DigicoolThings/MECB/MECB_WDC_W65C02S_PLCC_CPU/CreatiVision/CreatiVision_MECB_ROM_Expansion.pdf

## CreatiVision re-Creation - 16 Cartridge Selection

### for MECB ROM Expansion (ROM0 + ROM1)

v1.0 by DigicoolThings

Switch Settings: 1=On, 0=Off (Positions 1234 = A19, A18, A17, A16)

ROM | Program | Switch Setting 1234 | Switch Setting Rotary
ROM0 | Air/Sea Battle | 1111 | 0
| Astro Pinball | 1110 | 1
| Auto Chase | 1101 | 2
| BASIC 1983 | 1100 | 3
| Chopper Rescue | 1011 | 4
| Crazy Chicky | 1010 | 5
| Deep Sea Adventure | 1001 | 6
| Locomotive | 1000 | 7
ROM1 | Mouse Puzzle | 0111 | 8
| Planet Defender | 0110 | 9
| Police Jump | 0101 | A
| Soccer | 0100 | B
| Sonic Invader | 0011 | C
| Stone Age | 0010 | D
| Tank Attack | 0001 | E
| Tennis Wimbledon | 0000 | F
