DigicoolThings/MECB/MECB_6802_CPU/MECB_6802_CPU_PCB_3D.png

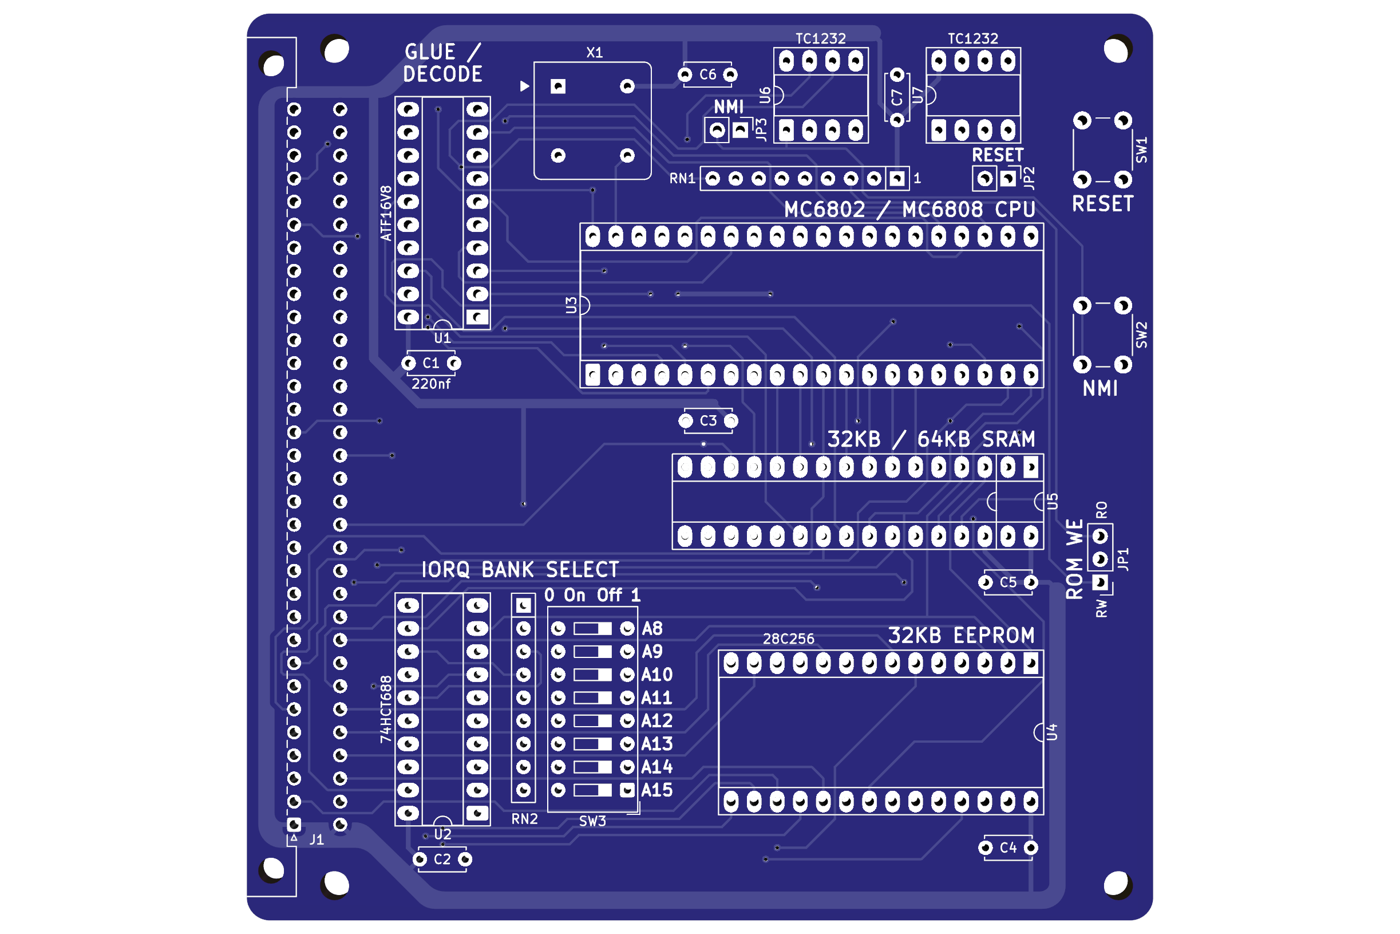
MECB_6802_CPU/MECB_6802_CPU_PCB_3D.png
