DigicoolThings/MECB/MECB_6809_CPU/MECB_6809_CPU_IORQ_48K_v2.5.jpg

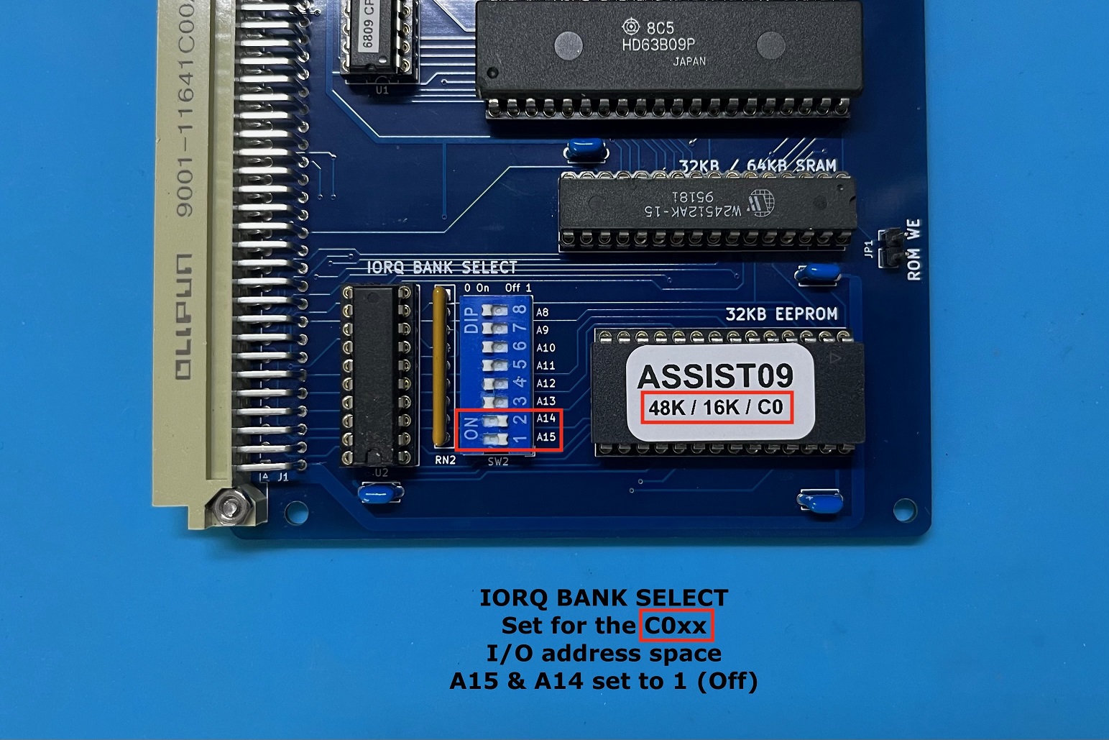
MECB_6809_CPU/MECB_6809_CPU_IORQ_48K_v2.5.jpg
