DigicoolThings/MECB/MECB_68008_CPU/MECB_68008_CPU_PCB_3D.png

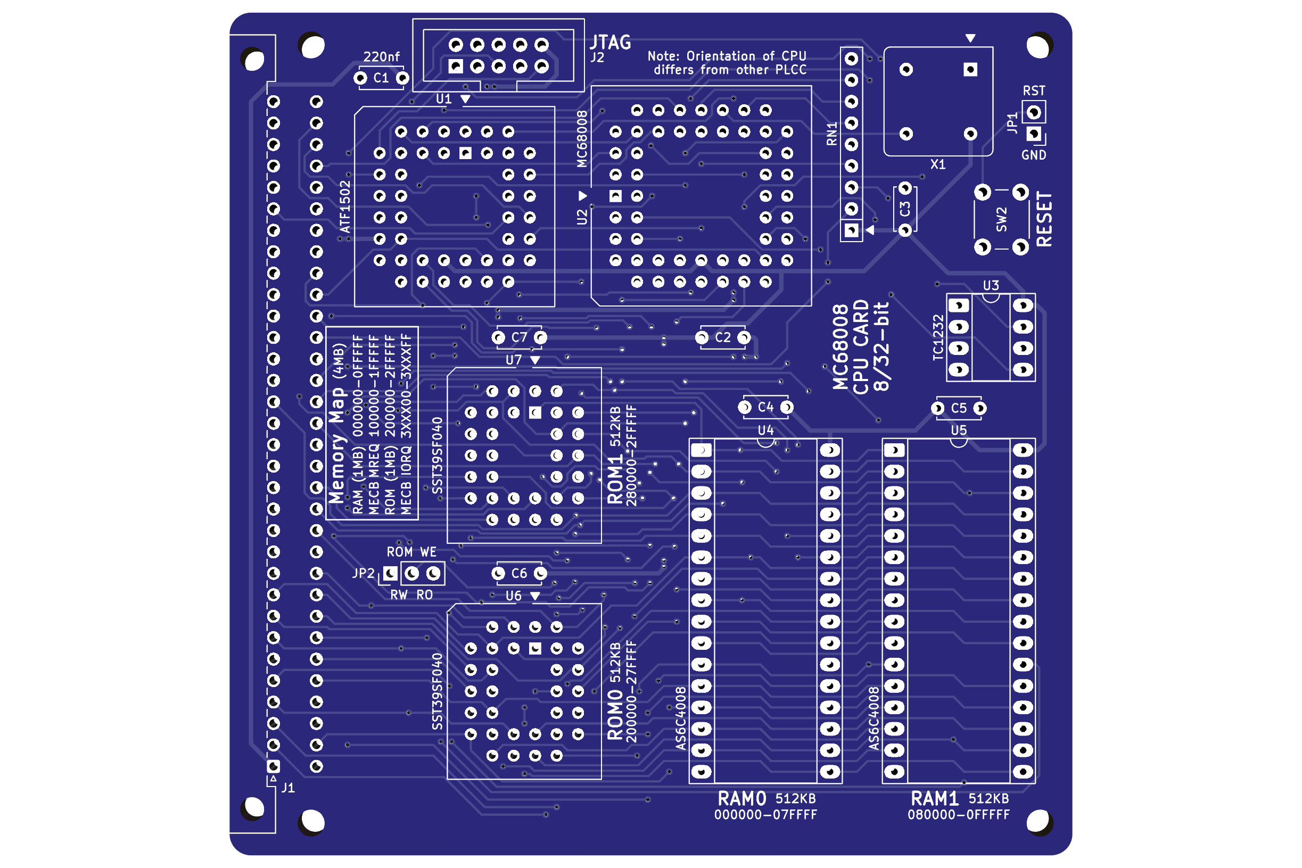
MECB_68008_CPU/MECB_68008_CPU_PCB_3D.png
