DigicoolThings/MECB/MECB_BackPlane_Extension/MECB_Backplane_Extension_PCB.png

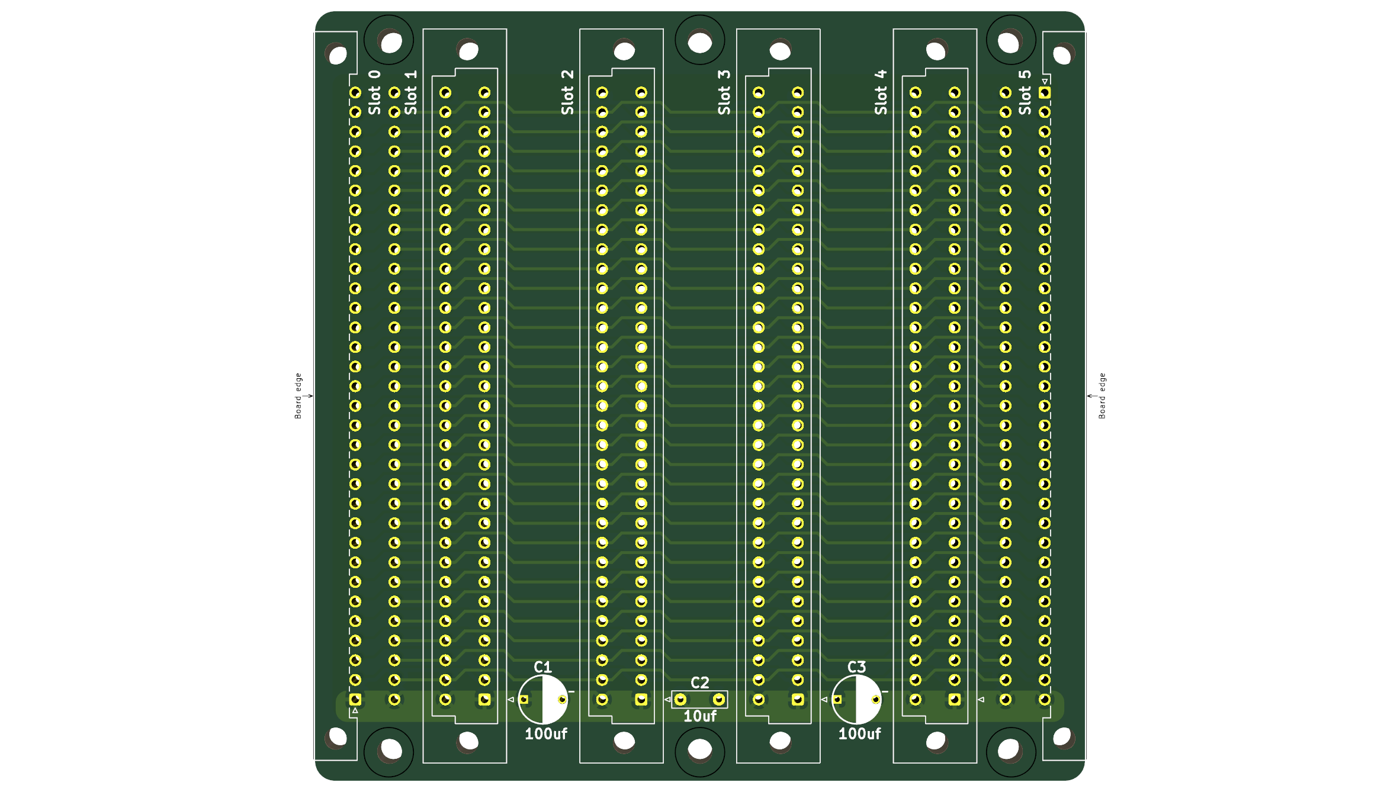
MECB_BackPlane_Extension/MECB_Backplane_Extension_PCB.png
