DigicoolThings/MECB/MECB_Grid/MECB_Grid_PCB_3D.png

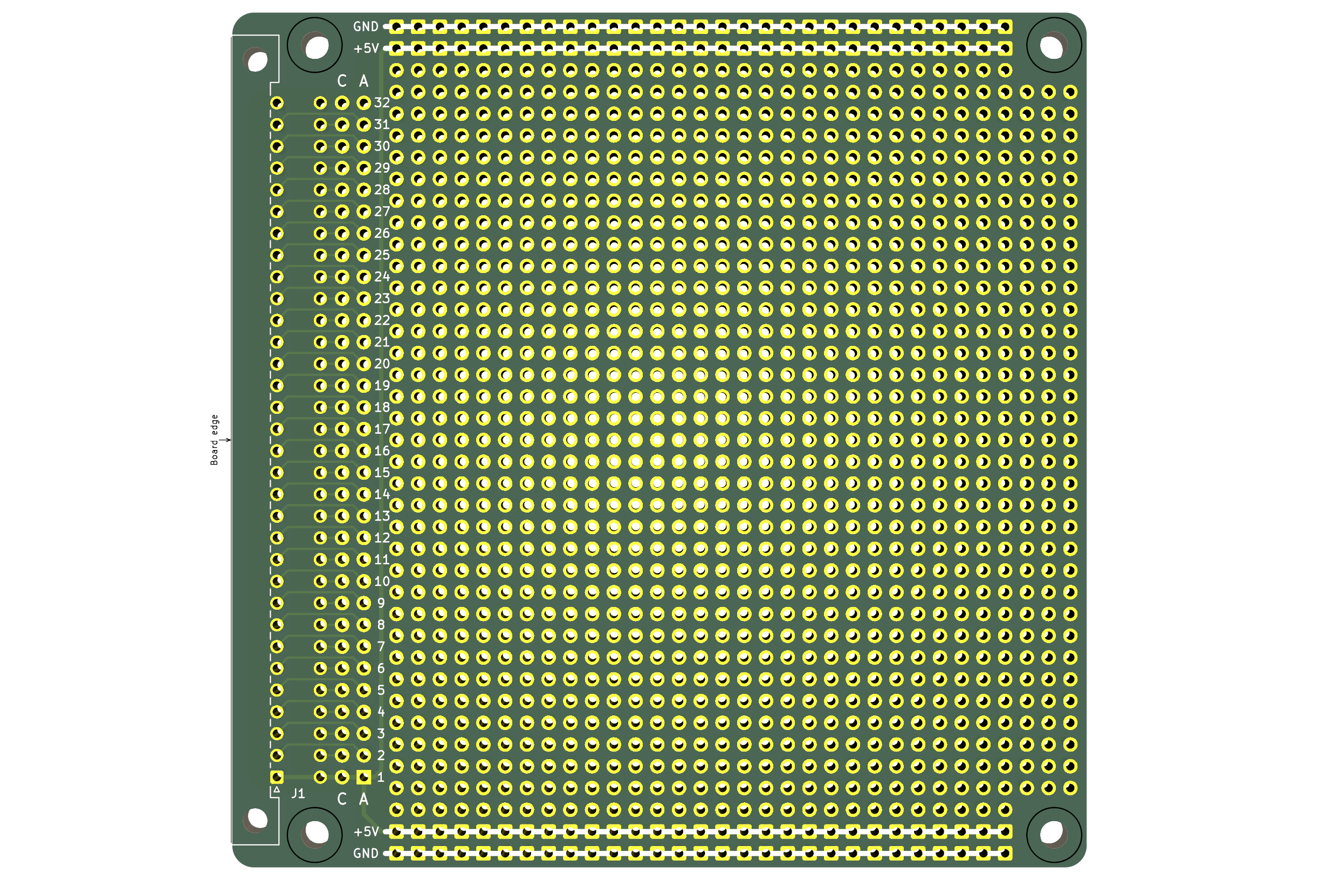
MECB_Grid/MECB_Grid_PCB_3D.png
