DigicoolThings/MECB/MECB_Grid/MECB_Pinout_Handout.png

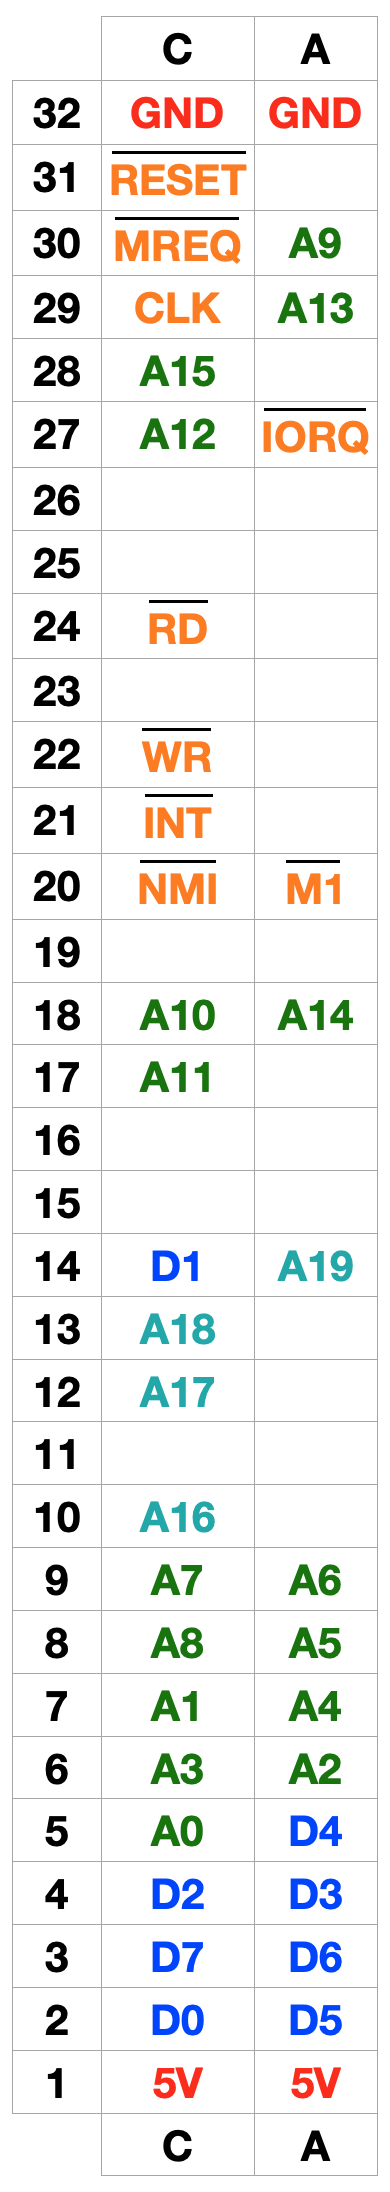
MECB_Grid/MECB_Pinout_Handout.png
