DigicoolThings/MECB/MECB_Motorola_IO/MECB_Motorola_IO_PCB_3D.png

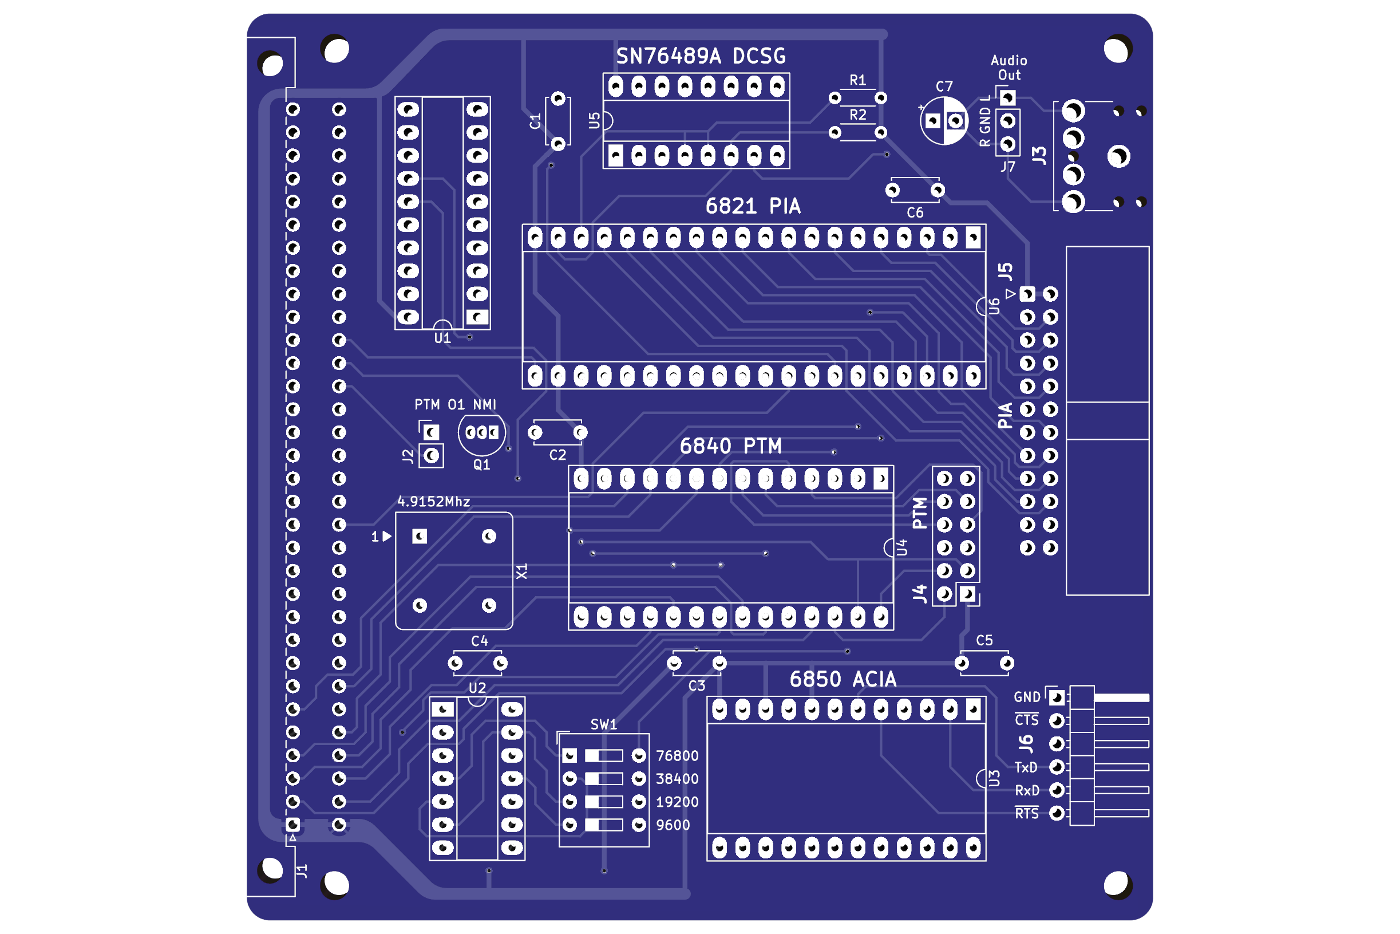
MECB_Motorola_IO/MECB_Motorola_IO_PCB_3D.png
