DigicoolThings/MECB/MECB_OLED_Display_128x64/MECB_OLED_Display_128x64_PCB_3D.png

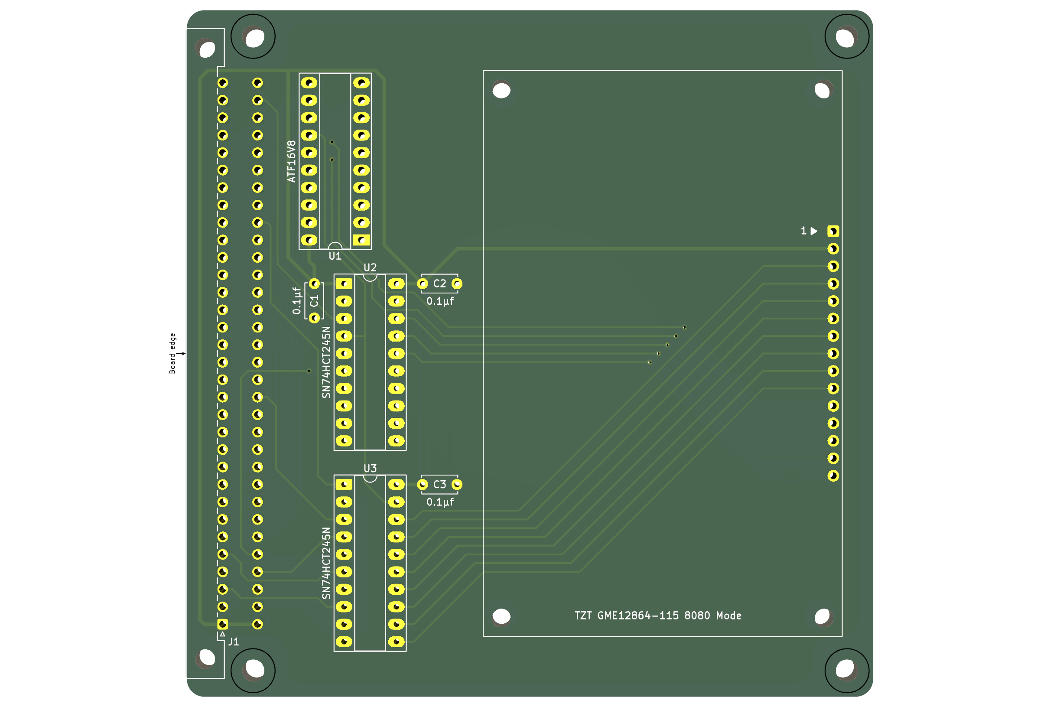
MECB_OLED_Display_128x64/MECB_OLED_Display_128x64_PCB_3D.png
