DigicoolThings/MECB/MECB_PICO9918_VDP/MECB_PICO9918_VDP_PCB_3D.png

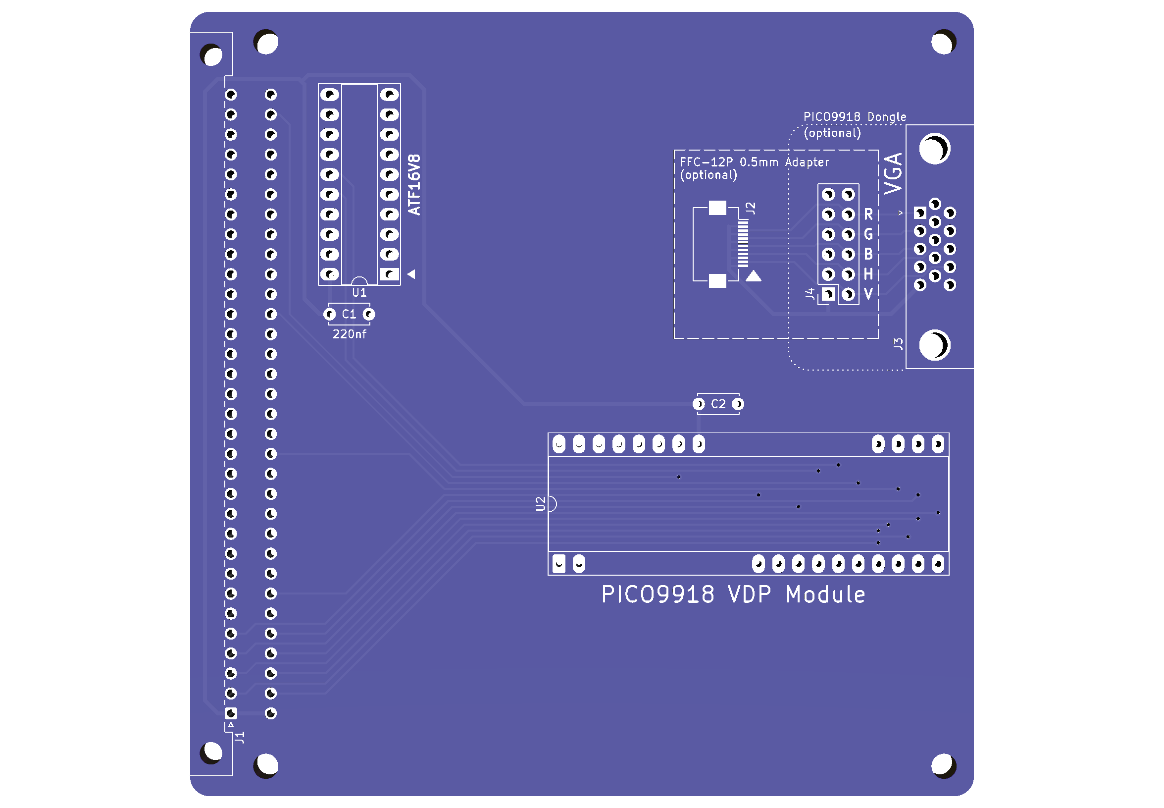
MECB_PICO9918_VDP/MECB_PICO9918_VDP_PCB_3D.png
