DigicoolThings/MECB/MECB_Template_16V8/meta/brd.png

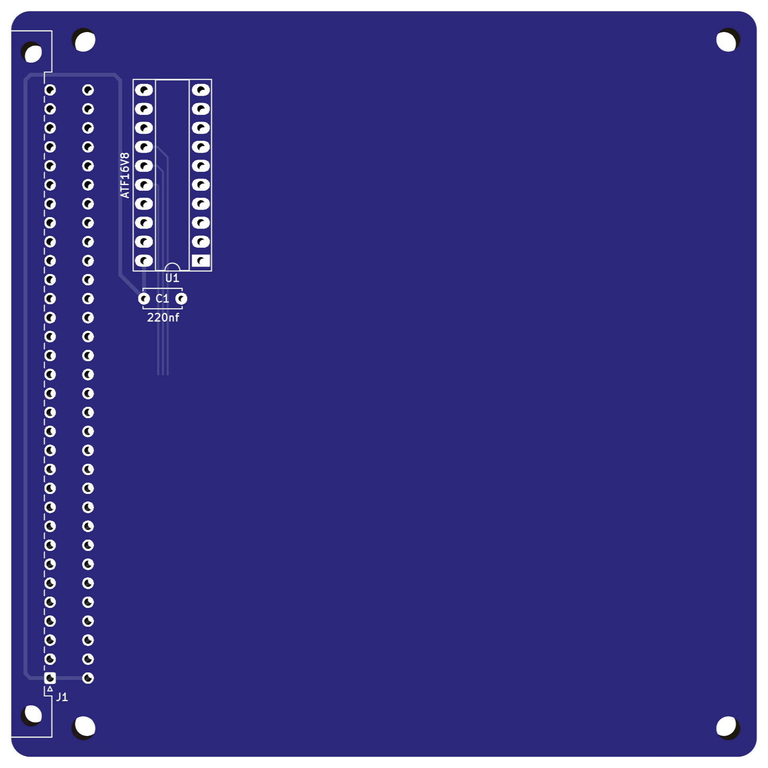
MECB_Template_16V8/meta/brd.png
