DigicoolThings/MECB/MECB_V9938_or_V9958_VDP/MECB_V9938_or_V9958_VDP_PCB_v1.2.png

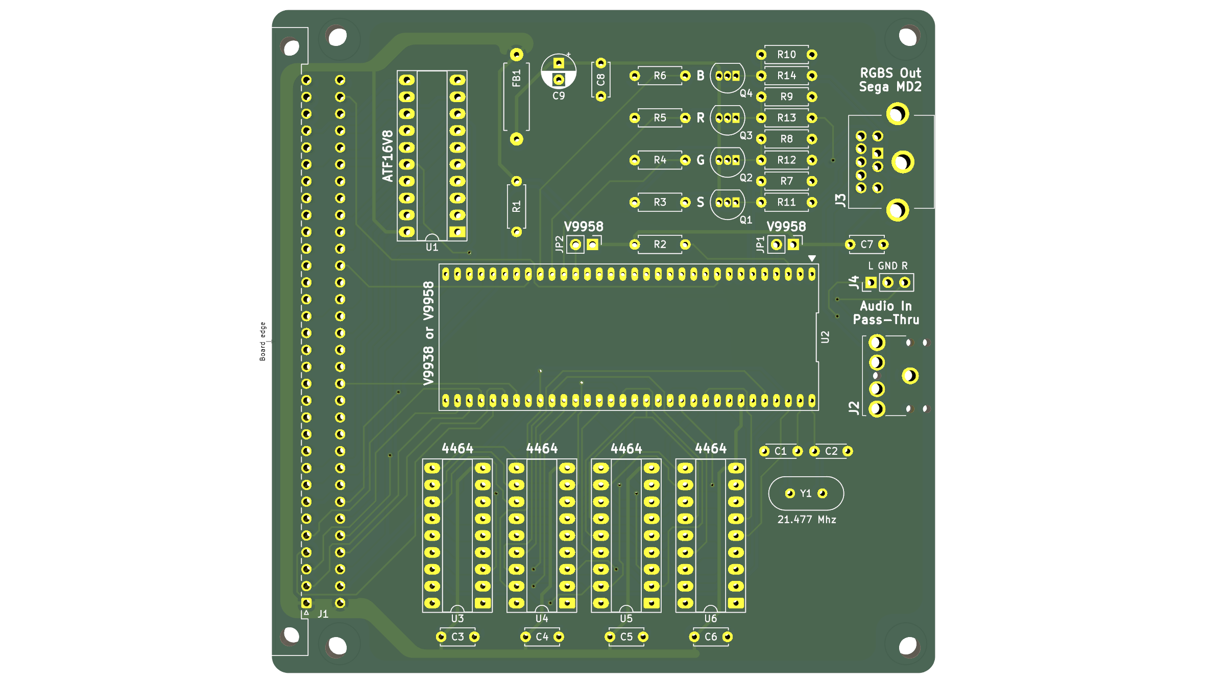
MECB_V9938_or_V9958_VDP/MECB_V9938_or_V9958_VDP_PCB_v1.2.png
