DigicoolThings/MECB/MECB_BackPlane_Extension/MECB_Backplane_Extension_BOM.pdf

Item | Qty | Source | Part Number
MECB Backplane Extension PCB | 1 | JLCPCB
DIN41612 Female 364 Connector | 4 | AliExpress | 364-STR-F
DIN41612 Female R/A 364 Connector | 1 | AliExpress | 364-RA-F
DIN41612 Male R/A 364 Connector | 1 | AliExpress | 364-RA-M
M2.5 Bolt 8mm | 8 | AliExpress
M2.5 Bolt 10mm | 4 | AliExpress
M2.5 Nut | 12 | AliExpress
12mm Nylon PCB Spacer | 6 | AliExpress
6mm Nylon Bolt | 12 | AliExpress
100uf Electrolytic | 2 | Mouser | 667-ECE-A1CKA101B
10uf Capacitor | 1 | Mouser | 810-FG24X7R1A106KRT6

MECB Backplane Extension - BOM

1
