DigicoolThings/MECB/MECB_6502_CPU/MECB_6502_CPU_BOM.pdf

Item | Qty | Source | Part Number
MECB 6502 CPU Card PCB | 1 | JLCPCB
DIN41612 Male R/A 364 Connector | 1 | AliExpress | 364-RA-M
M2.5 Bolt 10mm Thread Length | 2 | AliExpress
M2.5 Nut | 2 | AliExpress
12mm Nylon PCB Spacer | 4 | AliExpress
6mm Nylon Bolt | 8 | AliExpress
ATF16V8 PLD DIP20 (U1) | 1 | Mouser | ATF16V8B
28C256 32KB EEPROM DIP28 (U4) | 1 | Mouser | AT28C256
MOS 6502 or WDC W65C02S CPU DIP40 (U3) | 1 | AliExpress / Mouser
ECS-2100 Crystal Oscillator (e.g. 1 - 8Mhz) DIP8 (X1) | 1 | Mouser | ECS-2100AX-1.0MHZ
Resistor Network 4K7 SIP9 (RN1, RN2) | 2 | Mouser | 4609X-101-472LF
0.1µf Capacitor 5mm (C1,C2,C3,C4,C5,C6) | 6 | AliExpress
2 pin PCB Header | 4 | AliExpress
3 pin PCB Header | 1 | AliExpress
2 pin Jumper Cap | 2 | AliExpress
Tactile Switch 6mm | 2 | AliExpress
8-way DIP Switch DIP16 | 1 | AliExpress
74HCT688 DIP20 (U2) | 1 | Mouser | CD74HCT688E
W24512K 64KB SRAM SDIP32 (U5) | 1 | AliExpress
TC1232CPA DIP8 (U6,U7) | 2 | AliExpress | TC1232CPA
SDIP32 IC Socket (or 2x DIP16) (for U5) | 1 | AliExpress
DIP40 IC Socket (for U3) | 1 | AliExpress
DIP28 IC Socket (for U4) | 1 | AliExpress
DIP20 IC Socket (for U1,U2) | 2 | AliExpress
DIP8 IC Socket (for U6,U7,X1) | 3 | AliExpress

### MECB 6502 CPU - BOM

1
