DigicoolThings/MECB/MECB_Prototype/MECB_Prototype_BOM.pdf

Item | Qty | Source | Part Number
MECB Prototype Card PCB | 1 | JLCPCB
DIN41612 Male R/A 364 Connector | 1 | AliExpress | 364-RA-M
M2.5 Bolt 10mm Thread Length | 2 | AliExpress
M2.5 Nut | 2 | AliExpress
40 pin PCB Header | 2 | AliExpress
12mm Nylon PCB Spacer | 4 | AliExpress
6mm Nylon Bolt | 8 | AliExpress

MECB Prototype - BOM

1
