DigicoolThings/MECB/MECB_6802_CPU/MECB_6802_CPU_BOM.png

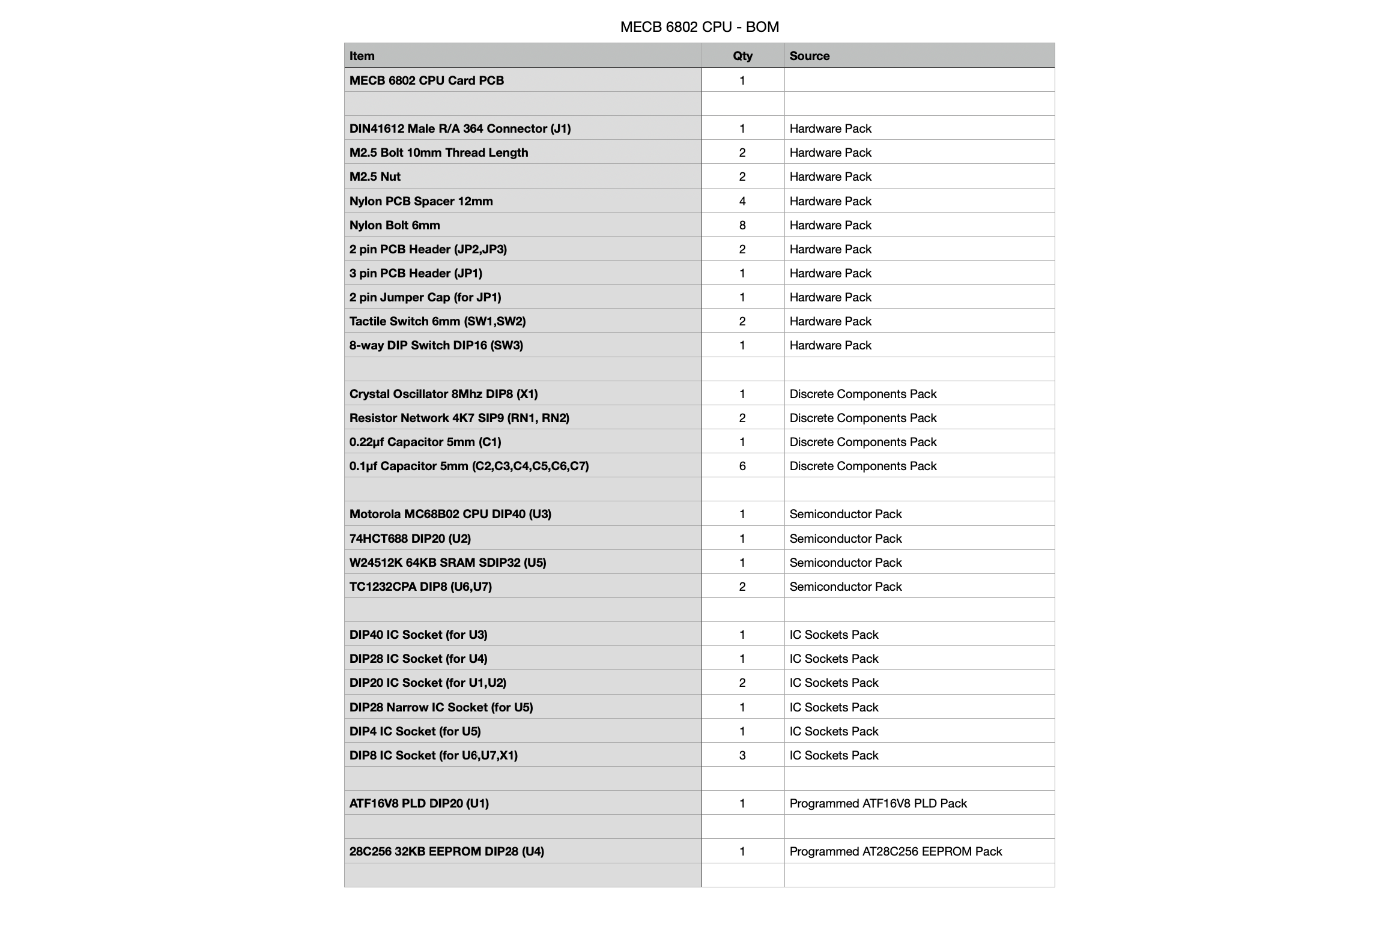
MECB_6802_CPU/MECB_6802_CPU_BOM.png
