DigicoolThings/MECB/MECB_68008_CPU/MECB_68008_CPU_BOM.png

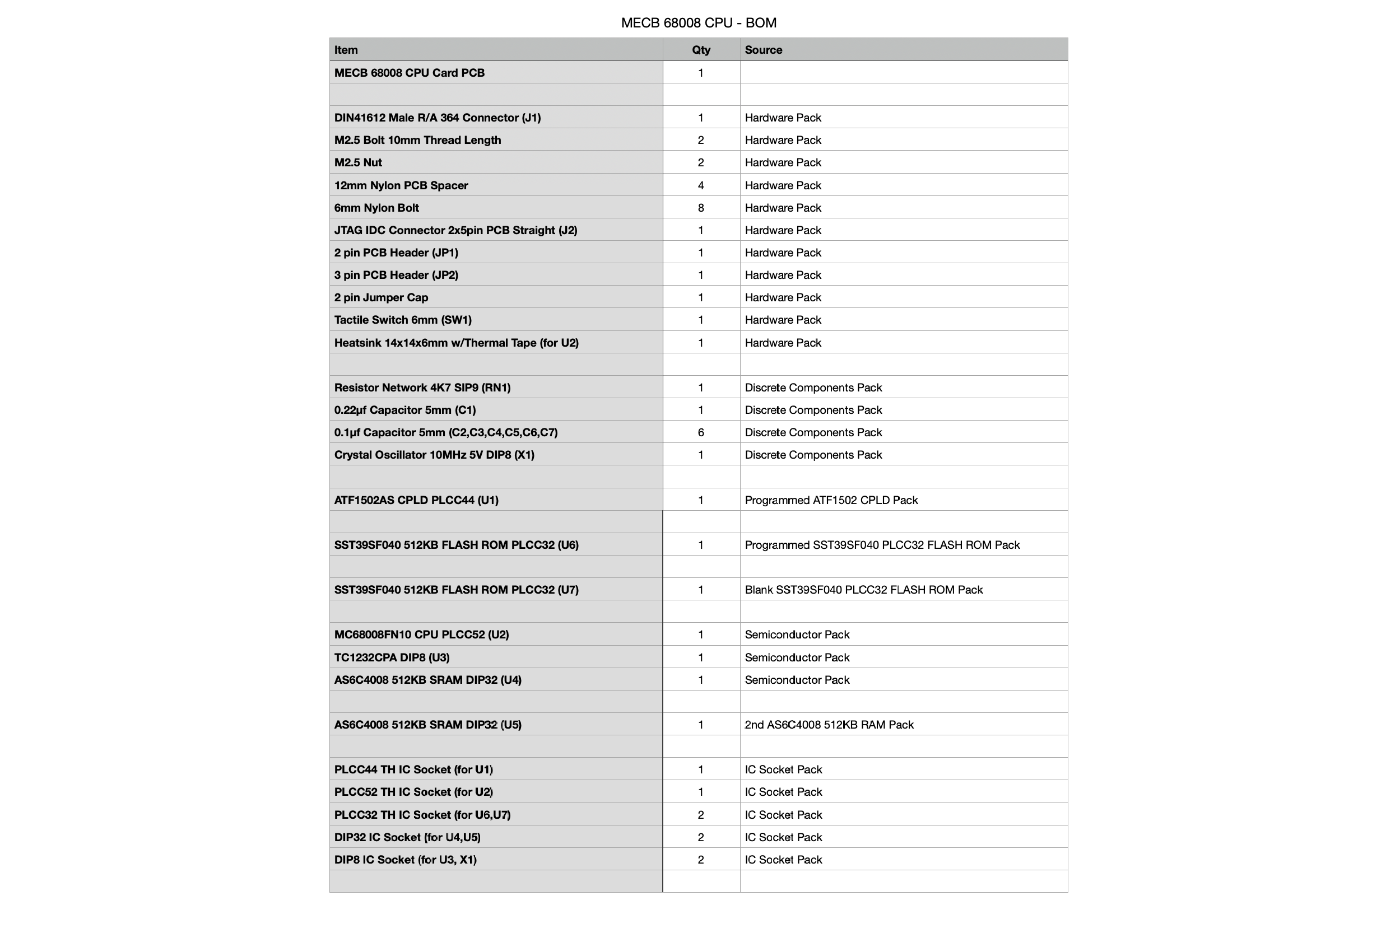
MECB_68008_CPU/MECB_68008_CPU_BOM.png
