DigicoolThings/MECB/MECB_Grid/MECB_Grid_BOM.png

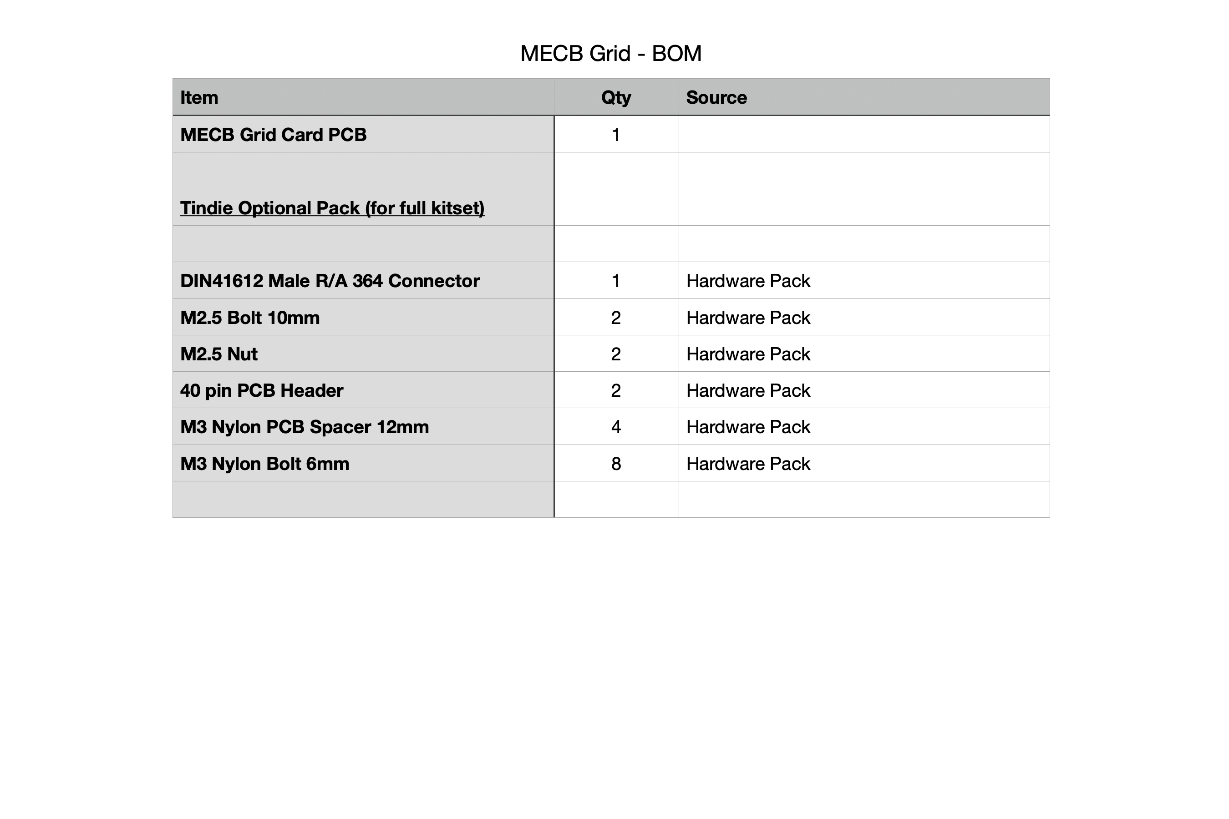
MECB_Grid/MECB_Grid_BOM.png
