DigicoolThings/MECB/MECB_Grid_16V8/MECB_Grid_16V8_BOM.png

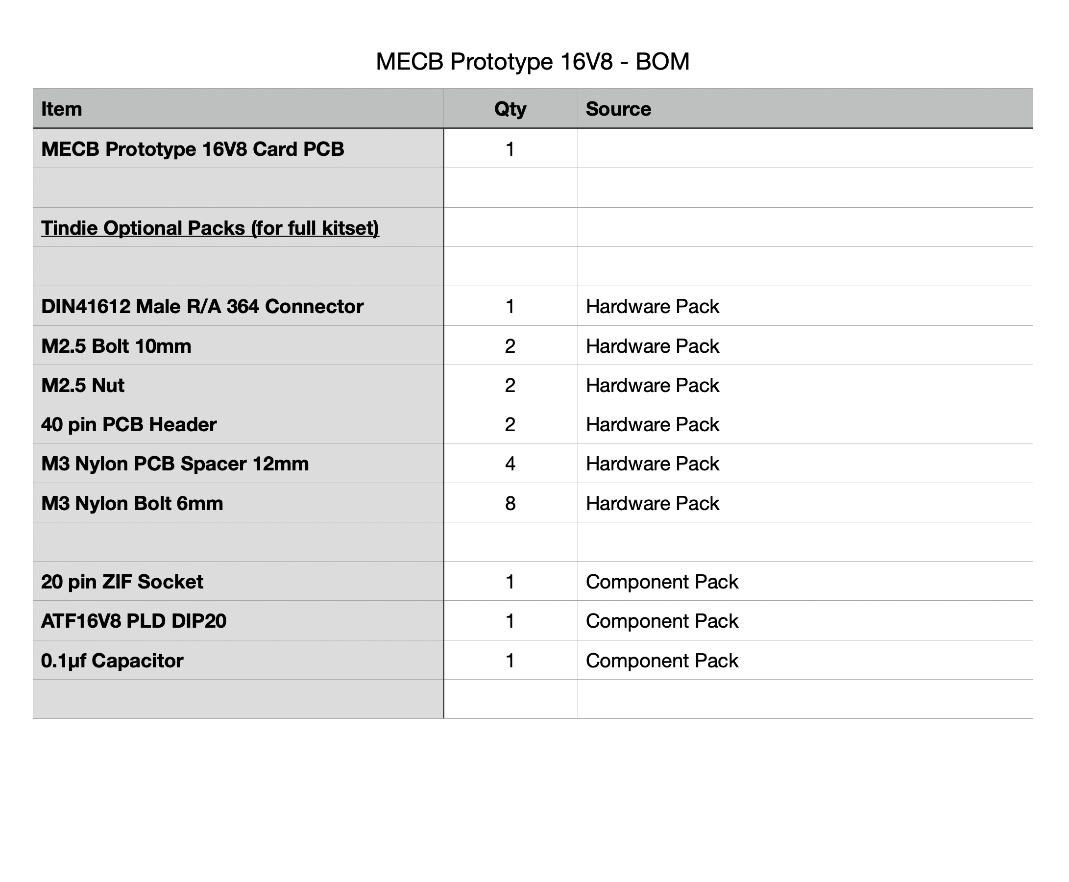
MECB_Grid_16V8/MECB_Grid_16V8_BOM.png
