DigicoolThings/MECB/MECB_Motorola_IO/MECB_Motorola_IO_BOM.png

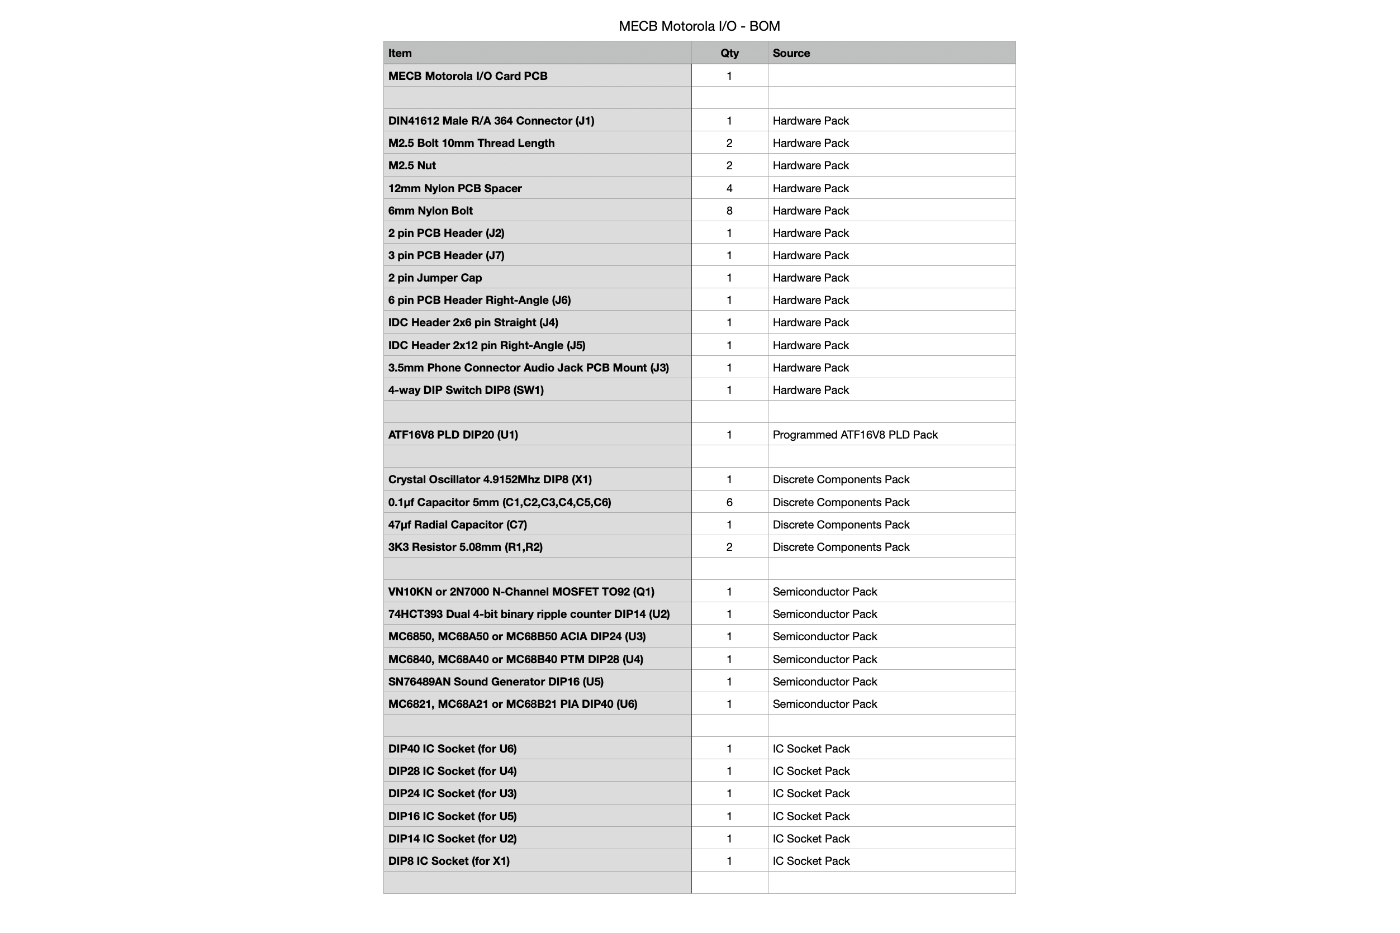
MECB_Motorola_IO/MECB_Motorola_IO_BOM.png
