DigicoolThings/MECB/MECB_OLED_Display_128x64/MECB_OLED_Display_128x64_BOM.png

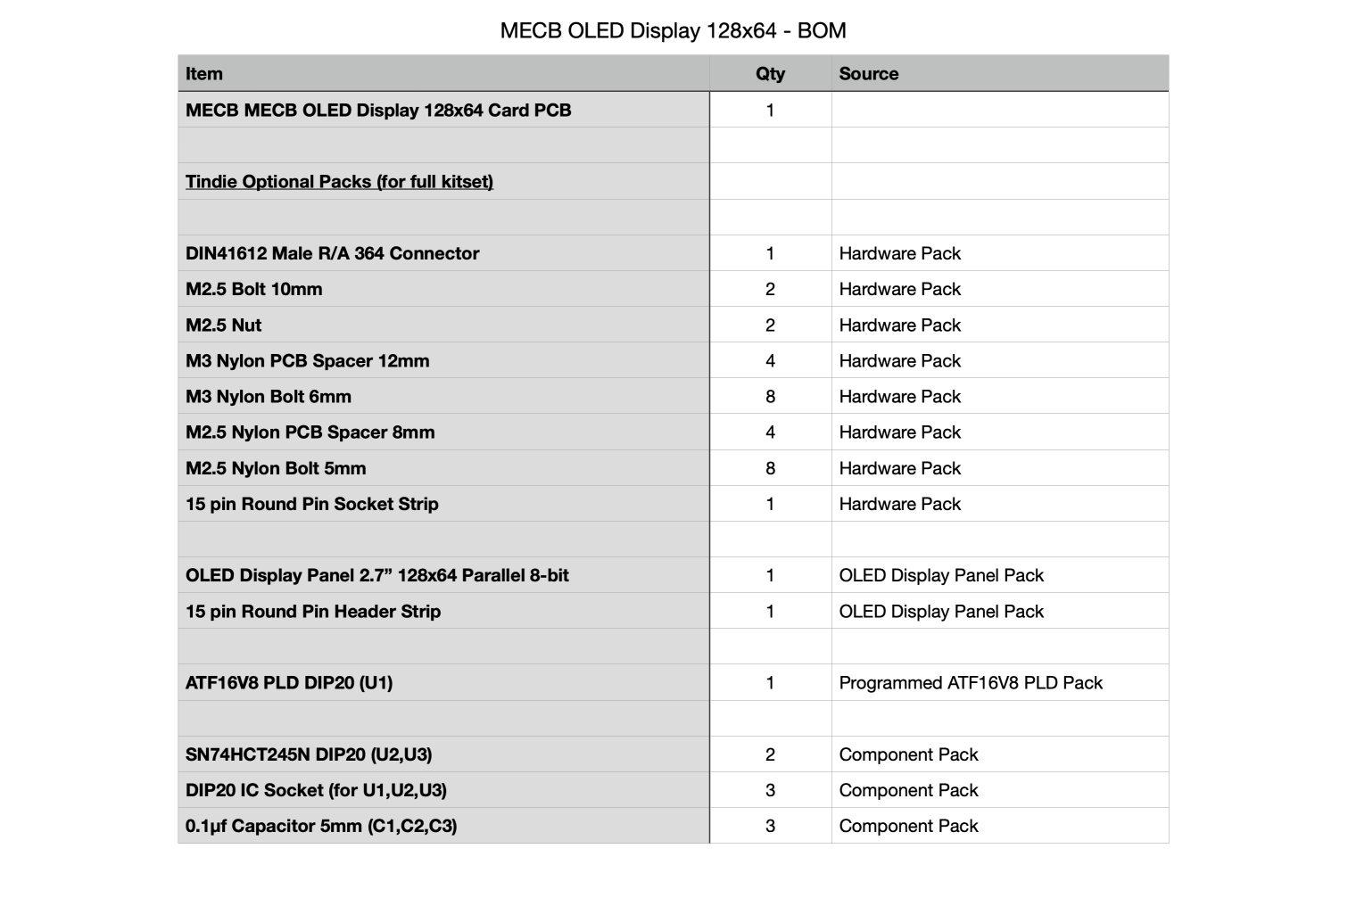
MECB_OLED_Display_128x64/MECB_OLED_Display_128x64_BOM.png
