DigicoolThings/MECB/MECB_Prototype_160mm/MECB_ProtoType_160mm_BOM.png

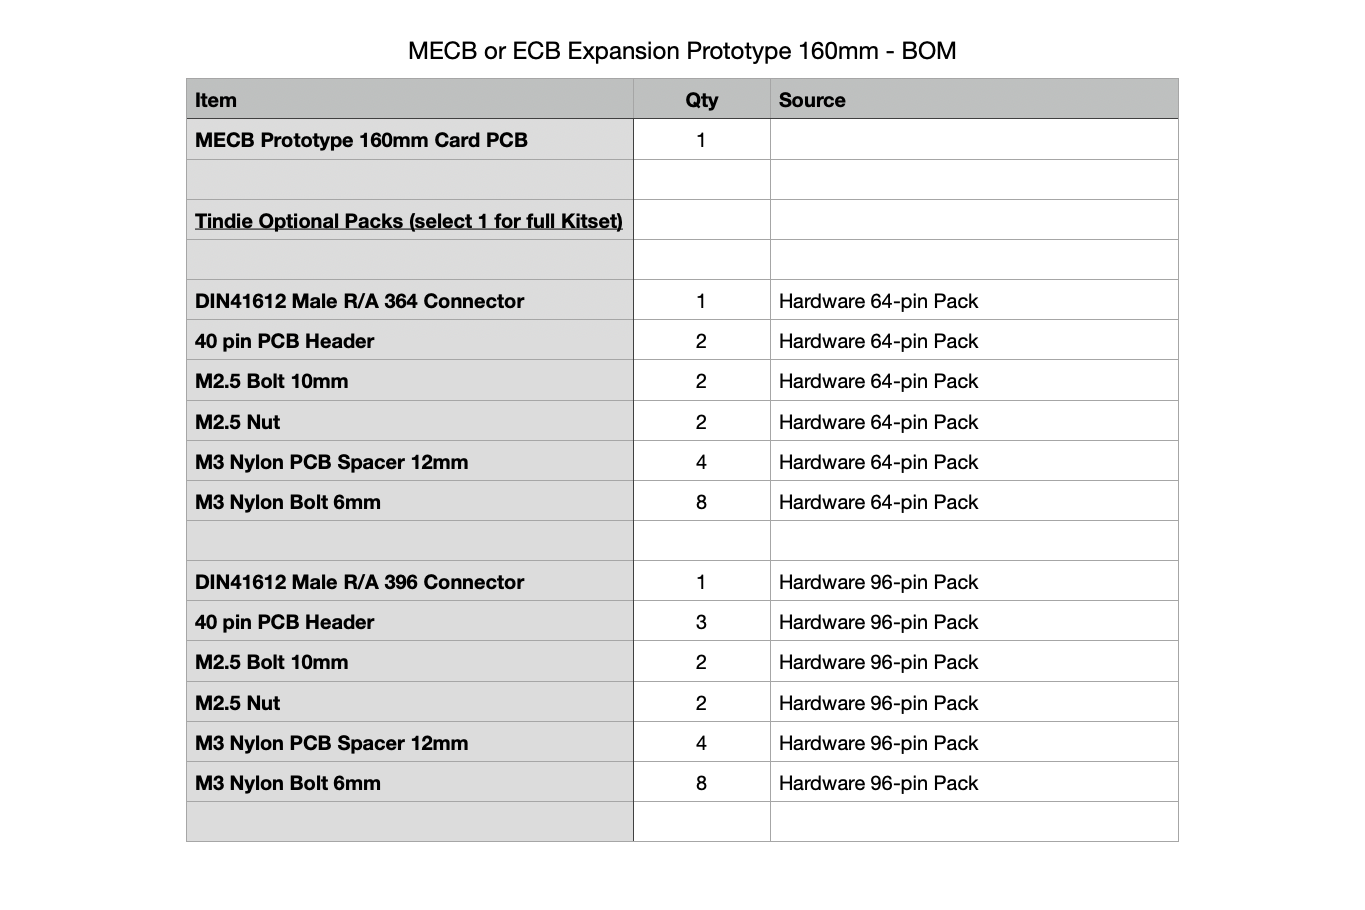
MECB_Prototype_160mm/MECB_ProtoType_160mm_BOM.png
