DigicoolThings/MECB/MECB_V9938_or_V9958_VDP/MECB_V9938_or_V9958_VDP_BOM_v1.x.png

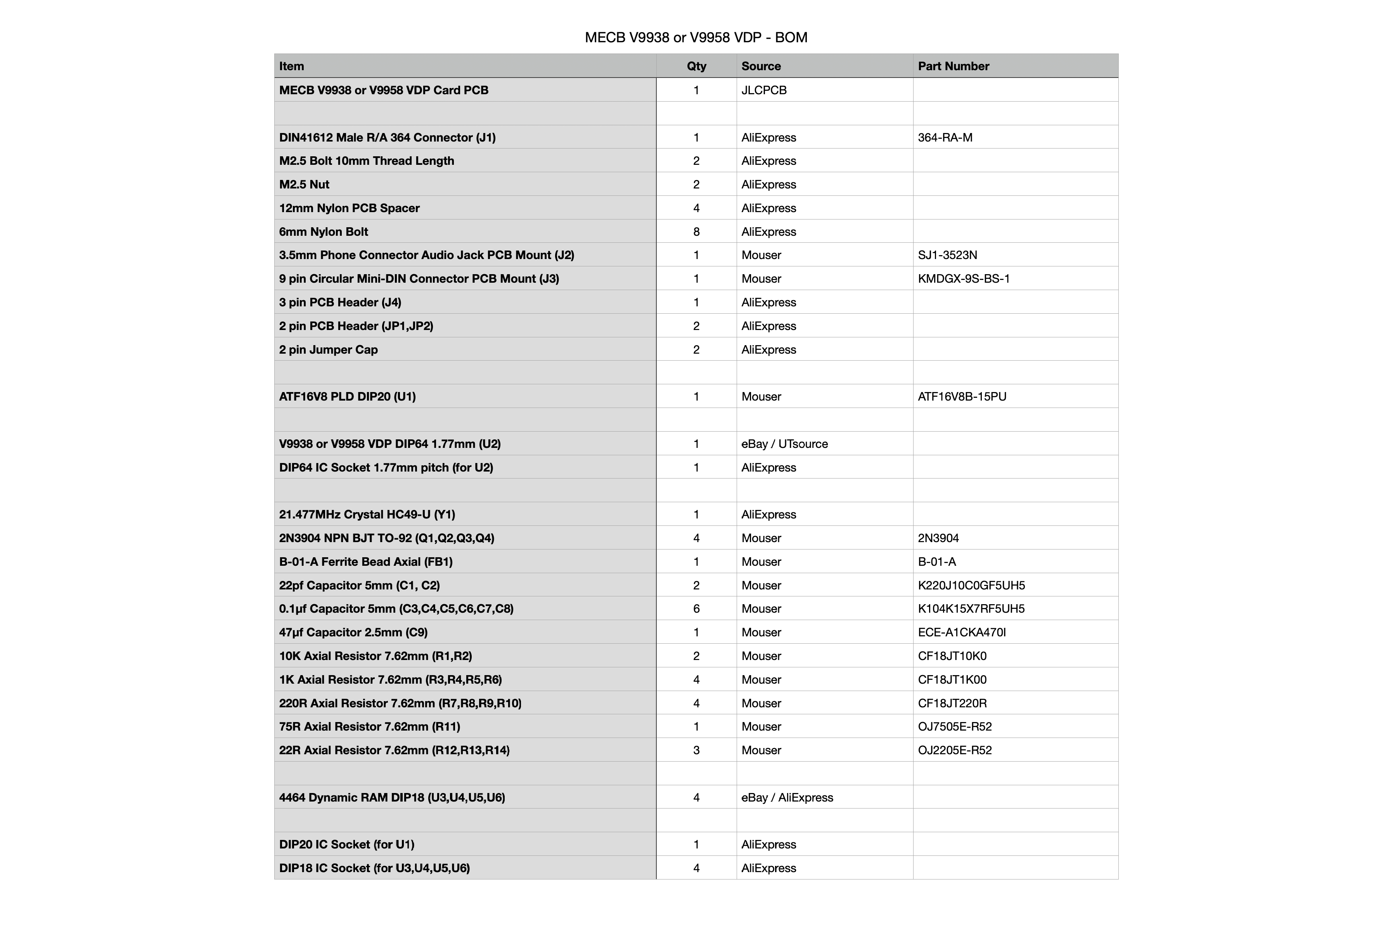
MECB_V9938_or_V9958_VDP/MECB_V9938_or_V9958_VDP_BOM_v1.x.png
