DigicoolThings/MECB/MECB_6309_CPU_PLCC/MECB_6309_CPU_PLCC_Assembled.jpeg

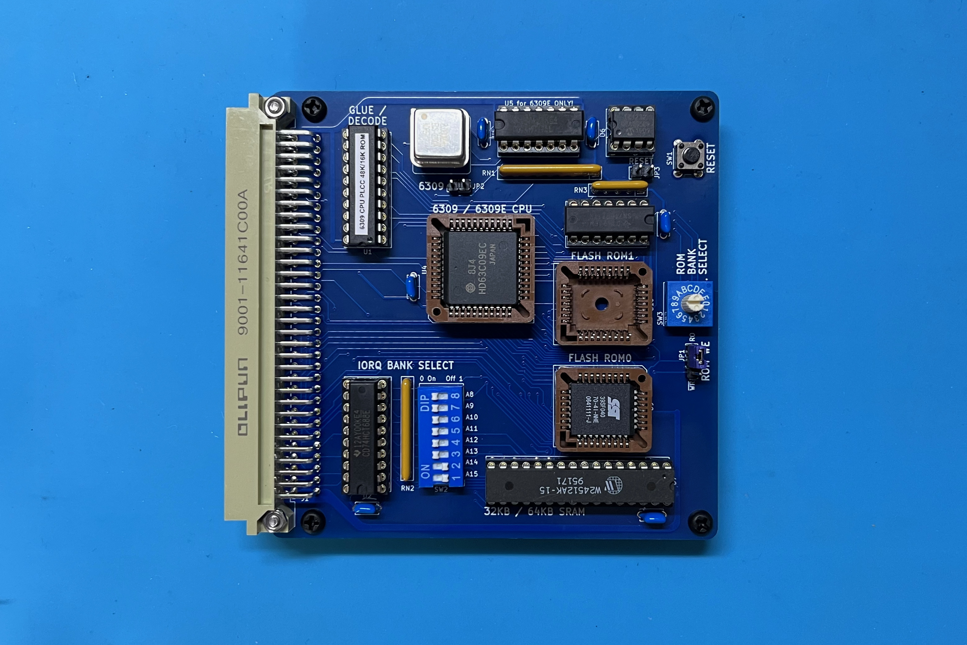
MECB_6309_CPU_PLCC/MECB_6309_CPU_PLCC_Assembled.jpeg
