DigicoolThings/MECB/MECB_6502_CPU/MECB_6502_CPU_Assembled_v1.3.jpeg

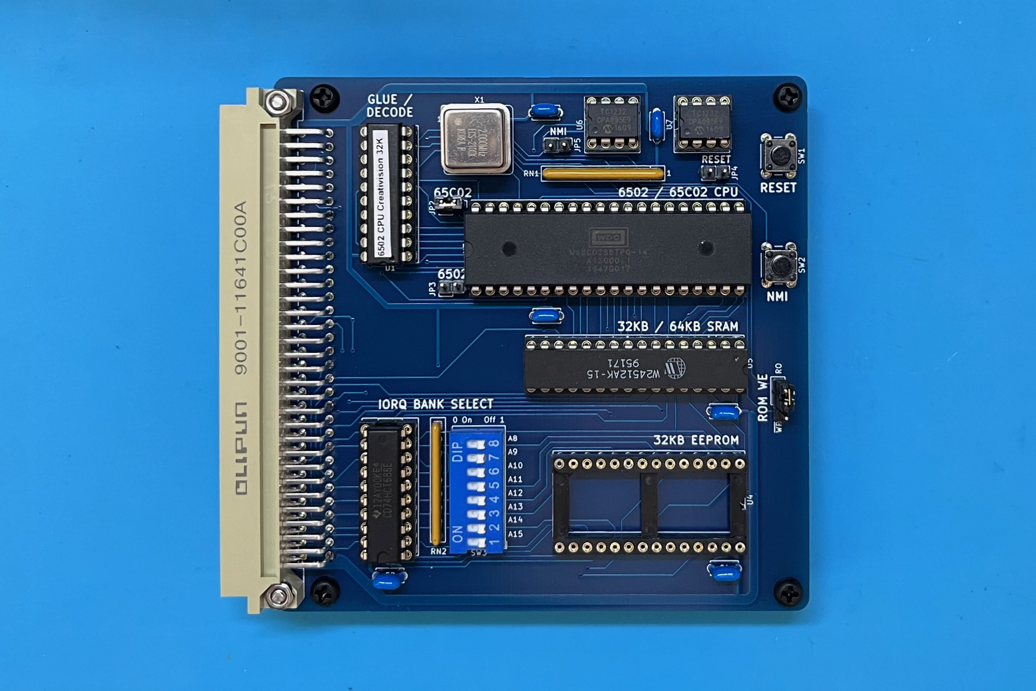
MECB_6502_CPU/MECB_6502_CPU_Assembled_v1.3.jpeg
