DigicoolThings/MECB/MECB_BackPlane/MECB_BackPlane_Assembled_v1.1.jpg

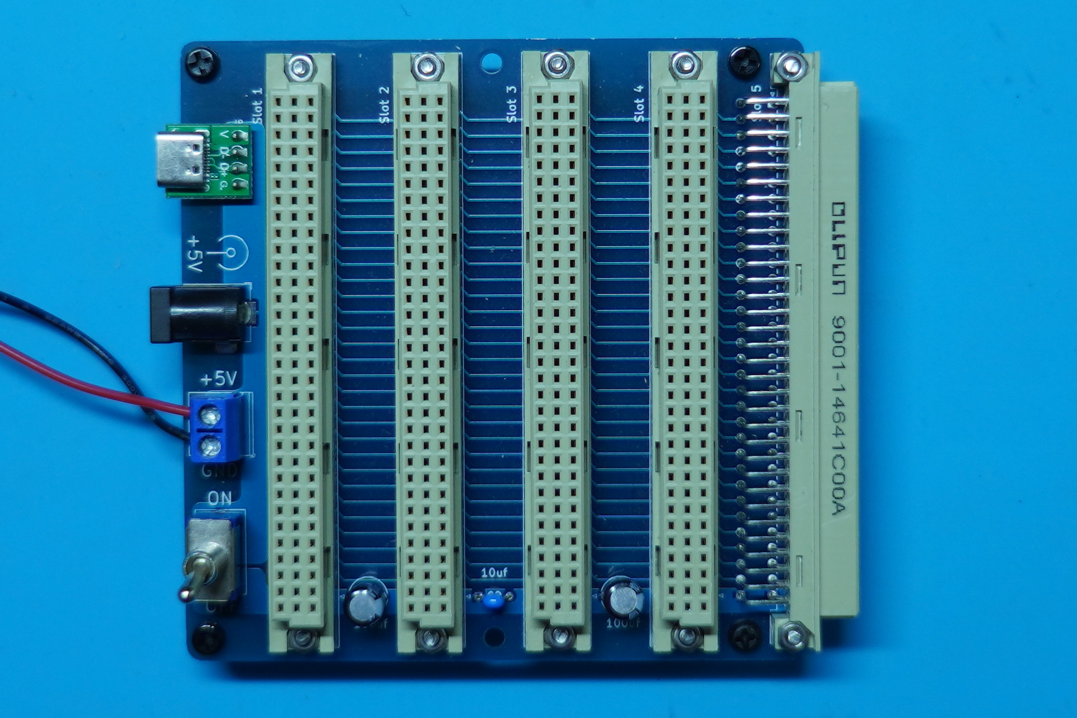
MECB_BackPlane/MECB_BackPlane_Assembled_v1.1.jpg
