DigicoolThings/MECB/MECB_BackPlane/MECB_Backplane_Assembled_v1.2.jpg

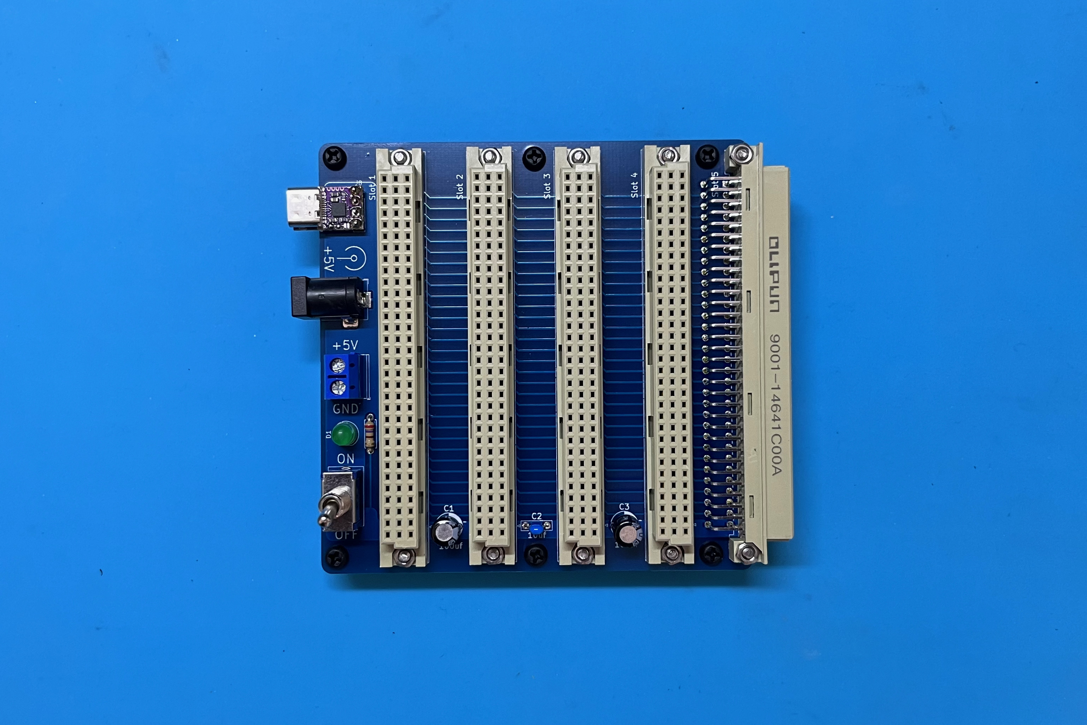
MECB_BackPlane/MECB_Backplane_Assembled_v1.2.jpg
