DigicoolThings/MECB/MECB_Motorola_IO/MECB_Motorola_IO_Assembled.jpeg

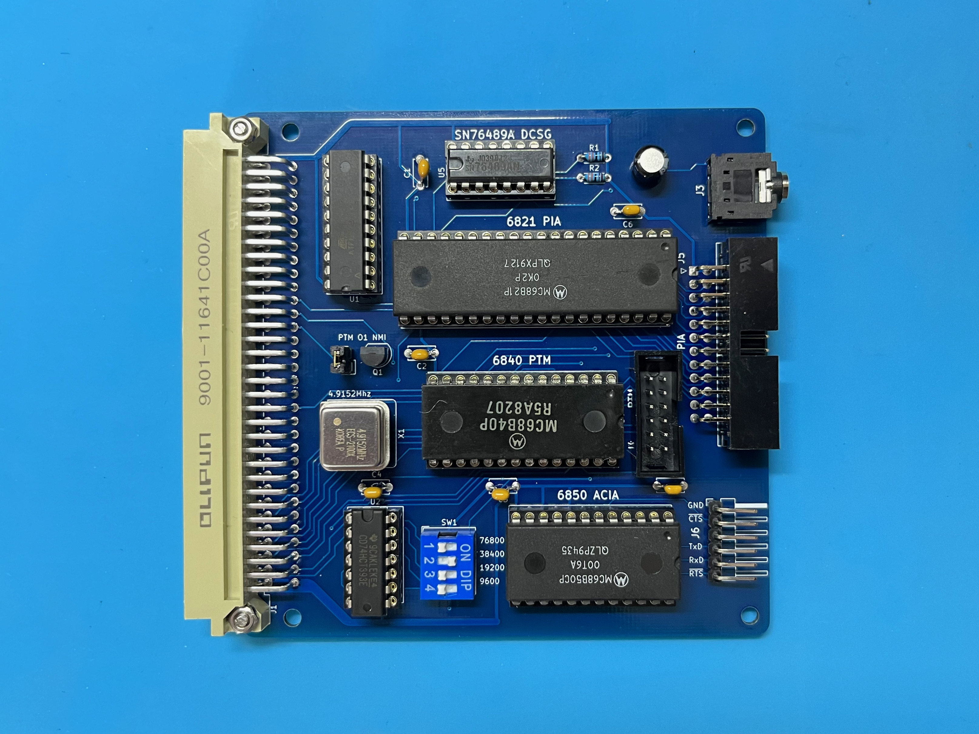
MECB_Motorola_IO/MECB_Motorola_IO_Assembled.jpeg
