DigicoolThings/MECB/MECB_PICO9918_VDP/MECB_PICO9918_VDP_Assembled.jpeg

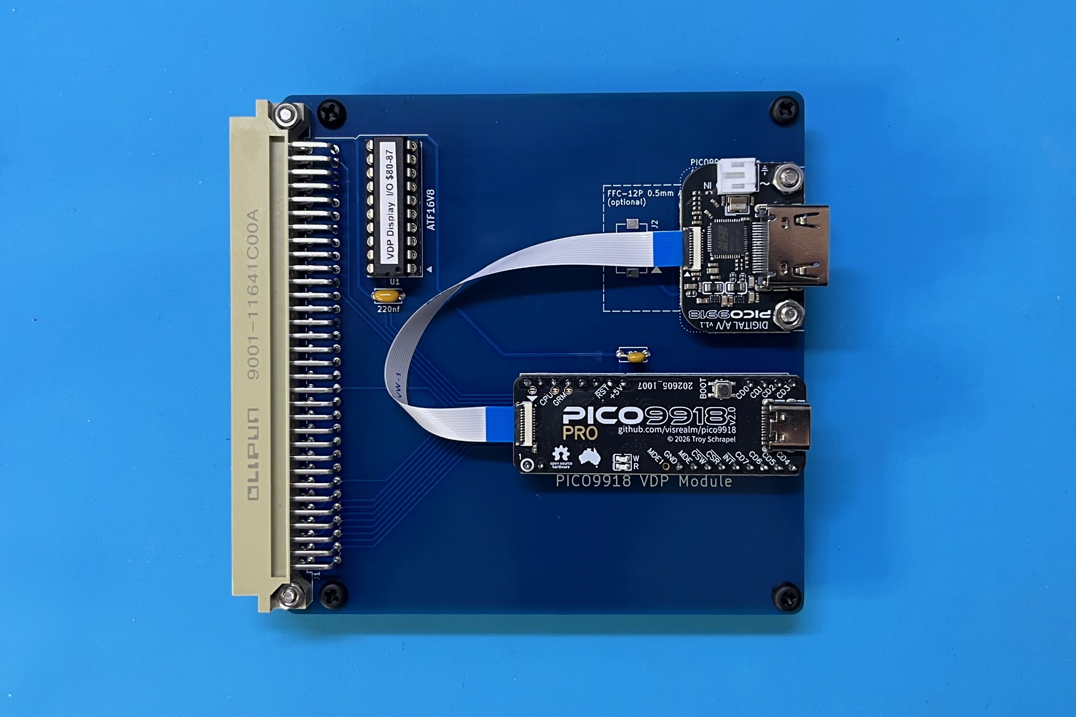
MECB_PICO9918_VDP/MECB_PICO9918_VDP_Assembled.jpeg
