DigicoolThings/MECB/MECB_Prototype/MECB_Prototype_Assembled.jpg

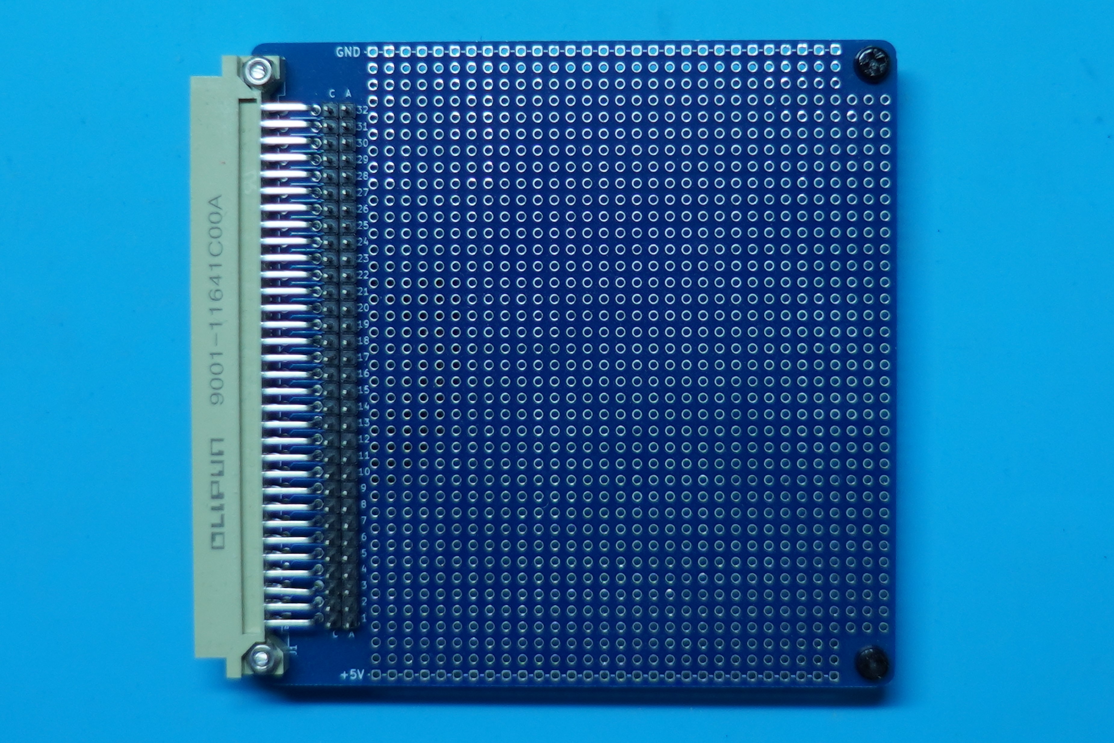
MECB_Prototype/MECB_Prototype_Assembled.jpg
