DigicoolThings/MECB/MECB_Prototype_16V8/MECB_Prototype_16V8_Assembled.jpeg

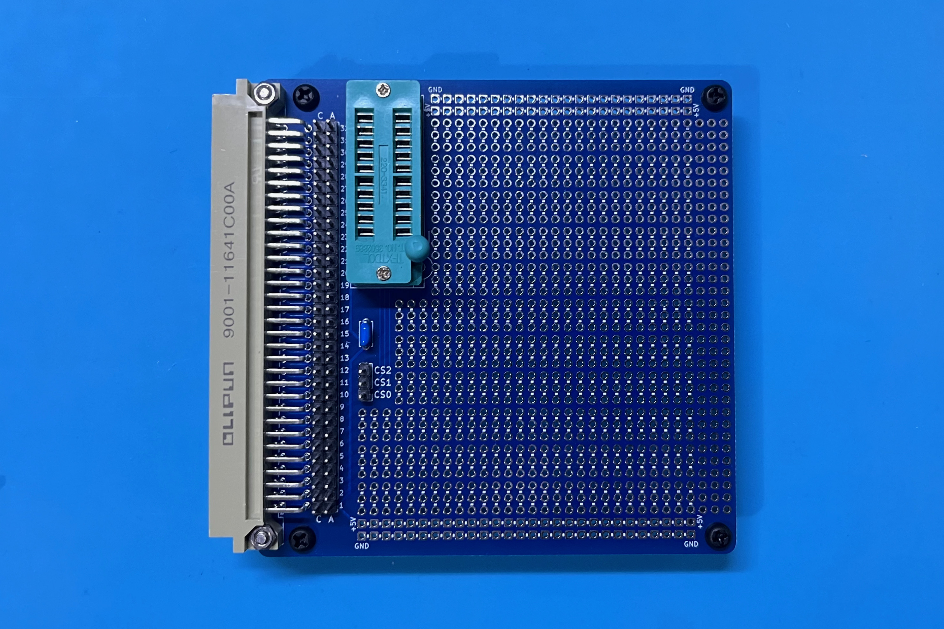
MECB_Prototype_16V8/MECB_Prototype_16V8_Assembled.jpeg
