DigicoolThings/MECB/MECB_Prototype_22V10/MECB_Prototype_22V10_Assembled.jpeg

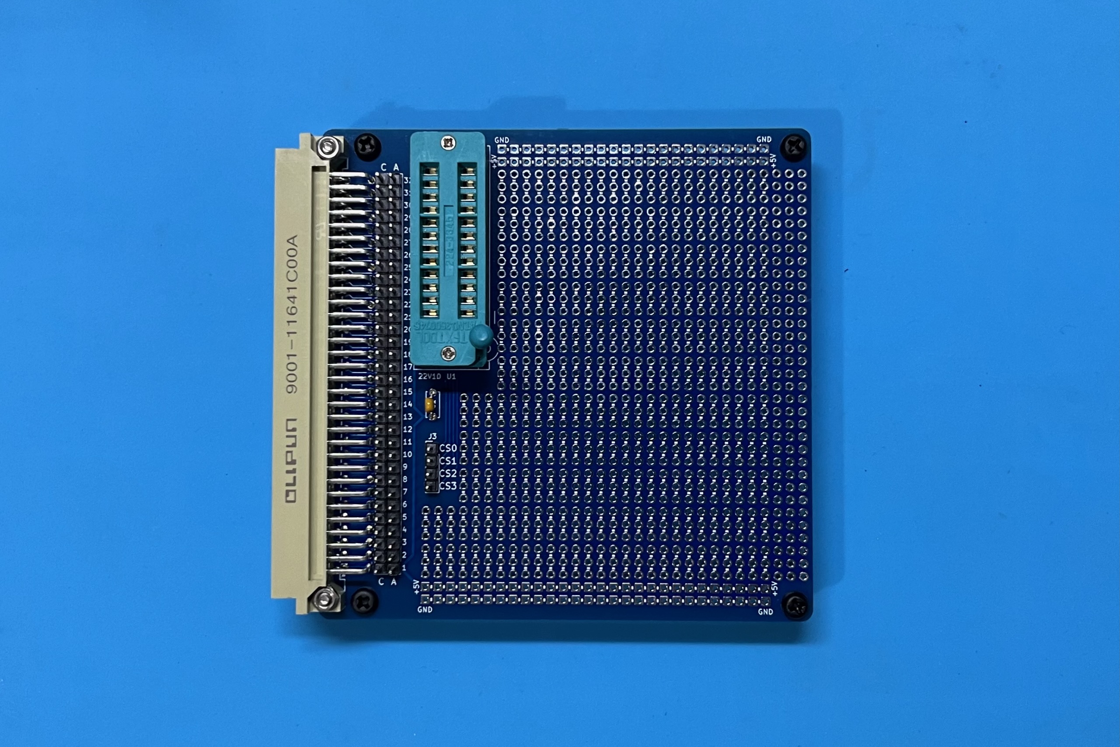
MECB_Prototype_22V10/MECB_Prototype_22V10_Assembled.jpeg
