DigicoolThings/MECB/MECB_TMS9918_or_TMS992x_VDP/MECB_TMS992xA_VDP_Assembled.jpg

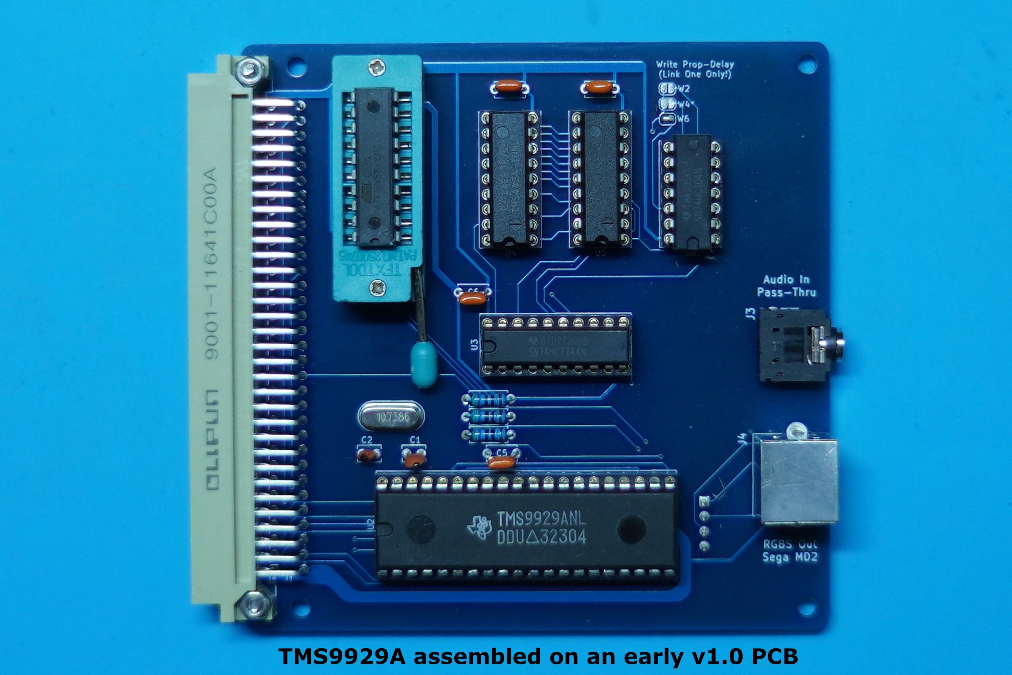
MECB_TMS9918_or_TMS992x_VDP/MECB_TMS992xA_VDP_Assembled.jpg
