DigicoolThings/MECB/MECB_WDC_W65C02S_PLCC_CPU/MECB_WDC_W65C02S_PLCC_CPU_Assembled.jpeg

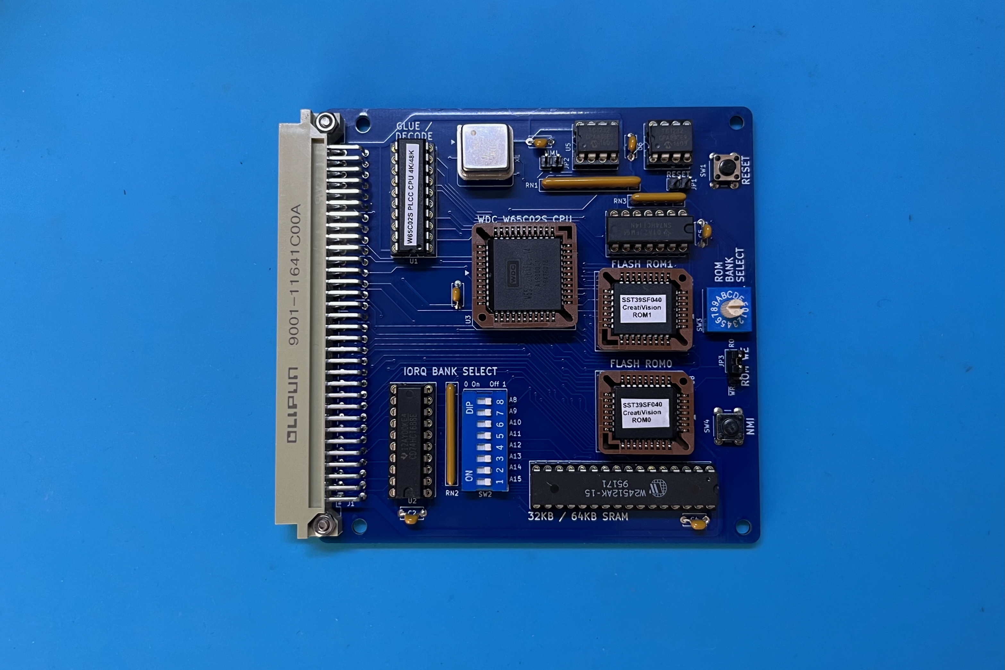
MECB_WDC_W65C02S_PLCC_CPU/MECB_WDC_W65C02S_PLCC_CPU_Assembled.jpeg
