DigicoolThings/MECB/MECB_Prototype_22V10/MECB_Prototype_22V10_Schematic.pdf

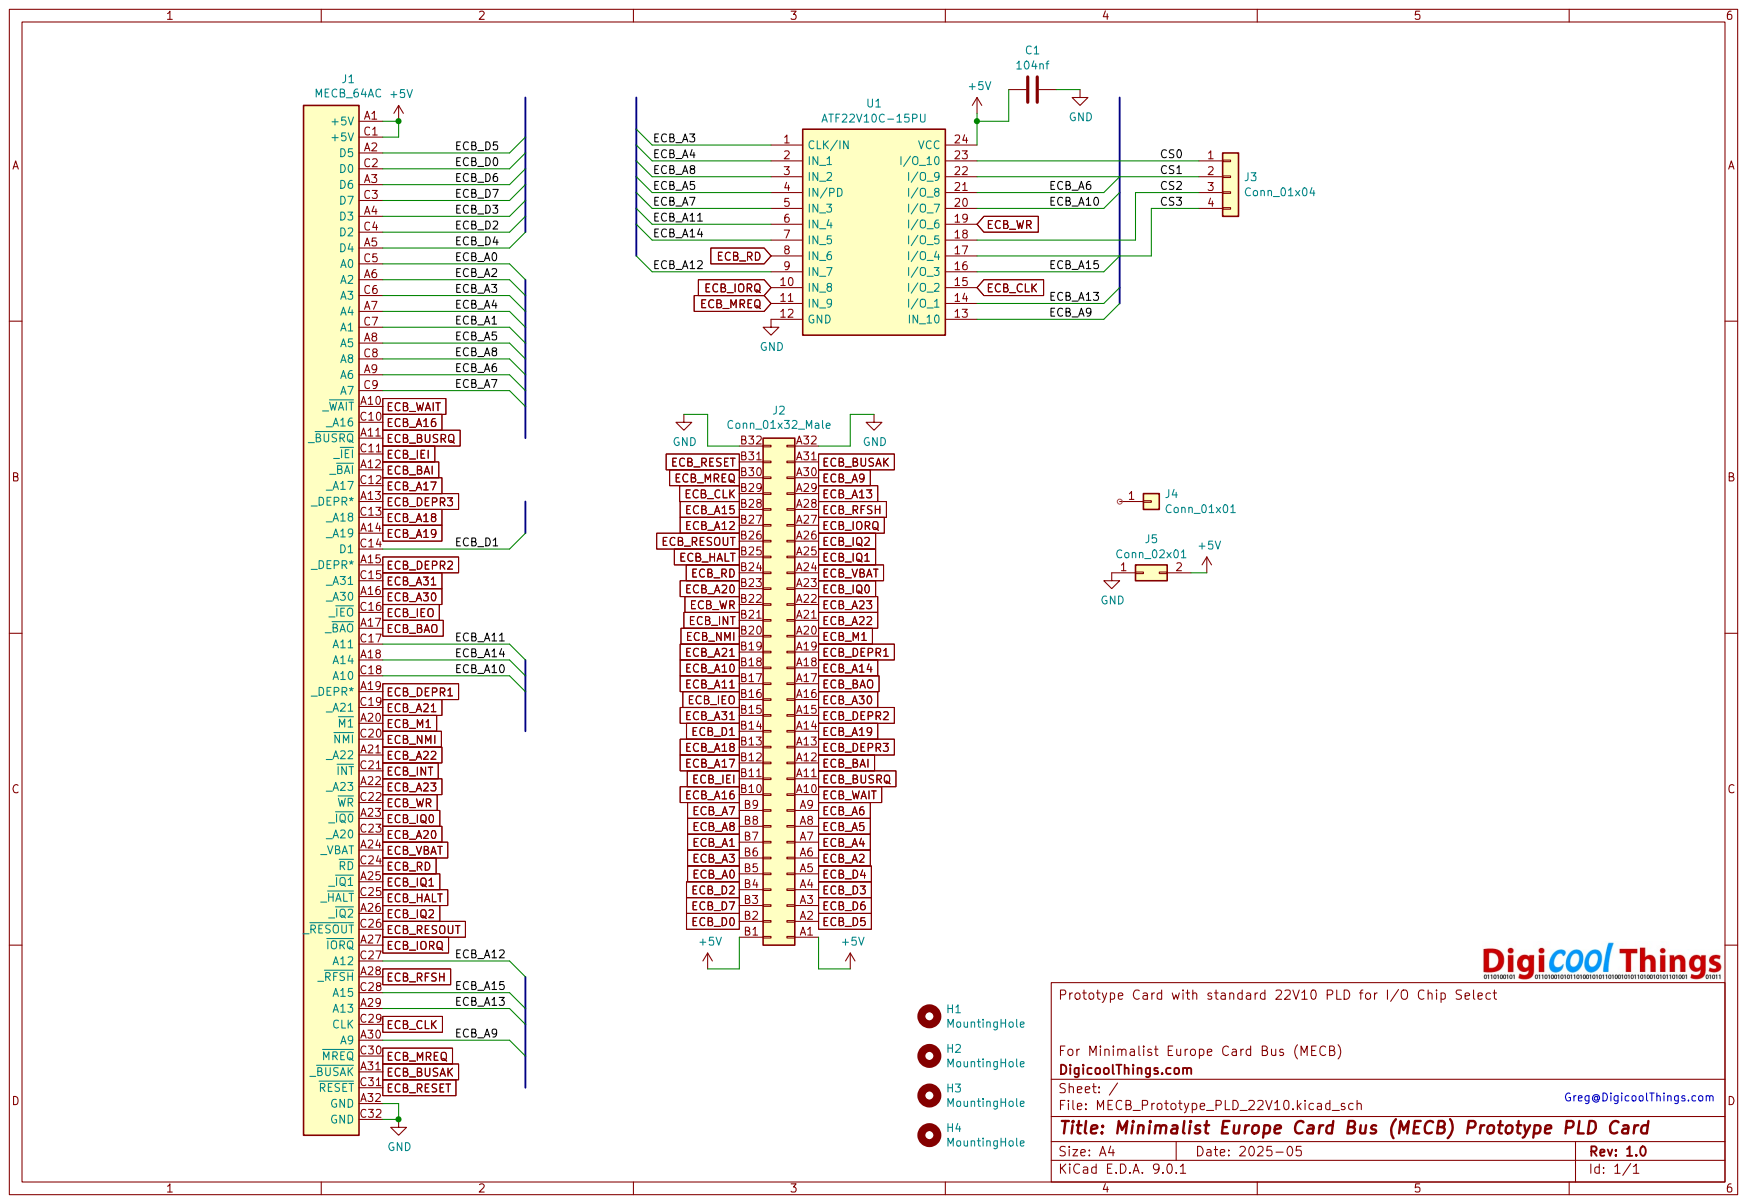
[picture p54: page 1]
