DigicoolThings/MECB/MECB_V9938_or_V9958_VDP/MECB_V9938_or_V9958_VDP_schematic_v1.2.pdf

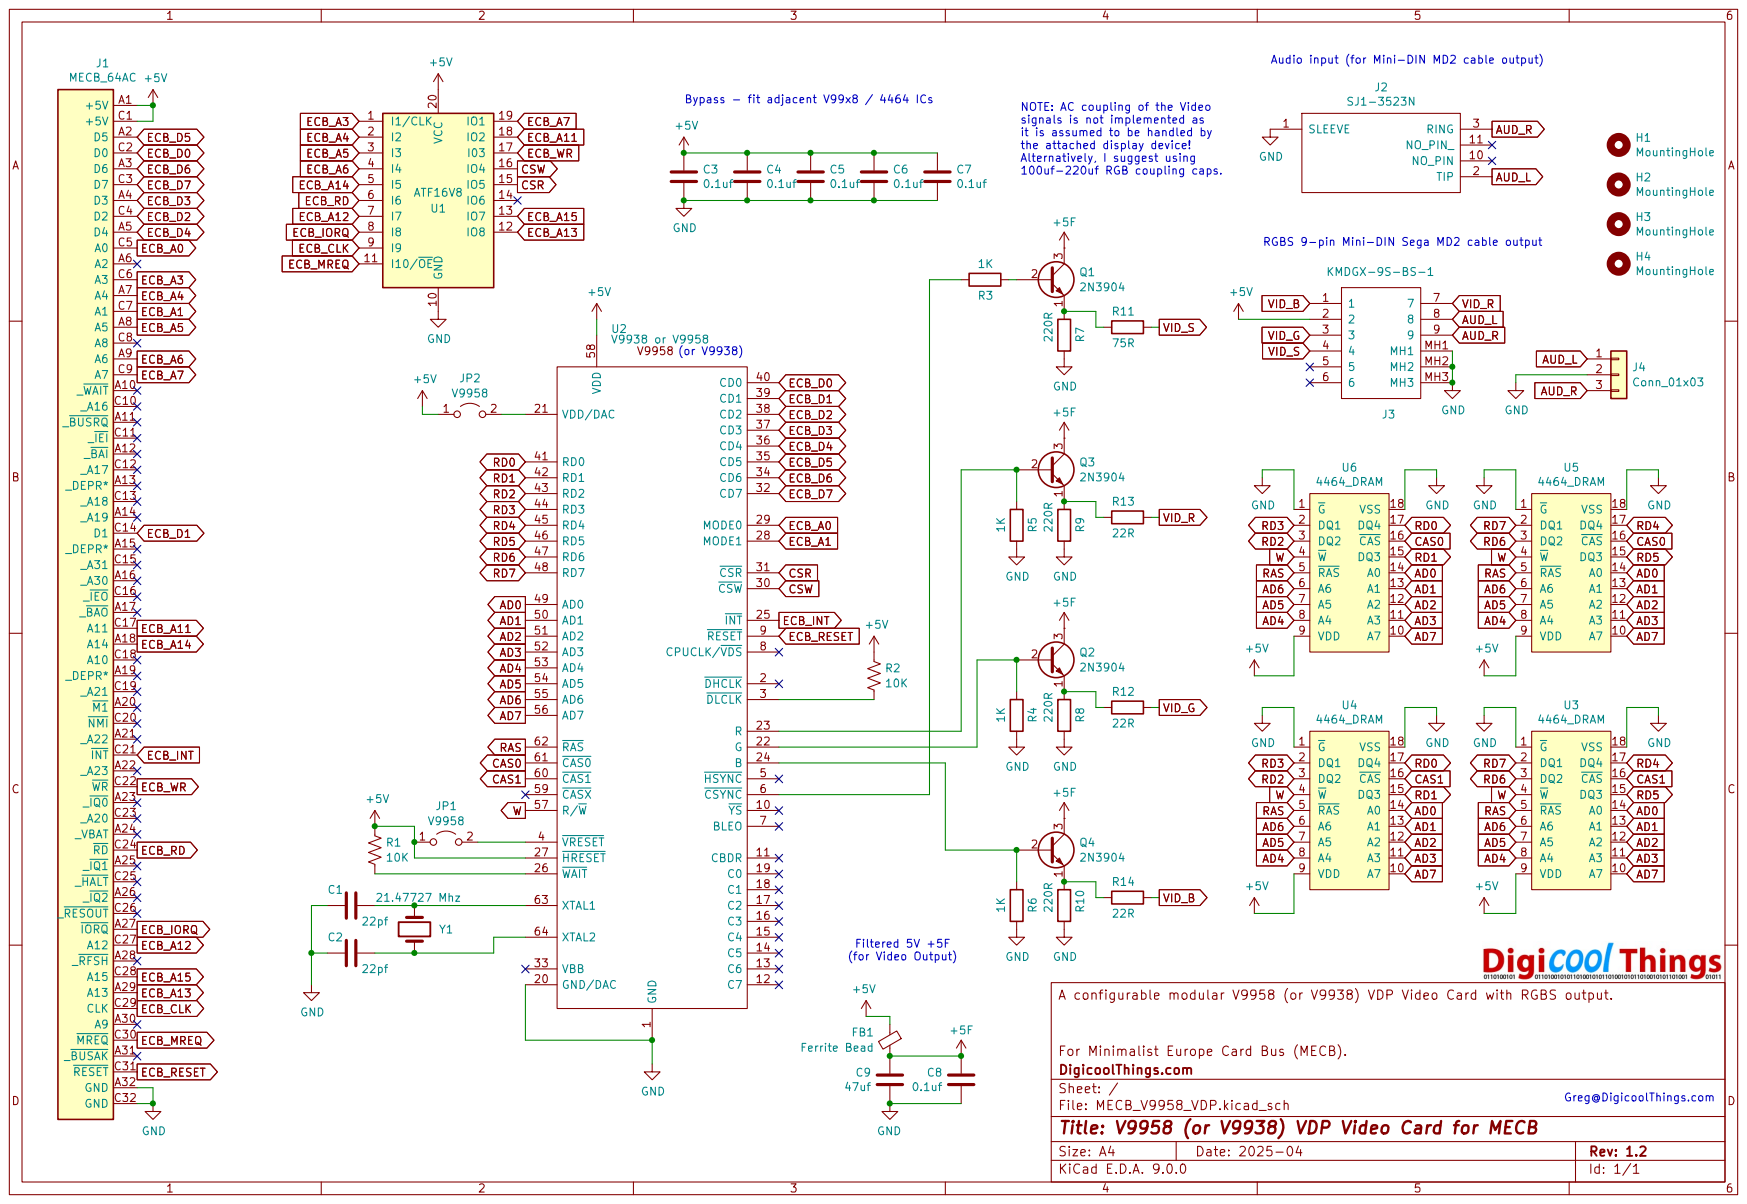
[picture p55: page 1]
