DigicoolThings/MECB/MECB_Motorola_IO/MECB_Motorola_IO_Schematic.pdf

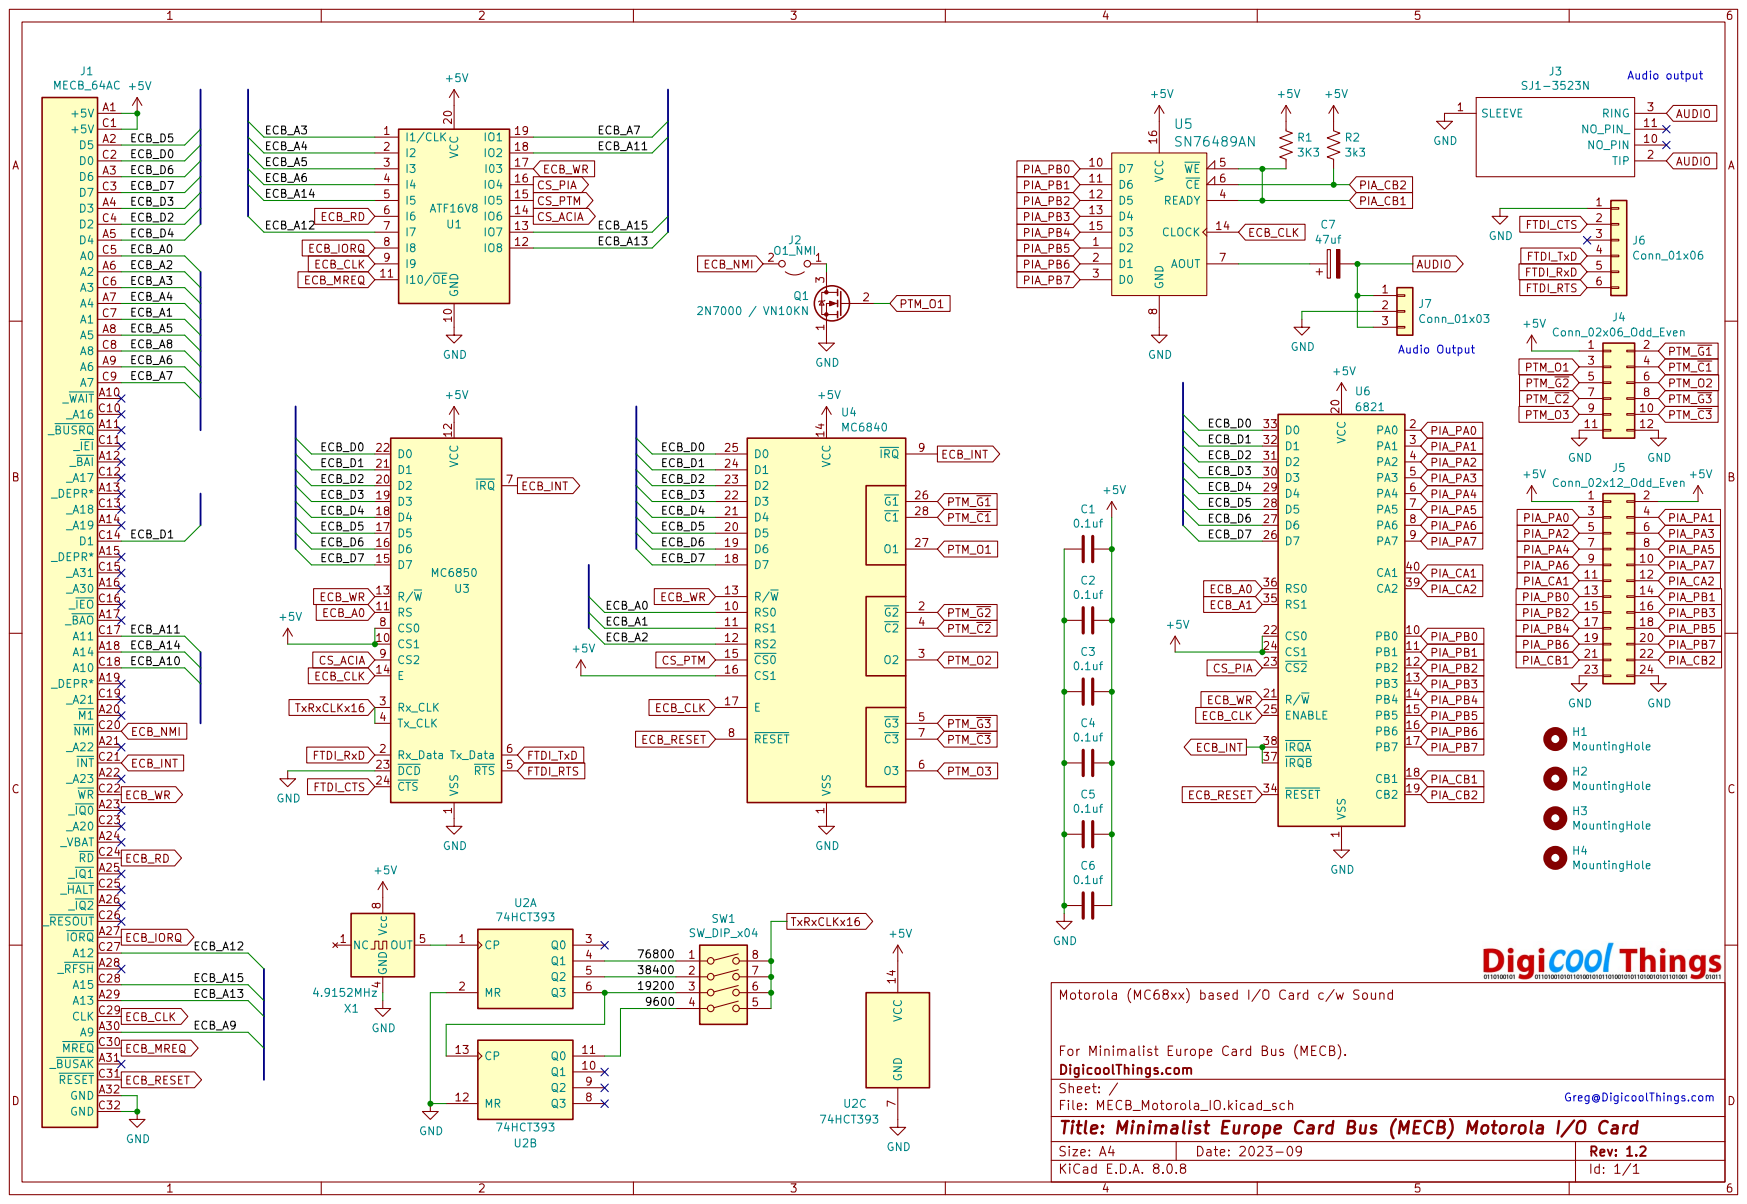
[picture p56: page 1]
