DigicoolThings/MECB/MECB_BackPlane_Extension/MECB_Backplane_Extension_Schematic.pdf

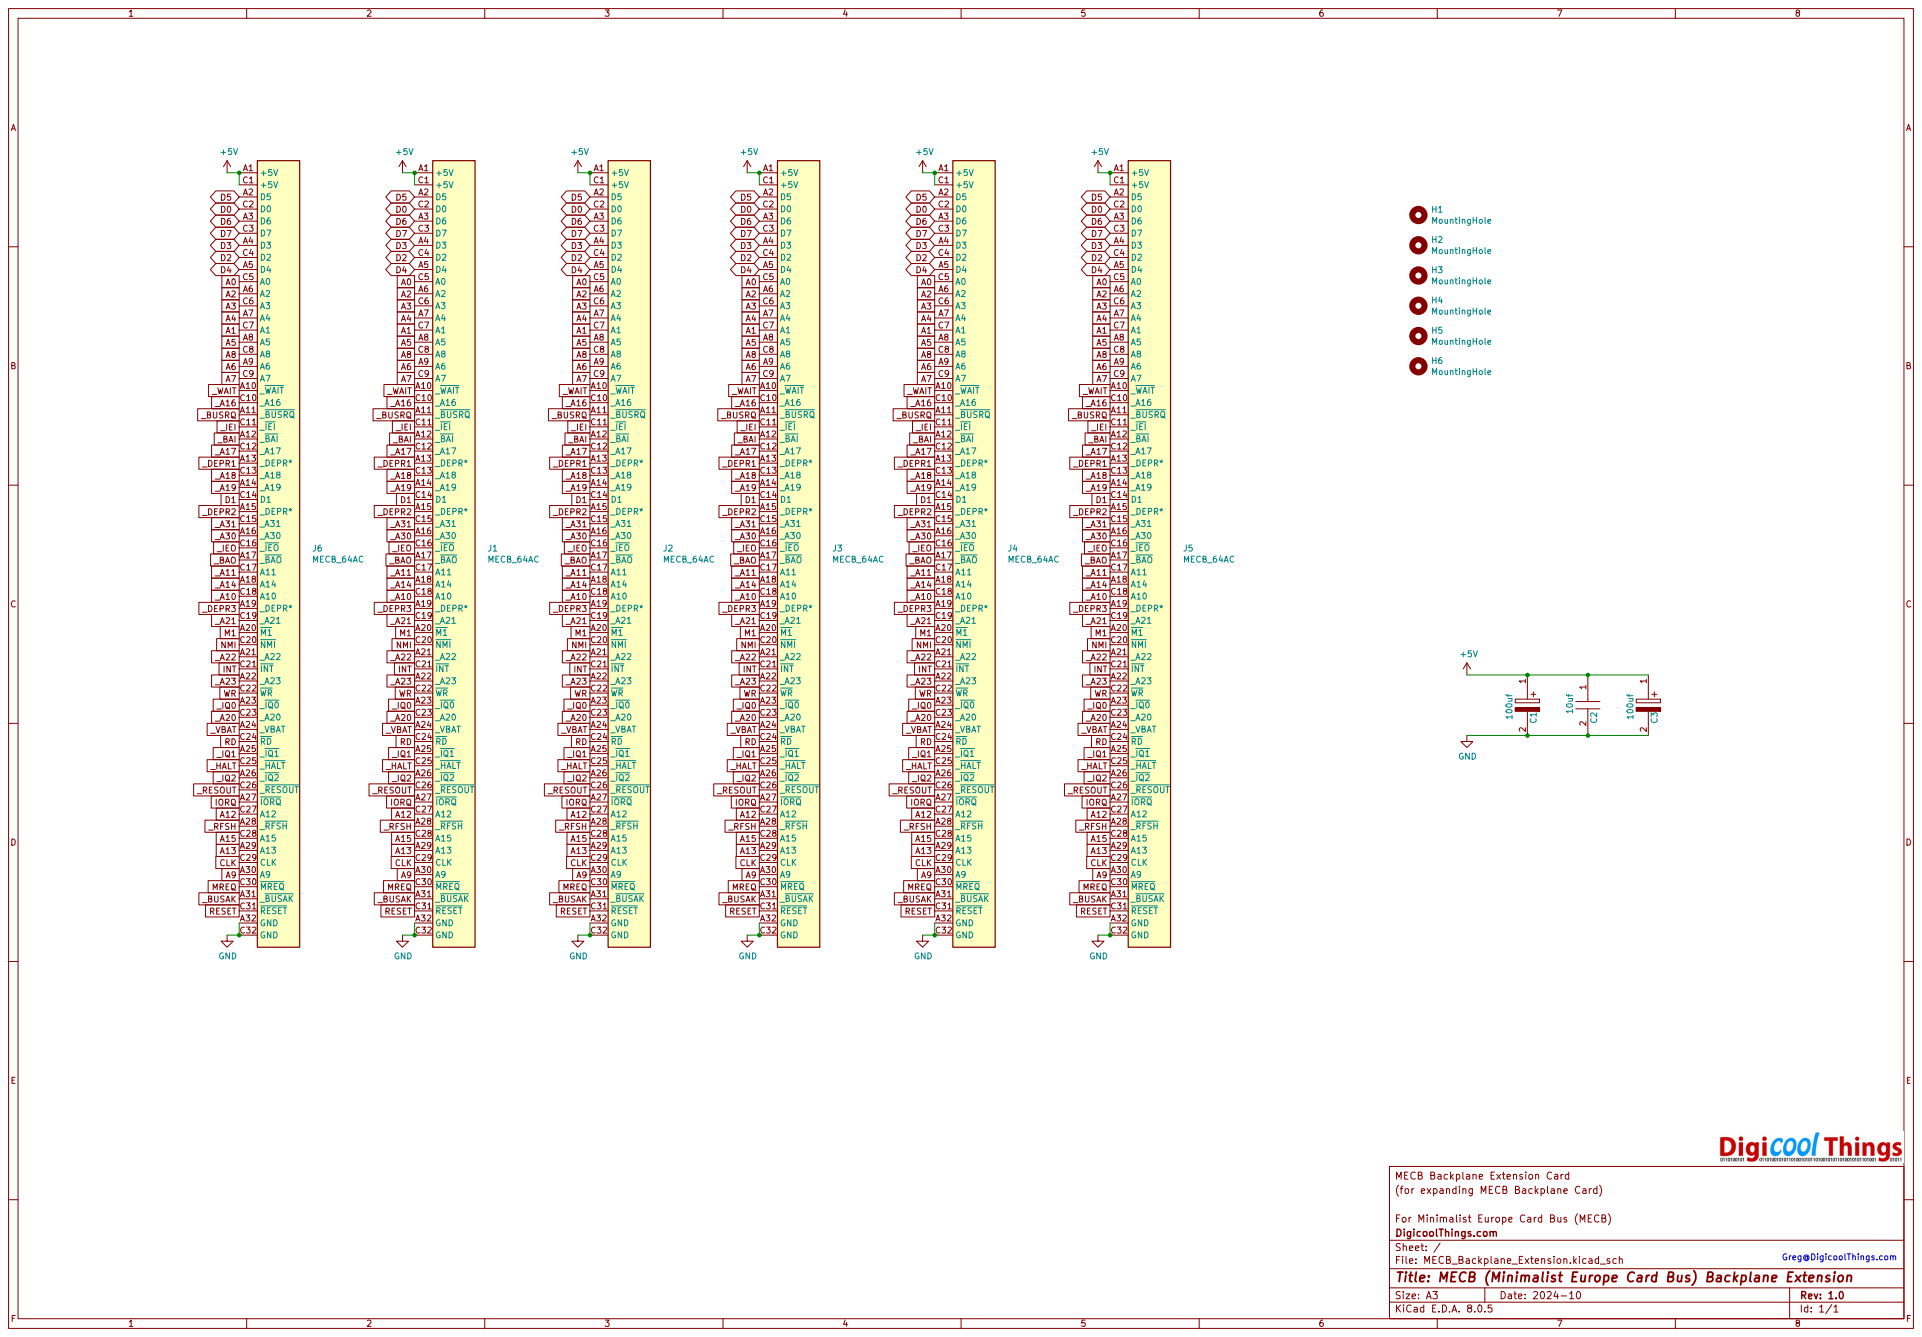
[picture p57: page 1]
