DigicoolThings/MECB/MECB_6502_CPU/MECB_6502_CPU_Schematic.pdf

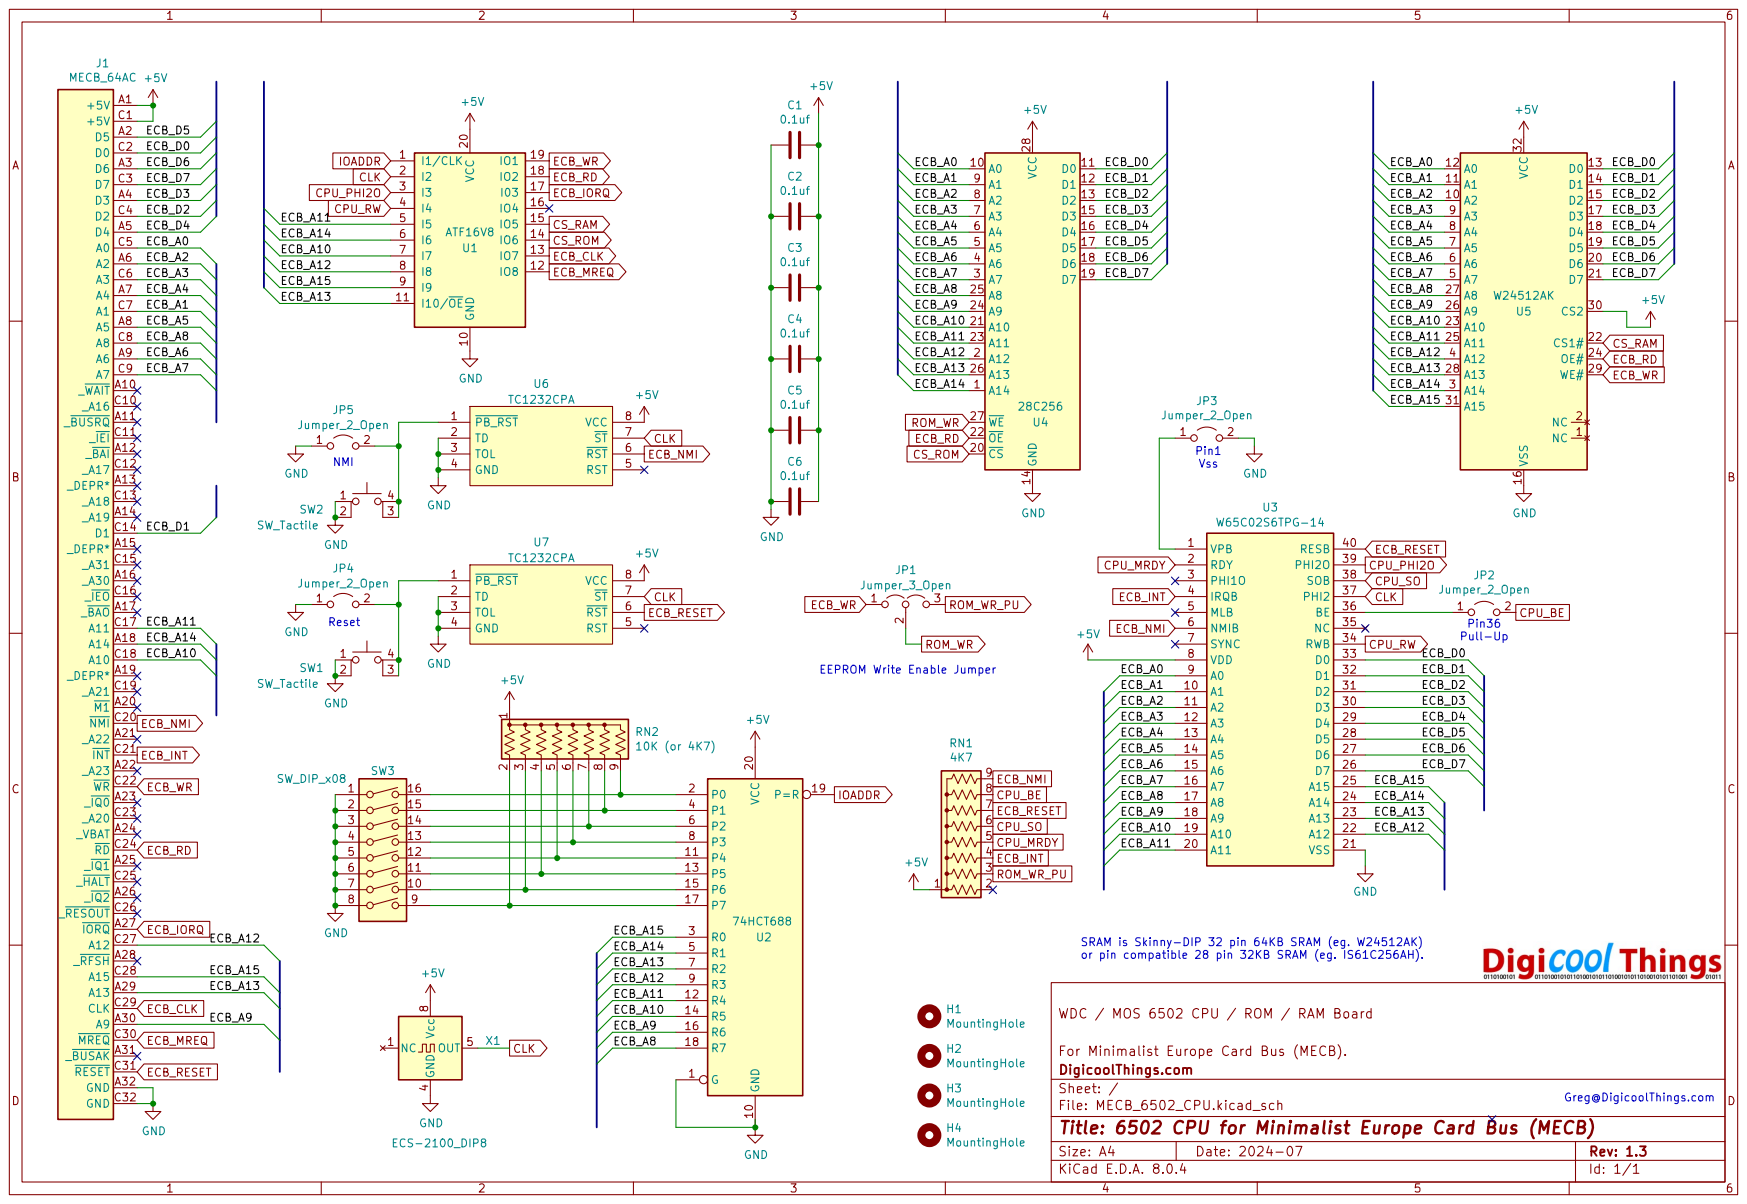
[picture p58: page 1]
