DigicoolThings/MECB/MECB_BackPlane/MECB_BackPlane_Schematic.pdf

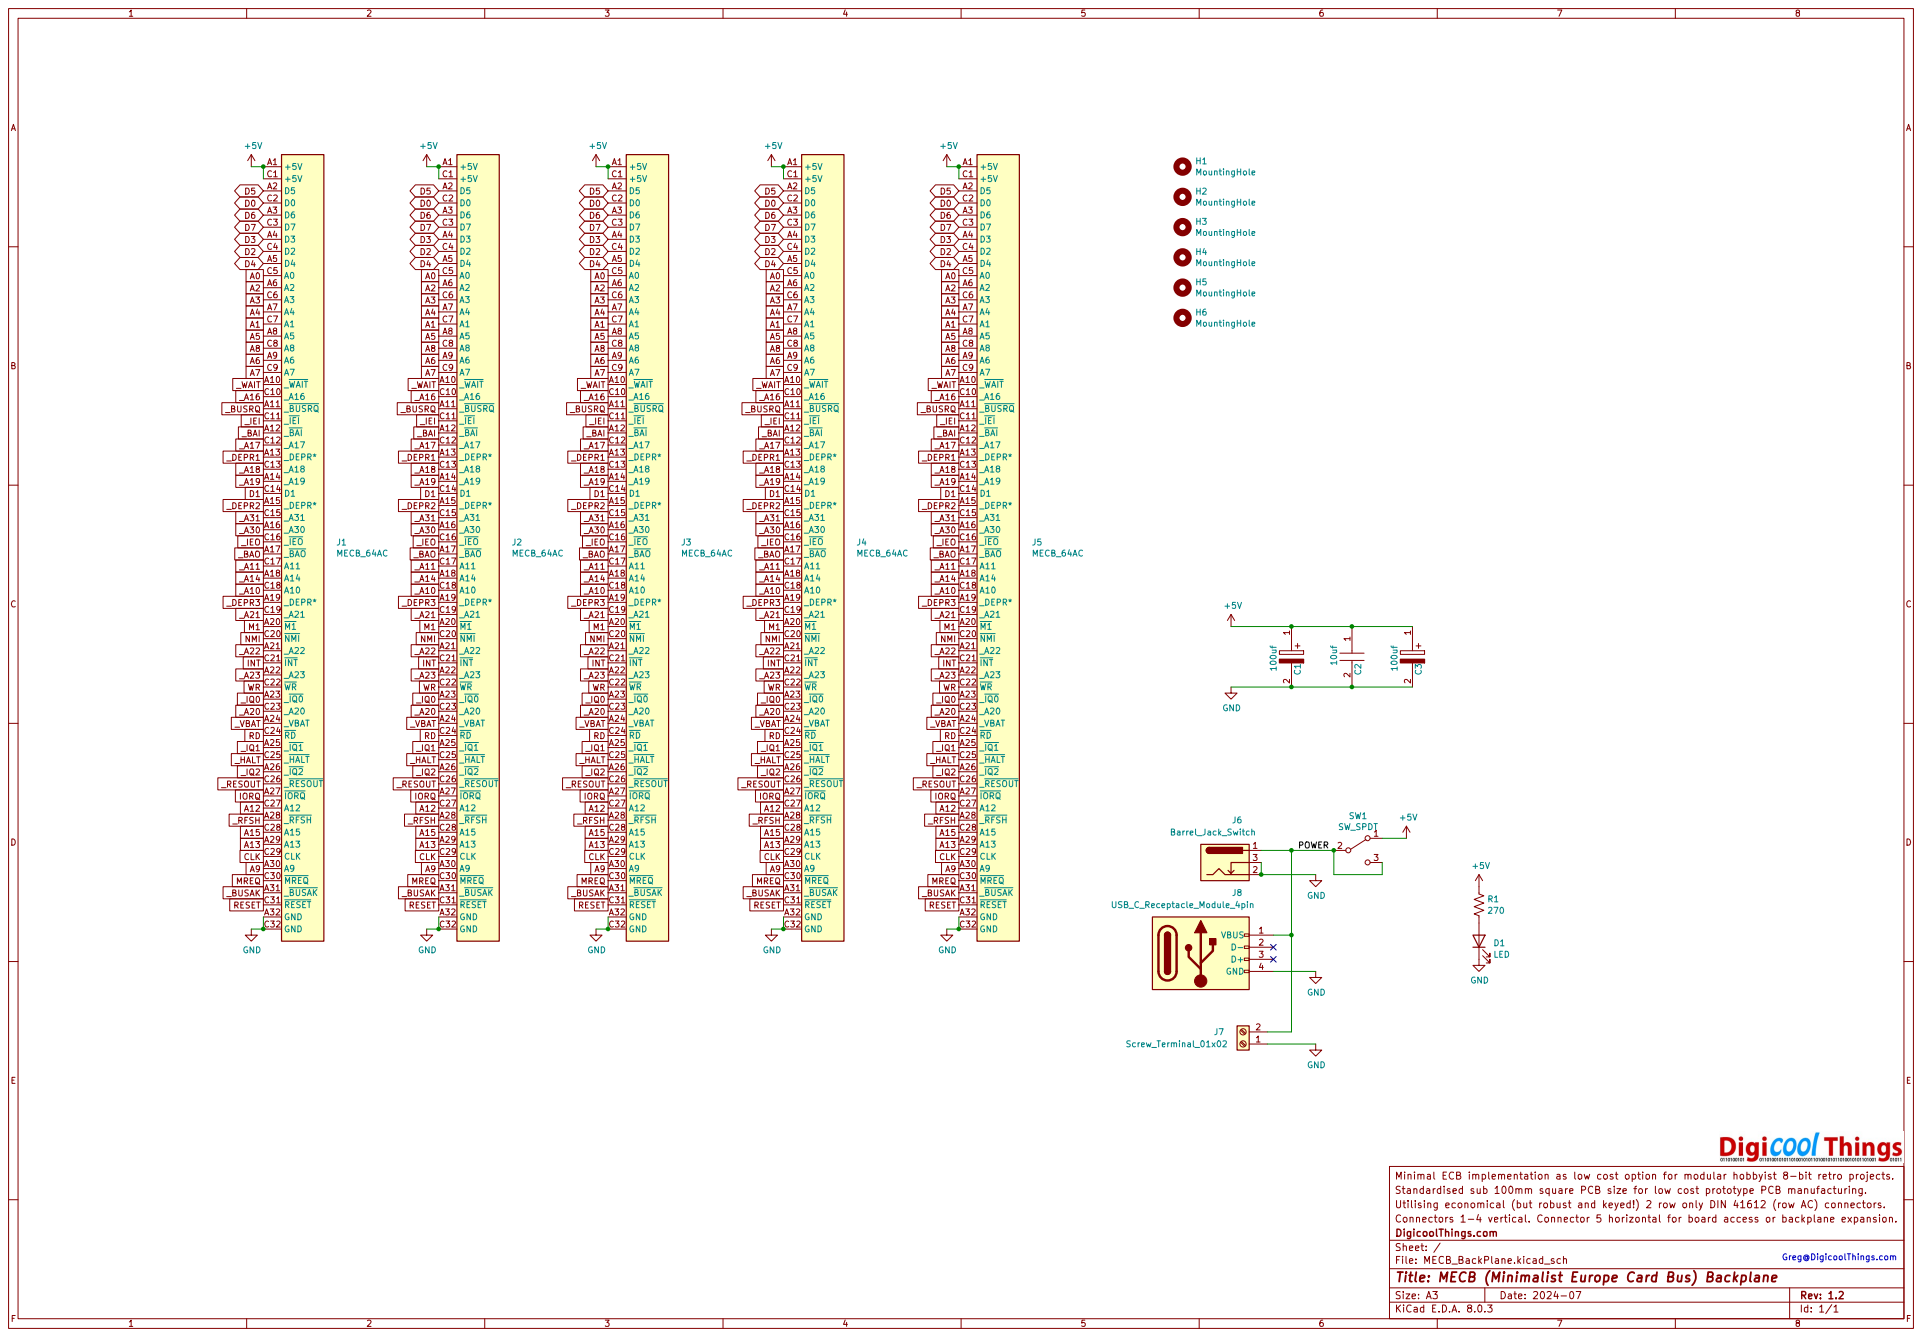
[picture p59: page 1]
