DigicoolThings/MECB/MECB_Prototype/MECB_Prototype_Schematic.pdf

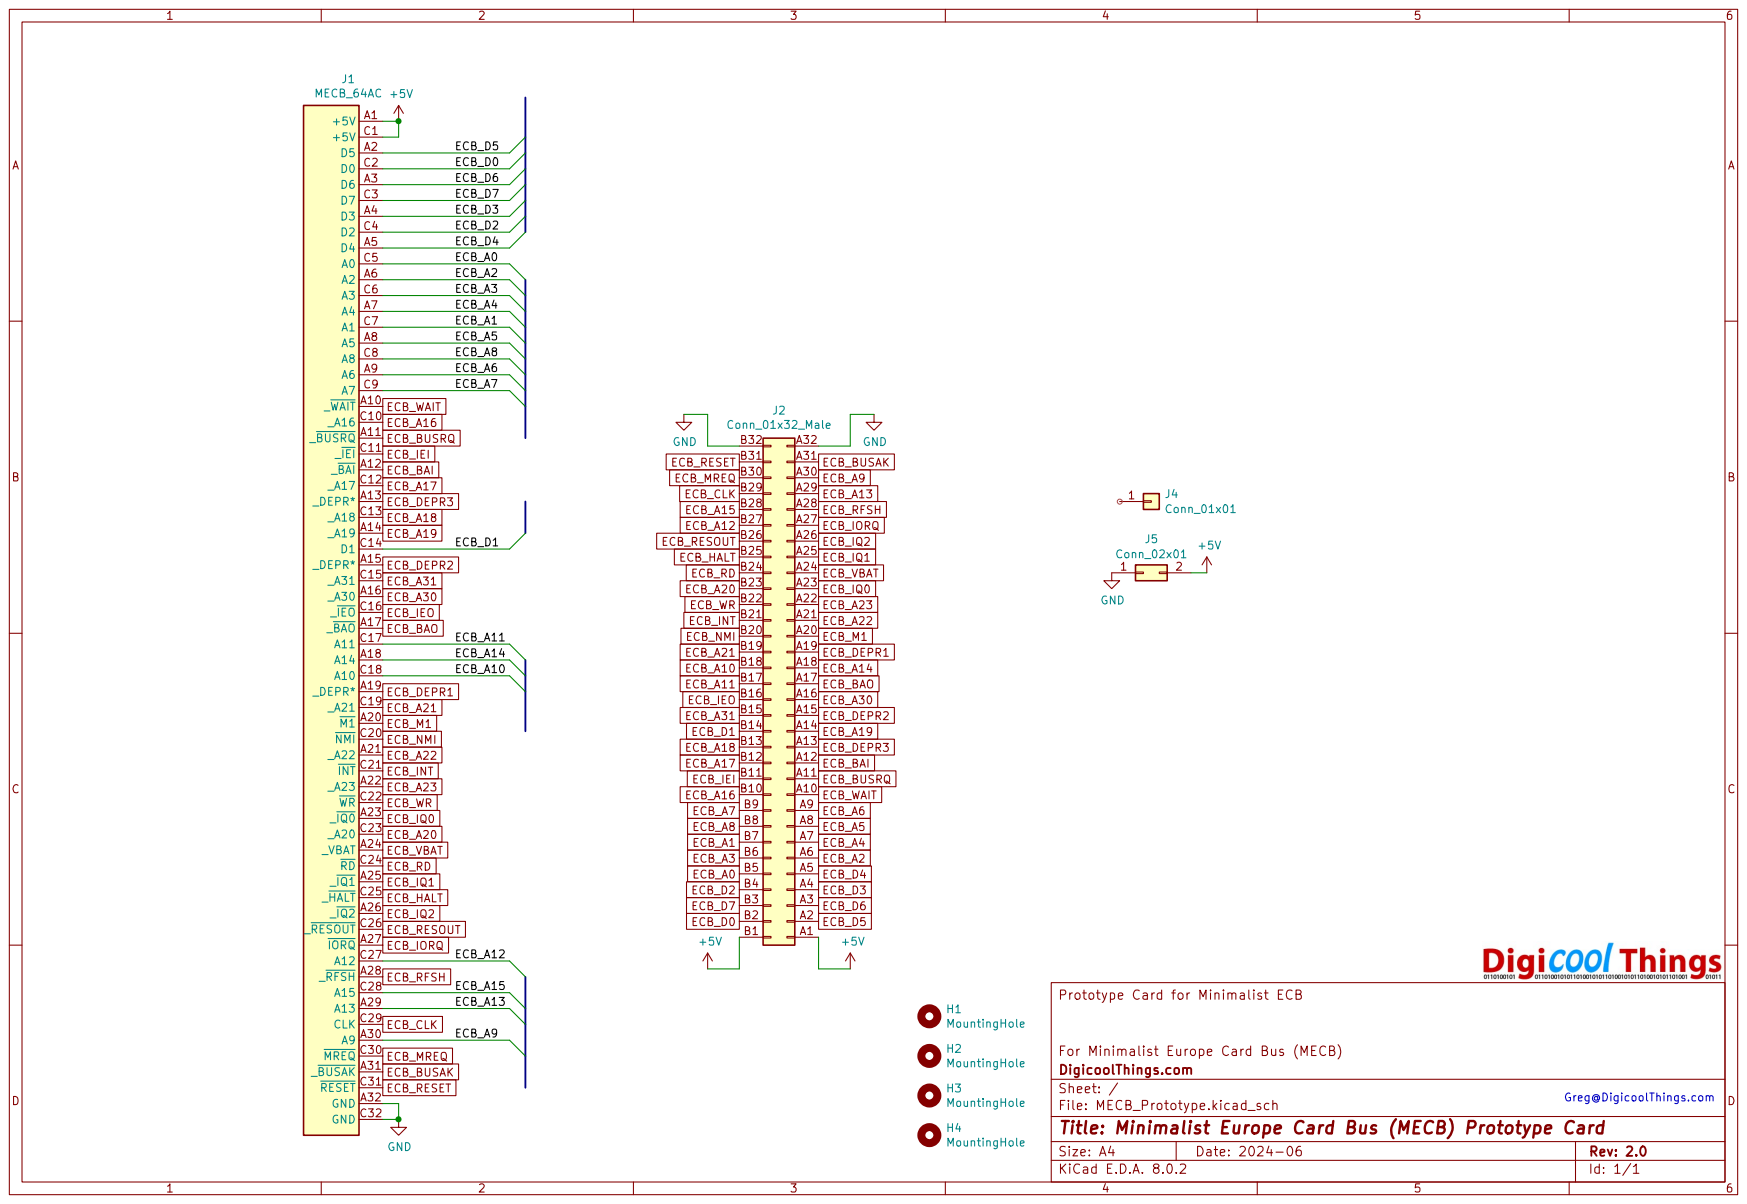
[picture p60: page 1]
