DigicoolThings/MECB/MECB_6309_CPU_PLCC/MECB_6309_CPU_PLCC_Schematic.pdf

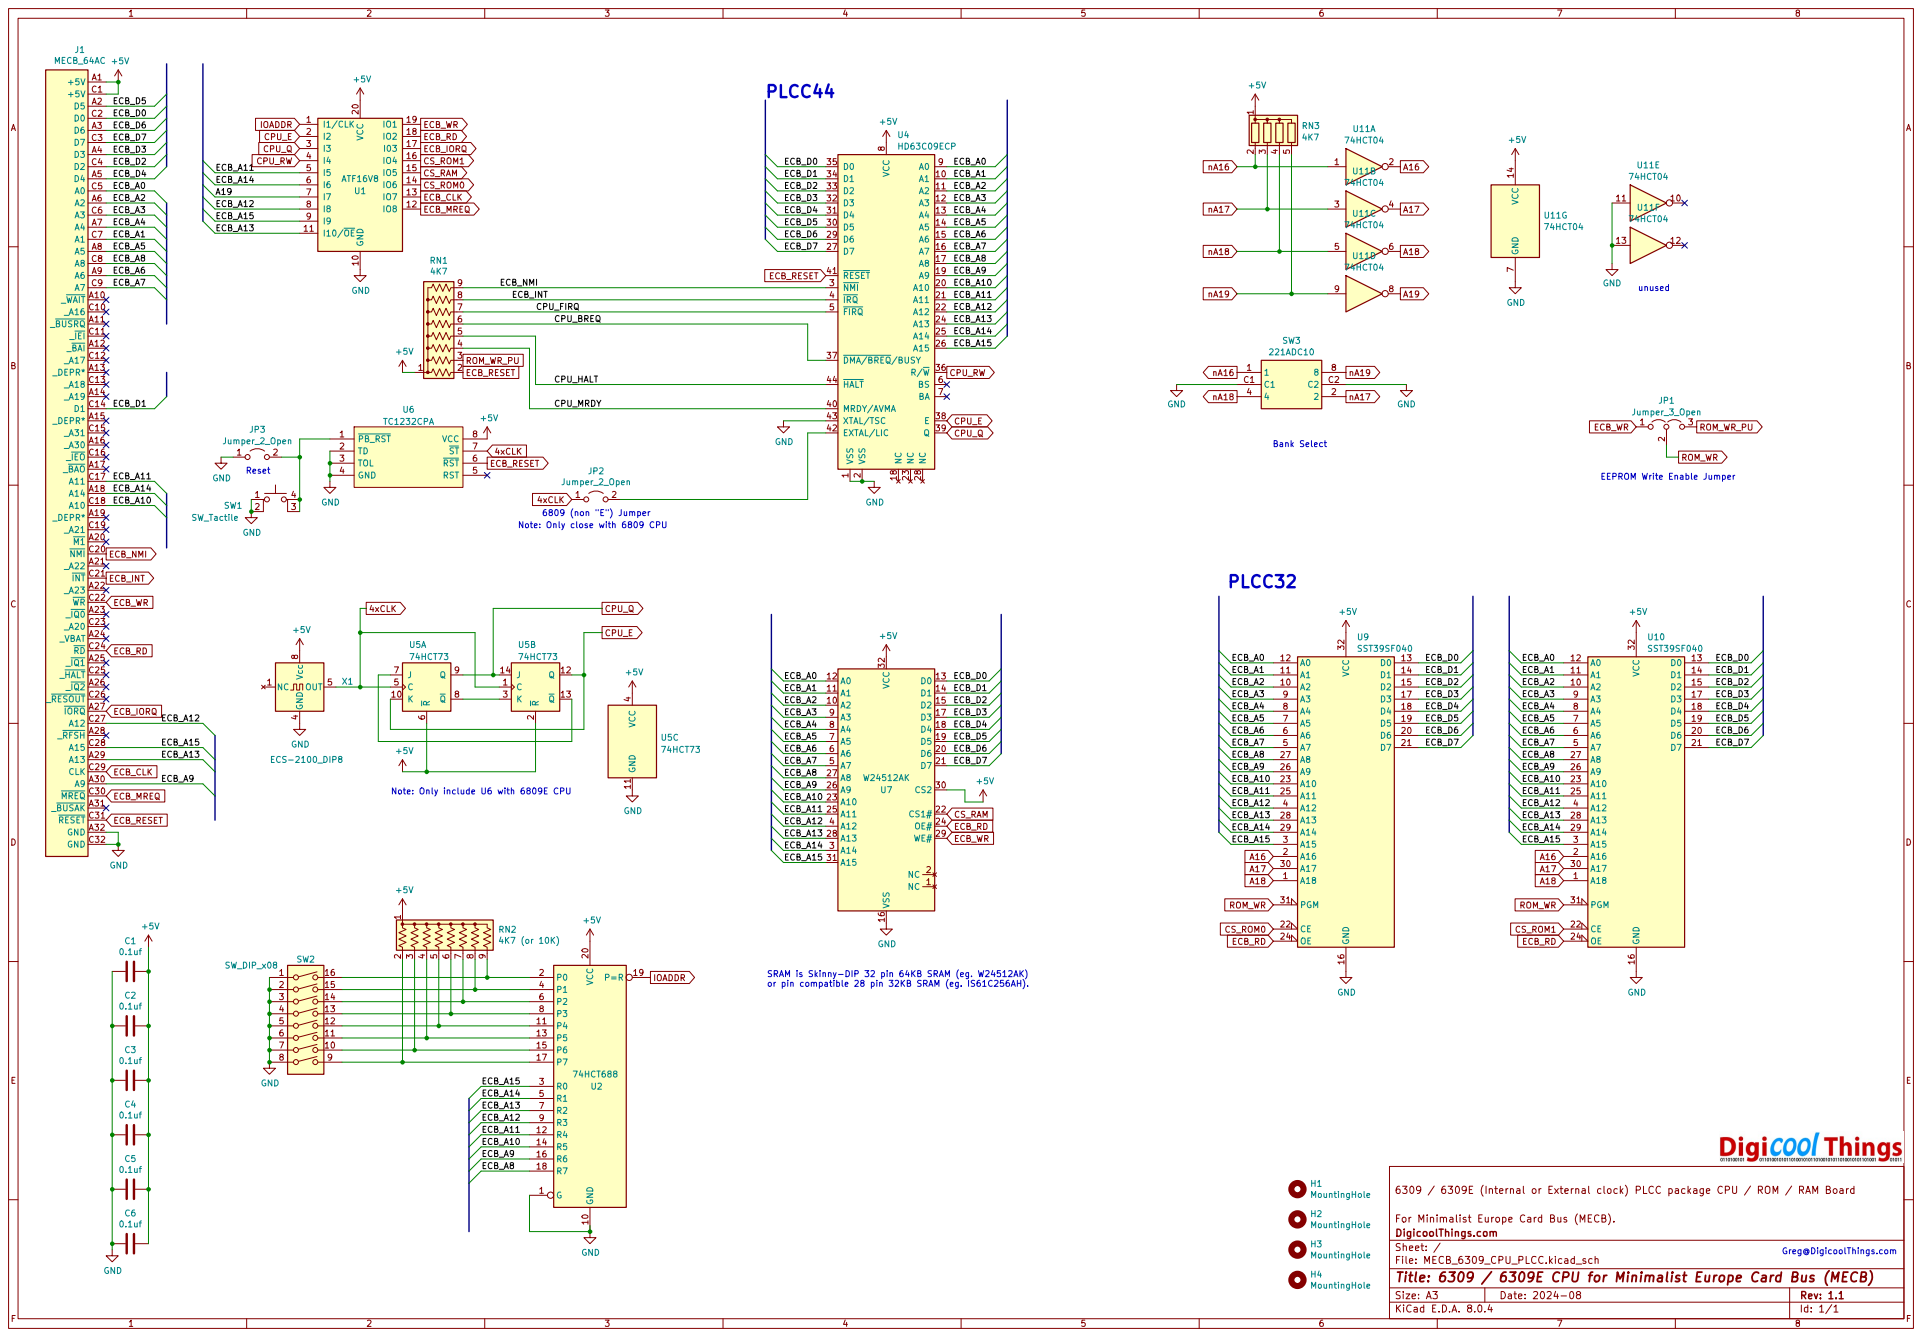
[picture p61: page 1]
