DigicoolThings/MECB/MECB_6809_CPU/MECB_6809_CPU_Schematic.pdf

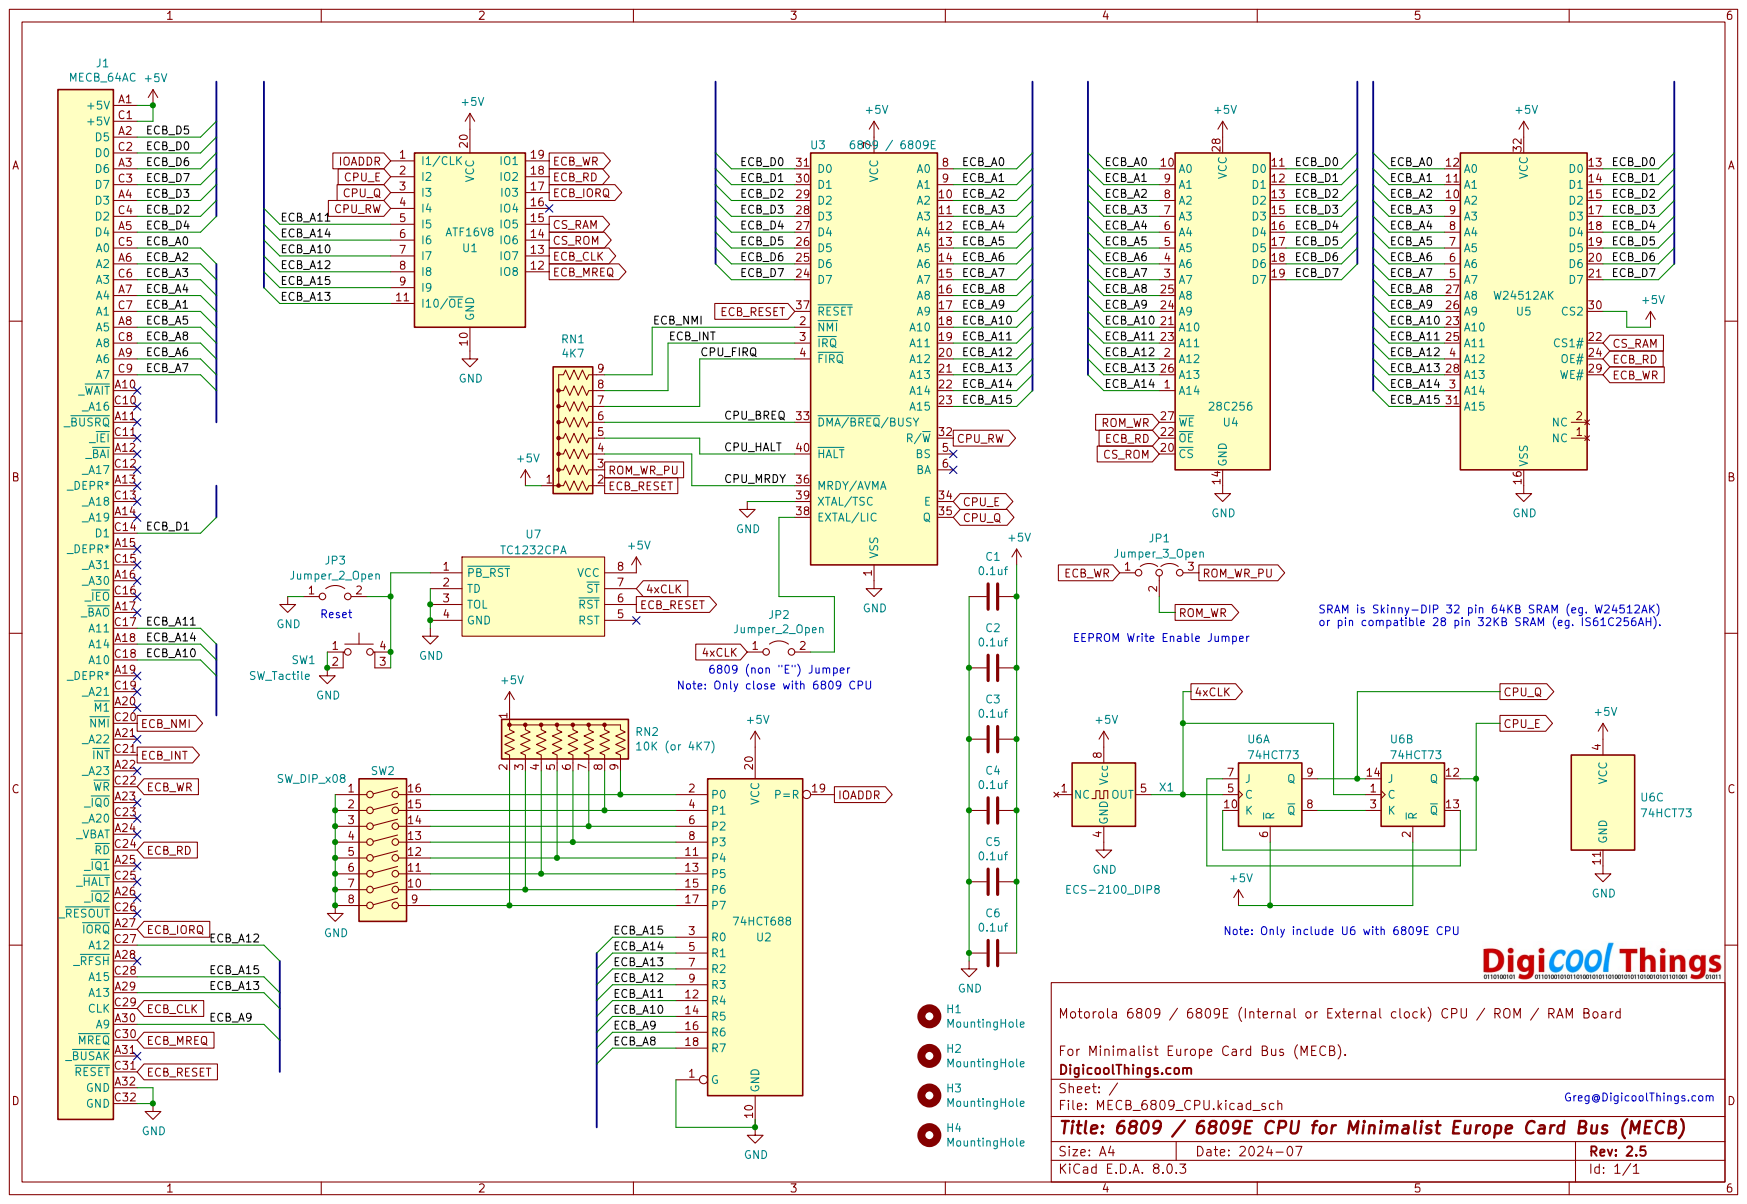
[picture p62: page 1]
