DigicoolThings/MECB/MECB_TMS9918_or_TMS992x_VDP/MECB_TMS9918_or_TMS992x_VDP_Schematic.pdf

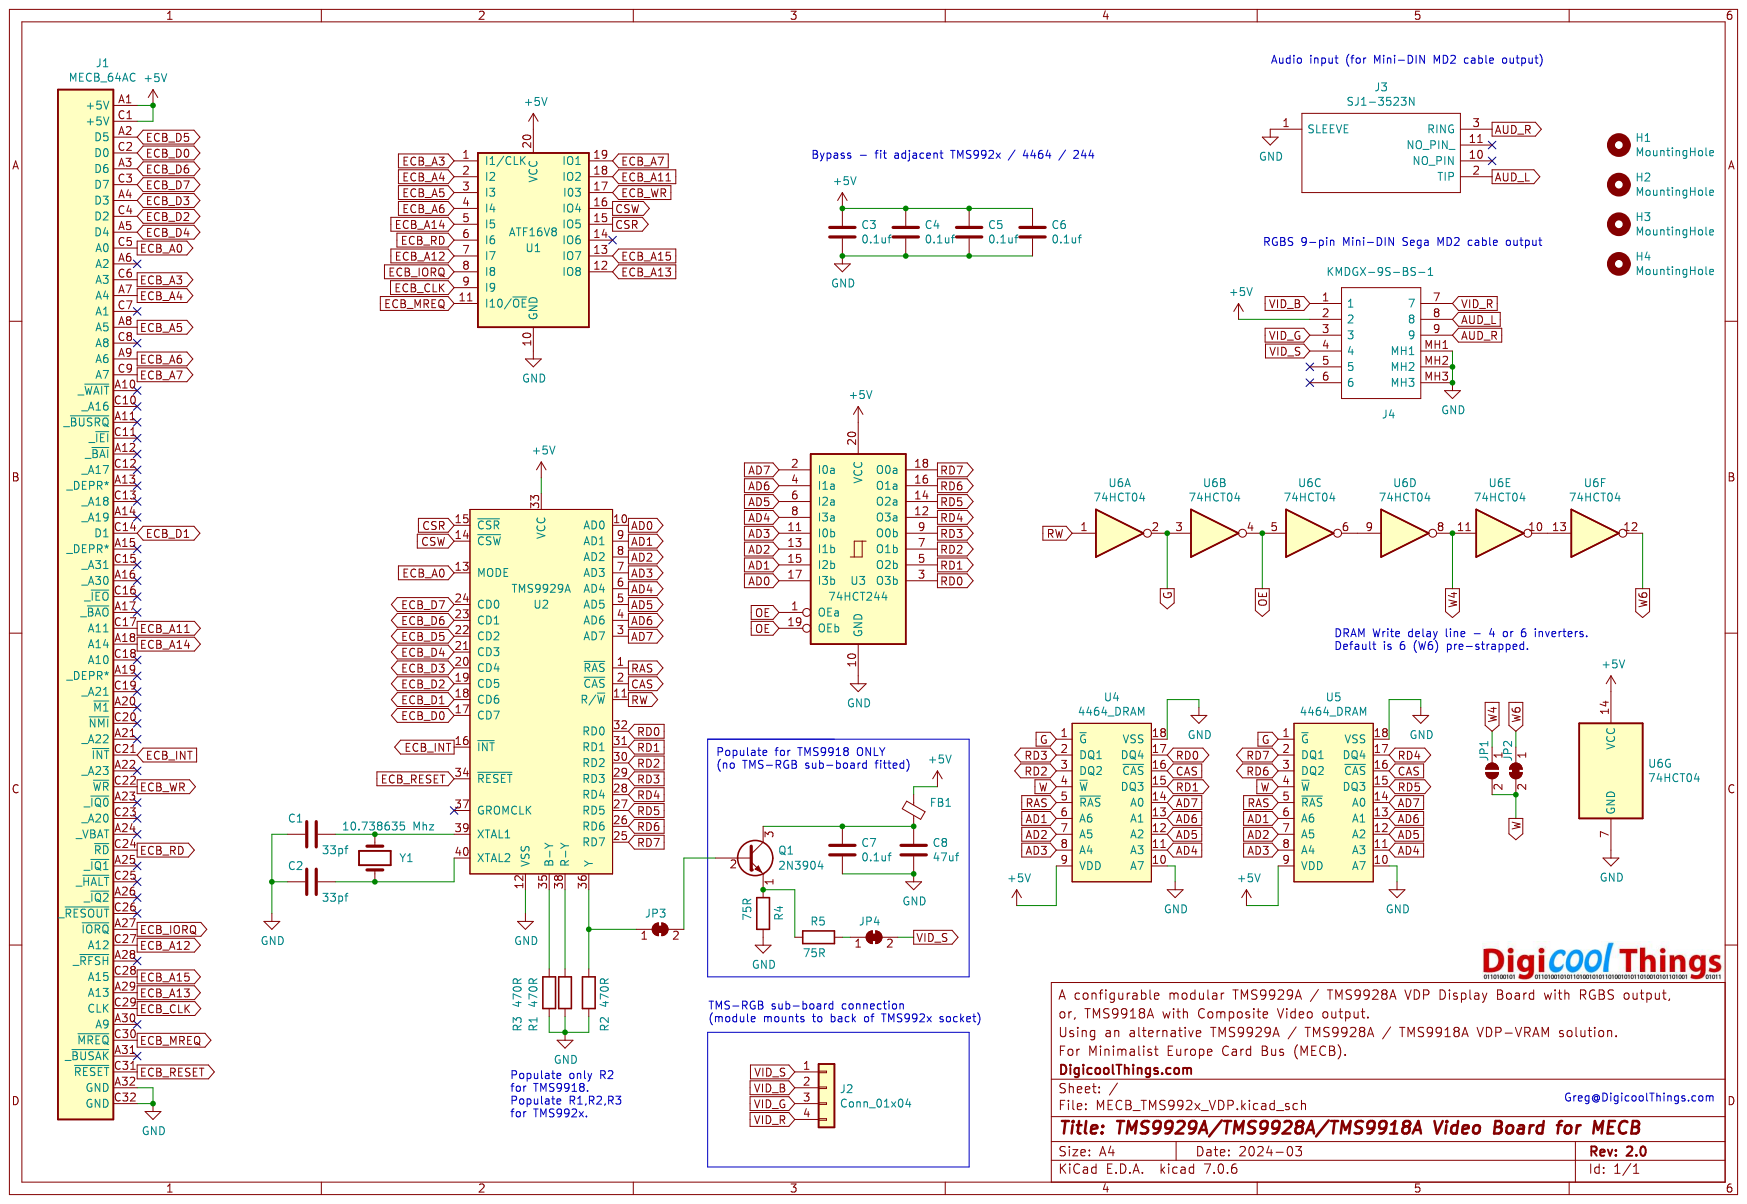
[picture p63: page 1]
