DigicoolThings/MECB/MECB_1MB_ROM_Expansion/MECB_1MB_ROM_Expansion_Schematic.pdf

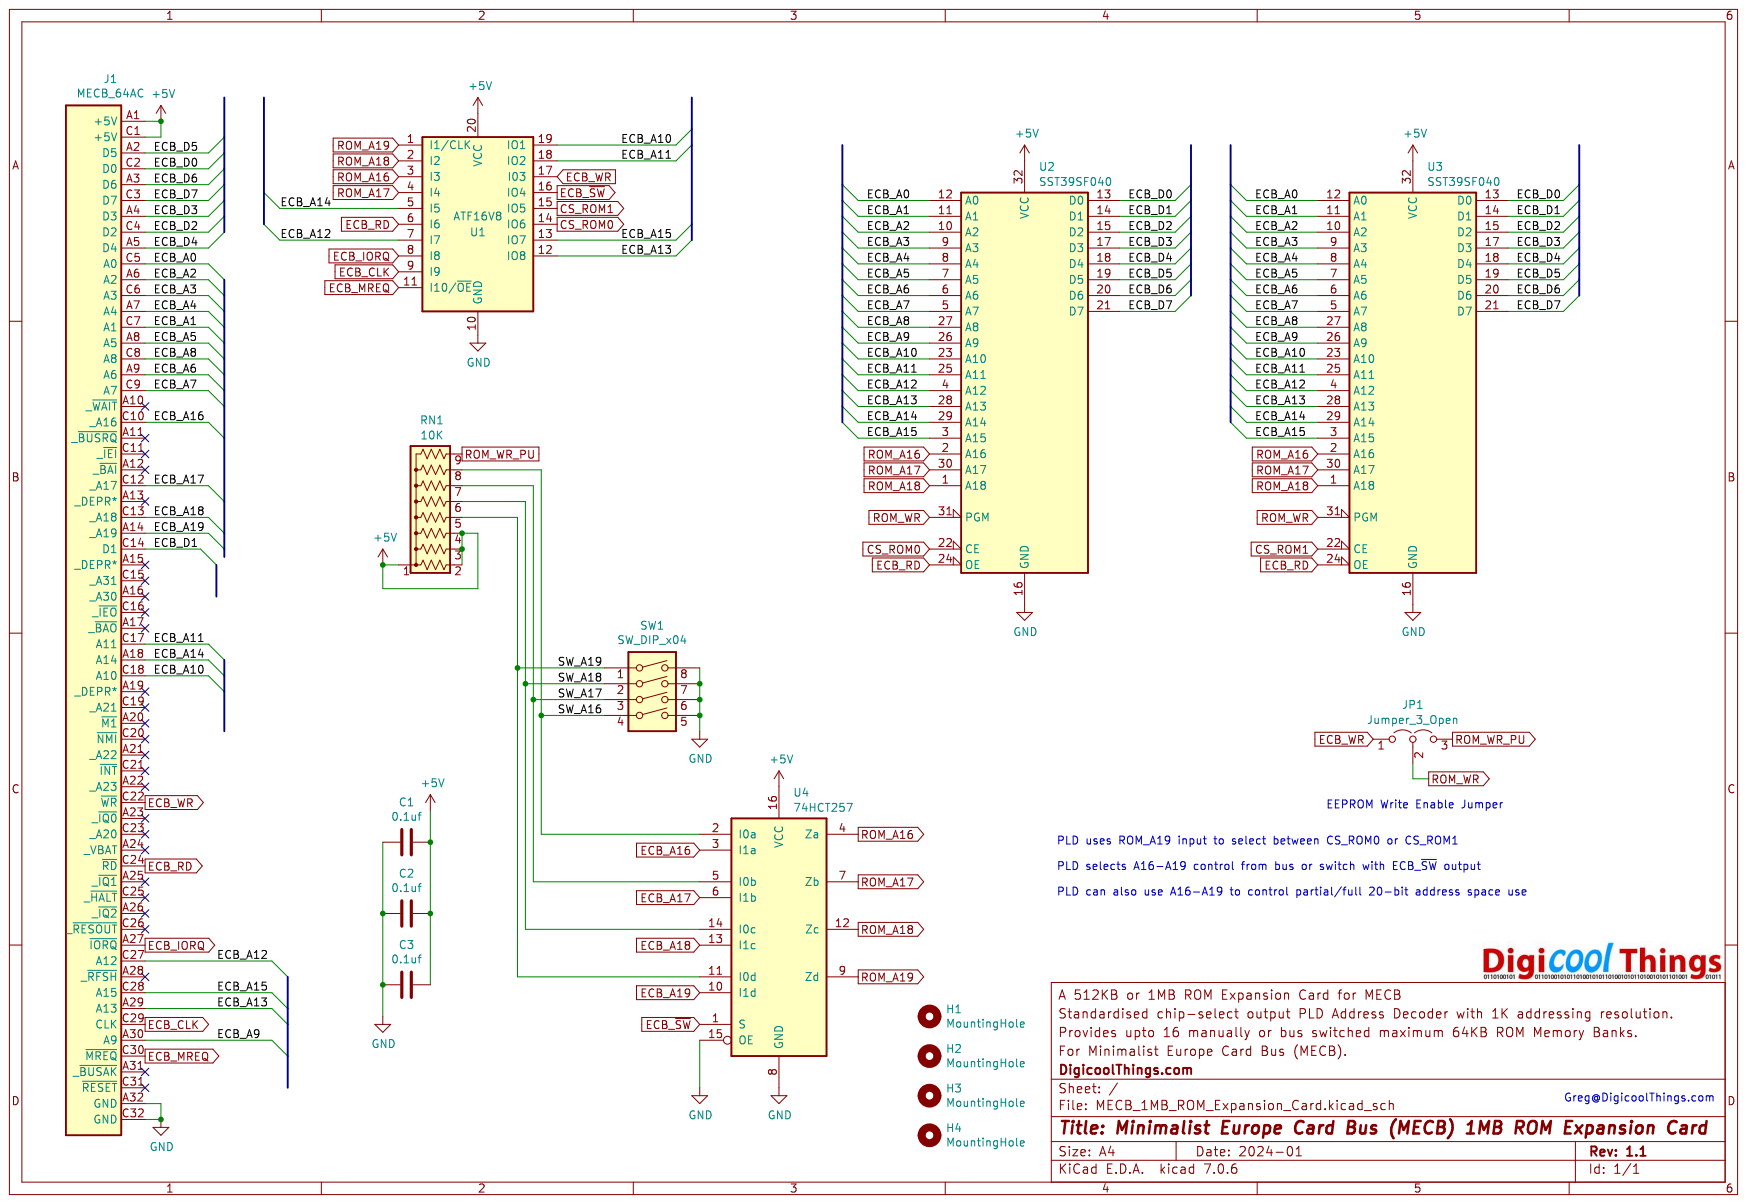
[picture p64: page 1]
