DigicoolThings/MECB/MECB_6809_CPU/HD63C09_PLCC-DIP40_Adapter/HD63C09_PLCC-DIP40_Adapter_Schematic_v1.0.pdf

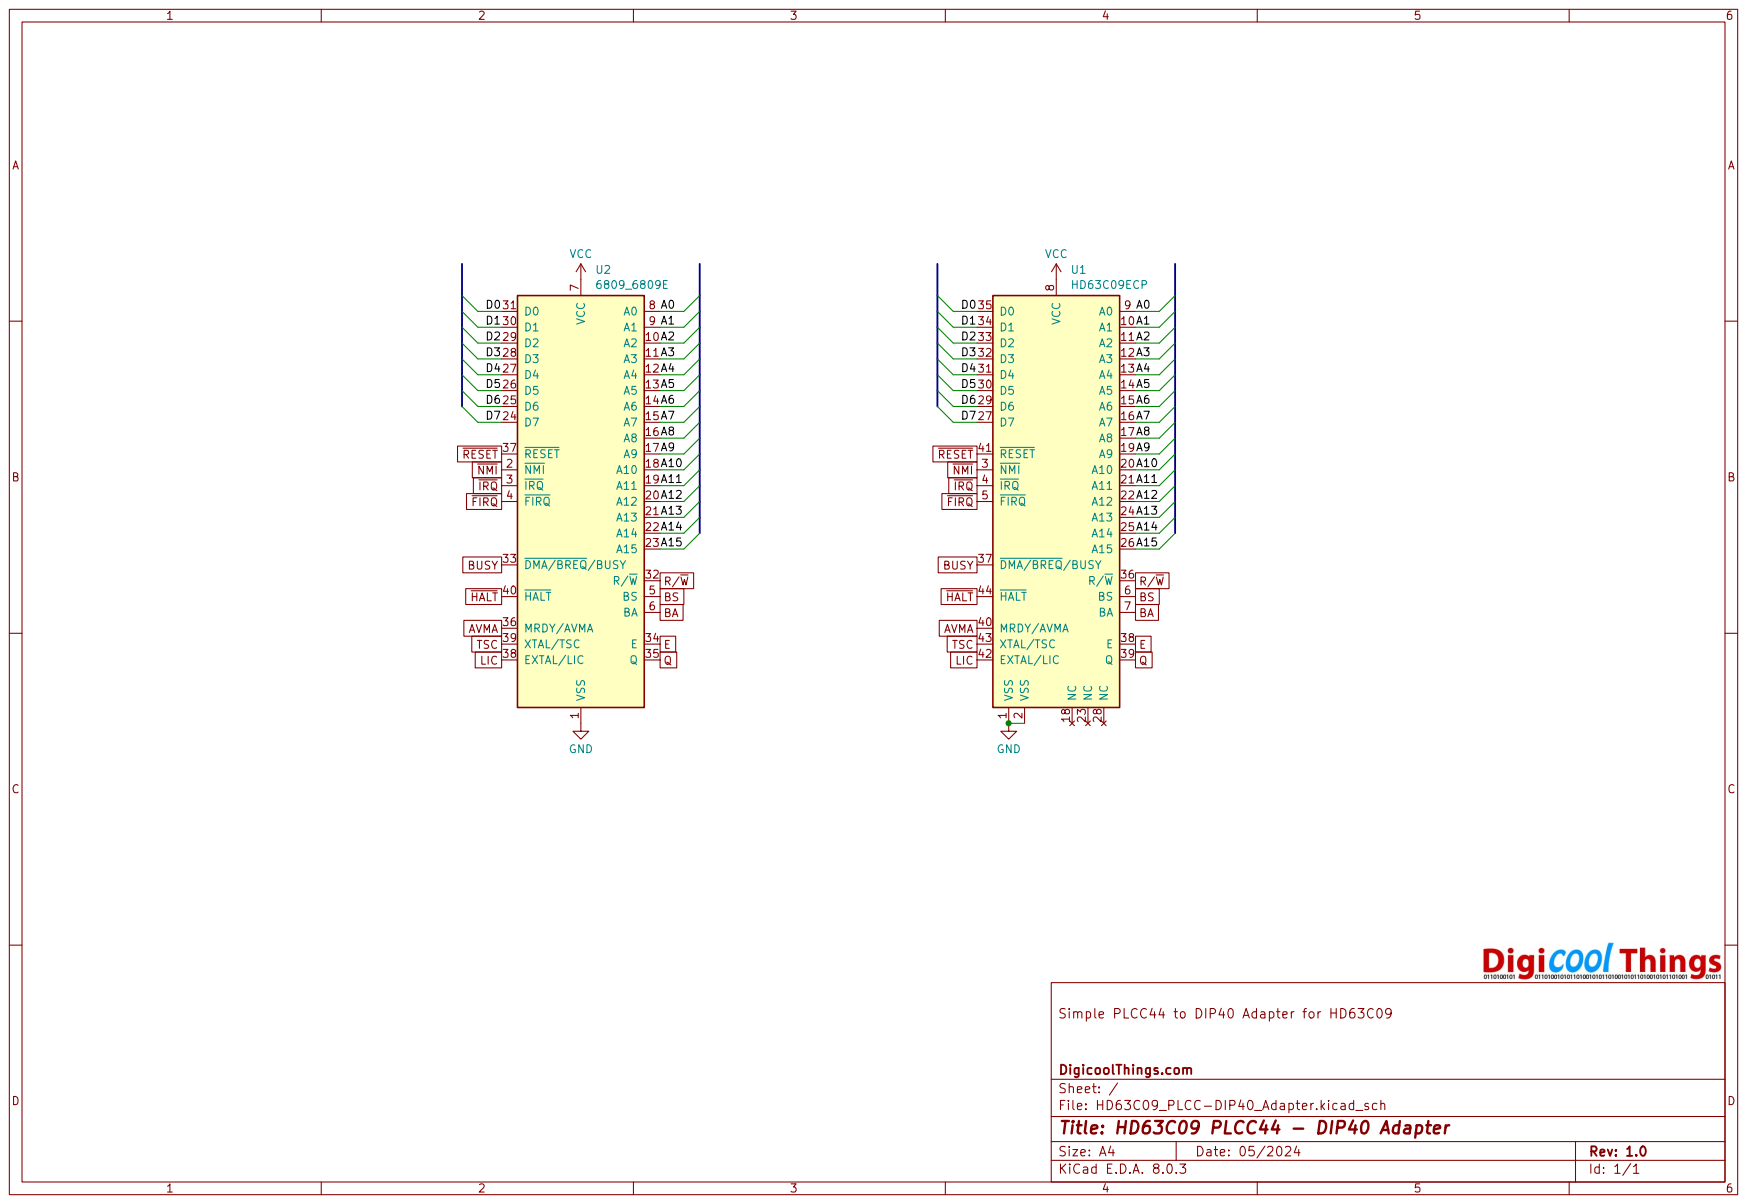
[picture p65: page 1]
