DigicoolThings/MECB/MECB_68008_CPU/Tutor/basic68k.asm

*************************************************************************************
*										    *
*	Enhanced BASIC for the Motorola MC680xx					    *
*										    *
*	This version is for the TS2 single board computer.		            *
*	Jeff Tranter (tranter@pobox.com)					    *
*										    *
*************************************************************************************
*										    *
*	Copyright(C) 2002-12 by Lee Davison. This program may be freely distributed *
*	for personal use only. All commercial rights are reserved.		    *
*										    *
*	More 68000 and other projects can be found on my website at ..		    *
*										    *
*	 http://mycorner.no-ip.org/index.html					    *
*										    *
*	mail : leeedavison@googlemail.com					    *
*										    *
*************************************************************************************

* Ver 3.54

* Ver 3.54 adds experimental support for LOAD/SAVE using Hobbytronics
* USB Flash Drive Host Board
* Ver 3.53 fixes math error that affected exponentiation ("^") and
*  EXP() function. Thanks to joelang for fix.
* Ver 3.52 stops USING$() from reading beyond the end of the format string
* Ver 3.51 fixes the UCASE$() and LCASE$() functions for null strings
* Ver 3.50 unary minus in concatenate generates a type mismatch error
* Ver 3.49 doesn't tokenise 'DEF' or 'DEC' within a hex value
* Ver 3.48 allows scientific notation underflow in the USING$() function
* Ver 3.47 traps the use of array elements as the FOR loop variable
* Ver 3.46 updates function and function variable handling

*************************************************************************************
*
* Ver 3.45 makes the handling of non existant variables consistent and gives the
* option of not returning an error for a non existant variable. If this is the
* behaviour you want just change novar to some non zero value

novar		EQU	0				* non existant variables cause errors

* Set the symbol FLASH_SUPPORT to 1 if you want to enable experimental
* support for LOAD/SAVE using a Hobbytronics USB Flash Drive Host
* Board.

FLASH_SUPPORT   EQU     0

*************************************************************************************

* Ver 3.44 adds overflow indication to the USING$() function
* Ver 3.43 removes an undocumented feature of concatenating null strings
* Ver 3.42 reimplements backspace so that characters are overwritten with [SPACE]
* Ver 3.41 removes undocumented features of the USING$() function
* Ver 3.40 adds the USING$() function
* Ver 3.33 adds the file requester to LOAD and SAVE
* Ver 3.32 adds the optional ELSE clause to IF .. THEN

*************************************************************************************
*
* Version 3.25 adds the option to change the behaviour of INPUT so that a null
* response does not cause a program break. If this is the behaviour you want just
* change nobrk to some non zero value.

nobrk		EQU	0				* null response to INPUT causes a break


*************************************************************************************
*
* Version 3.xx replaces the fixed RAM addressing from previous versions with a RAM
* pointer in a3. this means that this could now be run as a task on a multitasking
* system where memory resources may change.


*************************************************************************************

* This lot is in RAM

ram_strt    = $0000
ram_base    = $0400
LAB_WARM    = $0400
Wrmjpv      = $0402
Usrjmp      = $0406
Usrjpv      = $0408
V_INPT      = $040C
V_INPTv     = $040E
V_OUTP      = $0412
V_OUTPv     = $0414
V_LOAD      = $0418
V_LOADv     = $041A
V_SAVE      = $041E
V_SAVEv     = $0420
V_CTLC      = $0424
V_CTLCv     = $0426
Itemp       = $042A
Smeml       = $042E
Sfncl       = $0432
Svarl       = $0436
Sstrl       = $043A
Sarryl      = $043E
Earryl      = $0442
Sstorl      = $0446
Ememl       = $044A
Sutill      = $044E
Clinel      = $0452
Blinel      = $0456
Cpntrl      = $045A
Dlinel      = $045E
Dptrl       = $0462
Rdptrl      = $0466
Varname     = $046A
Cvaral      = $046E
Lvarpl      = $0472
des_sk_e    = $0476
des_sk      = $048E
Ibuffs      = $0490
Ibuffe      = $0590
FAC1_m      = $0590
FAC1_e      = $0594
FAC1_s      = $0595
FAC2_m      = $0598
FAC2_e      = $059C
FAC2_s      = $059D
FAC_sc      = $059E
flag        = $059F
PRNlword    = $05A0
ut1_pl      = $05A4
Asptl       = $05A8
Astrtl      = $05AC
numexp      = $05AC
expcnt      = $05AD
expneg      = $05AF
func_l      = $05B0
Defdim      = $05B4
cosout      = $05B4
Dtypef      = $05B5
Binss       = $05B6
Decss       = $05C6
Usdss       = $05CC
Hexss       = $05CE
BHsend      = $05D6
prstk       = $05D8
tpower      = $05D9
Asrch       = $05DA
Dimcnt      = $05DB
Breakf      = $05DC
Oquote      = $05DD
Gclctd      = $05DE
Sufnxf      = $05DF
Imode       = $05E0
Cflag       = $05E1
TabSiz      = $05E2
comp_f      = $05E3
Nullct      = $05E4
TPos        = $05E5
TWidth      = $05E6
Iclim       = $05E7
ccflag      = $05E8
ccbyte      = $05E9
ccnull      = $05EA
load_first  = $05EB
load_filename  = $05EC
prg_strt    = $05EC

* Use these two lines when running from ROM
ram_addr	EQU	$08800		* RAM start address just above where Tutor usage ends
* ram_size	EQU	$17800		* RAM size
ram_size	EQU	$3FFFF		* RAM size  (256KB RAM)

* Use these two lines when running from RAM
*ram_addr	EQU	$04000		* RAM start address
*ram_size	EQU	$04000		* RAM size
							* RAM offset definitions

ACIA_1   =      SER1        * Console ACIA base address
ACIA_2   =      SER2        * Auxiliary ACIA base address

*************************************************************************************
*
* the following code is simulator specific, change to suit your system

* Output character to the console from register d0.b

VEC_OUT
        MOVEM.L  A0/D1,-(A7)    * Save working registers
        LEA.L    ACIA_1,A0      * A0 points to console ACIA
TXNOTREADY
        MOVE.B   (A0),D1        * Read ACIA status
        BTST     #1,D1          * Test TDRE bit
        BEQ.S    TXNOTREADY     * Until ACIA Tx ready
        MOVE.B   D0,1(A0)       * Write character to send
        MOVEM.L  (A7)+,A0/D1    * Restore working registers
        RTS

* Output character to the second (aux) serial port from register d0.b

 ifne   FLASH_SUPPORT

VEC_OUT2
        MOVEM.L  A0/D1,-(A7)    * Save working registers
        LEA.L    ACIA_2,A0      * A0 points to console ACIA
TXNOTREADY1
        MOVE.B   (A0),D1        * Read ACIA status
        BTST     #1,D1          * Test TDRE bit
        BEQ.s    TXNOTREADY1    * Until ACIA Tx ready
        MOVE.B   D0,1(A0)       * Write character to send
        MOVEM.L  (A7)+,A0/D1    * Restore working registers
        RTS

* Output null terminated string pointed to by A0 to first serial port.

PRINTSTRING1
        MOVEM.L  A0/D0,-(A7)    * Save working registers
LP1     CMP.B    #0,(A0)        * Is it null?
        BEQ      RET1           * If so, return
        MOVE.B   (A0)+,D0       * Get character and advance pointer
        JSR      VEC_OUT        * Output it
        BRA      LP1            * Continue for rest of string

RET1    MOVEM.L  (A7)+,A0/D0    * Restore working registers
        RTS                     * Return

* Output null terminated string pointed to by A0 to second serial port.

PRINTSTRING2
        MOVEM.L  A0/D0,-(A7)    * Save working registers
LP2     CMP.B    #0,(A0)        * Is it null?
        BEQ      RET2           * If so, return
        MOVE.B   (A0)+,D0       * Get character and advance pointer
        JSR      VEC_OUT2       * Output it
        BRA      LP2            * Continue for rest of string

RET2    MOVEM.L  (A7)+,A0/D0    * Restore working registers
        RTS                     * Return

 endc

*************************************************************************************
*
* input a character from the console into register d0
* else return Cb=0 if there's no character available

VEC_IN
        MOVEM.L  A0/D1,-(A7)    * Save working registers
        LEA.L    ACIA_1,A0      * A0 points to console ACIA
        MOVE.B   (A0),D1        * Read ACIA status
        BTST     #0,D1          * Test RDRF bit
        BEQ.S    RXNOTREADY     * Branch if ACIA Rx not ready
        MOVE.B   1(A0),D0       * Read character received
        MOVEM.L  (A7)+,A0/D1    * Restore working registers
        ORI.B    #1,CCR         * Set the carry, flag we got a byte
        RTS                     * Return
RXNOTREADY
        MOVEM.L  (A7)+,A0/D1    * Restore working registers
        ANDI.B   #$FE,CCR       * Clear the carry, flag character not available
        RTS

* Input routine used in LOAD mode to read file from USB flash storage.

 ifne   FLASH_SUPPORT

VEC_IN2
        MOVEM.L  A0/D1,-(A7)    * Save working registers
        LEA.L    VEC_OUT2,A0    * Redirect output to aux. port.
        MOVE.L   A0,V_OUTPv(a3)

* The first time, send READ <filename> 1 1
* Subsequent times, send READ <filename> n 1

        LEA      LAB_READN(pc),A0 * Send READ command string
        BSR      PRINTSTRING2   * Print null terminated string

        LEA      load_filename(A3),A0 * Send filename string
        BSR      PRINTSTRING2   * Print null terminated string

        MOVE.B   #' ',D0       * Send space
        JSR      VEC_OUT2

        CMP.B    #1,load_first(A3) * First time?
        BNE      NOTFIRST1
        MOVE.B   #'1',D0        * Send '1'
        CLR.B    load_first(A3) * Clear first flag
        BRA      SENDCMD1
NOTFIRST1
        MOVE.B   #'n',D0        * Send 'n'
SENDCMD1
        JSR      VEC_OUT2
        MOVE.B   #' ',D0        * Send space
        JSR      VEC_OUT2
        MOVE.B   #'1',D0        * Send '1'
        JSR      VEC_OUT2
        MOVE.B   #$0D,D0        * Send <Return>
        JSR      VEC_OUT2

        LEA.L    VEC_OUT,A0     * Redirect output back to console port.
        MOVE.L   A0,V_OUTPv(a3)

* Read one byte from USB host

        LEA.L    ACIA_2,A0      * A0 points to console ACIA
RXNOTREADY2
        MOVE.B   (A0),D1        * Read ACIA status
        BTST     #0,D1          * Test RDRF bit
        BEQ.S    RXNOTREADY2    * Branch if ACIA Rx not ready
        MOVE.B   1(A0),D0       * Read character received

* Check for end of file character ('~') and if found, redirect
* input back to console port.

        CMP.B    #'~',D0        * End of file marker?
        BNE      NOTEOF
        MOVE.B   #$0D,D0        * Convert '~' to a Return
        LEA.L    VEC_IN,A0      * Redirect input back to console port.
        MOVE.L   A0,V_INPTv(a3)
NOTEOF
        MOVEM.L  (A7)+,A0/D1    * Restore working registers
        ORI.b    #1,CCR         * Set the carry, flag we got a byte
        RTS                     * Return

 endc

*************************************************************************************
*
* LOAD routine for the TS2 computer (not implemented)

 ifeq   FLASH_SUPPORT

VEC_LD
       MOVEQ           #$2E,d7                         * error code $2E "Not implemented" error
       BRA             LAB_XERR                        * do error #d7, then warm start

 endc

* LOAD routine for the TS2 computer. Supports a Hobbytronics USB Flash
* Drive Host Board connected to the auxiliary serial port.

 ifne   FLASH_SUPPORT

VEC_LD  LEA             LAB_FILENAME(PC),A0             * Prompt for filename.
        BSR             PRINTSTRING1                    * Print null terminated string
        MOVE.L          A3,A2                           * Save pointer to RAM variables
GETFN1  JSR             VEC_IN                          * Get character
        BCC             GETFN1                          * Go back if carry clear, indicating no key pressed
        JSR             VEC_OUT                         * Echo the character
        CMP.B           #$0D,D0                         * Was it <Return>?
        BEQ             ENDLN1                          * If so, branch
        CMP.B           #$7F,D0                         * Was it <Delete>?
        BEQ             DELETE1                         * If so, handle delete
        CMP.B           #$08,D0                         * Was it <Backspace?
        BEQ             DELETE1                         * If so, handle as delete
        MOVE.B          D0,load_filename(A2)            * Save in buffer
        ADDQ.L          #1,A2                           * Advance string pointer
        BRA             GETFN1                          * Go back and get next character
DELETE1 SUBQ.L          #1,A2                           * Delete last character entered
        BRA             GETFN1                          * Go back and get next character

ENDLN1  MOVE.B          #0,load_filename(A2)            * Add terminating null to filename
        LEA.L           VEC_IN2,A0                      * Redirect input from aux. port.
        MOVE.L          A0,V_INPTv(a3)
        MOVE.B          #1,load_first(A3)               * Set load_first flag

* Input routine will detect end of file and redirect input back to
* console port.

        RTS

 endc

*************************************************************************************
*
* SAVE routine for the TS2 computer (not implemented)

 ifeq   FLASH_SUPPORT
VEC_SV
       MOVEQ           #$2E,d7                         * error code $2E "Not implemented" error
       BRA             LAB_XERR                        * do error #d7, then warm start
 endc

 ifne   FLASH_SUPPORT

* SAVE routine for the TS2 computer. Supports a Hobbytronics USB Flash
* Drive Host Board connected to the auxiliary serial port.

* TODO: Make configurable at build time

VEC_SV  LEA             LAB_FILENAME(PC),A0             * Prompt for filename.
        BSR             PRINTSTRING1                    * Print null terminated string
        MOVE.L          A3,A2                           * Save pointer to RAM variables
GETFN   JSR             VEC_IN                          * Get character
        BCC             GETFN                           * Go back if carry clear, indicating no key pressed
        JSR             VEC_OUT                         * Echo the character
        CMP.B           #$0D,D0                         * Was it <Return>?
        BEQ             ENDLN                           * If so, branch
        CMP.B           #$7F,D0                         * Was it <Delete>?
        BEQ             DELETE                          * If so, handle delete
        CMP.B           #$08,D0                         * Was it <Backspace?
        BEQ             DELETE                          * If so, handle as delete
        MOVE.B          D0,load_filename(A2)            * Save in buffer
        ADDQ.L          #1,A2                           * Advance string pointer
        BRA             GETFN                           * Go back and get next character
DELETE  SUBQ.L          #1,A2                           * Delete last character entered
        BRA             GETFN                           * Go back and get next character

ENDLN   MOVE.B          #0,load_filename(A2)            * Add terminating null to filename

        LEA.L           VEC_OUT2,A0                     * Redirect output to aux. port.
        MOVE.L          A0,V_OUTPv(a3)

        LEA             LAB_WRITE(pc),A0                * Send WRITE command string
        BSR             PRINTSTRING2                    * Print null terminated string

        LEA             load_filename(A3),A0            * Send filename string
        BSR             PRINTSTRING2                    * Print null terminated string

        MOVE.B          #$0D,D0                         * Send <Return>
        JSR             VEC_OUT2

        MOVE.l          #356000,d0                      * Delay approx. 1 second to allow USB to create file
DELAY   SUBQ.l          #1,d0
        BNE             DELAY

        MOVEQ           #0,d0                           * Tells LIST no arguments
        ANDI.b          #$FE,CCR                        * Clear carry
        BSR             LAB_LIST                        * Call LIST routine

        MOVEQ           #'~',d0                         * Send tilde symbol indicate end of file (used when loading)
        BSR             LAB_PRNA

        MOVEQ           #26,d0                          * Send Control-Z to indicate end of file save operation
        BSR             LAB_PRNA

        LEA.L           VEC_OUT,A0                      * Redirect output back to console port.
        MOVE.L          A0,V_OUTPv(a3)
        RTS                                             * Return

LAB_WRITE
        dc.b            '$WRITE ',$00

LAB_READN
        dc.b            '$READ ',$00

LAB_FILENAME
        dc.b            'Filename? ',$00

 endc
        even

*************************************************************************************

code_start
                                * Set up ACIA parameters
        LEA.L   ACIA_1,A0       * A0 points to console ACIA
        MOVE.B  #$15,(A0)       * Set up ACIA1 constants (no IRQ,
                                * RTS* low, 8 bit, no parity, 1 stop)
        LEA.L   ACIA_2,A0       * A0 points to aux. ACIA
        MOVE.B  #$15,(A0)       * Set up ACIA2 constants (no IRQ,
                                * RTS* low, 8 bit, no parity, 1 stop)

* to tell EhBASIC where and how much RAM it has pass the address in a0 and the size
* in d0. these values are at the end of the .inc file

	MOVEA.l	#ram_addr,a0		* tell BASIC where RAM starts
	MOVE.l	#ram_size,d0		* tell BASIC how big RAM is

* end of simulator specific code


****************************************************************************************
****************************************************************************************
****************************************************************************************
****************************************************************************************
*
* Register use :- (must improve this !!)
*
*	a6 -	temp Bpntr				* temporary BASIC execute pointer
*	a5 -	Bpntr					* BASIC execute (get byte) pointer
*	a4 -	des_sk				        * descriptor stack pointer
*	a3 -	ram_strt				* start of RAM. all RAM references are offsets
*							* from this value
*

*************************************************************************************
*
* BASIC cold start entry point. assume entry with RAM address in a0 and RAM length
* in d0

LAB_COLD
	CMP.l		#$4000,d0			* compare size with 16k
	BGE.s		LAB_sizok			* branch if >= 16k

	MOVEQ		#5,d0				* error 5 - not enough RAM
        move.b          #228,D7                         * Go to TUTOR function
        trap            #14                             * Call TRAP14 handler

LAB_sizok
	MOVEA.l	a0,a3				* copy RAM base to a3
	ADDA.l	d0,a0				* a0 is top of RAM
	MOVE.l	a0,Ememl(a3)		* set end of mem
	LEA		ram_base(a3),sp		* set stack to RAM start + 1k

	MOVE.w	#$4EF9,d0			* JMP opcode
	MOVEA.l	sp,a0				* point to start of vector table

	MOVE.w	d0,(a0)+			* LAB_WARM
	LEA		LAB_COLD(pc),a1		* initial warm start vector
	MOVE.l	a1,(a0)+			* set vector

	MOVE.w	d0,(a0)+			* Usrjmp
	LEA		LAB_FCER(pc),a1		* initial user function vector
							* "Function call" error
	MOVE.l	a1,(a0)+			* set vector

	MOVE.w	d0,(a0)+			* V_INPT JMP opcode
	LEA		VEC_IN(pc),a1		* get byte from input device vector
	MOVE.l	a1,(a0)+			* set vector

	MOVE.w	d0,(a0)+			* V_OUTP JMP opcode
	LEA		VEC_OUT(pc),a1		* send byte to output device vector
	MOVE.l	a1,(a0)+			* set vector

	MOVE.w	d0,(a0)+			* V_LOAD JMP opcode
	LEA		VEC_LD(pc),a1		* load BASIC program vector
	MOVE.l	a1,(a0)+			* set vector

	MOVE.w	d0,(a0)+			* V_SAVE JMP opcode
	LEA		VEC_SV(pc),a1		* save BASIC program vector
	MOVE.l	a1,(a0)+			* set vector

	MOVE.w	d0,(a0)+			* V_CTLC JMP opcode
	LEA		VEC_CC(pc),a1		* save CTRL-C check vector
	MOVE.l	a1,(a0)+			* set vector

* set-up start values

*##LAB_GMEM
	MOVEQ		#$00,d0			* clear d0
	MOVE.b	d0,Nullct(a3)		* default NULL count
	MOVE.b	d0,TPos(a3)			* clear terminal position
	MOVE.b	d0,ccflag(a3)		* allow CTRL-C check
	MOVE.w	d0,prg_strt-2(a3)		* clear start word
	MOVE.w	d0,BHsend(a3)		* clear value to string end word

	MOVE.b	#$50,TWidth(a3)		* default terminal width byte for simulator
	MOVE.b	#$0E,TabSiz(a3)		* save default tab size = 14

	MOVE.b	#$38,Iclim(a3)		* default limit for TAB = 14 for simulator

	LEA		des_sk(a3),a4		* set descriptor stack start

	LEA		prg_strt(a3),a0		* get start of mem
	MOVE.l	a0,Smeml(a3)		* save start of mem

	BSR		LAB_1463			* do "NEW" and "CLEAR"
	BSR		LAB_CRLF			* print CR/LF
	MOVE.l	Ememl(a3),d0		* get end of mem
	SUB.l		Smeml(a3),d0		* subtract start of mem

	BSR		LAB_295E			* print d0 as unsigned integer (bytes free)
	LEA		LAB_SMSG(pc),a0		* point to start message
	BSR		LAB_18C3			* print null terminated string from memory

	LEA		LAB_RSED(pc),a0		* get pointer to value
	BSR		LAB_UFAC			* unpack memory (a0) into FAC1

	LEA		LAB_1274(pc),a0		* get warm start vector
	MOVE.l	a0,Wrmjpv(a3)		* set warm start vector
	BSR		LAB_RND			* initialise
	JMP		LAB_WARM(a3)		* go do warm start


*************************************************************************************
*
* do format error

LAB_FOER
	MOVEQ		#$2C,d7			* error code $2C "Format" error
	BRA.s		LAB_XERR			* do error #d7, then warm start


*************************************************************************************
*
* do address error

LAB_ADER
	MOVEQ		#$2A,d7			* error code $2A "Address" error
	BRA.s		LAB_XERR			* do error #d7, then warm start


*************************************************************************************
*
* do wrong dimensions error

LAB_WDER
	MOVEQ		#$28,d7			* error code $28 "Wrong dimensions" error
	BRA.s		LAB_XERR			* do error #d7, then warm start


*************************************************************************************
*
* do undimensioned array error

LAB_UDER
	MOVEQ		#$26,d7			* error code $26 "undimensioned array" error
	BRA.s		LAB_XERR			* do error #d7, then warm start


*************************************************************************************
*
* do undefined variable error

LAB_UVER

* if you do want a non existant variable to return an error then leave the novar
* value at the top of this file set to zero

 ifeq	novar

	MOVEQ		#$24,d7			* error code $24 "undefined variable" error
	BRA.s		LAB_XERR			* do error #d7, then warm start

 endc

* if you want a non existant variable to return a null value then set the novar
* value at the top of this file to some non zero value

 ifne	novar

	ADD.l		d0,d0				* .......$ .......& ........ .......0
	SWAP		d0				* ........ .......0 .......$ .......&
	ROR.b		#1,d0				* ........ .......0 .......$ &.......
	LSR.w		#1,d0				* ........ .......0 0....... $&.....�.
	AND.b		#$C0,d0			* mask the type bits
	MOVE.b	d0,Dtypef(a3)		* save the data type

	MOVEQ		#0,d0				* clear d0 and set the zero flag
	MOVEA.l	d0,a0				* return a null address
	RTS

 endc


*************************************************************************************
*
* do loop without do error

LAB_LDER
	MOVEQ		#$22,d7			* error code $22 "LOOP without DO" error
	BRA.s		LAB_XERR			* do error #d7, then warm start


*************************************************************************************
*
* do undefined function error

LAB_UFER
	MOVEQ		#$20,d7			* error code $20 "Undefined function" error
	BRA.s		LAB_XERR			* do error #d7, then warm start


*************************************************************************************
*
* do can't continue error

LAB_CCER
	MOVEQ		#$1E,d7			* error code $1E "Can't continue" error
	BRA.s		LAB_XERR			* do error #d7, then warm start


*************************************************************************************
*
* do string too complex error

LAB_SCER
	MOVEQ		#$1C,d7			* error code $1C "String too complex" error
	BRA.s		LAB_XERR			* do error #d7, then warm start


*************************************************************************************
*
* do string too long error

LAB_SLER
	MOVEQ		#$1A,d7			* error code $1A "String too long" error
	BRA.s		LAB_XERR			* do error #d7, then warm start


*************************************************************************************
*
* do type missmatch error

LAB_TMER
	MOVEQ		#$18,d7			* error code $18 "Type mismatch" error
	BRA.s		LAB_XERR			* do error #d7, then warm start


*************************************************************************************
*
* do illegal direct error

LAB_IDER
	MOVEQ		#$16,d7			* error code $16 "Illegal direct" error
	BRA.s		LAB_XERR			* do error #d7, then warm start


*************************************************************************************
*
* do divide by zero error

LAB_DZER
	MOVEQ		#$14,d7			* error code $14 "Divide by zero" error
	BRA.s		LAB_XERR			* do error #d7, then warm start


*************************************************************************************
*
* do double dimension error

LAB_DDER
	MOVEQ		#$12,d7			* error code $12 "Double dimension" error
	BRA.s		LAB_XERR			* do error #d7, then warm start


*************************************************************************************
*
* do array bounds error

LAB_ABER
	MOVEQ		#$10,d7			* error code $10 "Array bounds" error
	BRA.s		LAB_XERR			* do error #d7, then warm start


*************************************************************************************
*
* do undefined satement error

LAB_USER
	MOVEQ		#$0E,d7			* error code $0E "Undefined statement" error
	BRA.s		LAB_XERR			* do error #d7, then warm start


*************************************************************************************
*
* do out of memory error

LAB_OMER
	MOVEQ		#$0C,d7			* error code $0C "Out of memory" error
	BRA.s		LAB_XERR			* do error #d7, then warm start


*************************************************************************************
*
* do overflow error

LAB_OFER
	MOVEQ		#$0A,d7			* error code $0A "Overflow" error
	BRA.s		LAB_XERR			* do error #d7, then warm start


*************************************************************************************
*
* do function call error

LAB_FCER
	MOVEQ		#$08,d7			* error code $08 "Function call" error
	BRA.s		LAB_XERR			* do error #d7, then warm start


*************************************************************************************
*
* do out of data error

LAB_ODER
	MOVEQ		#$06,d7			* error code $06 "Out of DATA" error
	BRA.s		LAB_XERR			* do error #d7, then warm start


*************************************************************************************
*
* do return without gosub error

LAB_RGER
	MOVEQ		#$04,d7			* error code $04 "RETURN without GOSUB" error
	BRA.s		LAB_XERR			* do error #d7, then warm start


*************************************************************************************
*
* do syntax error

LAB_SNER
	MOVEQ		#$02,d7			* error code $02 "Syntax" error
	BRA.s		LAB_XERR			* do error #d7, then warm start


*************************************************************************************
*
* do next without for error

LAB_NFER
	MOVEQ		#$00,d7			* error code $00 "NEXT without FOR" error


*************************************************************************************
*
* do error #d7, then warm start

LAB_XERR
	BSR		LAB_1491			* flush stack & clear continue flag
	BSR		LAB_CRLF			* print CR/LF
	LEA		LAB_BAER(pc),a1		* start of error message pointer table
	MOVE.w	(a1,d7.w),d7		* get error message offset
	LEA		(a1,d7.w),a0		* get error message address
	BSR		LAB_18C3			* print null terminated string from memory
	LEA		LAB_EMSG(pc),a0		* point to " Error" message
LAB_1269
	BSR		LAB_18C3			* print null terminated string from memory
	MOVE.l	Clinel(a3),d0		* get current line
	BMI.s		LAB_1274			* go do warm start if -ve # (was immediate mode)

							* else print line number
	BSR		LAB_2953			* print " in line [LINE #]"

* BASIC warm start entry point, wait for Basic command

LAB_1274
	LEA		LAB_RMSG(pc),a0		* point to "Ready" message
	BSR		LAB_18C3			* go do print string

* wait for Basic command - no "Ready"

LAB_127D
	MOVEQ		#-1,d1			* set to -1
	MOVE.l	d1,Clinel(a3)		* set current line #
	MOVE.b	d1,Breakf(a3)		* set break flag
	LEA		Ibuffs(a3),a5		* set basic execute pointer ready for new line
LAB_127E
	BSR		LAB_1357			* call for BASIC input
	BSR		LAB_GBYT			* scan memory
	BEQ.s		LAB_127E			* loop while null

* got to interpret input line now ....

	BCS.s		LAB_1295			* branch if numeric character, handle new
							* BASIC line

							* no line number so do immediate mode, a5
							* points to the buffer start
	BSR		LAB_13A6			* crunch keywords into Basic tokens
							* crunch from (a5), output to (a0)
							* returns ..
							* d2 is length, d1 trashed, d0 trashed,
							* a1 trashed
	BRA		LAB_15F6			* go scan & interpret code


*************************************************************************************
*
* handle a new BASIC line

LAB_1295
	BSR		LAB_GFPN			* get fixed-point number into temp integer & d1
	BSR		LAB_13A6			* crunch keywords into Basic tokens
							* crunch from (a5), output to (a0)
							* returns .. d2 is length,
							* d1 trashed, d0 trashed, a1 trashed
	MOVE.l	Itemp(a3),d1		* get required line #
	BSR		LAB_SSLN			* search BASIC for d1 line number
							* returns pointer in a0
	BCS.s		LAB_12E6			* branch if not found

							* aroooogah! line # already exists! delete it
	MOVEA.l	(a0),a1			* get start of block (next line pointer)
	MOVE.l	Sfncl(a3),d0		* get end of block (start of functions)
	SUB.l		a1,d0				* subtract start of block ( = bytes to move)
	LSR.l		#1,d0				* /2 (word move)
	SUBQ.l	#1,d0				* adjust for DBF loop
	SWAP		d0				* swap high word to low word
	MOVEA.l	a0,a2				* copy destination
LAB_12AE
	SWAP		d0				* swap high word to low word
LAB_12B0
	MOVE.w	(a1)+,(a2)+			* copy word
	DBF		d0,LAB_12B0			* decrement low count and loop until done

	SWAP		d0				* swap high word to low word
	DBF		d0,LAB_12AE			* decrement high count and loop until done

	MOVE.l	a2,Sfncl(a3)		* start of functions
	MOVE.l	a2,Svarl(a3)		* save start of variables
	MOVE.l	a2,Sstrl(a3)		* start of strings
	MOVE.l	a2,Sarryl(a3)		* save start of arrays
	MOVE.l	a2,Earryl(a3)		* save end of arrays

							* got new line in buffer and no existing same #
LAB_12E6
	MOVE.b	Ibuffs(a3),d0		* get byte from start of input buffer
	BEQ.s		LAB_1325			* if null line go do line chaining

							* got new line and it isn't empty line
	MOVEA.l	Sfncl(a3),a1		* get start of functions (end of block to move)
	LEA		8(a1,d2),a2			* copy it, add line length and add room for
							* pointer and line number

	MOVE.l	a2,Sfncl(a3)		* start of functions
	MOVE.l	a2,Svarl(a3)		* save start of variables
	MOVE.l	a2,Sstrl(a3)		* start of strings
	MOVE.l	a2,Sarryl(a3)		* save start of arrays
	MOVE.l	a2,Earryl(a3)		* save end of arrays
	MOVE.l	Ememl(a3),Sstorl(a3)	* copy end of mem to start of strings, clear
							* strings

	MOVE.l	a1,d1				* copy end of block to move
	SUB.l		a0,d1				* subtract start of block to move
	LSR.l		#1,d1				* /2 (word copy)
	SUBQ.l	#1,d1				* correct for loop end on -1
	SWAP		d1				* swap high word to low word
LAB_12FF
	SWAP		d1				* swap high word to low word
LAB_1301
	MOVE.w	-(a1),-(a2)			* decrement pointers and copy word
	DBF		d1,LAB_1301			* decrement & loop

	SWAP		d1				* swap high word to low word
	DBF		d1,LAB_12FF			* decrement high count and loop until done

* space is opened up, now copy the crunched line from the input buffer into the space

	LEA		Ibuffs(a3),a1		* source is input buffer
	MOVEA.l	a0,a2				* copy destination
	MOVEQ		#-1,d1			* set to allow re-chaining
	MOVE.l	d1,(a2)+			* set next line pointer (allow re-chaining)
	MOVE.l	Itemp(a3),(a2)+		* save line number
	LSR.w		#1,d2				* /2 (word copy)
	SUBQ.w	#1,d2				* correct for loop end on -1
LAB_1303
	MOVE.w	(a1)+,(a2)+			* copy word
	DBF		d2,LAB_1303			* decrement & loop

	BRA.s		LAB_1325			* go test for end of prog

* rebuild chaining of BASIC lines

LAB_132E
	ADDQ.w	#8,a0				* point to first code byte of line, there is
							* always 1 byte + [EOL] as null entries are
							* deleted
LAB_1330
	TST.b		(a0)+				* test byte	
	BNE.s		LAB_1330			* loop if not [EOL]

							* was [EOL] so get next line start
	MOVE.w	a0,d1				* past pad byte(s)
	ANDI.w	#1,d1				* mask odd bit
	ADD.w		d1,a0				* add back to ensure even
	MOVE.l	a0,(a1)			* save next line pointer to current line
LAB_1325
	MOVEA.l	a0,a1				* copy pointer for this line
	TST.l		(a0)				* test pointer to next line
	BNE.s		LAB_132E			* not end of program yet so we must
							* go and fix the pointers

	BSR		LAB_1477			* reset execution to start, clear variables
							* and flush stack
	BRA		LAB_127D			* now we just wait for Basic command, no "Ready"


*************************************************************************************
*
* receive a line from the keyboard
							* character $08 as delete key, BACKSPACE on
							* standard keyboard
LAB_134B
	BSR		LAB_PRNA			* go print the character
	MOVEQ		#' ',d0			* load [SPACE]
	BSR		LAB_PRNA			* go print
	MOVEQ		#$08,d0			* load [BACKSPACE]
	BSR		LAB_PRNA			* go print
	SUBQ.w	#$01,d1			* decrement the buffer index (delete)
	BRA.s		LAB_1359			* re-enter loop

* print "? " and get BASIC input
* return a0 pointing to the buffer start

LAB_INLN
	BSR		LAB_18E3			* print "?" character
	MOVEQ		#' ',d0			* load " "
	BSR		LAB_PRNA			* go print

* call for BASIC input (main entry point)
* return a0 pointing to the buffer start

LAB_1357
	MOVEQ		#$00,d1			* clear buffer index
	LEA		Ibuffs(a3),a0		* set buffer base pointer
LAB_1359
	JSR		V_INPT(a3)			* call scan input device
	BCC.s		LAB_1359			* loop if no byte

	BEQ.s		LAB_1359			* loop if null byte

	CMP.b		#$07,d0			* compare with [BELL]
	BEQ.s		LAB_1378			* branch if [BELL]

	CMP.b		#$0D,d0			* compare with [CR]
	BEQ		LAB_1866			* do CR/LF exit if [CR]

	TST.w		d1				* set flags on buffer index
	BNE.s		LAB_1374			* branch if not empty

* the next two lines ignore any non printing character and [SPACE] if the input buffer
* is empty

	CMP.b		#' ',d0			* compare with [SP]+1
	BLS.s		LAB_1359			* if < ignore character

*##	CMP.b		#' '+1,d0			* compare with [SP]+1
*##	BCS.s		LAB_1359			* if < ignore character

LAB_1374
	CMP.b		#$08,d0			* compare with [BACKSPACE]
	BEQ.s		LAB_134B			* go delete last character

LAB_1378
	CMP.w		#(Ibuffe-Ibuffs-1),d1	* compare character count with max-1
	BCC.s		LAB_138E			* skip store & do [BELL] if buffer full

	MOVE.b	d0,(a0,d1.w)		* else store in buffer
	ADDQ.w	#$01,d1			* increment index
LAB_137F
	BSR		LAB_PRNA			* go print the character
	BRA.s		LAB_1359			* always loop for next character

* announce buffer full

LAB_138E
	MOVEQ		#$07,d0			* [BELL] character into d0
	BRA.s		LAB_137F			* go print the [BELL] but ignore input character


*************************************************************************************
*
* copy a hex value without crunching

LAB_1392
	MOVE.b	d0,(a0,d2.w)		* save the byte to the output
	ADDQ.w	#1,d2				* increment the buffer save index

	ADDQ.w	#1,d1				* increment the buffer read index
	MOVE.b	(a5,d1.w),d0		* get a byte from the input buffer
	BEQ		LAB_13EC			* if [EOL] go save it without crunching

	CMP.b		#' ',d0			* compare the character with " "
	BEQ.s		LAB_1392			* if [SPACE] just go save it and get another

	CMP.b		#'0',d0			* compare the character with "0"
	BCS.s		LAB_13C6			* if < "0" quit the hex save loop

	CMP.b		#'9',d0			* compare with "9"
	BLS.s		LAB_1392			* if it is "0" to "9" save it and get another

	MOVEQ		#-33,d5			* mask xx0x xxxx, ASCII upper case
	AND.b		d0,d5				* mask the character

	CMP.b		#'A',d5			* compare with "A"
	BCS.s		LAB_13CC			* if < "A" quit the hex save loop

	CMP.b		#'F',d5			* compare with "F"
	BLS.s		LAB_1392			* if it is "A" to "F" save it and get another

	BRA.s		LAB_13CC			* else continue crunching

* crunch keywords into Basic tokens
* crunch from (a5), output to (a0)
* returns ..
* d4 trashed
* d3 trashed
* d2 is length
* d1 trashed
* d0 trashed
* a1 trashed

* this is the improved BASIC crunch routine and is 10 to 100 times faster than the
* old list search

LAB_13A6
	MOVEQ		#0,d1				* clear the read index
	MOVE.l	d1,d2				* clear the save index
	MOVE.b	d1,Oquote(a3)		* clear the open quote/DATA flag
LAB_13AC
	MOVEQ		#0,d0				* clear word
	MOVE.b	(a5,d1.w),d0		* get byte from input buffer
	BEQ.s		LAB_13EC			* if null save byte then continue crunching

	CMP.b		#'_',d0			* compare with "_"
	BCC.s		LAB_13EC			* if >= "_" save byte then continue crunching

	CMP.b		#'<',d0			* compare with "<"
	BCC.s		LAB_13CC			* if >= "<" go crunch

	CMP.b		#'0',d0			* compare with "0"
	BCC.s		LAB_13EC			* if >= "0" save byte then continue crunching

	MOVE.b	d0,Asrch(a3)		* save buffer byte as search character
	CMP.b		#$22,d0			* is it quote character?
	BEQ.s		LAB_1410			* branch if so (copy quoted string)

	CMP.b		#'$',d0			* is it the hex value character?
	BEQ.s		LAB_1392			* if so go copy a hex value

LAB_13C6
	CMP.b		#'*',d0			* compare with "*"
	BCS.s		LAB_13EC			* if <= "*" save byte then continue crunching

							* crunch rest
LAB_13CC
	BTST.b	#6,Oquote(a3)		* test open quote/DATA token flag
	BNE.s		LAB_13EC			* branch if b6 of Oquote set (was DATA)
							* go save byte then continue crunching

	SUB.b		#$2A,d0			* normalise byte
	ADD.w		d0,d0				* *2 makes word offset (high byte=$00)
	LEA		TAB_CHRT(pc),a1		* get keyword offset table address
	MOVE.w	(a1,d0.w),d0		* get offset into keyword table
	BMI.s		LAB_141F			* branch if no keywords for character

	LEA		TAB_STAR(pc),a1		* get keyword table address
	ADDA.w	d0,a1				* add keyword offset
	MOVEQ		#-1,d3			* clear index
	MOVE.w	d1,d4				* copy read index
LAB_13D6
	ADDQ.w	#1,d3				* increment table index
	MOVE.b	(a1,d3.w),d0		* get byte from table
LAB_13D8
	BMI.s		LAB_13EA			* branch if token, save token and continue
							* crunching

	ADDQ.w	#1,d4				* increment read index
	CMP.b		(a5,d4.w),d0		* compare byte from input buffer
	BEQ.s		LAB_13D6			* loop if character match

	BRA.s		LAB_1417			* branch if no match

LAB_13EA
	MOVE.w	d4,d1				* update read index
LAB_13EC
	MOVE.b	d0,(a0,d2.w)		* save byte to output
	ADDQ.w	#1,d2				* increment buffer save index
	ADDQ.w	#1,d1				* increment buffer read index
	TST.b		d0				* set flags
	BEQ.s		LAB_142A			* branch if was null [EOL]

							* d0 holds token or byte here
	SUB.b		#$3A,d0			* subtract ":"
	BEQ.s		LAB_13FF			* branch if it was ":" (is now $00)

							* d0 now holds token-$3A
	CMP.b		#(TK_DATA-$3A),d0		* compare with DATA token - $3A
	BNE.s		LAB_1401			* branch if not DATA

							* token was : or DATA
LAB_13FF
	MOVE.b	d0,Oquote(a3)		* save token-$3A ($00 for ":", TK_DATA-$3A for
							* DATA)
LAB_1401
	SUB.b		#(TK_REM-$3A),d0		* subtract REM token offset
	BNE		LAB_13AC			* If wasn't REM then go crunch rest of line

	MOVE.b	d0,Asrch(a3)		* else was REM so set search for [EOL]

							* loop for REM, "..." etc.
LAB_1408
	MOVE.b	(a5,d1.w),d0		* get byte from input buffer
	BEQ.s		LAB_13EC			* branch if null [EOL]

	CMP.b		Asrch(a3),d0		* compare with stored character
	BEQ.s		LAB_13EC			* branch if match (end quote, REM, :, or DATA)

							* entry for copy string in quotes, don't crunch
LAB_1410
	MOVE.b	d0,(a0,d2.w)		* save byte to output
	ADDQ.w	#1,d2				* increment buffer save index
	ADDQ.w	#1,d1				* increment buffer read index
	BRA.s		LAB_1408			* loop

* not found keyword this go so find the end of this word in the table

LAB_1417
	MOVE.w	d1,d4				* reset read pointer
LAB_141B
	ADDQ.w	#1,d3				* increment keyword table pointer, flag
							* unchanged
	MOVE.b	(a1,d3.w),d0		* get keyword table byte
	BPL.s		LAB_141B			* if not end of keyword go do next byte

	ADDQ.w	#1,d3				* increment keyword table pointer flag
							* unchanged
	MOVE.b	(a1,d3.w),d0		* get keyword table byte
	BNE.s		LAB_13D8			* go test next word if not zero byte (table end)

							* reached end of table with no match
LAB_141F
	MOVE.b	(a5,d1.w),d0		* restore byte from input buffer
	BRA.s		LAB_13EC			* go save byte in output and continue crunching

							* reached [EOL]
LAB_142A
	MOVEQ		#0,d0				* ensure longword clear
	BTST		d0,d2				* test odd bit (fastest)
	BEQ.s		LAB_142C			* branch if no bytes to fill

	MOVE.b	d0,(a0,d2.w)		* clear next byte
	ADDQ.w	#1,d2				* increment buffer save index
LAB_142C
	MOVE.l	d0,(a0,d2.w)		* clear next line pointer, EOT in immediate mode
	RTS


*************************************************************************************
*
* search Basic for d1 line number from start of mem

LAB_SSLN
	MOVEA.l	Smeml(a3),a0		* get start of program mem
	BRA.s		LAB_SCLN			* go search for required line from a0

LAB_145F
	MOVEA.l	d0,a0				* copy next line pointer

* search Basic for d1 line number from a0
* returns Cb=0 if found
* returns a0 pointer to found or next higher (not found) line

LAB_SCLN
	MOVE.l	(a0)+,d0			* get next line pointer and point to line #
	BEQ.s		LAB_145E			* is end marker so we're done, do 'no line' exit

	CMP.l		(a0),d1			* compare this line # with required line #
	BGT.s		LAB_145F			* loop if required # > this #

	SUBQ.w	#4,a0				* adjust pointer, flags not changed
	RTS

LAB_145E
	SUBQ.w	#4,a0				* adjust pointer, flags not changed
	SUBQ.l	#1,d0				* make end program found = -1, set carry
	RTS


*************************************************************************************
*
* perform NEW

LAB_NEW
	BNE.s		RTS_005			* exit if not end of statement (do syntax error)

LAB_1463
	MOVEA.l	Smeml(a3),a0		* point to start of program memory
	MOVEQ		#0,d0				* clear longword
	MOVE.l	d0,(a0)+			* clear first line, next line pointer
	MOVE.l	a0,Sfncl(a3)		* set start of functions

* reset execution to start, clear variables and flush stack

LAB_1477
	MOVEA.l	Smeml(a3),a5		* reset BASIC execute pointer
	SUBQ.w	#1,a5				* -1 (as end of previous line)

* "CLEAR" command gets here

LAB_147A
	MOVE.l	Ememl(a3),Sstorl(a3)	* save end of mem as bottom of string space
	MOVE.l	Sfncl(a3),d0		* get start of functions
	MOVE.l	d0,Svarl(a3)		* start of variables
	MOVE.l	d0,Sstrl(a3)		* start of strings
	MOVE.l	d0,Sarryl(a3)		* set start of arrays
	MOVE.l	d0,Earryl(a3)		* set end of arrays
LAB_1480
	MOVEQ		#0,d0				* set Zb
	MOVE.b	d0,ccnull(a3)		* clear get byte countdown
	BSR		LAB_RESTORE			* perform RESTORE command

* flush stack & clear continue flag

LAB_1491
	LEA		des_sk(a3),a4		* reset descriptor stack pointer

	MOVE.l	(sp)+,d0			* pull return address
	LEA		ram_base(a3),sp		* set stack to RAM start + 1k, flush stack
	MOVE.l	d0,-(sp)			* restore return address

	MOVEQ		#0,d0				* clear longword
	MOVE.l	d0,Cpntrl(a3)		* clear continue pointer
	MOVE.b	d0,Sufnxf(a3)		* clear subscript/FNX flag
RTS_005
	RTS


*************************************************************************************
*
* perform CLEAR

LAB_CLEAR
	BEQ.s		LAB_147A			* if no following byte go do "CLEAR"

	RTS						* was following byte (go do syntax error)


*************************************************************************************
*
* perform LIST [n][-m]

LAB_LIST
	BCS.s		LAB_14BD			* branch if next character numeric (LIST n...)

	MOVEQ		#-1,d1			* set end to $FFFFFFFF
	MOVE.l	d1,Itemp(a3)		* save to Itemp

	MOVEQ		#0,d1				* set start to $00000000
	TST.b		d0				* test next byte
	BEQ.s		LAB_14C0			* branch if next character [NULL] (LIST)

	CMP.b		#TK_MINUS,d0		* compare with token for -
	BNE.s		RTS_005			* exit if not - (LIST -m)

							* LIST [[n]-[m]] this sets the n, if present,
							* as the start and end
LAB_14BD
	BSR		LAB_GFPN			* get fixed-point number into temp integer & d1
LAB_14C0
	BSR		LAB_SSLN			* search BASIC for d1 line number
							* (pointer in a0)
	BSR		LAB_GBYT			* scan memory
	BEQ.s		LAB_14D4			* branch if no more characters

							* this bit checks the - is present
	CMP.b		#TK_MINUS,d0		* compare with token for -
	BNE.s		RTS_005			* return if not "-" (will be Syntax error)

	MOVEQ		#-1,d1			* set end to $FFFFFFFF
	MOVE.l	d1,Itemp(a3)		* save Itemp

							* LIST [n]-[m] the - was there so see if
							* there is an m to set as the end value
	BSR		LAB_IGBY			* increment & scan memory
	BEQ.s		LAB_14D4			* branch if was [NULL] (LIST n-)

	BSR		LAB_GFPN			* get fixed-point number into temp integer & d1
LAB_14D4
	MOVE.b	#$00,Oquote(a3)		* clear open quote flag
	BSR		LAB_CRLF			* print CR/LF
	MOVE.l	(a0)+,d0			* get next line pointer
	BEQ.s		RTS_005			* if null all done so exit

	MOVEA.l	d0,a1				* copy next line pointer
	BSR		LAB_1629			* do CRTL-C check vector

	MOVE.l	(a0)+,d0			* get this line #
	CMP.l		Itemp(a3),d0		* compare end line # with this line #
	BHI.s		RTS_005			* if this line greater all done so exit

LAB_14E2
	MOVEM.l	a0-a1,-(sp)			* save registers
	BSR		LAB_295E			* print d0 as unsigned integer
	MOVEM.l	(sp)+,a0-a1			* restore registers
	MOVEQ		#$20,d0			* space is the next character
LAB_150C
	BSR		LAB_PRNA			* go print the character
	CMP.b		#$22,d0			* was it " character
	BNE.s		LAB_1519			* branch if not

							* we're either entering or leaving quotes
	EOR.b		#$FF,Oquote(a3)		* toggle open quote flag
LAB_1519
	MOVE.b	(a0)+,d0			* get byte and increment pointer
	BNE.s		LAB_152E			* branch if not [EOL] (go print)

							* was [EOL]
	MOVEA.l	a1,a0				* copy next line pointer
	MOVE.l	a0,d0				* copy to set flags
	BNE.s		LAB_14D4			* go do next line if not [EOT]

	RTS

LAB_152E
	BPL.s		LAB_150C			* just go print it if not token byte

							* else it was a token byte so maybe uncrunch it
	TST.b		Oquote(a3)			* test the open quote flag
	BMI.s		LAB_150C			* just go print character if open quote set

							* else uncrunch BASIC token
	LEA		LAB_KEYT(pc),a2		* get keyword table address
	MOVEQ		#$7F,d1			* mask into d1
	AND.b		d0,d1				* copy and mask token
	LSL.w		#2,d1				* *4
	LEA		(a2,d1.w),a2		* get keyword entry address
	MOVE.b	(a2)+,d0			* get byte from keyword table
	BSR		LAB_PRNA			* go print the first character
	MOVEQ		#0,d1				* clear d1
	MOVE.b	(a2)+,d1			* get remaining length byte from keyword table
	BMI.s		LAB_1519			* if -ve done so go get next byte

	MOVE.w	(a2),d0			* get offset to rest
	LEA		TAB_STAR(pc),a2		* get keyword table address
	LEA		(a2,d0.w),a2		* get address of rest
LAB_1540
	MOVE.b	(a2)+,d0			* get byte from keyword table
	BSR		LAB_PRNA			* go print the character
	DBF		d1,LAB_1540			* decrement and loop if more to do

	BRA.s		LAB_1519			* go get next byte


*************************************************************************************
*
* perform FOR

LAB_FOR
	BSR		LAB_LET			* go do LET

	MOVE.l	Lvarpl(a3),d0		* get the loop variable pointer
	CMP.l		Sstrl(a3),d0		* compare it with the end of vars memory
	BGE		LAB_TMER			* if greater go do type mismatch error

* test for not less than the start of variables memory if needed
*
*	CMP.l		Svarl(a3),d0		* compare it with the start of variables memory
*	BLT		LAB_TMER			* if not variables memory do type mismatch error

*	MOVEQ		#28,d0			* we need 28 bytes !
*	BSR.s		LAB_1212			* check room on stack for d0 bytes

	BSR		LAB_SNBS			* scan for next BASIC statement ([:] or [EOL])
							* returns a0 as pointer to [:] or [EOL]
	MOVE.l	a0,(sp)			* push onto stack (and dump the return address)
	MOVE.l	Clinel(a3),-(sp)		* push current line onto stack

	MOVEQ		#TK_TO-$100,d0		* set "TO" token
	BSR		LAB_SCCA			* scan for CHR$(d0) else syntax error/warm start
	BSR		LAB_CTNM			* check if source is numeric, else type mismatch
	MOVE.b	Dtypef(a3),-(sp)		* push the FOR variable data type onto stack
	BSR		LAB_EVNM			* evaluate expression and check is numeric else
							* do type mismatch

	MOVE.l	FAC1_m(a3),-(sp)		* push TO value mantissa
	MOVE.w	FAC1_e(a3),-(sp)		* push TO value exponent and sign

	MOVE.l	#$80000000,FAC1_m(a3)	* set default STEP size mantissa
	MOVE.w	#$8100,FAC1_e(a3)		* set default STEP size exponent and sign

	BSR		LAB_GBYT			* scan memory
	CMP.b		#TK_STEP,d0			* compare with STEP token
	BNE.s		LAB_15B3			* jump if not "STEP"

							* was STEP token so ....
	BSR		LAB_IGBY			* increment & scan memory
	BSR		LAB_EVNM			* evaluate expression & check is numeric
							* else do type mismatch
LAB_15B3
	MOVE.l	FAC1_m(a3),-(sp)		* push STEP value mantissa
	MOVE.w	FAC1_e(a3),-(sp)		* push STEP value exponent and sign

	MOVE.l	Lvarpl(a3),-(sp)		* push variable pointer for FOR/NEXT
	MOVE.w	#TK_FOR,-(sp)		* push FOR token on stack

	BRA.s		LAB_15C2			* go do interpreter inner loop

LAB_15DC						* have reached [EOL]+1
	MOVE.w	a5,d0				* copy BASIC execute pointer
	AND.w		#1,d0				* and make line start address even
	ADD.w		d0,a5				* add to BASIC execute pointer
	MOVE.l	(a5)+,d0			* get next line pointer
	BEQ		LAB_1274			* if null go to immediate mode, no "BREAK"
							* message (was immediate or [EOT] marker)

	MOVE.l	(a5)+,Clinel(a3)		* save (new) current line #
LAB_15F6
	BSR		LAB_GBYT			* get BASIC byte
	BSR.s		LAB_15FF			* go interpret BASIC code from (a5)

* interpreter inner loop (re)entry point

LAB_15C2
	BSR.s		LAB_1629			* do CRTL-C check vector
	TST.b		Clinel(a3)			* test current line #, is -ve for immediate mode
	BMI.s		LAB_15D1			* branch if immediate mode

	MOVE.l	a5,Cpntrl(a3)		* save BASIC execute pointer as continue pointer
LAB_15D1
	MOVE.b	(a5)+,d0			* get this byte & increment pointer
	BEQ.s		LAB_15DC			* loop if [EOL]

	CMP.b		#$3A,d0			* compare with ":"
	BEQ.s		LAB_15F6			* loop if was statement separator

	BRA		LAB_SNER			* else syntax error, then warm start


*************************************************************************************
*
* interpret BASIC code from (a5)

LAB_15FF
	BEQ		RTS_006			* exit if zero [EOL]

LAB_1602
	EORI.b	#$80,d0			* normalise token
	BMI		LAB_LET			* if not token, go do implied LET

	CMP.b		#(TK_TAB-$80),d0		* compare normalised token with TAB
	BCC		LAB_SNER			* branch if d0>=TAB, syntax error/warm start
							* only tokens before TAB can start a statement

	EXT.w		d0				* byte to word (clear high byte)
	ADD.w		d0,d0				* *2
	LEA		LAB_CTBL(pc),a0		* get vector table base address
	MOVE.w	(a0,d0.w),d0		* get offset to vector
	PEA		(a0,d0.w)			* push vector
	BRA		LAB_IGBY			* get following byte & execute vector


*************************************************************************************
*
* CTRL-C check jump. this is called as a subroutine but exits back via a jump if a
* key press is detected.

LAB_1629
	JMP		V_CTLC(a3)			* ctrl c check vector

* if there was a key press it gets back here .....

LAB_1636
	CMP.b		#$03,d0			* compare with CTRL-C
	BEQ.s		LAB_163B			* STOP if was CTRL-C

LAB_1639
	RTS						*


*************************************************************************************
*
* perform END

LAB_END
	BNE.s		LAB_1639			* exit if something follows STOP
	MOVE.b	#0,Breakf(a3)		* clear break flag, indicate program end


*************************************************************************************
*
* perform STOP

LAB_STOP
	BNE.s		LAB_1639			* exit if something follows STOP

LAB_163B
	LEA		Ibuffe(a3),a1		* get buffer end
	CMPA.l	a1,a5				* compare execute address with buffer end
	BCS.s		LAB_164F			* branch if BASIC pointer is in buffer
							* can't continue in immediate mode

							* else...
	MOVE.l	a5,Cpntrl(a3)		* save BASIC execute pointer as continue pointer
LAB_1647
	MOVE.l	Clinel(a3),Blinel(a3)	* save break line
LAB_164F
	ADDQ.w	#4,sp				* dump return address, don't return to execute
							* loop
	MOVE.b	Breakf(a3),d0		* get break flag
	BEQ		LAB_1274			* go do warm start if was program end

	LEA		LAB_BMSG(pc),a0		* point to "Break"
	BRA		LAB_1269			* print "Break" and do warm start


*************************************************************************************
*
* perform RESTORE

LAB_RESTORE
	MOVEA.l	Smeml(a3),a0		* copy start of memory
	BEQ.s		LAB_1624			* branch if next character null (RESTORE)

	BSR		LAB_GFPN			* get fixed-point number into temp integer & d1
	CMP.l		Clinel(a3),d1		* compare current line # with required line #
	BLS.s		LAB_GSCH			* branch if >= (start search from beginning)

	MOVEA.l	a5,a0				* copy BASIC execute pointer
LAB_RESs
	TST.b		(a0)+				* test next byte & increment pointer
	BNE.s		LAB_RESs			* loop if not EOL

	MOVE.w	a0,d0				* copy pointer
	AND.w		#1,d0				* mask odd bit
	ADD.w		d0,a0				* add pointer
							* search for line in Itemp from (a0)
LAB_GSCH
	BSR		LAB_SCLN			* search for d1 line number from a0
							* returns Cb=0 if found
	BCS		LAB_USER			* go do "Undefined statement" error if not found

LAB_1624
	TST.b		-(a0)				* decrement pointer (faster)
	MOVE.l	a0,Dptrl(a3)		* save DATA pointer
RTS_006
	RTS


*************************************************************************************
*
* perform NULL

LAB_NULL
	BSR		LAB_GTBY			* get byte parameter, result in d0 and Itemp
	MOVE.b	d0,Nullct(a3)		* save new NULL count
	RTS


*************************************************************************************
*
* perform CONT

LAB_CONT
	BNE		LAB_SNER			* if following byte exit to do syntax error

	TST.b		Clinel(a3)			* test current line #, is -ve for immediate mode
	BPL		LAB_CCER			* if running go do can't continue error

	MOVE.l	Cpntrl(a3),d0		* get continue pointer
	BEQ		LAB_CCER			* go do can't continue error if we can't

							* we can continue so ...
	MOVEA.l	d0,a5				* save continue pointer as BASIC execute pointer
	MOVE.l	Blinel(a3),Clinel(a3)	* set break line as current line
	RTS


*************************************************************************************
*
* perform RUN

LAB_RUN
	BNE.s		LAB_RUNn			* if following byte do RUN n

	BSR		LAB_1477			* execution to start, clear vars & flush stack
	MOVE.l	a5,Cpntrl(a3)		* save as continue pointer
	BRA		LAB_15C2			* go do interpreter inner loop
							* (can't RTS, we flushed the stack!)

LAB_RUNn
	BSR		LAB_147A			* go do "CLEAR"
	BRA.s		LAB_16B0			* get n and do GOTO n


*************************************************************************************
*
* perform DO

LAB_DO
*	MOVE.l	#$05,d0			* need 5 bytes for DO
*	BSR.s		LAB_1212			* check room on stack for A bytes
	MOVE.l	a5,-(sp)			* push BASIC execute pointer on stack
	MOVE.l	Clinel(a3),-(sp)		* push current line on stack
	MOVE.w	#TK_DO,-(sp)		* push token for DO on stack
	PEA		LAB_15C2(pc)		* set return address
	BRA		LAB_GBYT			* scan memory & return to interpreter inner loop


*************************************************************************************
*
* perform GOSUB

LAB_GOSUB
*	MOVE.l	#10,d0			* need 10 bytes for GOSUB
*	BSR.s		LAB_1212			* check room on stack for d0 bytes
	MOVE.l	a5,-(sp)			* push BASIC execute pointer
	MOVE.l	Clinel(a3),-(sp)		* push current line
	MOVE.w	#TK_GOSUB,-(sp)		* push token for GOSUB
LAB_16B0
	BSR		LAB_GBYT			* scan memory
	PEA		LAB_15C2(pc)		* return to interpreter inner loop after GOTO n

* this PEA is needed because either we just cleared the stack and have nowhere to return
* to or, in the case of GOSUB, we have just dropped a load on the stack and the address
* we whould have returned to is buried. This burried return address will be unstacked by
* the corresponding RETURN command


*************************************************************************************
*
* perform GOTO

LAB_GOTO
	BSR		LAB_GFPN			* get fixed-point number into temp integer & d1
	MOVEA.l	Smeml(a3),a0		* get start of memory
	CMP.l		Clinel(a3),d1		* compare current line with wanted #
	BLS.s		LAB_16D0			* branch if current # => wanted #

	MOVEA.l	a5,a0				* copy BASIC execute pointer
LAB_GOTs
	TST.b		(a0)+				* test next byte & increment pointer
	BNE.s		LAB_GOTs			* loop if not EOL

	MOVE.w	a0,d0				* past pad byte(s)
	AND.w		#1,d0				* mask odd bit
	ADD.w		d0,a0				* add to pointer

LAB_16D0
	BSR		LAB_SCLN			* search for d1 line number from a0
							* returns Cb=0 if found
	BCS		LAB_USER			* if carry set go do "Undefined statement" error

	MOVEA.l	a0,a5				* copy to basic execute pointer
	SUBQ.w	#1,a5				* decrement pointer
	MOVE.l	a5,Cpntrl(a3)		* save as continue pointer
	RTS


*************************************************************************************
*
* perform LOOP

LAB_LOOP
	CMP.w		#TK_DO,4(sp)		* compare token on stack with DO token
	BNE		LAB_LDER			* branch if no matching DO

	MOVE.b	d0,d7				* copy following token (byte)
	BEQ.s		LoopAlways			* if no following token loop forever

	CMP.b		#':',d7			* compare with ":"
	BEQ.s		LoopAlways			* if no following token loop forever

	SUB.b		#TK_UNTIL,d7		* subtract token for UNTIL
	BEQ.s		DoRest			* branch if was UNTIL

	SUBQ.b	#1,d7				* decrement result
	BNE		LAB_SNER			* if not WHILE go do syntax error & warm start
							* only if the token was WHILE will this fail

	MOVEQ		#-1,d7			* set invert result longword
DoRest
	BSR		LAB_IGBY			* increment & scan memory
	BSR		LAB_EVEX			* evaluate expression
	TST.b		FAC1_e(a3)			* test FAC1 exponent
	BEQ.s		DoCmp				* if = 0 go do straight compare

	MOVE.b	#$FF,FAC1_e(a3)		* else set all bits
DoCmp
	EOR.b		d7,FAC1_e(a3)		* EOR with invert byte
	BNE.s		LoopDone			* if <> 0 clear stack & back to interpreter loop

							* loop condition wasn't met so do it again
LoopAlways
	MOVE.l	6(sp),Clinel(a3)		* copy DO current line
	MOVE.l	10(sp),a5			* save BASIC execute pointer

	LEA		LAB_15C2(pc),a0		* get return address
	MOVE.l	a0,(sp)			* dump the call to this routine and set the
							* return address
	BRA		LAB_GBYT			* scan memory and return to interpreter inner
							* loop

							* clear stack & back to interpreter loop
LoopDone
	LEA		14(sp),sp			* dump structure and call from stack
	BRA.s		LAB_DATA			* go perform DATA (find : or [EOL])


*************************************************************************************
*
* perform RETURN

LAB_RETURN
	BNE.s		RTS_007			* exit if following token to allow syntax error

	CMP.w		#TK_GOSUB,4(sp)		* compare token from stack with GOSUB
	BNE		LAB_RGER			* do RETURN without GOSUB error if no matching
							* GOSUB

	ADDQ.w	#6,sp				* dump calling address & token
	MOVE.l	(sp)+,Clinel(a3)		* pull current line
	MOVE.l	(sp)+,a5			* pull BASIC execute pointer
							* now do perform "DATA" statement as we could be
							* returning into the middle of an ON <var> GOSUB
							* n,m,p,q line (the return address used by the
							* DATA statement is the one pushed before the
							* GOSUB was executed!)


*************************************************************************************
*
* perform DATA

LAB_DATA
	BSR.s		LAB_SNBS			* scan for next BASIC statement ([:] or [EOL])
							* returns a0 as pointer to [:] or [EOL]
	MOVEA.l	a0,a5				* skip rest of statement
RTS_007
	RTS


*************************************************************************************
*
* scan for next BASIC statement ([:] or [EOL])
* returns a0 as pointer to [:] or [EOL]

LAB_SNBS
	MOVEA.l	a5,a0				* copy BASIC execute pointer
	MOVEQ		#$22,d1			* set string quote character
	MOVEQ		#$3A,d2			* set look for character = ":"
	BRA.s		LAB_172D			* go do search

LAB_172C
	CMP.b		d0,d2				* compare with ":"
	BEQ.s		RTS_007a			* exit if found

	CMP.b		d0,d1				* compare with '"'
	BEQ.s		LAB_1725			* if found go search for [EOL]

LAB_172D
	MOVE.b	(a0)+,d0			* get next byte
	BNE.s		LAB_172C			* loop if not null [EOL]

RTS_007a
	SUBQ.w	#1,a0				* correct pointer
	RTS

LAB_1723
	CMP.b		d0,d1				* compare with '"'
	BEQ.s		LAB_172D			* if found go search for ":" or [EOL]

LAB_1725
	MOVE.b	(a0)+,d0			* get next byte
	BNE.s		LAB_1723			* loop if not null [EOL]

	BRA.s		RTS_007a			* correct pointer & return


*************************************************************************************
*
* perform IF

LAB_IF
	BSR		LAB_EVEX			* evaluate expression
	BSR		LAB_GBYT			* scan memory
	CMP.b		#TK_THEN,d0			* compare with THEN token
	BEQ.s		LAB_174B			* if it was THEN then continue

							* wasn't IF .. THEN so must be IF .. GOTO
	CMP.b		#TK_GOTO,d0			* compare with GOTO token
	BNE		LAB_SNER			* if not GOTO token do syntax error/warm start

							* was GOTO so check for GOTO <n>
	MOVE.l	a5,a0				* save the execute pointer
	BSR		LAB_IGBY			* scan memory, test for a numeric character
	MOVE.l	a0,a5				* restore the execute pointer
	BCC		LAB_SNER			* if not numeric do syntax error/warm start

LAB_174B
	MOVE.b	FAC1_e(a3),d0		* get FAC1 exponent
	BEQ.s		LAB_174E			* if result was zero go look for an ELSE

	BSR		LAB_IGBY			* increment & scan memory
	BCS		LAB_GOTO			* if numeric do GOTO n
							* a GOTO <n> will never return to the IF
							* statement so there is no need to return
							* to this code

	CMP.b		#TK_RETURN,d0		* compare with RETURN token
	BEQ		LAB_1602			* if RETURN then interpret BASIC code from (a5)
							* and don't return here

	BSR		LAB_15FF			* else interpret BASIC code from (a5)

* the IF was executed and there may be a following ELSE so the code needs to return
* here to check and ignore the ELSE if present

	MOVE.b	(a5),d0			* get the next basic byte
	CMP.b		#TK_ELSE,d0			* compare it with the token for ELSE
	BEQ		LAB_DATA			* if ELSE ignore the following statement

* there was no ELSE so continue execution of IF <expr> THEN <stat> [: <stat>]. any
* following ELSE will, correctly, cause a syntax error

	RTS						* else return to interpreter inner loop

* perform ELSE after IF

LAB_174E
	MOVE.b	(a5)+,d0			* faster increment past THEN
	MOVEQ		#-87,d3			* set search for ELSE token
	MOVEQ		#-117,d4			* set search for IF token
	MOVEQ		#0,d5				* clear the nesting depth
LAB_1750
	MOVE.b	(a5)+,d0			* get next BASIC byte & increment ptr
	BEQ.s		LAB_1754			* if EOL correct the pointer and return

	CMP.b		d4,d0				* compare with "IF" token
	BNE.s		LAB_1752			* skip if not nested IF

	ADDQ.w	#1,d5				* else increment the nesting depth ..
	BRA.s		LAB_1750			* .. and continue looking

LAB_1752
	CMP.b		d3,d0				* compare with ELSE token
	BNE.s		LAB_1750			* if not ELSE continue looking

LAB_1756
	DBF		d5,LAB_1750			* loop if still nested

* found the matching ELSE, now do <{n|statement}>

	BSR		LAB_GBYT			* scan memory
	BCS		LAB_GOTO			* if numeric do GOTO n
							* code will return to the interpreter loop
							* at the tail end of the GOTO <n>

	BRA		LAB_15FF			* else interpret BASIC code from (a5)
							* code will return to the interpreter loop
							* at the tail end of the <statement>


*************************************************************************************
*
* perform REM, skip (rest of) line

LAB_REM
	TST.b		(a5)+				* test byte & increment pointer
	BNE.s		LAB_REM			* loop if not EOL

LAB_1754
	SUBQ.w	#1,a5				* correct the execute pointer
	RTS


*************************************************************************************
*
* perform ON

LAB_ON
	BSR		LAB_GTBY			* get byte parameter, result in d0 and Itemp
	MOVE.b	d0,d2				* copy byte
	BSR		LAB_GBYT			* restore BASIC byte
	MOVE.w	d0,-(sp)			* push GOTO/GOSUB token
	CMP.b		#TK_GOSUB,d0		* compare with GOSUB token
	BEQ.s		LAB_176C			* branch if GOSUB

	CMP.b		#TK_GOTO,d0			* compare with GOTO token
	BNE		LAB_SNER			* if not GOTO do syntax error, then warm start

* next character was GOTO or GOSUB

LAB_176C
	SUBQ.b	#1,d2				* decrement index (byte value)
	BNE.s		LAB_1773			* branch if not zero

	MOVE.w	(sp)+,d0			* pull GOTO/GOSUB token
	BRA		LAB_1602			* go execute it

LAB_1773
	BSR		LAB_IGBY			* increment & scan memory
	BSR.s		LAB_GFPN			* get fixed-point number into temp integer & d1
							* (skip this n)
	CMP.b		#$2C,d0			* compare next character with ","
	BEQ.s		LAB_176C			* loop if ","

	MOVE.w	(sp)+,d0			* pull GOTO/GOSUB token (run out of options)
	RTS						* and exit


*************************************************************************************
*
* get fixed-point number into temp integer & d1
* interpret number from (a5), leave (a5) pointing to byte after #

LAB_GFPN
	MOVEQ		#$00,d1			* clear integer register
	MOVE.l	d1,d0				* clear d0
	BSR		LAB_GBYT			* scan memory, Cb=1 if "0"-"9", & get byte
	BCC.s		LAB_1786			* return if carry clear, chr was not "0"-"9"

	MOVE.l	d2,-(sp)			* save d2
LAB_1785
	MOVE.l	d1,d2				* copy integer register
	ADD.l		d1,d1				* *2
	BCS		LAB_SNER			* if overflow do syntax error, then warm start

	ADD.l		d1,d1				* *4
	BCS		LAB_SNER			* if overflow do syntax error, then warm start

	ADD.l		d2,d1				* *1 + *4
	BCS		LAB_SNER			* if overflow do syntax error, then warm start

	ADD.l		d1,d1				* *10
	BCS		LAB_SNER			* if overflow do syntax error, then warm start

	SUB.b		#$30,d0			* subtract $30 from byte
	ADD.l		d0,d1				* add to integer register, the top 24 bits are
							* always clear
	BVS		LAB_SNER			* if overflow do syntax error, then warm start
							* this makes the maximum line number 2147483647
	BSR		LAB_IGBY			* increment & scan memory
	BCS.s		LAB_1785			* loop for next character if "0"-"9"

	MOVE.l	(sp)+,d2			* restore d2
LAB_1786
	MOVE.l	d1,Itemp(a3)		* save Itemp
	RTS


*************************************************************************************
*
* perform DEC

LAB_DEC
	MOVE.w	#$8180,-(sp)		* set -1 sign/exponent
	BRA.s		LAB_17B7			* go do DEC


*************************************************************************************
*
* perform INC

LAB_INC
	MOVE.w	#$8100,-(sp)		* set 1 sign/exponent
	BRA.s		LAB_17B7			* go do INC

							* was "," so another INCR variable to do
LAB_17B8
	BSR		LAB_IGBY			* increment and scan memory
LAB_17B7
	BSR		LAB_GVAR			* get variable address in a0

* if you want a non existant variable to return a null value then set the novar
* value at the top of this file to some non zero value

 ifne	novar

	BEQ.s		LAB_INCT			* if variable not found skip the inc/dec

 endc

	TST.b		Dtypef(a3)			* test data type, $80=string, $40=integer,
							* $00=float
	BMI		LAB_TMER			* if string do "Type mismatch" error/warm start

	BNE.s		LAB_INCI			* go do integer INC/DEC

	MOVE.l	a0,Lvarpl(a3)		* save var address
	BSR		LAB_UFAC			* unpack memory (a0) into FAC1
	MOVE.l	#$80000000,FAC2_m(a3)	* set FAC2 mantissa for 1
	MOVE.w	(sp),d0			* move exponent & sign to d0
	MOVE.w	d0,FAC2_e(a3)		* move exponent & sign to FAC2
	MOVE.b	FAC1_s(a3),FAC_sc(a3)	* make sign compare = FAC1 sign
	EOR.b		d0,FAC_sc(a3)		* make sign compare (FAC1_s EOR FAC2_s)
	BSR		LAB_ADD			* add FAC2 to FAC1
	BSR		LAB_PFAC			* pack FAC1 into variable (Lvarpl)
LAB_INCT
	BSR		LAB_GBYT			* scan memory
	CMPI.b	#$2C,d0			* compare with ","
	BEQ.s		LAB_17B8			* continue if "," (another variable to do)

	ADDQ.w	#2,sp				* else dump sign & exponent
	RTS

LAB_INCI
	TST.b		1(sp)				* test sign
	BNE.s		LAB_DECI			* branch if DEC

	ADDQ.l	#1,(a0)			* increment variable
	BRA.s		LAB_INCT			* go scan for more

LAB_DECI
	SUBQ.l	#1,(a0)			* decrement variable
	BRA.s		LAB_INCT			* go scan for more


*************************************************************************************
*
* perform LET

LAB_LET
	BSR		LAB_SVAR			* search for or create a variable
							* return the variable address in a0
	MOVE.l	a0,Lvarpl(a3)		* save variable address
	MOVE.b	Dtypef(a3),-(sp)		* push var data type, $80=string, $40=integer,
							* $00=float
	MOVEQ		#TK_EQUAL-$100,d0		* get = token
	BSR		LAB_SCCA			* scan for CHR$(d0), else do syntax error/warm
							* start
	BSR		LAB_EVEX			* evaluate expression
	MOVE.b	Dtypef(a3),d0		* copy expression data type
	MOVE.b	(sp)+,Dtypef(a3)		* pop variable data type
	ROL.b		#1,d0				* set carry if expression type = string
	BSR		LAB_CKTM			* type match check, set C for string
	BEQ		LAB_PFAC			* if number pack FAC1 into variable Lvarpl & RET

* string LET

LAB_17D5
	MOVEA.l	Lvarpl(a3),a2		* get pointer to variable
LAB_17D6
	MOVEA.l	FAC1_m(a3),a0		* get descriptor pointer
	MOVEA.l	(a0),a1			* get string pointer
	CMP.l		Sstorl(a3),a1		* compare string memory start with string
							* pointer
	BCS.s		LAB_1811			* if it was in program memory assign the value
							* and exit

	CMPA.l	Sfncl(a3),a0		* compare functions start with descriptor
							* pointer
	BCS.s		LAB_1811			* branch if >= (string is on stack)

							* string is variable$ make space and copy string
LAB_1810
	MOVEQ		#0,d1				* clear length
	MOVE.w	4(a0),d1			* get string length
	MOVEA.l	(a0),a0			* get string pointer
	BSR		LAB_20C9			* copy string
	MOVEA.l	FAC1_m(a3),a0		* get descriptor pointer back
							* clean stack & assign value to string variable
LAB_1811
	CMPA.l	a0,a4				* is string on the descriptor stack
	BNE.s		LAB_1813			* skip pop if not

	ADDQ.w	#$06,a4			* else update stack pointer
LAB_1813
	MOVE.l	(a0)+,(a2)+			* save pointer to variable
	MOVE.w	(a0),(a2)			* save length to variable
RTS_008
	RTS


*************************************************************************************
*
* perform GET

LAB_GET
	BSR		LAB_SVAR			* search for or create a variable
							* return the variable address in a0
	MOVE.l	a0,Lvarpl(a3)		* save variable address as GET variable
	TST.b		Dtypef(a3)			* test data type, $80=string, $40=integer,
							* $00=float
	BMI.s		LAB_GETS			* go get string character

							* was numeric get
	BSR		INGET				* get input byte
	BSR		LAB_1FD0			* convert d0 to unsigned byte in FAC1
	BRA		LAB_PFAC			* pack FAC1 into variable (Lvarpl) & return

LAB_GETS
	MOVEQ		#$00,d1			* assume no byte
	MOVE.l	d1,a0				* assume null string
	BSR		INGET				* get input byte
	BCC.s		LAB_NoSt			* branch if no byte received

	MOVEQ		#$01,d1			* string is single byte
	BSR		LAB_2115			* make string space d1 bytes long
							* return a0 = pointer, other registers unchanged

	MOVE.b	d0,(a0)			* save byte in string (byte IS string!)
LAB_NoSt
	BSR		LAB_RTST			* push string on descriptor stack
							* a0 = pointer, d1 = length

	BRA.s		LAB_17D5			* do string LET & return


*************************************************************************************
*
* PRINT

LAB_1829
	BSR		LAB_18C6			* print string from stack
LAB_182C
	BSR		LAB_GBYT			* scan memory

* perform PRINT

LAB_PRINT
	BEQ.s		LAB_CRLF			* if nothing following just print CR/LF

LAB_1831
	CMP.b		#TK_TAB,d0			* compare with TAB( token
	BEQ.s		LAB_18A2			* go do TAB/SPC

	CMP.b		#TK_SPC,d0			* compare with SPC( token
	BEQ.s		LAB_18A2			* go do TAB/SPC

	CMP.b		#',',d0			* compare with ","
	BEQ.s		LAB_188B			* go do move to next TAB mark

	CMP.b		#';',d0			* compare with ";"
	BEQ		LAB_18BD			* if ";" continue with PRINT processing

	BSR		LAB_EVEX			* evaluate expression
	TST.b		Dtypef(a3)			* test data type, $80=string, $40=integer,
							* $00=float
	BMI.s		LAB_1829			* branch if string

** replace the two lines above with this code

**	MOVE.b	Dtypef(a3),d0		* get data type flag, $80=string, $00=numeric
**	BMI.s		LAB_1829			* branch if string

	BSR		LAB_2970			* convert FAC1 to string
	BSR		LAB_20AE			* print " terminated string to FAC1 stack

* don't check fit if terminal width byte is zero

	MOVEQ		#0,d0				* clear d0
	MOVE.b	TWidth(a3),d0		* get terminal width byte
	BEQ.s		LAB_185E			* skip check if zero

	SUB.b		7(a4),d0			* subtract string length
	SUB.b		TPos(a3),d0			* subtract terminal position
	BCC.s		LAB_185E			* branch if less than terminal width

	BSR.s		LAB_CRLF			* else print CR/LF
LAB_185E
	BSR.s		LAB_18C6			* print string from stack
	BRA.s		LAB_182C			* always go continue processing line


*************************************************************************************
*
* CR/LF return to BASIC from BASIC input handler
* leaves a0 pointing to the buffer start

LAB_1866
	MOVE.b	#$00,(a0,d1.w)		* null terminate input

* print CR/LF

LAB_CRLF
	MOVEQ		#$0D,d0			* load [CR]
	BSR.s		LAB_PRNA			* go print the character
	MOVEQ		#$0A,d0			* load [LF]
	BRA.s		LAB_PRNA			* go print the character & return

LAB_188B
	MOVE.b	TPos(a3),d2			* get terminal position
	CMP.b		Iclim(a3),d2		* compare with input column limit
	BCS.s		LAB_1898			* branch if less than Iclim

	BSR.s		LAB_CRLF			* else print CR/LF (next line)
	BRA.s		LAB_18BD			* continue with PRINT processing

LAB_1898
	SUB.b		TabSiz(a3),d2		* subtract TAB size
	BCC.s		LAB_1898			* loop if result was >= 0

	NEG.b		d2				* twos complement it
	BRA.s		LAB_18B7			* print d2 spaces

							* do TAB/SPC
LAB_18A2
	MOVE.w	d0,-(sp)			* save token
	BSR		LAB_SGBY			* increment and get byte, result in d0 and Itemp
	MOVE.w	d0,d2				* copy byte
	BSR		LAB_GBYT			* get basic byte back
	CMP.b		#$29,d0			* is next character ")"
	BNE		LAB_SNER			* if not do syntax error, then warm start

	MOVE.w	(sp)+,d0			* get token back
	CMP.b		#TK_TAB,d0			* was it TAB ?
	BNE.s		LAB_18B7			* branch if not (was SPC)

							* calculate TAB offset
	SUB.b		TPos(a3),d2			* subtract terminal position
	BLS.s		LAB_18BD			* branch if result was <= 0
							* can't TAB backwards or already there

							* print d2.b spaces
LAB_18B7
	MOVEQ		#0,d0				* clear longword
	SUBQ.b	#1,d0				* make d0 = $FF
	AND.l		d0,d2				* mask for byte only
	BEQ.s		LAB_18BD			* branch if zero

	MOVEQ		#$20,d0			* load " "
	SUBQ.b	#1,d2				* adjust for DBF loop
LAB_18B8
	BSR.s		LAB_PRNA			* go print
	DBF		d2,LAB_18B8			* decrement count and loop if not all done

							* continue with PRINT processing
LAB_18BD
	BSR		LAB_IGBY			* increment & scan memory
	BNE		LAB_1831			* if byte continue executing PRINT

	RTS						* exit if nothing more to print


*************************************************************************************
*
* print null terminated string from a0

LAB_18C3
	BSR		LAB_20AE			* print terminated string to FAC1/stack

* print string from stack

LAB_18C6
	BSR		LAB_22B6			* pop string off descriptor stack or from memory
							* returns with d0 = length, a0 = pointer
	BEQ.s		RTS_009			* exit (RTS) if null string

	MOVE.w	d0,d1				* copy length & set Z flag
	SUBQ.w	#1,d1				* -1 for BF loop
LAB_18CD
	MOVE.b	(a0)+,d0			* get byte from string
	BSR.s		LAB_PRNA			* go print the character
	DBF		d1,LAB_18CD			* decrement count and loop if not done yet

RTS_009
	RTS


*************************************************************************************
*
* print "?" character

LAB_18E3
	MOVEQ		#$3F,d0			* load "?" character


*************************************************************************************
*
* print character in d0, includes the null handler and infinite line length code
* changes no registers

LAB_PRNA
	MOVE.l	d1,-(sp)			* save d1
	CMP.b		#$20,d0			* compare with " "
	BCS.s		LAB_18F9			* branch if less, non printing character

							* don't check fit if terminal width byte is zero
	MOVE.b	TWidth(a3),d1		* get terminal width
	BNE.s		LAB_18F0			* branch if not zero (not infinite length)

							* is "infinite line" so check TAB position
	MOVE.b	TPos(a3),d1			* get position
	SUB.b		TabSiz(a3),d1		* subtract TAB size
	BNE.s		LAB_18F7			* skip reset if different

	MOVE.b	d1,TPos(a3)			* else reset position
	BRA.s		LAB_18F7			* go print character

LAB_18F0
	CMP.b		TPos(a3),d1			* compare with terminal character position
	BNE.s		LAB_18F7			* branch if not at end of line

	MOVE.l	d0,-(sp)			* save d0
	BSR		LAB_CRLF			* else print CR/LF
	MOVE.l	(sp)+,d0			* restore d0
LAB_18F7
	ADDQ.b	#$01,TPos(a3)		* increment terminal position
LAB_18F9
	JSR		V_OUTP(a3)			* output byte via output vector
	CMP.b		#$0D,d0			* compare with [CR]
	BNE.s		LAB_188A			* branch if not [CR]

							* else print nullct nulls after the [CR]
	MOVEQ		#$00,d1			* clear d1
	MOVE.b	Nullct(a3),d1		* get null count
	BEQ.s		LAB_1886			* branch if no nulls

	MOVEQ		#$00,d0			* load [NULL]
LAB_1880
	JSR		V_OUTP(a3)			* go print the character
	DBF		d1,LAB_1880			* decrement count and loop if not all done

	MOVEQ		#$0D,d0			* restore the character
LAB_1886
	MOVE.b	d1,TPos(a3)			* clear terminal position
LAB_188A
	MOVE.l	(sp)+,d1			* restore d1
	RTS


*************************************************************************************
*
* handle bad input data

LAB_1904
	MOVEA.l	(sp)+,a5			* restore execute pointer
	TST.b		Imode(a3)			* test input mode flag, $00=INPUT, $98=READ
	BPL.s		LAB_1913			* branch if INPUT (go do redo)

	MOVE.l	Dlinel(a3),Clinel(a3)	* save DATA line as current line
	BRA		LAB_TMER			* do type mismatch error, then warm start

							* mode was INPUT
LAB_1913
	LEA		LAB_REDO(pc),a0		* point to redo message
	BSR		LAB_18C3			* print null terminated string from memory
	MOVEA.l	Cpntrl(a3),a5		* save continue pointer as BASIC execute pointer
	RTS


*************************************************************************************
*
* perform INPUT

LAB_INPUT
	BSR		LAB_CKRN			* check not direct (back here if ok)
	CMP.b		#'"',d0			* compare the next byte with open quote
	BNE.s		LAB_1934			* if no prompt string just go get the input

	BSR		LAB_1BC1			* print "..." string
	MOVEQ		#';',d0			* set the search character to ";"
	BSR		LAB_SCCA			* scan for CHR$(d0), else do syntax error/warm
							* start
	BSR		LAB_18C6			* print string from Sutill/Sutilh
							* finished the prompt, now read the data
LAB_1934
	BSR		LAB_INLN			* print "? " and get BASIC input
							* return a0 pointing to the buffer start
	MOVEQ		#0,d0				* flag INPUT

* if you don't want a null response to INPUT to break the program then set the nobrk
* value at the top of this file to some non zero value

 ifne	nobrk

	BRA.s		LAB_1953			* go handle the input

 endc

* if you do want a null response to INPUT to break the program then leave the nobrk
* value at the top of this file set to zero

 ifeq	nobrk

	TST.b		(a0)				* test first byte from buffer
	BNE.s		LAB_1953			* branch if not null input

	BRA		LAB_1647			* go do BREAK exit

 endc


*************************************************************************************
*
* perform READ

LAB_READ
	MOVEA.l	Dptrl(a3),a0		* get the DATA pointer
	MOVEQ		#$98-$100,d0		* flag READ
LAB_1953
	MOVE.b	d0,Imode(a3)		* set input mode flag, $00=INPUT, $98=READ
	MOVE.l	a0,Rdptrl(a3)		* save READ pointer

							* READ or INPUT the next variable from list
LAB_195B
	BSR		LAB_SVAR			* search for or create a variable
							* return the variable address in a0
	MOVE.l	a0,Lvarpl(a3)		* save variable address as LET variable
	MOVE.l	a5,-(sp)			* save BASIC execute pointer
LAB_1961
	MOVEA.l	Rdptrl(a3),a5		* set READ pointer as BASIC execute pointer
	BSR		LAB_GBYT			* scan memory
	BNE.s		LAB_1986			* if not null go get the value

							* the pointer was to a null entry
	TST.b		Imode(a3)			* test input mode flag, $00=INPUT, $98=READ
	BMI.s		LAB_19DD			* branch if READ (go find the next statement)

							* else the mode was INPUT so get more
	BSR		LAB_18E3			* print a "?" character
	BSR		LAB_INLN			* print "? " and get BASIC input
							* return a0 pointing to the buffer start

* if you don't want a null response to INPUT to break the program then set the nobrk
* value at the top of this file to some non zero value

 ifne	nobrk

	MOVE.l	a0,Rdptrl(a3)		* save the READ pointer
	BRA.s		LAB_1961			* go handle the input

 endc

* if you do want a null response to INPUT to break the program then leave the nobrk
* value at the top of this file set to zero

 ifeq	nobrk

	TST.b		(a0)				* test the first byte from the buffer
	BNE.s		LAB_1984			* if not null input go handle it

	BRA		LAB_1647			* else go do the BREAK exit

LAB_1984
	MOVEA.l	a0,a5				* set the execute pointer to the buffer
	SUBQ.w	#1,a5				* decrement the execute pointer

 endc

LAB_1985
	BSR		LAB_IGBY			* increment & scan memory
LAB_1986
	TST.b		Dtypef(a3)			* test data type, $80=string, $40=integer,
							* $00=float
	BPL.s		LAB_19B0			* branch if numeric

							* else get string
	MOVE.b	d0,d2				* save search character
	CMP.b		#$22,d0			* was it " ?
	BEQ.s		LAB_1999			* branch if so

	MOVEQ		#':',d2			* set new search character
	MOVEQ		#',',d0			* other search character is ","
	SUBQ.w	#1,a5				* decrement BASIC execute pointer
LAB_1999
	ADDQ.w	#1,a5				* increment BASIC execute pointer
	MOVE.b	d0,d3				* set second search character
	MOVEA.l	a5,a0				* BASIC execute pointer is source

	BSR		LAB_20B4			* print d2/d3 terminated string to FAC1 stack
							* d2 = Srchc, d3 = Asrch, a0 is source
	MOVEA.l	a2,a5				* copy end of string to BASIC execute pointer
	BSR		LAB_17D5			* go do string LET
	BRA.s		LAB_19B6			* go check string terminator

							* get numeric INPUT
LAB_19B0
	MOVE.b	Dtypef(a3),-(sp)		* save variable data type
	BSR		LAB_2887			* get FAC1 from string
	MOVE.b	(sp)+,Dtypef(a3)		* restore variable data type
	BSR		LAB_PFAC			* pack FAC1 into (Lvarpl)
LAB_19B6
	BSR		LAB_GBYT			* scan memory
	BEQ.s		LAB_19C2			* branch if null (last entry)

	CMP.b		#',',d0			* else compare with ","
	BNE		LAB_1904			* if not "," go handle bad input data

	ADDQ.w	#1,a5				* else was "," so point to next chr
							* got good input data
LAB_19C2
	MOVE.l	a5,Rdptrl(a3)		* save the read pointer for now
	MOVEA.l	(sp)+,a5			* restore the execute pointer
	BSR		LAB_GBYT			* scan the memory
	BEQ.s		LAB_1A03			* if null go do extra ignored message

	PEA		LAB_195B(pc)		* set return address
	BRA		LAB_1C01			* scan for "," else do syntax error/warm start
							* then go INPUT next variable from list

							* find next DATA statement or do "Out of Data"
							* error
LAB_19DD
	BSR		LAB_SNBS			* scan for next BASIC statement ([:] or [EOL])
							* returns a0 as pointer to [:] or [EOL]
	MOVEA.l	a0,a5				* add index, now = pointer to [EOL]/[EOS]
	ADDQ.w	#1,a5				* pointer to next character
	CMP.b		#':',d0			* was it statement end?
	BEQ.s		LAB_19F6			* branch if [:]

							* was [EOL] so find next line

	MOVE.w	a5,d1				* past pad byte(s)
	AND.w		#1,d1				* mask odd bit
	ADD.w		d1,a5				* add pointer
	MOVE.l	(a5)+,d2			* get next line pointer
	BEQ		LAB_ODER			* branch if end of program

	MOVE.l	(a5)+,Dlinel(a3)		* save current DATA line
LAB_19F6
	BSR		LAB_GBYT			* scan memory
	CMP.b		#TK_DATA,d0			* compare with "DATA" token
	BEQ		LAB_1985			* was "DATA" so go do next READ

	BRA.s		LAB_19DD			* go find next statement if not "DATA"

* end of INPUT/READ routine

LAB_1A03
	MOVEA.l	Rdptrl(a3),a0		* get temp READ pointer
	TST.b		Imode(a3)			* get input mode flag, $00=INPUT, $98=READ
	BPL.s		LAB_1A0E			* branch if INPUT

	MOVE.l	a0,Dptrl(a3)		* else save temp READ pointer as DATA pointer
	RTS

							* we were getting INPUT
LAB_1A0E
	TST.b		(a0)				* test next byte
	BNE.s		LAB_1A1B			* error if not end of INPUT

	RTS
							* user typed too much
LAB_1A1B
	LEA		LAB_IMSG(pc),a0		* point to extra ignored message
	BRA		LAB_18C3			* print null terminated string from memory & RTS


*************************************************************************************
*
* perform NEXT

LAB_NEXT
	BNE.s		LAB_1A46			* branch if NEXT var

	ADDQ.w	#4,sp				* back past return address
	CMP.w		#TK_FOR,(sp)		* is FOR token on stack?
	BNE		LAB_NFER			* if not do NEXT without FOR err/warm start

	MOVEA.l	2(sp),a0			* get stacked FOR variable pointer
	BRA.s		LAB_11BD			* branch always (no variable to search for)

* NEXT var

LAB_1A46
	BSR		LAB_GVAR			* get variable address in a0
	ADDQ.w	#4,sp				* back past return address
	MOVE.w	#TK_FOR,d0			* set for FOR token
	MOVEQ		#$1C,d1			* set for FOR use size
	BRA.s		LAB_11A6			* enter loop for next variable search

LAB_11A5
	ADDA.l	d1,sp				* add FOR stack use size
LAB_11A6
	CMP.w		(sp),d0			* is FOR token on stack?
	BNE		LAB_NFER			* if not found do NEXT without FOR error and
							* warm start

							* was FOR token
	CMPA.l	2(sp),a0			* compare var pointer with stacked var pointer
	BNE.s		LAB_11A5			* loop if no match found

LAB_11BD
	MOVE.w	6(sp),FAC2_e(a3)		* get STEP value exponent and sign
	MOVE.l	8(sp),FAC2_m(a3)		* get STEP value mantissa

	MOVE.b	18(sp),Dtypef(a3)		* restore FOR variable data type
	BSR		LAB_1C19			* check type and unpack (a0)

	MOVE.b	FAC2_s(a3),FAC_sc(a3)	* save FAC2 sign as sign compare
	MOVE.b	FAC1_s(a3),d0		* get FAC1 sign
	EOR.b		d0,FAC_sc(a3)		* EOR to create sign compare

	MOVE.l	a0,Lvarpl(a3)		* save variable pointer
	BSR		LAB_ADD			* add STEP value to FOR variable
	MOVE.b	18(sp),Dtypef(a3)		* restore FOR variable data type (again)
	BSR		LAB_PFAC			* pack FAC1 into FOR variable (Lvarpl)

	MOVE.w	12(sp),FAC2_e(a3)		* get TO value exponent and sign
	MOVE.l	14(sp),FAC2_m(a3)		* get TO value mantissa

	MOVE.b	FAC2_s(a3),FAC_sc(a3)	* save FAC2 sign as sign compare
	MOVE.b	FAC1_s(a3),d0		* get FAC1 sign
	EOR.b		d0,FAC_sc(a3)		* EOR to create sign compare

	BSR		LAB_27FA			* compare FAC1 with FAC2 (TO value)
							* returns d0=+1 if FAC1 > FAC2
							* returns d0= 0 if FAC1 = FAC2
							* returns d0=-1 if FAC1 < FAC2

	MOVE.w	6(sp),d1			* get STEP value exponent and sign
	EOR.w		d0,d1				* EOR compare result with STEP exponent and sign

	TST.b		d0				* test for =
	BEQ.s		LAB_1A90			* branch if = (loop INcomplete)

	TST.b		d1				* test result
	BPL.s		LAB_1A9B			* branch if > (loop complete)

							* loop back and do it all again
LAB_1A90
	MOVE.l	20(sp),Clinel(a3)		* reset current line
	MOVE.l	24(sp),a5			* reset BASIC execute pointer
	BRA		LAB_15C2			* go do interpreter inner loop

							* loop complete so carry on
LAB_1A9B
	ADDA.w	#28,sp			* add 28 to dump FOR structure
	BSR		LAB_GBYT			* scan memory
	CMP.b		#$2C,d0			* compare with ","
	BNE		LAB_15C2			* if not "," go do interpreter inner loop

							* was "," so another NEXT variable to do
	BSR		LAB_IGBY			* else increment & scan memory
	BSR		LAB_1A46			* do NEXT (var)


*************************************************************************************
*
* evaluate expression & check is numeric, else do type mismatch

LAB_EVNM
	BSR.s		LAB_EVEX			* evaluate expression


*************************************************************************************
*
* check if source is numeric, else do type mismatch

LAB_CTNM
	CMP.w		d0,d0				* required type is numeric so clear carry


*************************************************************************************
*
* type match check, set C for string, clear C for numeric

LAB_CKTM
	BTST.b	#7,Dtypef(a3)		* test data type flag, don't change carry
	BNE.s		LAB_1ABA			* branch if data type is string

							* else data type was numeric
	BCS		LAB_TMER			* if required type is string do type mismatch
							* error

	RTS
							* data type was string, now check required type
LAB_1ABA
	BCC		LAB_TMER			* if required type is numeric do type mismatch
							* error
	RTS


*************************************************************************************
*
* this routine evaluates any type of expression. first it pushes an end marker so
* it knows when the expression has been evaluated, this is a precedence value of zero.
* next the first value is evaluated, this can be an in line value, either numeric or
* string, a variable or array element of any type, a function or even an expression
* in parenthesis. this value is kept in FAC_1
* after the value is evaluated a test is made on the next BASIC program byte, if it
* is a comparrison operator i.e. "<", "=" or ">", then the corresponding bit is set
* in the comparison evaluation flag. this test loops until no more comparrison operators
* are found or more than one of any type is found. in the last case an error is generated

* evaluate expression

LAB_EVEX
	SUBQ.w	#1,a5				* decrement BASIC execute pointer
LAB_EVEZ
	MOVEQ		#0,d1				* clear precedence word
	MOVE.b	d1,Dtypef(a3)		* clear the data type, $80=string, $40=integer,
							* $00=float
	BRA.s		LAB_1ACD			* enter loop

* get vector, set up operator then continue evaluation

LAB_1B43						*
	LEA		LAB_OPPT(pc),a0		* point to operator vector table
	MOVE.w	2(a0,d1.w),d0		* get vector offset
	PEA		(a0,d0.w)			* push vector

	MOVE.l	FAC1_m(a3),-(sp)		* push FAC1 mantissa
	MOVE.w	FAC1_e(a3),-(sp)		* push sign and exponent
	MOVE.b	comp_f(a3),-(sp)		* push comparison evaluation flag

	MOVE.w	(a0,d1.w),d1		* get precedence value
LAB_1ACD
	MOVE.w	d1,-(sp)			* push precedence value
	BSR		LAB_GVAL			* get value from line
	MOVE.b	#$00,comp_f(a3)		* clear compare function flag
LAB_1ADB
	BSR		LAB_GBYT			* scan memory
LAB_1ADE
	SUB.b		#TK_GT,d0			* subtract token for > (lowest compare function)
	BCS.s		LAB_1AFA			* branch if < TK_GT

	CMP.b		#$03,d0			* compare with ">" to "<" tokens
	BCS.s		LAB_1AE0			* branch if <= TK_SGN (is compare function)

	TST.b		comp_f(a3)			* test compare function flag
	BNE.s		LAB_1B2A			* branch if compare function

	BRA		LAB_1B78			* go do functions

							* was token for > = or < (d0 = 0, 1 or 2)
LAB_1AE0
	MOVEQ		#1,d1				* set to 0000 0001
	ASL.b		d0,d1				* 1 if >, 2 if =, 4 if <
	MOVE.b	comp_f(a3),d0		* copy old compare function flag
	EOR.b		d1,comp_f(a3)		* EOR in this compare function bit
	CMP.b		comp_f(a3),d0		* compare old with new compare function flag
	BCC		LAB_SNER			* if new <= old comp_f do syntax error and warm
							* start, there was more than one <, = or >
	BSR		LAB_IGBY			* increment & scan memory
	BRA.s		LAB_1ADE			* go do next character

							* token is < ">" or > "<" tokens
LAB_1AFA
	TST.b		comp_f(a3)			* test compare function flag
	BNE.s		LAB_1B2A			* branch if compare function

							* was < TK_GT so is operator or lower
	ADD.b	#(TK_GT-TK_PLUS),d0		* add # of operators (+ - * / ^ AND OR EOR)
	BCC.s		LAB_1B78			* branch if < + operator

	BNE.s		LAB_1B0B			* branch if not + token

	TST.b		Dtypef(a3)			* test data type, $80=string, $40=integer,
							* $00=float
	BMI		LAB_224D			* type is string & token was +

LAB_1B0B
	MOVEQ		#0,d1				* clear longword
	ADD.b		d0,d0				* *2
	ADD.b		d0,d0				* *4
	MOVE.b	d0,d1				* copy to index
LAB_1B13
	MOVE.w	(sp)+,d0			* pull previous precedence
	LEA		LAB_OPPT(pc),a0		* set pointer to operator table
	CMP.w		(a0,d1.w),d0		* compare with this opperator precedence
	BCC.s		LAB_1B7D			* branch if previous precedence (d0) >=

	BSR		LAB_CTNM			* check if source is numeric, else type mismatch
LAB_1B1C
	MOVE.w	d0,-(sp)			* save precedence
LAB_1B1D
	BSR		LAB_1B43			* get vector, set-up operator and continue
							* evaluation
	MOVE.w	(sp)+,d0			* restore precedence
	MOVE.l	prstk(a3),d1		* get stacked function pointer
	BPL.s		LAB_1B3C			* branch if stacked values

	MOVE.w	d0,d0				* copy precedence (set flags)
	BEQ.s		LAB_1B7B			* exit if done

	BRA.s		LAB_1B86			* else pop FAC2 & return (do function)

							* was compare function (< = >)
LAB_1B2A
	MOVE.b	Dtypef(a3),d0		* get data type flag
	MOVE.b	comp_f(a3),d1		* get compare function flag
	ADD.b		d0,d0				* string bit flag into X bit
	ADDX.b	d1,d1				* shift compare function flag

	MOVE.b	#0,Dtypef(a3)		* clear data type flag, $00=float
	MOVE.b	d1,comp_f(a3)		* save new compare function flag
	SUBQ.w	#1,a5				* decrement BASIC execute pointer
	MOVEQ		#(TK_LT-TK_PLUS)*4,d1	* set offset to last operator entry
	BRA.s		LAB_1B13			* branch always

LAB_1B3C
	LEA		LAB_OPPT(pc),a0		* point to function vector table
	CMP.w		(a0,d1.w),d0		* compare with this opperator precedence
	BCC.s		LAB_1B86			* branch if d0 >=, pop FAC2 & return

	BRA.s		LAB_1B1C			* branch always

* do functions

LAB_1B78
	MOVEQ		#-1,d1			* flag all done
	MOVE.w	(sp)+,d0			* pull precedence word
LAB_1B7B
	BEQ.s		LAB_1B9D			* exit if done

LAB_1B7D
	CMP.w		#$64,d0			* compare previous precedence with $64
	BEQ.s		LAB_1B84			* branch if was $64 (< function can be string)

	BSR		LAB_CTNM			* check if source is numeric, else type mismatch
LAB_1B84
	MOVE.l	d1,prstk(a3)		* save current operator index

							* pop FAC2 & return
LAB_1B86
	MOVE.b	(sp)+,d0			* pop comparison evaluation flag
	MOVE.b	d0,d1				* copy comparison evaluation flag
	LSR.b		#1,d0				* shift out comparison evaluation lowest bit
	MOVE.b	d0,Cflag(a3)		* save comparison evaluation flag
	MOVE.w	(sp)+,FAC2_e(a3)		* pop exponent and sign
	MOVE.l	(sp)+,FAC2_m(a3)		* pop mantissa
	MOVE.b	FAC2_s(a3),FAC_sc(a3)	* copy FAC2 sign
	MOVE.b	FAC1_s(a3),d0		* get FAC1 sign
	EOR.b		d0,FAC_sc(a3)		* EOR FAC1 sign and set sign compare

	LSR.b		#1,d1				* type bit into X and C
	RTS

LAB_1B9D
	MOVE.b	FAC1_e(a3),d0		* get FAC1 exponent
	RTS


*************************************************************************************
*
* get a value from the BASIC line

LAB_GVAL
	BSR.s		LAB_IGBY			* increment & scan memory
	BCS		LAB_2887			* if numeric get FAC1 from string & return

	TST.b		d0				* test byte
	BMI		LAB_1BD0			* if -ve go test token values

							* else it is either a string, number, variable
							* or (<expr>)
	CMP.b		#'$',d0			* compare with "$"
	BEQ		LAB_2887			* if "$" get hex number from string & return

	CMP.b		#'%',d0			* else compare with "%"
	BEQ		LAB_2887			* if "%" get binary number from string & return

	CMP.b		#$2E,d0			* compare with "."
	BEQ		LAB_2887			* if so get FAC1 from string and return
							* (e.g. .123)

							* wasn't a number so ...
	CMP.b		#$22,d0			* compare with "
	BNE.s		LAB_1BF3			* if not open quote it must be a variable or
							* open bracket

							* was open quote so get the enclosed string

* print "..." string to string stack

LAB_1BC1
	MOVE.b	(a5)+,d0			* increment BASIC execute pointer (past ")
							* fastest/shortest method
	MOVEA.l	a5,a0				* copy basic execute pointer (string start)
	BSR		LAB_20AE			* print " terminated string to stack
	MOVEA.l	a2,a5				* restore BASIC execute pointer from temp
	RTS

* get value from line .. continued
							* wasn't any sort of number so ...
LAB_1BF3
	CMP.b		#'(',d0			* compare with "("
	BNE.s		LAB_1C18			* if not "(" get (var) and return value in FAC1
							* and $ flag


*************************************************************************************
*
* evaluate expression within parentheses

LAB_1BF7
	BSR		LAB_EVEZ			* evaluate expression (no decrement)


*************************************************************************************
*
* all the 'scan for' routines return the character after the sought character

* scan for ")", else do syntax error, then warm start

LAB_1BFB
	MOVEQ		#$29,d0			* load d0 with ")"
	BRA.s		LAB_SCCA


*************************************************************************************
*
* scan for "," and get byte, else do Syntax error then warm start

LAB_SCGB
	PEA		LAB_GTBY(pc)		* return address is to get byte parameter


*************************************************************************************
*
* scan for ",", else do syntax error, then warm start

LAB_1C01
	MOVEQ		#$2C,d0			* load d0 with ","


*************************************************************************************
*
* scan for CHR$(d0) , else do syntax error, then warm start

LAB_SCCA
	CMP.b		(a5)+,d0			* check next byte is = d0
	BEQ.s		LAB_GBYT			* if so go get next

	BRA		LAB_SNER			* else do syntax error/warm start


*************************************************************************************
*
* BASIC increment and scan memory routine

LAB_IGBY
	MOVE.b	(a5)+,d0			* get byte & increment pointer

* scan memory routine, exit with Cb = 1 if numeric character
* also skips any spaces encountered

LAB_GBYT
	MOVE.b	(a5),d0			* get byte

	CMP.b		#$20,d0			* compare with " "
	BEQ.s		LAB_IGBY			* if " " go do next

* test current BASIC byte, exit with Cb = 1 if numeric character

	CMP.b		#TK_ELSE,d0			* compare with the token for ELSE
	BCC.s		RTS_001			* exit if >= (not numeric, carry clear)

	CMP.b		#$3A,d0			* compare with ":"
	BCC.s		RTS_001			* exit if >= (not numeric, carry clear)

	MOVEQ		#-48,d6			* set -"0"
	ADD.b		d6,d0				* add -"0"
	SUB.b		d6,d0				* subtract -"0"
RTS_001						* carry set if byte = "0"-"9"
	RTS


*************************************************************************************
*
* set-up for - operator

LAB_1C11
	BSR		LAB_CTNM			* check if source is numeric, else type mismatch
	MOVEQ	#(TK_GT-TK_PLUS)*4,d1		* set offset from base to - operator
LAB_1C13
	LEA		4(sp),sp			* dump GVAL return address
	BRA		LAB_1B1D			* continue evaluating expression


*************************************************************************************
*
* variable name set-up
* get (var), return value in FAC_1 & data type flag

LAB_1C18
	BSR		LAB_GVAR			* get variable address in a0

* if you want a non existant variable to return a null value then set the novar
* value at the top of this file to some non zero value

 ifne	novar

	BNE.s		LAB_1C19			* if it exists return it

	LEA.l		LAB_1D96(pc),a0		* else return a null descriptor/pointer

 endc

* return existing variable value

LAB_1C19
	TST.b		Dtypef(a3)			* test data type, $80=string, $40=integer,
							* $00=float
	BEQ		LAB_UFAC			* if float unpack memory (a0) into FAC1 and
							* return

	BPL.s		LAB_1C1A			* if integer unpack memory (a0) into FAC1
							* and return

	MOVE.l	a0,FAC1_m(a3)		* else save descriptor pointer in FAC1
	RTS

LAB_1C1A
	MOVE.l	(a0),d0			* get integer value
	BRA		LAB_AYFC			* convert d0 to signed longword in FAC1 & return


*************************************************************************************
*
* get value from line .. continued
* do tokens

LAB_1BD0
	CMP.b		#TK_MINUS,d0		* compare with token for -
	BEQ.s		LAB_1C11			* branch if - token (do set-up for - operator)

							* wasn't -123 so ...
	CMP.b		#TK_PLUS,d0			* compare with token for +
	BEQ		LAB_GVAL			* branch if + token (+n = n so ignore leading +)

	CMP.b		#TK_NOT,d0			* compare with token for NOT
	BNE.s		LAB_1BE7			* branch if not token for NOT

							* was NOT token
	MOVE.w	#(TK_EQUAL-TK_PLUS)*4,d1	* offset to NOT function
	BRA.s		LAB_1C13			* do set-up for function then execute

							* wasn't +, - or NOT so ...
LAB_1BE7
	CMP.b		#TK_FN,d0			* compare with token for FN
	BEQ		LAB_201E			* if FN go evaluate FNx

							* wasn't +, -, NOT or FN so ...
	SUB.b		#TK_SGN,d0			* compare with token for SGN & normalise
	BCS		LAB_SNER			* if < SGN token then do syntax error

* get value from line .. continued
* only functions left so set up function references

* new for V2.0+ this replaces a lot of IF .. THEN .. ELSEIF .. THEN .. that was needed
* to process function calls. now the function vector is computed and pushed on the stack
* and the preprocess offset is read. if the preprocess offset is non zero then the vector
* is calculated and the routine called, if not this routine just does RTS. whichever
* happens the RTS at the end of this routine, or the preprocess routine calls, the
* function code

* this also removes some less than elegant code that was used to bypass type checking
* for functions that returned strings

	AND.w		#$7F,d0			* mask byte
	ADD.w		d0,d0				* *2 (2 bytes per function offset)

	LEA		LAB_FTBL(pc),a0		* pointer to functions vector table
	MOVE.w	(a0,d0.w),d1		* get function vector offset
	PEA		(a0,d1.w)			* push function vector

	LEA		LAB_FTPP(pc),a0		* pointer to functions preprocess vector table
	MOVE.w	(a0,d0.w),d0		* get function preprocess vector offset
	BEQ.s		LAB_1C2A			* no preprocess vector so go do function

	LEA		(a0,d0.w),a0		* get function preprocess vector
	JMP		(a0)				* go do preprocess routine then function


*************************************************************************************
*
* process string expression in parenthesis

LAB_PPFS
	BSR		LAB_1BF7			* process expression in parenthesis
	TST.b		Dtypef(a3)			* test data type
	BPL		LAB_TMER			* if numeric do Type missmatch Error/warm start

LAB_1C2A
	RTS						* else do function


*************************************************************************************
*
* process numeric expression in parenthesis

LAB_PPFN
	BSR		LAB_1BF7			* process expression in parenthesis
	TST.b		Dtypef(a3)			* test data type
	BMI		LAB_TMER			* if string do Type missmatch Error/warm start

	RTS						* else do function


*************************************************************************************
*
* set numeric data type and increment BASIC execute pointer

LAB_PPBI
	MOVE.b	#$00,Dtypef(a3)		* clear data type flag, $00=float
	MOVE.b	(a5)+,d0			* get next BASIC byte
	RTS						* do function


*************************************************************************************
*
* process string for LEFT$, RIGHT$ or MID$

LAB_LRMS
	BSR		LAB_EVEZ			* evaluate (should be string) expression
	TST.b		Dtypef(a3)			* test data type flag
	BPL		LAB_TMER			* if type is not string do type mismatch error

	MOVE.b	(a5)+,d2			* get BASIC byte
	CMP.b		#',',d2			* compare with comma
	BNE		LAB_SNER			* if not "," go do syntax error/warm start

	MOVE.l	FAC1_m(a3),-(sp)		* save descriptor pointer
	BSR		LAB_GTWO			* get word parameter, result in d0 and Itemp
	MOVEA.l	(sp)+,a0			* restore descriptor pointer
	RTS						* do function


*************************************************************************************
*
* process numeric expression(s) for BIN$ or HEX$

LAB_BHSS
	BSR		LAB_EVEZ			* evaluate expression (no decrement)
	TST.b		Dtypef(a3)			* test data type
	BMI		LAB_TMER			* if string do Type missmatch Error/warm start

	BSR		LAB_2831			* convert FAC1 floating to fixed
							* result in d0 and Itemp
	MOVEQ		#0,d1				* set default to no leading "0"s
	MOVE.b	(a5)+,d2			* get BASIC byte
	CMP.b		#',',d2			* compare with comma
	BNE.s		LAB_BHCB			* if not "," go check close bracket

	MOVE.l	d0,-(sp)			* copy number to stack
	BSR		LAB_GTBY			* get byte value
	MOVE.l	d0,d1				* copy leading 0s #
	MOVE.l	(sp)+,d0			* restore number from stack
	MOVE.b	(a5)+,d2			* get BASIC byte
LAB_BHCB
	CMP.b		#')',d2			* compare with close bracket
	BNE		LAB_SNER			* if not ")" do Syntax Error/warm start

	RTS						* go do function


*************************************************************************************
*
* perform EOR

LAB_EOR
	BSR.s		GetFirst			* get two values for OR, AND or EOR
							* first in d0, and Itemp, second in d2
	EOR.l		d2,d0				* EOR values
	BRA		LAB_AYFC			* convert d0 to signed longword in FAC1 & RET


*************************************************************************************
*
* perform OR

LAB_OR
	BSR.s		GetFirst			* get two values for OR, AND or EOR
							* first in d0, and Itemp, second in d2
	OR.l		d2,d0				* do OR
	BRA		LAB_AYFC			* convert d0 to signed longword in FAC1 & RET


*************************************************************************************
*
* perform AND

LAB_AND
	BSR.s		GetFirst			* get two values for OR, AND or EOR
							* first in d0, and Itemp, second in d2
	AND.l		d2,d0				* do AND
	BRA		LAB_AYFC			* convert d0 to signed longword in FAC1 & RET


*************************************************************************************
*
* get two values for OR, AND, EOR
* first in d0, second in d2

GetFirst
	BSR		LAB_EVIR			* evaluate integer expression (no sign check)
							* result in d0 and Itemp
	MOVE.l	d0,d2				* copy second value
	BSR		LAB_279B			* copy FAC2 to FAC1, get first value in
							* expression
	BRA		LAB_EVIR			* evaluate integer expression (no sign check)
							* result in d0 and Itemp & return


*************************************************************************************
*
* perform NOT

LAB_EQUAL
	BSR		LAB_EVIR			* evaluate integer expression (no sign check)
							* result in d0 and Itemp
	NOT.l		d0				* bitwise invert
	BRA		LAB_AYFC			* convert d0 to signed longword in FAC1 & RET


*************************************************************************************
*
* perform comparisons
* do < compare

LAB_LTHAN
	BSR		LAB_CKTM			* type match check, set C for string
	BCS.s		LAB_1CAE			* branch if string

							* do numeric < compare
	BSR		LAB_27FA			* compare FAC1 with FAC2
							* returns d0=+1 if FAC1 > FAC2
							* returns d0= 0 if FAC1 = FAC2
							* returns d0=-1 if FAC1 < FAC2
	BRA.s		LAB_1CF2			* process result

							* do string < compare
LAB_1CAE
	MOVE.b	#$00,Dtypef(a3)		* clear data type, $80=string, $40=integer,
							* $00=float
	BSR		LAB_22B6			* pop string off descriptor stack, or from top
							* of string space returns d0 = length,
							* a0 = pointer
	MOVEA.l	a0,a1				* copy string 2 pointer
	MOVE.l	d0,d1				* copy string 2 length
	MOVEA.l	FAC2_m(a3),a0		* get string 1 descriptor pointer
	BSR		LAB_22BA			* pop (a0) descriptor, returns with ..
							* d0 = length, a0 = pointer
	MOVE.l	d0,d2				* copy length
	BNE.s		LAB_1CB5			* branch if not null string

	TST.l		d1				* test if string 2 is null also
	BEQ.s		LAB_1CF2			* if so do string 1 = string 2

LAB_1CB5
	SUB.l		d1,d2				* subtract string 2 length
	BEQ.s		LAB_1CD5			* branch if strings = length

	BCS.s		LAB_1CD4			* branch if string 1 < string 2

	MOVEQ		#-1,d0			* set for string 1 > string 2
	BRA.s		LAB_1CD6			* go do character comapare

LAB_1CD4
	MOVE.l	d0,d1				* string 1 length is compare length
	MOVEQ		#1,d0				* and set for string 1 < string 2
	BRA.s		LAB_1CD6			* go do character comapare

LAB_1CD5
	MOVE.l	d2,d0				* set for string 1 = string 2
LAB_1CD6
	SUBQ.l	#1,d1				* adjust length for DBcc loop

							* d1 is length to compare, d0 is <=> for length
							* a0 is string 1 pointer, a1 is string 2 pointer
LAB_1CE6
	CMPM.b	(a0)+,(a1)+			* compare string bytes (1 with 2)
	DBNE		d1,LAB_1CE6			* loop if same and not end yet

	BEQ.s		LAB_1CF2			* if = to here, then go use length compare

	BCC.s		LAB_1CDB			* else branch if string 1 > string 2

	MOVEQ		#-1,d0			* else set for string 1 < string 2
	BRA.s		LAB_1CF2			* go set result

LAB_1CDB
	MOVEQ		#1,d0				* and set for string 1 > string 2

LAB_1CF2
	ADDQ.b	#1,d0				* make result 0, 1 or 2
	MOVE.b	d0,d1				* copy to d1
	MOVEQ		#1,d0				* set d0 longword
	ROL.b		d1,d0				* make 1, 2 or 4 (result = flag bit)
	AND.b		Cflag(a3),d0		* AND with comparison evaluation flag
	BEQ		LAB_27DB			* exit if not a wanted result (i.e. false)

	MOVEQ		#-1,d0			* else set -1 (true)
	BRA		LAB_27DB			* save d0 as integer & return


LAB_1CFE
	BSR		LAB_1C01			* scan for ",", else do syntax error/warm start


*************************************************************************************
*
* perform DIM

LAB_DIM
	MOVEQ		#-1,d1			* set "DIM" flag
	BSR.s		LAB_1D10			* search for or dimension a variable
	BSR		LAB_GBYT			* scan memory
	BNE.s		LAB_1CFE			* loop and scan for "," if not null

	RTS


*************************************************************************************
*
* perform << (left shift)

LAB_LSHIFT
	BSR.s		GetPair			* get an integer and byte pair
							* byte is in d2, integer is in d0 and Itemp
	BEQ.s		NoShift			* branch if byte zero

	CMP.b		#$20,d2			* compare bit count with 32d
	BCC.s		TooBig			* branch if >=

	ASL.l		d2,d0				* shift longword
NoShift
	BRA		LAB_AYFC			* convert d0 to signed longword in FAC1 & RET


*************************************************************************************
*
* perform >> (right shift)

LAB_RSHIFT
	BSR.s		GetPair			* get an integer and byte pair
							* byte is in d2, integer is in d0 and Itemp
	BEQ.s		NoShift			* branch if byte zero

	CMP.b		#$20,d2			* compare bit count with 32d
	BCS.s		Not2Big			* branch if >= (return shift)

	TST.l		d0				* test sign bit
	BPL.s		TooBig			* branch if +ve

	MOVEQ		#-1,d0			* set longword
	BRA		LAB_AYFC			* convert d0 to longword in FAC1 & RET

Not2Big
	ASR.l		d2,d0				* shift longword
	BRA		LAB_AYFC			* convert d0 to longword in FAC1 & RET

TooBig
	MOVEQ		#0,d0				* clear longword
	BRA		LAB_AYFC			* convert d0 to longword in FAC1 & RET


*************************************************************************************
*
* get an integer and byte pair
* byte is in d2, integer is in d0 and Itemp

GetPair
	BSR		LAB_EVBY			* evaluate byte expression, result in d0 and
							* Itemp
	MOVE.b	d0,d2				* save it
	BSR		LAB_279B			* copy FAC2 to FAC1, get first value in
							* expression
	BSR		LAB_EVIR			* evaluate integer expression (no sign check)
							* result in d0 and Itemp
	TST.b		d2				* test byte value
	RTS


*************************************************************************************
*
* check alpha, return C=0 if<"A" or >"Z" or <"a" to "z">

LAB_CASC
	CMP.b		#$61,d0			* compare with "a"
	BCC.s		LAB_1D83			* if >="a" go check =<"z"


*************************************************************************************
*
* check alpha upper case, return C=0 if<"A" or >"Z"

LAB_CAUC
	CMP.b		#$41,d0			* compare with "A"
	BCC.s		LAB_1D8A			* if >="A" go check =<"Z"

	OR		d0,d0				* make C=0
	RTS

LAB_1D8A
	CMP.b		#$5B,d0			* compare with "Z"+1
							* carry set if byte<="Z"
	RTS

LAB_1D83
	CMP.b		#$7B,d0			* compare with "z"+1
							* carry set if byte<="z"
	RTS


*************************************************************************************
*
* search for or create variable. this is used to automatically create a variable if
* it is not found. any routines that need to create the variable call LAB_GVAR via
* this point and error generation is supressed and the variable will be created
*
* return pointer to variable in Cvaral and a0
* set data type to variable type

LAB_SVAR
	BSR.s		LAB_GVAR			* search for variable
LAB_FVAR
	RTS


*************************************************************************************
*
* search for variable. if this routine is called from anywhere but the above call and
* the variable searched for does not exist then an error will be returned
*
* DIM flag is in d1.b
* return pointer to variable in Cvaral and a0
* set data type to variable type

LAB_GVAR
	MOVEQ		#$00,d1			* set DIM flag = $00
	BSR		LAB_GBYT			* scan memory (1st character)
LAB_1D10
	MOVE.b	d1,Defdim(a3)		* save DIM flag

* search for FN name entry point

LAB_1D12
	BSR.s		LAB_CASC			* check byte, return C=0 if<"A" or >"Z"
	BCC		LAB_SNER			* if not, syntax error then warm start

							* it is a variable name so ...
	MOVEQ		#$0,d1			* set index for name byte
	LEA		Varname(a3),a0		* pointer to variable name
	MOVE.l	d1,(a0)			* clear the variable name
	MOVE.b	d1,Dtypef(a3)		* clear the data type, $80=string, $40=integer,
							* $00=float

LAB_1D2D
	CMP.w		#$04,d1			* done all significant characters?
	BCC.s		LAB_1D2E			* if so go ignore any more

	MOVE.b	d0,(a0,d1.w)		* save the character
	ADDQ.w	#1,d1				* increment index
LAB_1D2E
	BSR		LAB_IGBY			* increment & scan memory (next character)
	BCS.s		LAB_1D2D			* branch if character = "0"-"9" (ok)

							* character wasn't "0" to "9" so ...
	BSR.s		LAB_CASC			* check byte, return C=0 if<"A" or >"Z"
	BCS.s		LAB_1D2D			* branch if = "A"-"Z" (ok)

							* check if string variable
	CMP.b		#'$',d0			* compare with "$"
	BNE.s		LAB_1D44			* branch if not string

							* type is string
	OR.b		#$80,Varname+1(a3)	* set top bit of 2nd character, indicate string
	BSR		LAB_IGBY			* increment & scan memory
	BRA.s		LAB_1D45			* skip integer check

							* check if integer variable
LAB_1D44
	CMP.b		#'&',d0			* compare with "&"
	BNE.s		LAB_1D45			* branch if not integer

							* type is integer
	OR.b		#$80,Varname+2(a3)	* set top bit of 3rd character, indicate integer
	BSR		LAB_IGBY			* increment & scan memory

* after we have determined the variable type we need to determine
* if it's an array of type

							* gets here with character after var name in d0
LAB_1D45
	TST.b		Sufnxf(a3)			* test function name flag
	BEQ.s		LAB_1D48			* if not FN or FN variable continue

	BPL.s		LAB_1D49			* if FN variable go find or create it

							* else was FN name
	MOVE.l	Varname(a3),d0		* get whole function name
	MOVEQ		#8,d1				* set step to next function size -4
	LEA		Sfncl(a3),a0		* get pointer to start of functions
	BRA.s		LAB_1D4B			* go find function

LAB_1D48
	SUB.b		#'(',d0			* subtract "("
	BEQ		LAB_1E17			* if "(" go find, or make, array

* either find or create var
* var name (1st four characters only!) is in Varname

							* variable name wasn't var( .. so look for
							* plain variable
LAB_1D49
	MOVE.l	Varname(a3),d0		* get whole variable name
LAB_1D4A
	MOVEQ		#4,d1				* set step to next variable size -4
	LEA		Svarl(a3),a0		* get pointer to start of variables

	BTST.l	#23,d0			* test if string name
	BEQ.s		LAB_1D4B			* branch if not

	ADDQ.w	#2,d1				* 6 bytes per string entry
	ADDQ.w	#(Sstrl-Svarl),a0		* move to string area

LAB_1D4B
	MOVEA.l	4(a0),a1			* get end address
	MOVEA.l	(a0),a0			* get start address
	BRA.s		LAB_1D5E			* enter loop at exit check

LAB_1D5D
	CMP.l		(a0)+,d0			* compare this variable with name
	BEQ.s		LAB_1DD7			* branch if match (found var)

	ADDA.l	d1,a0				* add offset to next variable
LAB_1D5E
	CMPA.l	a1,a0				* compare address with variable space end
	BNE.s		LAB_1D5D			* if not end go check next

	TST.b		Sufnxf(a3)			* is it a function or function variable
	BNE.s		LAB_1D94			* if was go do DEF or function variable

							* reached end of variable mem without match
							* ... so create new variable, possibly

	LEA		LAB_FVAR(pc),a2		* get the address of the create if doesn't
							* exist call to LAB_GVAR
	CMPA.l	(sp),a2			* compare the return address with expected
	BNE		LAB_UVER			* if not create go do error or return null

* this will only branch if the call to LAB_GVAR wasn't from LAB_SVAR

LAB_1D94
	BTST.b	#0,Sufnxf(a3)		* test function search flag
	BNE		LAB_UFER			* if not doing DEF then go do undefined
							* function error

							* else create new variable/function
LAB_1D98
	MOVEA.l	Earryl(a3),a2		* get end of block to move
	MOVE.l	a2,d2				* copy end of block to move
	SUB.l		a1,d2				* calculate block to move size

	MOVEA.l	a2,a0				* copy end of block to move
	ADDQ.l	#4,d1				* space for one variable/function + name
	ADDA.l	d1,a2				* add space for one variable/function
	MOVE.l	a2,Earryl(a3)		* set new array mem end
	LSR.l		#1,d2				* /2 for word copy
	BEQ.s		LAB_1DAF			* skip move if zero length block

	SUBQ.l	#1,d2				* -1 for DFB loop
	SWAP		d2				* swap high word to low word
LAB_1DAC
	SWAP		d2				* swap high word to low word
LAB_1DAE
	MOVE.w	-(a0),-(a2)			* copy word
	DBF		d2,LAB_1DAE			* loop until done

	SWAP		d2				* swap high word to low word
	DBF		d2,LAB_1DAC			* decrement high count and loop until done

* get here after creating either a function, variable or string
* if function set variables start, string start, array start
* if variable set string start, array start
* if string set array start

LAB_1DAF
	TST.b		Sufnxf(a3)			* was it function
	BMI.s		LAB_1DB0			* branch if was FN

	BTST.l	#23,d0			* was it string
	BNE.s		LAB_1DB2			* branch if string

	BRA.s		LAB_1DB1			* branch if was plain variable

LAB_1DB0
	ADD.l		d1,Svarl(a3)		* set new variable memory start
LAB_1DB1
	ADD.l		d1,Sstrl(a3)		* set new start of strings
LAB_1DB2
	ADD.l		d1,Sarryl(a3)		* set new array memory start
	MOVE.l	d0,(a0)+			* save variable/function name
	MOVE.l	#$00,(a0)			* initialise variable
	BTST.l	#23,d0			* was it string
	BEQ.s		LAB_1DD7			* branch if not string

	MOVE.w	#$00,4(a0)			* else initialise string length

							* found a match for var ((Vrschl) = ptr)
LAB_1DD7
	MOVE.l	d0,d1				* ........ $....... &....... ........
	ADD.l		d1,d1				* .......$ .......& ........ .......0
	SWAP		d1				* ........ .......0 .......$ .......&
	ROR.b		#1,d1				* ........ .......0 .......$ &.......
	LSR.w		#1,d1				* ........ .......0 0....... $&.....�.
	AND.b		#$C0,d1			* mask the type bits
	MOVE.b	d1,Dtypef(a3)		* save the data type

	MOVE.b	#$00,Sufnxf(a3)		* clear FN flag byte

* if you want a non existant variable to return a null value then set the novar
* value at the top of this file to some non zero value

 ifne	novar

	MOVEQ		#-1,d0			* return variable found

 endc

	RTS


*************************************************************************************
*
* set-up array pointer, d0, to first element in array
* set d0 to (a0)+2*(Dimcnt)+$0A

LAB_1DE6
	MOVEQ		#5,d0				* set d0 to 5 (*2 = 10, later)
	ADD.b		Dimcnt(a3),d0		* add # of dimensions (1, 2 or 3)
	ADD.l		d0,d0				* *2 (bytes per dimension size)
	ADD.l		a0,d0				* add array start pointer
	RTS


*************************************************************************************
*
* evaluate unsigned integer expression

LAB_EVIN
	BSR		LAB_IGBY			* increment & scan memory
	BSR		LAB_EVNM			* evaluate expression & check is numeric,
							* else do type mismatch


*************************************************************************************
*
* evaluate positive integer expression, result in d0 and Itemp

LAB_EVPI
	TST.b		FAC1_s(a3)			* test FAC1 sign (b7)
	BMI		LAB_FCER			* do function call error if -ve


*************************************************************************************
*
* evaluate integer expression, no sign check
* result in d0 and Itemp, exit with flags set correctly

LAB_EVIR
	CMPI.b	#$A0,FAC1_e(a3)		* compare exponent with exponent = 2^32 (n>2^31)
	BCS		LAB_2831			* convert FAC1 floating to fixed
							* result in d0 and Itemp
	BNE		LAB_FCER			* if > do function call error, then warm start

	TST.b		FAC1_s(a3)			* test sign of FAC1
	BPL		LAB_2831			* if +ve then ok

	MOVE.l	FAC1_m(a3),d0		* get mantissa
	NEG.l		d0				* do -d0
	BVC		LAB_FCER			* if not $80000000 do FC error, then warm start

	MOVE.l	d0,Itemp(a3)		* else just set it
	RTS


*************************************************************************************
*
* find or make array

LAB_1E17
	MOVE.w	Defdim(a3),-(sp)		* get DIM flag and data type flag (word in mem)
	MOVEQ		#0,d1				* clear dimensions count

* now get the array dimension(s) and stack it (them) before the data type and DIM flag

LAB_1E1F
	MOVE.w	d1,-(sp)			* save dimensions count
	MOVE.l	Varname(a3),-(sp)		* save variable name
	BSR.s		LAB_EVIN			* evaluate integer expression

	SWAP		d0				* swap high word to low word
	TST.w		d0				* test swapped high word
	BNE		LAB_ABER			* if too big do array bounds error

	MOVE.l	(sp)+,Varname(a3)		* restore variable name
	MOVE.w	(sp)+,d1			* restore dimensions count
	MOVE.w	(sp)+,d0			* restore DIM and data type flags
	MOVE.w	Itemp+2(a3),-(sp)		* stack this dimension size
	MOVE.w	d0,-(sp)			* save DIM and data type flags
	ADDQ.w	#1,d1				* increment dimensions count
	BSR		LAB_GBYT			* scan memory
	CMP.b		#$2C,d0			* compare with ","
	BEQ.s		LAB_1E1F			* if found go do next dimension

	MOVE.b	d1,Dimcnt(a3)		* store dimensions count
	BSR		LAB_1BFB			* scan for ")", else do syntax error/warm start
	MOVE.w	(sp)+,Defdim(a3)		* restore DIM and data type flags (word in mem)
	MOVEA.l	Sarryl(a3),a0		* get array mem start

* now check to see if we are at the end of array memory (we would be if there were
* no arrays).

LAB_1E5C
	MOVE.l	a0,Astrtl(a3)		* save as array start pointer
	CMPA.l	Earryl(a3),a0		* compare with array mem end
	BEQ.s		LAB_1EA1			* go build array if not found

							* search for array
	MOVE.l	(a0),d0			* get this array name
	CMP.l		Varname(a3),d0		* compare with array name
	BEQ.s		LAB_1E8D			* array found so branch

							* no match
	MOVEA.l	4(a0),a0			* get this array size
	ADDA.l	Astrtl(a3),a0		* add to array start pointer
	BRA.s		LAB_1E5C			* go check next array

							* found array, are we trying to dimension it?
LAB_1E8D
	TST.b		Defdim(a3)			* are we trying to dimension it?
	BNE		LAB_DDER			* if so do double dimension error/warm start

* found the array and we're not dimensioning it so we must find an element in it

	BSR		LAB_1DE6			* set data pointer, d0, to the first element
							* in the array
	ADDQ.w	#8,a0				* index to dimension count
	MOVE.w	(a0)+,d0			* get no of dimensions
	CMP.b		Dimcnt(a3),d0		* compare with dimensions count
	BEQ		LAB_1F28			* found array so go get element

	BRA		LAB_WDER			* else wrong so do "Wrong dimensions" error

							* array not found, so possibly build it
LAB_1EA1
	TST.b		Defdim(a3)			* test the default DIM flag
	BEQ		LAB_UDER			* if default flag is clear then we are not
							* explicitly dimensioning an array so go
							* do an "Undimensioned array" error

	BSR		LAB_1DE6			* set data pointer, d0, to the first element
							* in the array
	MOVE.l	Varname(a3),d0		* get array name
	MOVE.l	d0,(a0)+			* save array name
	MOVEQ		#4,d1				* set 4 bytes per element
	BTST.l	#23,d0			* test if string array
	BEQ.s		LAB_1EDF			* branch if not string

	MOVEQ		#6,d1				* else 6 bytes per element
LAB_1EDF
	MOVE.l	d1,Asptl(a3)		* set array data size (bytes per element)
	MOVE.b	Dimcnt(a3),d1		* get dimensions count
	ADDQ.w	#4,a0				* skip the array size now (don't know it yet!)
	MOVE.w	d1,(a0)+			* set array's dimensions count

* now calculate the array data space size

LAB_1EC0

* If you want arrays to dimension themselves by default then comment out the test
* above and uncomment the next three code lines and the label LAB_1ED0
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
