DigicoolThings/MECB/MECB_68008_CPU/Tutor/combo_68k.asm

* THIS VERSION MODIFIED FOR TEESSIDE X68K PC-2.2 CROSS ASSEMBLER
*     ftp://nyquist.ee.ualberta.ca/pub/motorola/m68k/x68k.zip
*
*     CHANGES FROM ORIGINAL MOTOROLA SOURCE:
*         MANY "MOVE.L" CHANGED TO "MOVEQ"
*             SIMILAR CHANGES ON A FEW OTHER COMMANDS WHERE
*             X68K DOES NOT AUTOMATICALLY MOTOROLA-IZE.
*         X68K HANDLES CHARACTER CONSTANTS DIFFERENTLY
*             DC.W  '1'    -->  $3100  (GOOD)
*             DC.W  '1'+0  -->  $0031  (WHAT!)
*     ONE DIFFERENCE REMAINS IN A "DON'T CARE" BYTE
*         $008FE0 1A3C00FF  MOVE.B  #-1,D5
*                     ^^ $00 INSTEAD OF $FF
* SUBSEQUENTLY MODIFIED FOR USE ON DIGICOOL THING MECB 68008 (EMULATED)

*=======================================================================*
* MOTOROLA EDUCATION COMPUTER BOARD ROM PROGRAM "TUTOR"  REVISION # 1.3 *
*=======================================================================*

* MACROS


ADDR2MEM MACRO
         PEA     \1(PC)         MOVE ADDRESS TO MEMORY; POSITION
         MOVE.L  (A7)+,\2       INDEPENDANT = TO "MOVE.L #\1,\2"
         ENDM


SAVEREGS MACRO
         MOVE.L  A7,REGA7       SAVE STACK POINTER
         LEA     SV\@(PC),A7    A7 = RETURN ADDRESS (FOR CALL TO SAVE)
         MOVE.L  A7,TEMP        TEMP = RETURN ADDRESS
         BRA     SAVE           BSR WITHOUT USING STACK
SV\@     DS      0
         ENDM




*-------------------------------------------------------------------------

RAM_START EQU   $0000

* EQUATES (in alphabetical order)

BELL     EQU     $07
BLANK    EQU     $20
BKPOINT  EQU     $4AFB
BUFFSIZE EQU     $80
BUFSIZE  EQU     80
CR       EQU     $0D
CTLD     EQU     $04
CTLH     EQU     $08
CTLW     EQU     $17
CTLX     EQU     $18
DEL      EQU     $7F
DELAYC1  EQU     $1000
EOT      EQU     $04
LF       EQU     $0A
LOCVARSZ EQU     16
RESET    EQU     $03            MASTER RESET FOR ACIA

LTIME    SET     205000         LONG TIMER 5 SEC @ 8 MHZ
STIME    SET     41000          SHORT TIMER  100 MLS @ 8 MHZ

PDI1     SET     $0F0000        PARALLEL PORT ADDRESS
PITCDDR  SET     $0F0009        PORT C DATA DIRECTION REGISTER
PITPCDR  SET     $0F0019        PORT C DATA REGISTER
PITTCR   SET     $0F0021        TIMER CONTROL REGISTER
PSTATUS  SET     $B             PRINTER STATUS
PBDATA   SET     3              PRINTER CONTROL--BUSY,PAPER,SELECT
PDATA    SET     1              PRINTER DATA
SER1     SET     $300008        TERMINAL
SER2     SET     $300008        SERIAL PORT2 ADDRESS


*-------------------------------------------------------------------------
* File ARAM      DATA VARIABLES                                   05/10/82

****************************************************************
*  N O T E:  Ram locations:   starting at zero                 *
****************************************************************

         ORG     RAM_START

*                               DEC HEX  DESCRIPTION
         DS.L    1              0   $00  AREA OVERLAID BY ROM SR
         DS.L    1              1   $01  AND PC


AV2      DS.L    1              2   $02  BUS ERROR            "BUS "
AV3      DS.L    1              3   $03  ADDRESS ERROR        "ADDR"
AV4      DS.L    1              4   $04  ILL INSTRUCTION      "OPCO"
         DS.L    1              5   $05  DIVIDE BY ZERO       "DIV0"
         DS.L    1              6   $06  CHECK TRAP           "CHCK"
         DS.L    1              7   $07  TRAP V               "TP V"
AV8      DS.L    1              8   $08  PRIVILEDGE VIOLATION "PRIV"
AV9      DS.L    1              9   $09  TRACE
         DS.L    1              10  $0A  1010 LINE EMULATION  "1010"
AV11     DS.L    1              11  $0B  1111 LINE EMULATION  "1111"
AV12     DS.L    1              12  $0C  USED AS TEMPORARY STORAGE FOR VECTOR MSGS.
         DS.L    1              13  $0D  NOT USED
         DS.L    1              14  $0E
         DS.L    1              15  $0F
         DS.L    1              16  $10
         DS.L    1              17  $11
         DS.L    1              18  $12
         DS.L    1              19  $13
         DS.L    1              20  $14
         DS.L    1              21  $15
         DS.L    1              22  $16
         DS.L    1              23  $17
AV24     DS.L    1              24  $18   0  AUTO VECTORS     "SPUR"
         DS.L    1              25  $19   1                   "AV#1"
         DS.L    1              26  $1A   2                   "AV#2"   TEST BUTTON
         DS.L    1              27  $1B   3                   "AV#3"
         DS.L    1              28  $1C   4                   "AV#4"
         DS.L    1              29  $1D   5                   "AV#5"
         DS.L    1              30  $1E   6                   "AV#6"
AV31     DS.L    1              31  $1F   7                   "AV#7   [ABORT BUTTON]
         DS.L    1              32  $20   TRAP  0             "UT 0"
         DS.L    1              33  $21   TRAP  1             "UT 1"
         DS.L    1              34  $22   TRAP  2             "UT 2"
         DS.L    1              35  $23   TRAP  3             "UT 3"
         DS.L    1              36  $24   TRAP  4             "UT 4"
         DS.L    1              37  $25   TRAP  5             "UT 5"
         DS.L    1              38  $26   TRAP  6             "UT 6"
         DS.L    1              39  $27   TRAP  7             "UT 7"
         DS.L    1              40  $28   TRAP  8             "UT 8"
         DS.L    1              41  $29   TRAP  9             "UT 9"
         DS.L    1              42  $2A   TRAP 10             "UT A"
         DS.L    1              43  $2B   TRAP 11             "UT B"
         DS.L    1              44  $2C   TRAP 12             "UT C"
         DS.L    1              45  $2D   TRAP 13             "UT D"
AV46     DS.L    1              46  $2E   TRAP 14             "UT E"
AV47     DS.L    1              47  $2F   TRAP 15             "UT F"
AV48     DS.L    1              48  $30
         DS.L    1              49  $31
         DS.L    1              50  $32
         DS.L    1              51  $33
         DS.L    1              52  $34
         DS.L    1              53  $35
         DS.L    1              54  $36
         DS.L    1              55  $37
         DS.L    1              56  $38
         DS.L    1              57  $39
         DS.L    1              58  $3A
         DS.L    1              59  $3B
         DS.L    1              60  $3C
         DS.L    1              61  $3D
         DS.L    1              62  $3E
         DS.L    1              63  $3F
         DS.L    1              64  $40
         DS.L    1              65  $41
         DS.L    1              66  $42
         DS.L    1              67  $43
         DS.L    1              68  $44
         DS.L    1              69  $45
         DS.L    1              70  $46
         DS.L    1              71  $47
         DS.L    1              72  $48
         DS.L    1              73  $49
         DS.L    1              74  $4A
         DS.L    1              75  $4B
         DS.L    1              76  $4C
         DS.L    1              77  $4D
         DS.L    1              78  $4E
         DS.L    1              79  $4F
         DS.L    1              80  $50
         DS.L    1              81  $51
         DS.L    1              82  $52
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
         DS.L    1              186  $BA
         DS.L    1              187  $BB
         DS.L    1              188  $BC
         DS.L    1              189  $BD
         DS.L    1              190  $BE
         DS.L    1              191  $BF
         DS.L    1              192  $C0
         DS.L    1              193  $C1
         DS.L    1              194  $C2
         DS.L    1              195  $C3
         DS.L    1              196  $C4
         DS.L    1              197  $C5
         DS.L    1              198  $C6
         DS.L    1              199  $C7
         DS.L    1              200  $C8
         DS.L    1              201  $C9
         DS.L    1              202  $CA
         DS.L    1              203  $CB
         DS.L    1              204  $CC
         DS.L    1              205  $CD
         DS.L    1              206  $CE
         DS.L    1              207  $CF
         DS.L    1              208  $D0
         DS.L    1              209  $D1
         DS.L    1              210  $D2
         DS.L    1              211  $D3
         DS.L    1              212  $D4
         DS.L    1              213  $D5
         DS.L    1              214  $D6
         DS.L    1              215  $D7
         DS.L    1              216  $D8
         DS.L    1              217  $D9
         DS.L    1              218  $DA
         DS.L    1              219  $DB
         DS.L    1              220  $DC
         DS.L    1              221  $DD
         DS.L    1              222  $DE
         DS.L    1              223  $DF
         DS.L    1              224  $E0
         DS.L    1              225  $E1
         DS.L    1              226  $E2
         DS.L    1              227  $E3
         DS.L    1              228  $E4
         DS.L    1              229  $E5
         DS.L    1              230  $E6
         DS.L    1              231  $E7
         DS.L    1              232  $E8
         DS.L    1              233  $E9
         DS.L    1              234  $EA
         DS.L    1              235  $EB
         DS.L    1              236  $EC
         DS.L    1              237  $ED
         DS.L    1              238  $EE
         DS.L    1              239  $EF
         DS.L    1              240  $F0
         DS.L    1              241  $F1
         DS.L    1              242  $F2
         DS.L    1              243  $F3
         DS.L    1              244  $F4
         DS.L    1              245  $F5
         DS.L    1              246  $F6
         DS.L    1              247  $F7
         DS.L    1              248  $F8
         DS.L    1              249  $F9
         DS.L    1              250  $FA
         DS.L    1              251  $FB
         DS.L    1              252  $FC
         DS.L    1              253  $FD            3RD
         DS.L    1              254  $FE            2ND
         DS.L    1              255  $FF VECTOR FOR 1ST IPC DISK CONTROLLER


*  PSEUDO REGISTERS

REGPC    DS.L    1              USERS PROGRAM COUNTER
REGSR    DS.L    1              USERS CONDITION CODES
REGS     DS.L    8              D REGISTERS
         DS.L    7              A0 THROUGH A6 REGISTERS
REGA7    DS.L    1              A7 REGISTER
REGUS    DS.L    1              USER STACK



****************************************************************
*              WORKING STORAGE                                 *
*  NOTE: SUBROUTINE "INITHRAM" ZEROES RAM...                   *
*        FROM "BEGHRAM" THROUGH "ENDHRAM" WHEN IT IS EXECUTED  *
****************************************************************

BEGHRAM  DS      0              INITIALIZE STARTS HERE

OFFSET   DS.L    8              ASSUMED OFFSETS (VIA "R@" FORMAT)
MEMSIZE  DS.L    1              MEMORY SIZE IN BYTES
BPADD    DS.L    8              BREAKPOINT ADDRESSES
BPTILL   DS.L    1              TEMPORARY BREAKPOINT
BPCNT    DS.L    9              BREAKPOINT COUNTS
BPDATA   DS.W    9              HOLD USER WORDS REPLACED BY TRAP IN SET BP
BERRD    DS.L    2              SPECIAL DATA FOR BUS AND ADDR ERROR EXCEPTIONS
SAVEAV4  DS.L    1              HOLDS USER'S AV4 VECTOR (WE USE FOR BP)
TEMP     DS.L    1              TEMP
TRACECNT DS.L    1              TRACE COUNTER (-1=TRACE 1 & RUN)
TRACEON  DS.W    1              FLAG FOR TRACE ON
BPSTATUS DS.W    1              1=PB ARE IN  0=ARE OUT OF MEMORY
ECHOPT1  DS.L    1              ECHO FLAG TO PORT ONE



* THE FOLLOWING MUST REMAIN AS IS
*  User documentation DEPENDS upon it!
*
OPTIONS  DS.W    0              FORCE WORD BOUNDRY
         DS.B    1              X-ON CHARACTER
         DS.B    1              X-OFF CHARACTER
         DS.B    1              NO NO-AUTO LINEFEED
         DS.B    1              SHORT FORM REGISTER DISPLAY
         DS.B    1              TM  trailing character
         DS.B    1              TM  exit character

XONOFF   EQU     OPTIONS
TMCHARS  EQU     OPTIONS+4

* END of as is section


***************************
* TARGET SUPERVISOR STACK *
***************************

         DS.L    20
SSA7     DS.L    1



**************
* I/O BUFFER *
**************

BUFFER   DS.B    BUFFSIZE

DUMPTEMP DS.B    80             HEADER TEMP BUFFER

SCREEN1  DS.L    1              PRINT THIS BEFORE TRACE DISPLAY
SCREEN2  DS.L    1              PRINT THIS AFTER TRACE DISPLAY

NULLPADS DS.B    2              CHARACTER NULL PADS
CRPADS   DS.B    2              CARRIAGE RETURN NULL PADS

OUTTO    DS.L    1              HOLDS ADDRESS OF OUTPUT ROUTINE
INFROM   DS.L    1              HOLDS ADDRESS OF INPUT ROUTINE
ALTSER1  DS.L    1              ALTERNATE SERIAL PORT#1
ALTSER2  DS.L    1              ALTERNATE SERIAL PORT#2
INPORT1  DS.L    1              INPUT ROUTINE ADDRESS
OUTPORT1 DS.L    1              ADDRESS FOR OUPUT ROUTINE
INPORT2  DS.L    1              ADDRESS FOR INPUT ROUTINE
OUTPORT2 DS.L    1              FOR OUTPURT ROUTINE
INPORT3  DS.L    1              THIS MIGHT BE FOR TAPE
OUTPORT3 DS.L    1              THIS MIGHT BE FOR PRINTER
INPORT4  DS.L    1              CASSETTE
OUTPORT4 DS.L    1              CASSETTE
MD1CON   DS.W    1              ACIA PROFILE (PORT1/PORT2)
PDIPORT  DS.L    1              PDIPORT ADDRESS
CRTPNT   DS.W    1              OUTPUT TO PRINTER AND CRT
TAPENULS DS.B    1              NULLS FOR CASSETTE

         DS.B    1              PAD BYTE

CTLINK   DS.L    1              POINTER TO FIRST TABLE



ENDHRAM  DS.W    0              MUST START ON WORD BOUNDRY



*********************
* SYSTEM STACK AREA *
*********************

         DS.W    0              FORCE ON WORD BOUNDRY
         DS.B    300            ROOM FOR STACK
SYSTACK  DS.W    1              START OF STACK (ADDRESS DECREASES)
         DS.B    4              STRETCHED STACK (USED BY 'SAVE')

         DS.B    120            EXTENDED AREA USED IF DISASSEMBLER

         DS.B    0              LAST LOW MEMORY LOCATION USED + 1


*-------------------------------------------------------------------------

*CODE68K
*                               OFFSET  0
ESKB     EQU     $00000000      DS      0
TDATA    EQU     $00000000      DS.B    10
TNB      EQU     $0000000A      DS.B    1
TLSPEC   EQU     $0000000B      DS.B    1
TLENGTH  EQU     $0000000C      DS.W    1
PCOUNTER EQU     $0000000E      DS.L    1
PTROP    EQU     $00000012      DS.L    1              POINTER TO OPERAND
PENDOP   EQU     $00000016      DS.L    1              POINTER END OF OPERAND
PTRBUFE  EQU     $0000001A      DS.L    1              POINTER TO END OF FORMATED SOURCE
LINK     EQU     $0000001E      DS.L    1              SAVE FOR UNLINK
ESKE     EQU     $00000022      DS.B    0


*DCODE68K
*                               OFFSET  -LOCVARSZ
DDATA    EQU     $FFFFFFF0      DS.L    3
HISPC    EQU     $FFFFFFFC      DS.L    1


*LOAD
*                               OFFSET  -((BUFFSIZE/2)+4)
CC       EQU     $FFFFFFBC      DS.L    1              CC (BYTE COUNT)
ADDRESS  EQU     $FFFFFFC0      DS.L    1              ADDRESS + OFFSET
LDATA    EQU     $FFFFFFC4      DS.B    1




*-------------------------------------------------------------------------
* File B         Init Vectors+Ram                                 05/29/82

         ORG     $200000

FIRST    DC.L    REGA7              ; 0   $00  SR
         DC.L    START              ; 1   $01  RESET
         DC.L    BERRMSG            ; 2   $02  BUS ERROR            "BUS "
         DC.L    ADDRMSG            ; 3   $03  ADDRESS ERROR        "ADDR"
         DC.L    CHKBP              ; 4   $04  ILL INSTRUCTION      "OPCO"
         DC.L    VECT5              ; 5   $05  DIVIDE BY ZERO       "DIV0"
         DC.L    VECT6              ; 6   $06  CHECK TRAP           "CHCK"
         DC.L    VECT7              ; 7   $07  TRAP V               "TP V"
         DC.L    VECT8              ; 8   $08  PRIVILEDGE VIOLATION "PRIV"
         DC.L    TRACE              ; 9   $09  TRACE
         DC.L    VECT10             ; 10  $0A  1010 LINE EMULATION  "1010"
         DC.L    VECT11             ; 11  $0B  1111 LINE EMULATION  "1111"
         DS.L    1              12  $0C  UNASSIGNED
         DS.L    1              13  $0D  UNASSIGNED
         DS.L    1              14  $0E  UNASSIGNED
         DS.L    1              15  $0F  UNINITIALIZED INTERRUPT VECTOR
         DS.L    1              16  $10  UNASSIGNED
         DS.L    1              17  $11  UNASSIGNED
         DS.L    1              18  $12  UNASSIGNED
         DS.L    1              19  $13  UNASSIGNED
         DS.L    1              20  $14  UNASSIGNED
         DS.L    1              21  $15  UNASSIGNED
         DS.L    1              22  $16  UNASSIGNED
         DS.L    1              23  $17  UNASSIGNED
         DC.L    VECT24         24  $18  SPURIOUS INTERRUPT
         DC.L    VECT25         25  $19  LEVEL 1 INTERRUPT
         DC.L    VECT26         26  $1A  LEVEL 2 INTERRUPT
         DC.L    VECT27         27  $1B  LEVEL 3 INTERRUPT
         DC.L    VECT28         28  $1C  LEVEL 4 INTERRUPT
         DC.L    VECT29         29  $1D  LEVEL 5 INTERRUPT
         DC.L    VECT30         30  $1E  LEVEL 6 INTERRUPT
         DC.L    ABORTB         31  $1F  LEVEL 7 INTERRUPT
         DC.L    VECT32         32  $20   TRAP  0
         DC.L    VECT33         33  $21   TRAP  1
         DC.L    VECT34         34  $22   TRAP  2
         DC.L    VECT35         35  $23   TRAP  3
         DC.L    VECT36         36  $24   TRAP  4
         DC.L    VECT37         37  $25   TRAP  5
         DC.L    VECT38         38  $26   TRAP  6
         DC.L    VECT39         39  $27   TRAP  7
         DC.L    VECT40         40  $28   TRAP  8
         DC.L    VECT41         41  $29   TRAP  9
         DC.L    VECT42         42  $2A   TRAP 10
         DC.L    VECT43         43  $2B   TRAP 11
         DC.L    VECT44         44  $2C   TRAP 12
         DC.L    VECT45         45  $2D   TRAP 13
         DC.L    TRAP14         46  $2E   TRAP 14
         DC.L    VECT47         47  $2F   TRAP 15
         DS.L    1              48  $30   UNASSIGNED
         DS.L    1              49  $31   UNASSIGNED
         DS.L    1              50  $32   UNASSIGNED
         DS.L    1              51  $33   UNASSIGNED
         DS.L    1              52  $34   UNASSIGNED
         DS.L    1              53  $35   UNASSIGNED
         DS.L    1              54  $36   UNASSIGNED
         DS.L    1              55  $37   UNASSIGNED
         DS.L    1              56  $38   UNASSIGNED
         DS.L    1              57  $39   UNASSIGNED
         DS.L    1              58  $3A   UNASSIGNED
         DS.L    1              59  $3B   UNASSIGNED
         DS.L    1              60  $3C   UNASSIGNED
         DS.L    1              61  $3D   UNASSIGNED
         DS.L    1              62  $3E   UNASSIGNED
         DS.L    1              63  $3F   UNASSIGNED
         DS.L    1              64  $40   USER INTERRUPT
         DS.L    1              65  $41   USER INTERRUPT
         DS.L    1              66  $42   USER INTERRUPT
         DS.L    1              67  $43   USER INTERRUPT
         DS.L    1              68  $44   USER INTERRUPT
         DS.L    1              69  $45   USER INTERRUPT
         DS.L    1              70  $46   USER INTERRUPT
         DS.L    1              71  $47   USER INTERRUPT
         DS.L    1              72  $48   USER INTERRUPT
         DS.L    1              73  $49   USER INTERRUPT
         DS.L    1              74  $4A   USER INTERRUPT
         DS.L    1              75  $4B   USER INTERRUPT
         DS.L    1              76  $4C   USER INTERRUPT
         DS.L    1              77  $4D   USER INTERRUPT
         DS.L    1              78  $4E   USER INTERRUPT
         DS.L    1              79  $4F   USER INTERRUPT
         DS.L    1              80  $50   USER INTERRUPT
         DS.L    1              81  $51   USER INTERRUPT
         DS.L    1              82  $52   USER INTERRUPT
         DS.L    1              83  $53   USER INTERRUPT
         DS.L    1              84  $54   USER INTERRUPT
         DS.L    1              85  $55   USER INTERRUPT
         DS.L    1              86  $56   USER INTERRUPT
         DS.L    1              87  $57   USER INTERRUPT
         DS.L    1              88  $58   USER INTERRUPT
         DS.L    1              89  $59   USER INTERRUPT
         DS.L    1              90  $5A   USER INTERRUPT
         DS.L    1              91  $5B   USER INTERRUPT
         DS.L    1              92  $5C   USER INTERRUPT
         DS.L    1              93  $5D   USER INTERRUPT
         DS.L    1              94  $5E   USER INTERRUPT
         DS.L    1              95  $5F   USER INTERRUPT
         DS.L    1              96  $60   USER INTERRUPT
         DS.L    1              97  $61   USER INTERRUPT
         DS.L    1              98  $62   USER INTERRUPT
         DS.L    1              99  $63   USER INTERRUPT
         DS.L    1              100  $64  USER INTERRUPT
         DS.L    1              101  $65  USER INTERRUPT
         DS.L    1              102  $66  USER INTERRUPT
         DS.L    1              103  $67  USER INTERRUPT
         DS.L    1              104  $68  USER INTERRUPT
         DS.L    1              105  $69  USER INTERRUPT
         DS.L    1              106  $6A  USER INTERRUPT
         DS.L    1              107  $6B  USER INTERRUPT
         DS.L    1              108  $6C  USER INTERRUPT
         DS.L    1              109  $6D  USER INTERRUPT
         DS.L    1              110  $6E  USER INTERRUPT
         DS.L    1              111  $6F  USER INTERRUPT
         DS.L    1              112  $70  USER INTERRUPT
         DS.L    1              113  $71  USER INTERRUPT
         DS.L    1              114  $72  USER INTERRUPT
         DS.L    1              115  $73  USER INTERRUPT
         DS.L    1              116  $74  USER INTERRUPT
         DS.L    1              117  $75  USER INTERRUPT
         DS.L    1              118  $76  USER INTERRUPT
         DS.L    1              119  $77  USER INTERRUPT
         DS.L    1              120  $78  USER INTERRUPT
         DS.L    1              121  $79  USER INTERRUPT
         DS.L    1              122  $7A  USER INTERRUPT
         DS.L    1              123  $7B  USER INTERRUPT
         DS.L    1              124  $7C  USER INTERRUPT
         DS.L    1              125  $7D  USER INTERRUPT
         DS.L    1              126  $7E  USER INTERRUPT
         DS.L    1              127  $7F  USER INTERRUPT
         DS.L    1              128  $80  USER INTERRUPT
         DS.L    1              129  $81  USER INTERRUPT
         DS.L    1              130  $82  USER INTERRUPT
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
         DS.L    1              204  $CC  USER INTERRUPT
         DS.L    1              205  $CD  USER INTERRUPT
         DS.L    1              206  $CE  USER INTERRUPT
         DS.L    1              207  $CF  USER INTERRUPT
         DS.L    1              208  $D0  USER INTERRUPT
         DS.L    1              209  $D1  USER INTERRUPT
         DS.L    1              210  $D2  USER INTERRUPT
         DS.L    1              211  $D3  USER INTERRUPT
         DS.L    1              212  $D4  USER INTERRUPT
         DS.L    1              213  $D5  USER INTERRUPT
         DS.L    1              214  $D6  USER INTERRUPT
         DS.L    1              215  $D7  USER INTERRUPT
         DS.L    1              216  $D8  USER INTERRUPT
         DS.L    1              217  $D9  USER INTERRUPT
         DS.L    1              218  $DA  USER INTERRUPT
         DS.L    1              219  $DB  USER INTERRUPT
         DS.L    1              220  $DC  USER INTERRUPT
         DS.L    1              221  $DD  USER INTERRUPT
         DS.L    1              222  $DE  USER INTERRUPT
         DS.L    1              223  $DF  USER INTERRUPT
         DS.L    1              224  $E0  USER INTERRUPT
         DS.L    1              225  $E1  USER INTERRUPT
         DS.L    1              226  $E2  USER INTERRUPT
         DS.L    1              227  $E3  USER INTERRUPT
         DS.L    1              228  $E4  USER INTERRUPT
         DS.L    1              229  $E5  USER INTERRUPT
         DS.L    1              230  $E6  USER INTERRUPT
         DS.L    1              231  $E7  USER INTERRUPT
         DS.L    1              232  $E8  USER INTERRUPT
         DS.L    1              233  $E9  USER INTERRUPT
         DS.L    1              234  $EA  USER INTERRUPT
         DS.L    1              235  $EB  USER INTERRUPT
         DS.L    1              236  $EC  USER INTERRUPT
         DS.L    1              237  $ED  USER INTERRUPT
         DS.L    1              238  $EE  USER INTERRUPT
         DS.L    1              239  $EF  USER INTERRUPT
         DS.L    1              240  $F0  USER INTERRUPT
         DS.L    1              241  $F1  USER INTERRUPT
         DS.L    1              242  $F2  USER INTERRUPT
         DS.L    1              243  $F3  USER INTERRUPT
         DS.L    1              244  $F4  USER INTERRUPT
         DS.L    1              245  $F5  USER INTERRUPT
         DS.L    1              246  $F6  USER INTERRUPT
         DS.L    1              247  $F7  USER INTERRUPT
         DS.L    1              248  $F8  USER INTERRUPT
         DS.L    1              249  $F9  USER INTERRUPT
         DS.L    1              250  $FA  USER INTERRUPT
         DS.L    1              251  $FB  USER INTERRUPT
         DS.L    1              252  $FC  USER INTERRUPT
         DS.L    1              253  $FD  USER INTERRUPT
         DS.L    1              254  $FE  USER INTERRUPT
         DS.L    1              255  $FF  USER INTERRUPT

V2       BRA     TRACE


**********************************
* INITIALIZE HIGH RAM SUBROUTINE *
**********************************

INITHRAM LEA     BEGHRAM,A0     START OF WORK RAM (PAST REGISTERS)
         MOVE.L  #(ENDHRAM-BEGHRAM),D0  BYTES TO ZERO
         CLR.L   D1
INIT     MOVE.B  D1,(A0)+       ZERO MEMORY
         SUBQ.L  #1,D0
         BNE     INIT

         ADDR2MEM BERRMSG,AV2   POINT AT BUS TRAP ERROR MESSAGE ROUTINE

         ADDR2MEM ADDRMSG,AV3   POINT AT ADDRESS TRAP ERROR MESSAGE ROUTINE

         RTS


****************************************************
* SPECIAL HANDLING FOR BUS ERROR AND ADDRESS ERROR *
****************************************************

BERRMSG  MOVE.L  #'BUS ',$30

         BRA.S   VECTBE

ADDRMSG  MOVE.L  #'ADDR',$30


VECTBE   MOVE.L  (A7)+,BERRD
         MOVE.L  (A7)+,BERRD+4

         SAVEREGS
         BSR     FIXBUF
         MOVE.W  #$D0A,(A6)+
         MOVE.W  BERRD,D0
         BSR     PNT4HX         FORMAT FUNCTION CODE

         MOVE.B  #BLANK,(A6)+   SPACE
         MOVE.L  BERRD+2,D0
         BSR     PNT8HX         FORMAT ACCESS ADDRESS

         MOVE.B  #BLANK,(A6)+   SPACE
         MOVE.W  BERRD+6,D0
         BSR     PNT4HX         FORMAT INSTRUCTION REGISTER

         BSR     OUTPUT
         BRA     EVECT2         GO DISPLAY REGISTERS & PROMPT

MSG008   DC.B    'SYNTAX '

MSG008E  DC.B    'ERROR '

MSGEOT   DC.B    EOT

MSG021   DC.B    'WHAT',EOT

         DC.B    0              PAD BYTE


* PRINT WHAT

WHAT     LEA     MSG021(PC),A5  PRINT 'WHAT' AND ENTER MACSBUG
WHAT93   BSR.S   FIXDATA
         CLR.W   TRACEON
MSG      BSR     OUT1CR
         BRA     MACSBUG


* PRINT ERROR

ERROR    LEA     MSG008E(PC),A5
         BRA     WHAT93

SYNTAX   LEA     MSG008(PC),A5  'SYNTAX ERROR'
         BRA     WHAT93

* FORMAT PHYSICAL ADDRESS FROM (D0)
PPHY     LEA     MSG019(PC),A5
         BSR.S   FIXDATA
         BRA.S   P2PHY2

* FORMAT TWO PHYSICAL ADDRESSES FROM (A0) & (A1)
P2PHY    LEA     MSG019(PC),A5  'PHYSICAL ADDRESS='
         BSR.S   FIXDATA
         MOVE.L  A0,D0
         BSR     PNT8HX         FORMAT ADDR1
         MOVE.B  #BLANK,(A6)+   SPACE FOR FORMATING
         MOVE.L  A1,D0
P2PHY2   BSR     PNT8HX         FORMAT ADDR2
         BSR     OUT1CR         DISPLAY IT
         RTS

MSG019   DC.B    'PHYSICAL ADDRESS=',EOT





*************************************************************
* -FIXDATA- SUBROUTINE...  MOVES MESSAGE POINTED TO BY (A5) *
*                          INTO "BUFFER". EOT, ($04), ENDS  *
*                          THE MOVE. AT COMPLETION (A5) IS  *
*                          POINTING AT THE BEGINNING, (A6)  *
*                          POINTS AT END.                   *
*************************************************************

FIXDATA  LEA     BUFFER,A6
FIXDADD  CMPI.B  #EOT,(A5)
         BEQ.S   FIXD2
         MOVE.B  (A5)+,(A6)+
         BRA     FIXDADD
FIXD2    LEA     BUFFER,A5
         RTS


************************************************************
* -FIXDCRLF- SUBROUTINE INSERTS A CARRIAGE RETURN AND LINE *
*                       FEED IN FRONT OF THE TEXT, THEN    *
*                       USES THE REMAINING PORTION OF THE  *
*                       FIXDATA.                           *
************************************************************

FIXDCRLF LEA     BUFFER,A6
         MOVE.W  #$0D0A,(A6)+   CR,LF
         BRA     FIXDADD




*-------------------------------------------------------------------------
* File E         VERSAbug entry point                             01/08/81

**********************
* INITIALIZE VECTORS *
**********************
*                               Set most vectors to point at "????" routine
INITVECT LEA     8,A0           Skip (Restart) STACK & ADDRESS vectors
         LEA     ABORTE(PC),A1  A1 = "Default" TRAP ERROR routine address

INIT0    MOVE.L  A1,(A0)+       INITIALIZE VECTOR
         CMPA.L  #$400,A0       Done?
         BMI.S   INIT0          *
         RTS


* SPECIAL ENTRY THAT DOES NOT CHANGE VECTORS

START1S  MOVEM.W D0,REGSR+2     Assure good parity.
         MOVE.W  SR,REGSR+2     SAVE TARGET'S STATUS REGISTER
         MOVE.L  A7,REGA7       SAVE TARGET'S STACK
         MOVE.L  (A7),REGPC     .PROGRAM COUNTER
         LEA     REGA7,A7
         MOVEM.L D0-D7/A0-A6,-(A7) .REGISTERS
         LEA     SYSTACK,A7
         BRA     START11


************************
*    INITIALIZATION    *
************************

* SAVE PROCESSOR REGISTERS (EXCEPT A7 & PC)

START    MOVEM.W D0,REGSR+2     Assure good parity
         MOVE.W  SR,REGSR+2     SAVE STATUS REGISTER
         MOVEM.L D0-D7/A0-A6,-(A7)

         LEA     SYSTACK,A7     SET UP STACK
         MOVE.L  A7,REGA7

         CLR.L   D1
         MOVE.L  D1,REGPC       PC = 000000

         BSR     INITVECT


START11  MOVE.W  #$2700,SR      MASK OFF INTERRUPTS

         MOVE.L  USP,A0
         MOVE.L  A0,REGUS       USER STACK

         BSR     INITHRAM       ZERO (INITIALIZE) HIGH RAM


* VECTMSG.SA
         BSR     INITVMSG


* H.SA
         ADDR2MEM CHKBP,AV4     ILLEGAL INSTRUCTION


* TM.SA
         MOVE.W  #$1801,TMCHARS CNTLX,CNTL/A


* W.SA
         ADDR2MEM  ABORTB,AV31  ABORT


* Y.SA
         ADDR2MEM  OUT1CR0,OUTPORT1 INITIALIZE I/O ROUTINES
         ADDR2MEM  OUTPUT20,OUTPORT2
         ADDR2MEM  PRCRLF,OUTPORT3     PRINTER DRIVER
         ADDR2MEM  TAPEOUT,OUTPORT4    CASSETTE
         ADDR2MEM  PORTIN10,INPORT1
         ADDR2MEM  PORTIN20,INPORT2
         ADDR2MEM  PORTIN10,INPORT3
         ADDR2MEM  TAPEIN,INPORT4      CASSETTE

         MOVE.B  #8,TAPENULS    NULLS FOR CASSETTE
         MOVE.L  #PDI1,PDIPORT  PRINTER


*        INITIALIZE MC68230 PI/T
         MOVE.L  #PDI1,A0       BASE ADDRESS OF PI/T
         MOVE.L  #$0000FF00,D0
         MOVEP.L D0,1(A0)

*        SELECT MODE 0
*        IRQ'S INACTIVATED
*        PORT A--ALL BITS OUTPUTS
*        PORT B--ALL BITS INPUTS

         MOVE.B  #$60,13(A0)    SUBMODE 01 FOR PORT A; INTERLOCKED HANDS
         MOVE.B  #$A0,15(A0)    SUBMODE 1X FOR PORT B
         MOVE.B  #$30,1(A0)     ENABLE HANDSHAKE LINES
         MOVE.B  #$A8,15(A0)    RESET AND INIT PRINTER
         MOVE.L  #PDI1+$10,PDIPORT

         MOVE.B  #$A0,15(A0)    CLEAR INIT

* INITIALIZE THE PDI'S

         MOVE.W  #$5151,MD1CON
         BSR     INITSER        RESET & PROGRAM PDI

* INITIALIZE XON/XOFF (READER ON / READER OFF)
*            AUTO-LINE FEED OVERRIDE

         MOVE.L  #$00000000,XONOFF



* TRAP14.SA
         ADDR2MEM  TRAP14,AV46
         MOVE.L  #(254<<24)+CT,CTLINK





************************************************************************
*                    V E R S I O N   N U M B E R   A N D   P R O M P T *
************************************************************************

MACSBUG  MOVE.W  #$2700,SR      MASK OFF INTERRUPTS
         LEA     SYSTACK,A7     RESTORE SYSTEM STACK
         BSR     SWAPOUT        GET BP OUT OF USER MEMORY

         CLR.L   BPTILL         GET RID OF 'TILL' BREAKPOINT
         CLR.L   OUTTO          INITIALIZE I/O TO DEFAULT
         CLR.L   INFROM         INITIALIZE I/O TO DEFAULT
         CLR.B   ECHOPT1        NO ECHO TO PORT1

         LEA     MSG001(PC),A5  > (Prompt)
         BSR     FIXDATA

         TST.W   TRACEON        SEE IF IN TRACE MODE
         BEQ.S   MACSBUG1
         MOVE.B  #':',(A6)+     IN TRACE MODE
MACSBUG1 MOVE.B  #'>',(A6)+     PROMPT
         MOVE.B  #BLANK,(A6)+   .. SPACE
         BSR     OUTPUT         GO PRINT IT

* INPUT LINE
         BSR     FIXBUF         GET READY FOR INPUT
         BSR     PORTIN1        GET A COMMAND
DECODE6  MOVE.B  #BLANK,(A6)    BLANK OUT END+1

*  DECODE A COMMAND
*
*  DECODE SPECIAL CHARACTER USAGE:
*    LEADING SPACES IGNORED
*    LEADING NULLS IGNORED
*    IF SECOND CHAR  *  CHAR CAN BE ANY CHAR

         CMP.L   A6,A5          SEE IF ANYTHING ENTERED
         BMI.S   DECODE1
         TST.W   TRACEON        SEE IF IN TRACE MODE
         BNE     TCMDHOT        DIRECT TO TRACE 1 COMMAND

DECODE1  CMP.L   A6,A5          SEE IF AT END OF BUFFER
         BHI     WHAT           GO TO 'WHAT' IF CONFUSED
         MOVE.B  (A5),D0        GRAB FIRST CHARACTER
         CMPI.B  #'*',D0        SEND LINE COMMAND
         BNE.S   DECODE10
         ADDQ.L  #1,A5          GET PAST PHOENY PROMPT
         BSR     OUTPUT2        SEND LINE+CR (NO LF) TO PORT2
         BRA     MACSBUG        REENTER COMMAND MODE

DECODE10 CMPI.B  #$20,D0        IGNORE LEADING SPACES
         BNE.S   DECODE2        WHERE TO GO IF NOT A SPACE
         ADDQ.L  #1,A5          BUMP START OF BUFFER
         BRA.S   DECODE1        TRY NEXT CHARACTER
*
DECODE2  MOVE.B  (A5),D1        GET 2 LETTERS OF COMMAND
         LSL.W   #8,D1          MAKE ROOM FOR SECOND CHAR
         MOVE.B  1(A5),D1       GET SECOND CHAR
         CLR.L   D3             D3 = CLEAR "NO" SWITCH

DECODE21 LEA     SOLIST(PC),A1  A1 = COMMAND LIST ADDRESS
DECODE4  MOVE.W  (A1)+,D2       D2 = 2 CHAR COMMAND FROM LIST
         CLR.L   D0             CLEAR HIGH BITS
         MOVE.W  (A1)+,D0       D0 = OFFSET FROM START OF ROM

         TST.L   D3
         BEQ.S   DECODE41       NOT A "NO"
         TST.B   D2             IS "NO" OPTION SUPPORTED THIS COMMAND?
         BPL     DECODE4        NO...THEN RUN OUT OF COMMANDS

DECODE41 ANDI.W  #$7F7F,D2      CLEAR "INVISABLE" & "NO" BITS
         CMPI.W  #$7F7F,D2      END OF LIST?
         BEQ     WHAT           Command not found

         CMPI.B  #'*',D2        SEE IF DON'T CARE CHARACTER
         BNE.S   DECODE3
         MOVE.B  D1,D2          DEFAULT

DECODE3  CMP.W   D1,D2          Command from table = the input?
         BNE     DECODE4        COMMAND NOT FOUND

         CLR.W   TRACEON        TURN OFF TRACE MODE

         ADDQ.L  #2,A5          POINT A5 PAST 2 DIGIT COMMAND

         PEA     FIRST(PC)      BUILD GO TO ADDRESS
         ADD.L   D0,(A7)        ON STACK.
         ADD.L   D3,(A7)

         MOVE.L  (A7)+,A0       GO TO COMMAND
         JSR     (A0)           * SAVE MARK FOR RETURN
         BRA     MACSBUG        *  RETURN HERE

*
*    NO COMMAND
*
NOCMD    MOVEQ   #-4,D3         SET "NO" SWITCH
         MOVE.B  (A5),D1        MOVE CHAR #3
         ASL.W   #8,D1          MOVE OVER 1 CHAR
         MOVE.B  1(A5),D1       MOVE CHAR #4
         BRA     DECODE21       WHICH "NO" COMMAND?


*-------------------------------------------------------------------------
* File COMMANDS  Command list                                     06/20/82


MSG001   DC.B    CR,LF,'TUTOR  1.3 ',EOT    "PROMPT"




*******************************************************
* C O P Y R I G H T . 1 9 8 1 . B Y . M O T O R O L A *
*******************************************************

* VERSAbug command generation macro
CMD      MACRO
FLAG     SET     0              *
         IFC     '\2','HELP=NO'
FLAG     SET     FLAG+$8000     * "Help" will not display this command
         ENDC
         IFC     '\3','HELP=NO'
FLAG     SET     FLAG+$8000     * "Help" will not display this command
         ENDC
         IFC     '\2','NORTN=YES'
FLAG     SET     FLAG+$80       * "NO\1".Command
         ENDC
         IFC     '\3','NORTN=YES'
FLAG     SET     FLAG+$80       * "NO\1".Command
         ENDC
         IFC     '\1','PER'     Check for the "PER" command
         DC.W    '.*'+FLAG      * Reg commands (.A2 .D6 .PC .R0 etc.)
         DC.W    \1CMD-FIRST    *************************************
         ENDC
         IFNC    '\1','PER'     If not PERCMD...
         IFEQ    '\1'&($FF00)   If 1 digit code, 2nd will be a blank.
         DC.W    '\1 '+FLAG     * "\1"....Command  -  -  (Single Digit)
         ENDC
         IFNE    '\1'&($FF00)   If 2 digit code, leave as is.
         DC.W    '\1'+FLAG      * "\1"...Command
         ENDC
         DC.W    \1CMD-FIRST    *************************************
         ENDC
         ENDM


SOLIST   DS      0              Start Of LIST

         CMD     PER,HELP=NO,X,X

         CMD     NO,HELP=NO,X,X

         CMD     BA,X,X

         CMD     BF,X,X

         CMD     BM,X,X



         CMD     BR,NORTN=YES,X,X

         CMD     BS,X,X

         CMD     BT,X,X

         CMD     DC,X,X

         CMD     DF,X,X

         CMD     DU,X,X



         CMD     G,X,X

         CMD     GD,X,X

         CMD     GO,X,X

         CMD     GT,X,X

         CMD     HE,X,X

         CMD     LO,X,X

         CMD     M,X,X



         CMD     MD,X,X

         CMD     MM,X,X

         CMD     MS,X,X

         CMD     OF,X,X

         CMD     PA,NORTN=YES,X,X

         CMD     PF,X,X



         CMD     T,X,X

         CMD     TM,X,X

         CMD     TR,X,X

         CMD     TT,X,X

         CMD     VE,X,X

         DC.W      $FFFF     End of list indicator




*-------------------------------------------------------------------------
* File VECTMSG   Messages for vectors                             05/29/82

************************************************************
*Reprogram some VECTORS to specific ERROR handler routines *
************************************************************

INITVMSG LEA     VECT(PC),A0    A0 = START OF VECTOR TABLE
         LEA     AV4,A1         A1 = FIRST VECTOR TO INITIALIZE
         MOVEQ   #10,D0         D0 = COUNT
VECTI    MOVE.L  A0,(A1)+       MOVE ADDRESS TO VECTOR
         ADD.L   D0,A0          BUMP ADDRESS
         CMPA.L  #AV11+4,A1
         BNE     VECTI

         LEA     AV24,A1        A1 = NEXT VECTOR TO INITIALIZE
VECTI2   MOVE.L  A0,(A1)+       MOVE ADDRESS TO VECTOR
         ADD.L   D0,A0          BUMP ADDRESS
         CMPA.L  #AV48,A1
         BNE     VECTI2
         RTS


*************************************************************************
* STANDARD VECTOR "MESSAGE" HANDLING ROUTINE ($30 IS TEMP STORAGE AREA) *
*************************************************************************

VECT     MOVE.L  #'OPCO',$30    MOVE TO $30, USE SHORT BRANCHES AND PRINT IT

         BRA.S   EVECT5
VECT5    MOVE.L  #'DIV0',$30    MOVE TO $30, USE SHORT BRANCHES AND PRINT IT

         BRA.S   EVECT5
VECT6    MOVE.L  #'CHCK',$30    MOVE TO $30, USE SHORT BRANCHES AND PRINT IT

         BRA.S   EVECT5
VECT7    MOVE.L  #'TP V',$30    MOVE TO $30, USE SHORT BRANCHES AND PRINT IT

         BRA.S   EVECT5
VECT8    MOVE.L  #'PRIV',$30    MOVE TO $30, USE SHORT BRANCHES AND PRINT IT

         BRA.S   EVECT5
VECT9    MOVE.L  #'TRAC',$30    MOVE TO $30, USE SHORT BRANCHES AND PRINT IT

         BRA.S   EVECT5
VECT10   MOVE.L  #'1010',$30    MOVE TO $30, USE SHORT BRANCHES AND PRINT IT

         BRA.S   EVECT5
VECT11   MOVE.L  #'1111',$30    MOVE TO $30, USE SHORT BRANCHES AND PRINT IT

         BRA.S   EVECT5
VECT24   MOVE.L  #'SPUR',$30    MOVE TO $30, USE SHORT BRANCHES AND PRINT IT

EVECT5   BRA.S   EVECT6
VECT25   MOVE.L  #'AV#1',$30    MOVE TO $30, USE SHORT BRANCHES AND PRINT IT

         BRA.S   EVECT6
VECT26   MOVE.L  #'AV#2',$30    MOVE TO $30, USE SHORT BRANCHES AND PRINT IT

         BRA.S   EVECT6
VECT27   MOVE.L  #'AV#3',$30    MOVE TO $30, USE SHORT BRANCHES AND PRINT IT

         BRA.S   EVECT6
VECT28   MOVE.L  #'AV#4',$30    MOVE TO $30, USE SHORT BRANCHES AND PRINT IT

         BRA.S   EVECT6
VECT29   MOVE.L  #'AV#5',$30    MOVE TO $30, USE SHORT BRANCHES AND PRINT IT

         BRA.S   EVECT6
VECT30   MOVE.L  #'AV#6',$30    MOVE TO $30, USE SHORT BRANCHES AND PRINT IT

         BRA.S   EVECT6
VECT31   MOVE.L  #'AV#7',$30    MOVE TO $30, USE SHORT BRANCHES AND PRINT IT

EVECT6   BRA.S   EVECT7
VECT32   MOVE.L  #'UT 0',$30    MOVE TO $30, USE SHORT BRANCHES AND PRINT IT

         BRA.S   EVECT7
VECT33   MOVE.L  #'UT 1',$30    MOVE TO $30, USE SHORT BRANCHES AND PRINT IT

         BRA.S   EVECT7
VECT34   MOVE.L  #'UT 2',$30    MOVE TO $30, USE SHORT BRANCHES AND PRINT IT

         BRA.S   EVECT7
VECT35   MOVE.L  #'UT 3',$30    MOVE TO $30, USE SHORT BRANCHES AND PRINT IT

         BRA.S   EVECT7
VECT36   MOVE.L  #'UT 4',$30    MOVE TO $30, USE SHORT BRANCHES AND PRINT IT

         BRA.S   EVECT7
VECT37   MOVE.L  #'UT 5',$30    MOVE TO $30, USE SHORT BRANCHES AND PRINT IT

         BRA.S   EVECT7
VECT38   MOVE.L  #'UT 6',$30    MOVE TO $30, USE SHORT BRANCHES AND PRINT IT

         BRA.S   EVECT7
VECT39   MOVE.L  #'UT 7',$30    MOVE TO $30, USE SHORT BRANCHES AND PRINT IT

EVECT7   BRA.S   EVECT
VECT40   MOVE.L  #'UT 8',$30    MOVE TO $30, USE SHORT BRANCHES AND PRINT IT

         BRA.S   EVECT
VECT41   MOVE.L  #'UT 9',$30    MOVE TO $30, USE SHORT BRANCHES AND PRINT IT

         BRA.S   EVECT
VECT42   MOVE.L  #'UT A',$30    MOVE TO $30, USE SHORT BRANCHES AND PRINT IT

         BRA.S   EVECT
VECT43   MOVE.L  #'UT B',$30    MOVE TO $30, USE SHORT BRANCHES AND PRINT IT

         BRA.S   EVECT
VECT44   MOVE.L  #'UT C',$30    MOVE TO $30, USE SHORT BRANCHES AND PRINT IT

         BRA.S   EVECT
VECT45   MOVE.L  #'UT D',$30    MOVE TO $30, USE SHORT BRANCHES AND PRINT IT

         BRA.S   EVECT
VECT46   MOVE.L  #'UT E',$30    MOVE TO $30, USE SHORT BRANCHES AND PRINT IT

         BSR.S   EVECT
VECT47   MOVE.L  #'UT F',$30    MOVE TO $30, USE SHORT BRANCHES AND PRINT IT


*
*    SAVE REGISTERS AND PRINT VECTOR MSG
*
EVECT    BRA     EVECTL




*-------------------------------------------------------------------------
* File BF        Block Fill command                               06/16/82

*  BLOCK FILL    ADDRESS1 ADDRESS2 WORD-DATA

BFCMD    LEA     SYNTAX(PC),A0
         BSR     FNEXTF
         BSR     GETA
         BSR     CKWADR         CHECK WORD BOUNDRY ADDRESS
         MOVE.L  D0,D6          D6 = FROM BEGIN ADDRESS

         BSR     FNEXTF
         BSR     GETA
         BSR     CKWADR         CHECK WORD BOUNDRY ADDRESS
         MOVE.L  D0,A1          A1 = FROM END ADDRESS

         BSR     FNEXTF         FIND NEXT FIELD
         BSR     GETNUMA        D0 = VALUE
         MOVE.L  D0,D7

         MOVE.L  D6,A0          A0 = FROM BEGIN ADDRESS
         BSR     P2PHY          DISPLAY ADDRESSES
         CMP.L   A0,A1
         BCS     SYNTAX         END ADDR TOO SMALL

         CMPI.L  #$10000,D7
         BCC     SYNTAX         WORD OVERFLOW

BFCMD11
         MOVE.W  D7,(A0)        STORE DATA
         MOVE.W  (A0)+,D1
         CMP.W   D7,D1          VERIFY DATA
         BNE     MM90           'DATA DID NOT STORE'

         CMP.L   A0,A1
         BCC     BFCMD11
         BRA     MACSBUG




*-------------------------------------------------------------------------
* File BM        BM (Block Move) Command                          11/27/81

*  BLOCK MOVE

BMCMD    LEA     SYNTAX(PC),A0
         BSR     FNEXTF
         BSR     GETA
         MOVE.L  D0,A3          A3 = FROM BEGIN ADDRESS

         BSR     FNEXTF
         BSR     GETA
         MOVE.L  D0,A1          A1 = FROM END ADDRESS

         BSR     FNEXTF
         BSR     GETA
         MOVE.L  D0,A2          A2 = TO BEGIN ADDRESS

         MOVE.L  A3,A0
         BSR     P2PHY          PRINT ADDRESSES (A0) & (A1)
         MOVE.L  A2,D0
         BSR     PPHY           PRINT TO ADDRESS

         MOVE.L  A1,D1
         SUB.L   A3,D1          D1 =  SIZE - 1
         BCS     SYNTAX         END LESS THAN BEGIN
         ADDQ.L  #1,D1          D1 = COUNT (SIZE)

         CMP.L   A3,A2
         BCC.S   BM122          MOVING LOW TO HIGH

BM112    MOVE.B  (A3)+,(A2)+    MOVING HIGH TO LOW
         SUBQ.L  #1,D1          COUNT
         BNE     BM112
         BRA.S   BM142

BM122    ADD.L   D1,A3          MOVING LOW TO HIGH
         ADD.L   D1,A2
BM132    MOVE.B  -(A3),-(A2)
         SUBQ.L  #1,D1
         BNE     BM132
BM142    BRA     MACSBUG




*-------------------------------------------------------------------------
* File BR        BR, GD, GT, TR, TT, PER Commands                 12/04/81

*   ***T***   TRACE COMMAND

TCMD     DS      0              "T" Alias for "TR" command
TRCMD    LEA     TCMDHOT(PC),A0 IF NO PARAMTERS
         BSR     FNEXTF         FIND NEXT FIELD
         BSR     GETNUMA        FIND NUMBER OF INST TO TRACE
         BSR     CKADDR         INSURE 24 BITS OR LESS
         TST.L   D0
         BNE.S   TCMD15

TCMDHOT  DS      0              SPECIAL ENTRY FROM DECODE
         MOVEQ   #1,D0          ZERO; MAKE TRACE ONE
TCMD15   MOVE.L  D0,TRACECNT
         BRA.S   TRACE2


*
** TT ** "TRACE TILL" COMMAND
*

TTCMD    LEA     SYNTAX(PC),A0
         BSR     FNEXTF         FIND NEXT FIELD
         BSR     GETA           GET ADDRESS
         BSR     CKWADR         CHECK WORD BOUNDRY ADDRESS

         MOVE.L  D0,D6
         BSR     PPHY           DISPLAY TILL ADDRESS

         MOVE.L  D6,BPTILL      9TH BP
         MOVE.L  #$FFFF,TRACECNT  SET FOR A VERY LONG TIME


TRACE2   MOVE.W  #-1,TRACEON    FOR DECODE OF NEXT COMMAND

         MOVE.L  REGPC,D0
         BSR     PPHY           DISPLAY START (PC) ADDRESS
         BRA     UNTRACE


*
*   ***GT***  RUN PROGRAM TO TEMP BREAKPOINT
*

GTCMD    LEA     SYNTAX(PC),A0  GET NUMBER ELSE PRINT "WHAT"
         BSR     FNEXTF         FIND NEXT FIELD
         BSR     GETA           GET ADDRESS
         BSR     CKWADR         CHECK WORD BOUNDRY ADDRESS
         MOVE.L  D0,D6          D6 = UNTIL ADDRESS
         BSR     PPHY           PRINT PHYSICAL ADDRESS

* IF TILL ADDRESS IN BREAKPOINT TABLE; DISPLAY WHAT

         LEA     BPADD,A0       A0 = POINTER TO BP ADDRESSES
         MOVEQ   #8,D7          D7 = # OF ADDRESS ALLOWED
GT21     CMP.L   (A0)+,D6
         BEQ     BCMD55         ALREADY IN TABLE -SHOW TABLE-
         SUBQ.L  #1,D7
         BNE     GT21

         MOVE.L  D6,BPTILL      9TH BREAKPOINT
         BSR.S   GOCMD1A        NORMAL STARTUP
         BRA.S   GOCMD1

GOSET1   LEA     GOCMD1A(PC),A0 WHERE TO GO IF NO PARAMERS
         BSR     FNEXTF         FIND NEXT FIELD
         BSR     GETA           GET ADDRESS
         BSR     CKWADR         CHECK WORD BOUNDRY ADDRESS
         MOVE.L  D0,REGPC

GOCMD1A  MOVE.L  REGPC,D0       (ALSO SUBROUTINE ENTRY)
         BSR     PPHY           PRINT ".PC" PHYSICAL ADDRESS
         RTS

GCMD     DS      0              "G" ALIAS FOR "GO"
GOCMD    BSR     GOSET1         "GO" (AFTER TRACING ONE INST)
GOCMD1   MOVE.L  #-1,TRACECNT   "FLAG" COUNTER AS SPECIAL

         BRA     UNTRACE

GDCMD    BSR     GOSET1         "GO DIRECT" Command
         BRA     UNSTACK


*   ***BR***  SET AND PRINT BREAKPOINTS

*                   DELETE ALL BREAKPOINTS

NOBRCMD  BSR.S   FIXBP          GET POINTERS
BCMD01   CLR.L   (A0)+          CLEAR THE ADDRESS TABLE
         SUBQ.L  #1,D7          DO IT 8 TIMES
         BNE     BCMD01
         BRA.S   BCMD7          DISPLAY EMPTY TABLE

FIXBP    LEA     BPADD,A0       SET UP ADDRESS & COUNTER
         MOVEQ   #8,D7          COUNTER
         LEA     BPCNT,A2       COUNTS
         RTS

************************************************************
* THIS COMMAND SUPPORTS THE "NO" OPTION. COMMANDS THAT ALLOW
* THE "NO" OPTION PROVIDE A HARD BRANCH 4 BYTES BEFORE THE
* REGULAR COMMAND.
************************************************************

         BRA     NOBR0          ENTRY FOR "NOBR" (IT LOOKS FOR PARMS OR NOT)
BRCMD    LEA     BCMD7(PC),A0   WHERE TO GO IF NO PARMS
BCMD0    BSR     FNEXTF         FIND NEXT FIELD
         BSR     GETA           GET ADDRESS
         BSR     CKWADR         CHECK WORD BOUNDRY ADDRESS

         BSR     FIXBP          SET UP COUNTER & ADDRESS
BCMD00   CMP.L   (A0),D0        SEE IF ALREADY IN TABLE
         BEQ.S   BCMD33         GO CHECK FOR COUNT
         ADDQ.L  #4,A2          BUMP OTHER POINTER
         ADDQ.L  #4,A0          BUMP MAIN POINTER
         SUBQ.L  #1,D7
         BNE     BCMD00

         BSR     FIXBP          GET ADDRESS & POINTERS
BCMD3    TST.L   (A0)           FIND AN EMPTY STOP
         BNE.S   BCMD5
         MOVE.L  D0,(A0)        PUT NEW ADDRESS IN TABLE
BCMD33   CLR.L   (A2)           CLEAR CURRENT COUNT
         MOVE.B  (A5),D1        CHECK INPUT FOR COUNT
         CMPI.B  #';',D1
         BNE.S   BCMD6          NO COUNT
         ADDQ.L  #1,A5          BUMP THE BUFFER SCANNER
         BSR     GETNUMA        GO GET THE COUNT
         MOVE.L  D0,(A2)        MOVE TO TABLE

BCMD6    LEA     BCMD7(PC),A0   WHERE TO GO IF NO MORE PARAMETERS
         BRA     BCMD0

BCMD5    ADDQ.L  #4,A0          BUMP TABLE POINTER
         ADDQ.L  #4,A2          BUMP POINTER TO COUNTS
         SUBQ.L  #1,D7          LOOP AROUND
         BNE     BCMD3

BCMD55   LEA     MSG008E(PC),A5 TABLE FULL; ERROR MESSAGE
         BSR     FIXDATA
         BRA.S   BCMD77

BCMD7    LEA     MSGBR(PC),A5   "BREAKPOINTS"
         BSR     FIXDCRLF
BCMD77   BSR     OUT1CR

         BSR     FIXBP          SET ADDRESS & COUNTER
BCMD8    MOVE.L  (A2)+,D6       D6 = COUNT
         MOVE.L  (A0),D0        D0 = ADDRESS
         BEQ.S   BCMD9          ZERO ADDRESS
         BSR     FRELADDR       FORMAT RELATIVE ADDRESS
         MOVE.B  #BLANK,(A6)+

         MOVE.L  (A0),D0        FORMAT ABSOLUTE ADDRESS
         BSR     PNT6HX
         MOVE.L  D6,D0
         BEQ.S   BCMD81         DON'T PRINT ZERO COUNT
         MOVE.B  #';',(A6)+
         BSR     PNTZHX         PRINT WITH ZERO SURPRESS

BCMD81   BSR     OUT1CR
BCMD9    ADDQ.L  #4,A0
         SUBQ.L  #1,D7          LOOP AROUND
         BNE     BCMD8
         BRA     MACSBUG

MSGBR    DC.B    'BREAKPOINTS',EOT



* NOBR COMMAND

NOBR0    LEA     NOBRCMD(PC),A0 WHERE TO GO IF NO PARAMETERS
NOBR1    BSR     FNEXTF         FIND NEXT FIELD
         BSR     GETA           GO DECODE NUMBER/ADDRESS
         TST.L   D0
         BEQ     BCMD55         ZERO NOT VALID BREAKPOINT
         BSR     CKWADR         CHECK WORD BOUNDRY ADDRESS

         LEA     BPADD,A0       SET UP TABLE POINTER
         MOVEQ   #8,D7          COUNTER
NOBR3    MOVE.L  (A0),D1        GET BREAKPOINT IN TABLE
         CMP.L   D1,D0          SEE IF SAME
         BEQ.S   NOBR4
         ADDQ.L  #4,A0
         SUBQ.L  #1,D7
         BNE     NOBR3
NOBR4    CLR.L   (A0)           CLEAR THIS BREAKPOINT
         LEA     BCMD7(PC),A0   WHERE TO GO IF NO PARAMETER
         BRA     NOBR1




*-------------------------------------------------------------------------
* File BS        BS (Block Search) Command                        11/27/81

*
*  BLOCK SEARCH   BS <ADDR1> <ADDR2> 'LITERAL STRING'
*                 BS <ADDR1> <ADDR2> <DATA> [<MASK>] [;<OPTION>]

BSCMD    LEA     SYNTAX(PC),A0
         BSR     FNEXTF
         BSR     GETA
         MOVE.L  D0,A3          A3 = FROM BEGIN ADDRESS

         BSR     FNEXTF
         BSR     GETA
         MOVE.L  D0,A1          A1 = FROM END ADDRESS

         BSR     FNEXTF
         MOVE.B  (A5),D0
         CMPI.B  #$27,D0
         BEQ     BS311          LITERAL STRING SEARCH

         BSR     GETNUMA
         MOVE.L  D0,D7          D7 = DATA WE ARE LOOKING FOR
         CLR.L   D5             SCAN FOR OPTIONS
         MOVE.L  A5,A0
BS91     CMP.L   A6,A0
         BCC.S   BS97           AT END OF BUFFER

         MOVE.B  (A0)+,D0
         CMPI.B  #';',D0
         BNE     BS91           NOT SEMICOLON

         MOVE.L  A0,A6
         SUBQ.L  #1,A6          ADJUST END OF BUFFER POINTER

         MOVE.B  (A0),D0        D0 = OPTION CHARACTER
         CMPI.B  #'B',D0
         BEQ.S   BS97           BYTE  D5 = 0

         MOVEQ   #1,D5
         CMPI.B  #'W',D0
         BEQ.S   BS97                WORD  D5 = +

         MOVEQ   #-1,D5         LONG WORD  D5 = -
         CMPI.B  #'L',D0
         BNE     SYNTAX
BS97     DS      0

         MOVEQ   #-1,D4         D4 = DEFAULT SEARCH MASK
         LEA     BS101(PC),A0
         BSR     FNEXTF         FIND NEXT FIELD
         BSR     GETNUMA
         MOVE.L  D0,D4          D4 = MASK
BS101    DS      0

         MOVE.L  A3,A0
         BSR     P2PHY          PRINT ADDRESSES (A0) & (A1)

         CMP.L   A3,A1
         BCS     SYNTAX         END LESS THAN BEGIN

BS200    CMP.L   A1,A3
         BCC     MACSBUG        DONE

         BSR     FIXBUF
         MOVE.L  A3,D0
         BSR     PNT6HX         FORMAT ADDRESS
         MOVE.B  #BLANK,(A6)+   SPACE INTO BUFFER

         TST.L   D5
         BEQ.S   BS225          BYTE SIZE

         MOVE.L  A3,D0
         BSR     CKWADR         INSURE WORD BOUNDRY
         TST.L   D5
         BPL.S   BS219          WORD SIZE (2 BYTES)

         MOVEQ   #2,D6          D6 =  SIZE (LONG WORD)
         MOVE.L  (A3),D0        FETCH
         AND.L   D4,D0          MASK
         CMP.L   D7,D0          COMPARE
         BNE.S   BS215

         MOVE.L  (A3),D0        DISPLAY NON-MASKED DATA
         BSR     PNT8HX

BS213    BSR     OUT1CR

BS215    ADD.L   D6,A3          BUMP FETCH ADDRESS  (D6 = SIZE)
         BRA     BS200

BS219    MOVEQ   #2,D6          SIZE = WORD
         MOVE.W  (A3),D0
         AND.W   D4,D0
         CMP.W   D7,D0
         BNE     BS215

         MOVE.W  (A3),D0
         BSR     PNT4HX         DISPLAY
         BRA     BS213

BS225    MOVEQ   #1,D6          SIZE = BYTE
         MOVE.B  (A3),D0
         AND.B   D4,D0
         CMP.B   D7,D0
         BNE     BS215

         MOVE.B  (A3),D0
         BSR     PNT2HX         DISPLAY
         BRA     BS213

* LITERAL STRING SEARCH
*   SAVE STRING

BS311    LEA     DUMPTEMP,A2
BS313    ADDQ.L  #1,A5
         CMP.L   A6,A5
         BCC     SYNTAX         ADDR1 GREATER THAN ADDR2
         MOVE.B  (A5),(A2)+
         MOVE.B  (A5),D0
         CMPI.B  #$27,D0
         BNE     BS313
         SUBQ.L  #1,A2          A2 = END OF STRING + 1

         MOVE.L  A3,A0
         BSR     P2PHY          DISPLAY ADDRESSES

         CMP.L   A3,A1
         BCS     SYNTAX

* LOOK FOR STRING MATCH

BS323    LEA     DUMPTEMP,A4    A4 = BEGIN OF STRING
         MOVE.L  A3,A0          A0 = BEGIN OF MEMORY
BS325    MOVE.B  (A0),D0
         CMP.B   (A4)+,D0       DATA COMPARE
         BNE.S   BS365          MIS-MATCH

         CMP.L   A0,A1          ADDRESS CHECK
         BCS     MACSBUG        OUT OF MEMORY

         ADDQ.L  #1,A0
         CMP.L   A2,A4
         BCS     BS325          MORE STRING TO CHECK

         BSR     FIXBUF         HAVE MATCH
         MOVE.L  A3,D0          FORMAT ADDRESS
         BSR     PNT6HX
         MOVE.B  #BLANK,(A6)+   SPACE

         MOVE.B  #$27,(A6)+     LEADING QUOTE
         LEA     DUMPTEMP,A4    MOVE STRING TO BUFFER
BS355    MOVE.B  (A4)+,(A6)+
         CMP.L   A4,A2
         BCC     BS355

         BSR     OUT1CR         DISPLAY

BS365    ADDQ.L  #1,A3
         CMP.L   A3,A1
         BCS     MACSBUG        DONE
         BRA     BS323




*-------------------------------------------------------------------------
* File BT        BT (Block Test) command                          11/30/81

* BT   BLOCK OF MEMORY TEST

BTCMD    BSR     MTSETUP        PREPARE PARMS (FROM,TO/COUNT)
         BSR     RAMTEST        EXEC MEMORY TEST SUBROUTINE
         BEQ     MACSBUG        NO ERRORS, RETURN TO MACSBUG
         MOVE.L  D1,-(A7)       SAVE DATA READ
         MOVE.L  D0,-(A7)       SAVE DATA WRITTEN CAUSING ERROR

         BSR     FIXBUF         SET UP TO PRINT
         MOVE.L  #'FAIL',(A6)+
         MOVE.L  #'ED A',(A6)+
         MOVE.W  #'T ',(A6)+
         MOVE.L  A2,D0          ADDRESS WHERE IT FAILED
         BSR     PNT6HX

         MOVE.L  #'  WR',(A6)+
         MOVE.L  #'OTE=',(A6)+
         MOVE.L  (A7)+,D0       WHAT WAS WRITTEN
         BSR     PNT4HX

         MOVE.L  #'   R',(A6)+
         MOVE.L  #'EAD=',(A6)+
         MOVE.L  (A7)+,D0       WHAT WAS READ
         BSR     PNT4HX

         BRA     MSG            PRINT IT




*-------------------------------------------------------------------------
* File DC        DC (Data Conversion) Command                     12/10/81

*
*
*  ***DC***  NUMBER CONVERSIONS
*
DCCMD    DS      0              -DATA CONVERT COMMAND-
NUMCON0  LEA     SYNTAX(PC),A0  IF NO PARAMETERS
         BSR     FNEXTF         POINT TO NEXT PARAMETER
         BSR     GETA           EVALUATE EXPRESSION

         BSR     FIXBUF         SET UP FOR PRINT
         MOVE.L  D0,D7          D7=VALUE
         TST.L   D7             SEE IF NEGATIVE
         BPL.S   NUMCON1
         MOVE.B  #'$',(A6)+
         MOVE.L  D7,D0          MOVE NEGATIVE RESULT TO D0
         BSR     PNT8HX
         MOVE.B  #'=',(A6)+
NUMCON1  MOVE.L  D7,D0          RESTORE
         BPL.S   NUMCON2
         NEG.L   D0
         BMI.S   NUMCON2        SPECIAL CASE (-0)
         MOVE.B  #'-',(A6)+
NUMCON2  MOVE.B  #'$',(A6)+
         BSR     PNTZHX
         MOVE.B  #'=',(A6)+     NOW PRINT DECIMAL VALUE
         MOVE.L  D7,D0
         BPL.S   NUMCON3
         NEG.L   D0
         BMI.S   NUMCON3        SPECIAL CASE (-0)
         MOVE.B  #'-',(A6)+
NUMCON3  MOVE.B  #'&',(A6)+
         BSR     HEX2DEC        PUT VALUE IN BUFFER
         BRA     MSG            GO PRINT IT




*-------------------------------------------------------------------------
* File DFDI      DF (Display registers) WITH disassembler         05/27/82

REGNAMES DC.L    'PCSR'         TABLE OF NAMES OF REGISTERS
         DC.L    'USSS'
         DC.W    '??'           END OF TABLE

DFCMD    DS      0              DF COMMAND  ENTRY
         BRA.S   TD07

TDISPLY  BSR     FIXBUF         PRINT TRACE DISPLAY SUBROUTINE
         TST.B   XONOFF+3
         BNE.S   TD25           SHORT DISPLAY

TD07     BSR     FIXBUF         PRINT PRELUDE
         CLR.L   OUTTO          FORCE DISPLAY TO OPERATORS CONSOLE
         MOVE.L  SCREEN1,(A6)+
         BEQ.S   TD09           SKIP PRELUDE
         BSR     OUTPUT
TD09

         LEA     REGNAMES(PC),A4 REGISTER NAMES
         LEA     REGPC,A2       REGISTER DATA
         BSR     FIXBUF         SET UP I/O BUFFER

TD1      MOVE.W  (A4)+,D0       GET REG NAME
         MOVE.L  (A2)+,D7       GET REG CONTENT
         CMPI.W  #'??',D0       SEE IF AT END OF REGS
         BNE.S   TD4
         BSR     OUT1CR         PRINT BUFFER

         MOVE.B  #'D',D7        CLASS=DATA
         LEA     REGS,A3        OFFSET
         BSR     PNTCLS         GO PRINT THE BLOCK

         MOVE.B  #'A',D7        CLASS=ADDRESS
         LEA     REGS+32,A3     OFFSET
         BSR     PNTCLS         GO PRINT THE BLOCK

         BSR     FIXBUF
         MOVEQ   #20,D1         LOOP COUNTER
TD27     MOVE.B  #'-',(A6)+     FILL BUFFER WITH BOARDER
         SUBQ.L  #1,D1
         BNE TD27

TD25     MOVE.L  REGPC,A4       DISASSEMBLE
         MOVEM.L (A4),D0-D2
         MOVE.L  A6,A5
         BSR     DCODE68K
         LEA     BUFFER,A5

         BSR     OUT1CR         PRINT

         BSR     FIXBUF         PRINT END STUFF FOR SCREEN CONTROL
         MOVE.L  SCREEN2,(A6)+
         BEQ.S   TD39           SKIP END STUFF
         BSR     OUTPUT
TD39     RTS     RETURN FOR MORE WORK

TD4      MOVE.W  D0,D2          PRINT REG NAME IN BUFFER
         ASR.W   #8,D0          MOVE IT OVER
         MOVE.B  D0,D3          SAVE REGISTER TYPE A,D,W,M ETC
         MOVE.B  D0,(A6)+       SAVE FIRST LETTER
         MOVE.B  D2,(A6)+       SAVE NEXT LETTER
         MOVE.B  #'=',(A6)+     EQUAL SIGN
         CMPI.W  #'US',D2
         BNE.S   T44
         MOVE.L  REGUS,D0       USER STACK
         BRA.S   T449

T44      CMPI.W  #'SS',D2       SUPER STACK IS SPECIAL
         BNE.S   T448
         MOVE.L  REGA7,D0       GET A7
         BRA.S   T449

T448     MOVE.L  D7,D0          REGISTER VALUE
         CMPI.W  #'SR',D2       SEE IF STATUS REGISTER
         BEQ.S   TDCC
T449     BSR     PNT8HX         FORMAT 8 HEX CHAR
TD9      MOVE.B  #BLANK,(A6)+   SPACE BETWEEN REGS
         BRA TD1

*   CONDITION CODE FORMAT
*
TDCC     MOVE.W  D0,D3          SAVE FOR A MOMENT
         BSR     PNT4HX
         MOVE.B  #'=',(A6)+
         MOVE.L  #$80000054,D7  TRACE BIT
         BSR.S   TDCC9
         MOVE.L  #$20000053,D7  SUPERVISOR BIT
         BSR.S   TDCC9
         MOVE.W  D3,D0          INTERRUPT LEVEL
         LSR.W   #8,D0
         ANDI.B  #$07,D0        "7" MAX IN SR FOR LEVEL
         BSR     PUTHEX
         MOVE.L  #$100058,D7    X BIT
         BSR.S   TDCC9
         MOVE.L  #$8004E,D7     N BIT
         BSR.S   TDCC9
         MOVE.L  #$4005A,D7     Z BIT
         BSR.S   TDCC9
         MOVE.L  #$20056,D7     V BIT
         BSR.S   TDCC9
         MOVE.L  #$10043,D7     C BIT
         BSR.S   TDCC9
         BRA     TD9
*
TDCC9    MOVE.L  D7,D6          DUPLICATE STUFF
         SWAP    D6             GET BIT POSITION
         AND.W   D3,D6          SEE IF ON
         BNE.S   TDCC91
         MOVE.B  #'.',D7        PUT IN PERIOD IF OFF
TDCC91   MOVE.B  D7,(A6)+       PUT IN LETTER IF ON
         RTS




*-------------------------------------------------------------------------
* File DUMP      DU     Dump "S-Records"                          05/10/82

*   ***DUMP***  DUMP  'S' RECORDS
*    FORMAT:  DU  ADDRESS1 ADDRESS2  [TEXT....]
*
DUCMD    DS      0
         BSR     SCANPORT       SEE WHERE TO SEND OUTPUT (DUMMY CALL)
         MOVE.L  OUTTO,D6       SAVE OUTTO FOR ACTUAL S-RECORD DUMP
         CLR.L   OUTTO          OVERRIDE SCANPORT CALL

         LEA     SYNTAX(PC),A0  WHERE TO GO IF NO PARAMTERS
         BSR     FNEXTF         FIND NEXT FIELD
         BSR     GETA           GET ADDRESS1
         MOVE.L  D0,A3          A3 = BEGIN ADDRESS

         BSR     FNEXTF
         BSR     GETA           GET ADDRESS2
         MOVE.L  D0,A4          A4 = END ADDRESS

* PROCESS HEADER
         LEA     PUNCH5(PC),A0  WHERE TO GO IF NO HEADER
         BSR     FNEXTF         LOOK FOR HEADER
PUNCH5   DS      0

* MOVE TEXT TO 'TEMP STORAGE'
         LEA     DUMPTEMP,A2
         MOVE.L  A2,D5          D5 = START OF TEXT
PUM11    CMP.L   A5,A6
         BEQ.S   PUM13
         MOVE.B  (A5)+,(A2)+    MOVE
         BRA     PUM11
PUM13    EXG     A2,D5          D5 = END OF TEXT +1

* DISPLAY ADDRESSES
         MOVE.L  A3,A0
         MOVE.L  A4,A1
         BSR     P2PHY          DISPLAY TWO ADDRESSES

* INSURE END EQUAL GREATER THAN BEG
         CMP.L   A3,A4
         BCS     SYNTAX

         MOVE.L  D6,OUTTO       RESTORE OPTIONAL DESTINATION OF DUMP

* FINISH PROCESSING HEADER
*  A2 = START OF TEXT
         BSR     FIXBUF         A5,A6=#BUFFER
         MOVEQ   #2,D6          THE BYTE COUNT
         CLR.L   D4             CLEAR THE CHECKSUM
         MOVE.L  #'S0??',(A6)+  START OF S RECORD
         MOVE.L  #'0000',(A6)+  DUMMY ADDRESS
MORES0   CMP.L   D5,A2          SEE IF AT END OF TEXT
         BGE.S   ENDS0          WHERE TO GO WHEN ALL CHARACTERS USED
         ADDQ.L  #1,D6          ANOTHER BYTE

         MOVE.B  (A2)+,D0       GET ANOTHER BYTE OF TEXT

         ADD.L   D0,D4          FOR CHECKSUM
         BSR     PNT2HX         PUT IT IN BUFFER
         BRA     MORES0
ENDS0    DS      0

         BSR     PNTSREC        GO PRINT THE 'S' RECORD
         MOVE    A3,A2          A2 WILL SCAN BETWEEN A3-A4

* DO ANOTHER 'S' RECORD
MORESP   BSR     FIXBUF         A5,A6=#BUFFER
         CLR.L   D4             CLEAR CHECKSUM REGISTER
         MOVE.L  A3,D0          READY TO PRINT ADDRESS
         MOVE.L  A3,D1          GET READY TO AND ADDRESS
         MOVEQ   #$10,D3        MAXIMUM BYTES ON S REC LINE
         ADD.L   D3,D1          INSURE END OF LINE ADDRESS IS MAX
         ANDI.L  #$FF0000,D1    SEE IF 3 BYTE ADDRESS
         BNE.S   S2REC          WHERE TO GO IF 3 BYTES NEEDED
         MOVE.L  #'S1??',(A6)+  PUSH
         MOVE    A3,D0          SET UP TO PRINT 2 BYTE ADDRESS
         BSR     PNT4HX         PRINT 4 HEX CHAR ADDRESS
         MOVEQ   #2,D6          BYTE COUNT
         MOVE.W  A3,D0          FIX UP CHECKSUM
         ADD.B   D0,D4          LOW BYTE
         ASR     #8,D0          SHIFT IT OVER
         ADD.B   D0,D4          HIGH BYTE OF ADDRESS
         BRA.S   PNCA3          GO PUNCH A LINE

S2REC    MOVE.L  #'S2??',(A6)+  PUSH
         BSR     PNT6HX         PRINT 6 HEX CHAR ADDRESS
         MOVEQ   #3,D6          BYTE COUNT
         MOVE.L  A3,D0          FIX UP CHECKSUM
         ADD.B   D0,D4          LOW BYTE
         ASR     #8,D0          SHIFT IT OVER
         ADD.B   D0,D4          MIDDLE BYTE
         SWAP    D0             SET UP FOR HIGH BYTE
         ADD.B   D0,D4          ADD HIGH BYTE
PNCA3    CMP.L   A4,A3          SEE IF AT ENDING ADDRESS

* END OF FILE
         BLE.S   A3OUT          WHERE TO GO IF BELOW OR AT END ADDRESS
         BSR.S   PNTSRECX       END IT BY PRINTING LAST RECORD
         BSR     FIXBUF         A5,A6=#BUFFER
         CLR.L   D4             CLEAR THE CHECKSUM
         MOVE.L  #'S9??',(A6)+  MOVE TO PRINT BUFFER
         MOVE.L  #'0000',(A6)+  MOVE '0000' TO PRIT BUFFER
         MOVEQ   #2,D6          BYTE COUNT
         BSR.S   PNTSREC        PRINT 'S9' END-OF-FILE RECORD
         BRA     MACSBUG        REENTER MACSBUG

A3OUT    MOVE.B  (A3)+,D0       GRAB THE BYTE FROM MEMORY
         ADD.W   D0,D4          ADD TO CHECKSUM
         ADDQ.W  #1,D6          BUMP THE BYTE COUNT
         ADDQ.L  #1,A1          ADD TO COUNT OF BYTES PROCESSED
         BSR     PNT2HX         PUT THE HEX IN THE PRINT BUFFER
         SUBQ.L  #1,D3          COUNT DOWN CHAR TO GO IN LINE
         BNE     PNCA3
         BSR.S   PNTSREC        END OF LINE-PUNCH IT
         BRA     MORESP         GO FIX UP NEXT LINE

* FIX UP & PRINT THE 'S' RECORD/LINE

PNTSRECX CMP.W   #0,A1          SEE IF ANY CHAR MOVED
         BEQ.S   PNTSRTS        NO CHAR MOVED

PNTSREC  ADD     #1,D6          ONE MORE BYTE (CHECKSUM)
         ADD.W   D6,D4          ADD BYTE COUNT TO CHECKSUM
         NOT.B   D4             COMPLIMENT THE CHECKSUM
         MOVE.L  D4,D0          READY FOR PRINT-HEX
         BSR     PNT2HX         PUT CHECKSUM IN RECORD
         MOVE.L  A6,D7          SAVE FOR THE MOMENT
         MOVE.L  A5,A6          START OF BUFFER
         ADDQ.L  #2,A6          BYPASS RECORD TYPE (4 CHAR)
         MOVE.B  D6,D0          SET UP BYTE COUNT FOR PNTHEX ROUTINE
         BSR     PNT2HX         PUT THE BYTE COUNT IN THE PRINT BUFFER
         MOVE.L  D7,A6          RESTORE REAL END OF BUFFER
         BSR     OUT1CR         DO THE ACTUAL DISPLAY/PUNCH
         SUB.L   A1,A1          CLEAR COUNTER OF BYTES PROCESSED
PNTSRTS  RTS




*-------------------------------------------------------------------------
* File GETA      GET ADDRESS Subroutine                           12/01/81

* GET ADDRESS
*  ENTER (A5) POINTER START OF BUFFER
*        (A6) POINTER END OF BUFFER
*
*  RETURN:  D0 = ADDRESS

*        (A6) POINTER END OF BUFFER
*
*  RETURN:  D0 = ADDRESS


* FORMATS HANDLED:
*  1.  NUMBER        DEFAULTS TO HEX
*  2.  $NUMBER       HEX
*  3.  &NUMBER       DECIMAL
*  4.  (A@)
*  5.  NUMBER(A@)
*  6.  (A@,D@)
*  7.  NUMBER(A@,D@)
*  8.  [NUMBER]      MEMORY INDIRECT
*
*   FORMATS 1,2,3,8  ADD OFFSET R0 UNLESS R1 - R7 SPECIFIED


* WORK REGISTERS
*  D4    VALUE BEING BUILT
*
*  D5    FLAG REGISTER
*     = 8000XXXX  R@ GIVEN (GARO)
*     = XXXX80XX  [  GIVEN (GALB)
*     = XXXXXX80  (  GIVEN (GALP)
*
*  D6    FLAG REGISTER
*     = 8000XXXX  A@ GIVEN           (GAAVF)
*     = XXXX80XX  NEED PLUS OR MINUS (GANPM)
*     = XXXXXX2B  +  PLUS GIVEN      (GAPMS)
*             2D  -  MINUS GIVEN

GETA     MOVEM.L D4-D6/A0,-(A7) SAVE SOME REGISTERS
         CLR.L   D4             VALUE BEING BUILT
         CLR.L   D5             FLAG REG
         CLR.L   D6             FLAG REG

         MOVE.B  (A5)+,D0       GET BYTE
         CMP.L   A5,A6
         BCS     GAP191         END OF BUFFER

         CMPI.B  #'[',D0
         BNE.S   GAP113

*  [  SET INDIRECT

         ORI.W   #$8000,D5      SET LEFT BRACKET (GALB)

GAP111   MOVE.B  (A5)+,D0       GET BYTE
         CMP.L   A5,A6
         BCS     GAP191         END OF BUFFER
GAP113   DS      0

         CMPI.B  #'+',D0
         BEQ.S   GAP121         PLUS SIGN

         CMPI.B  #'-',D0
         BEQ.S   GAP121         MINUS SIGN

         CMPI.B  #']',D0
         BEQ.S   GAP131         RIGHT BRACKET (INDIRECT)

         CMPI.B  #'(',D0
         BEQ.S   GAP141         LEFT PARIN

         CMPI.B  #',',D0
         BEQ     GAP161         COMMA

         CMPI.B  #')',D0
         BEQ     GAP181         RIGHT PARIN

         CMPI.B  #';',D0        "SEMI-COLON"
         BEQ     GAP191         TERMINATE

         CMPI.B  #BLANK,D0      "SPACE"
         BEQ     GAP191         TERMINATE

         TST.W   D6             (GANPM)
         BMI.S   GAE            NEEDS PLUS OR MINUS

         CMPI.B  #'R',D0
         BEQ     GAP171         RELATIVE OFFSET

         TST.B   D6             (GALP)
         BMI.S   GAE            (...   NUMBER NOT ALLOWED

* NONE OF ABOVE ASSUME NUMERIC VALUE
         SUBQ.L  #1,A5          ADJUST (A5) TO FIRST CHAR
         CLR.L   D0
         BSR     GETNUMA

         CMPI.B  #'-',D6        (GAPMS)
         BEQ.S   GAP118         MINUS SIGN

         ADD.L   D0,D4          PLUS SIGN
         BRA.S   GAP119

GAP118   SUB.L   D0,D4

GAP119   CLR.B   D6             (GAPMS)  RESET PLUS MINUS FLAG
         ORI.W   #$8000,D6      (GANPM)  SET NEED PLUS MINUS
GAP111S  BRA     GAP111

* (*) (-) SET ARITHMETIC OPERATOR

GAP121   TST.B   D6             (GAPMS)
         BNE.S   GAE            MULTI OPERATORS
         MOVE.B  D0,D6          (GAPMS)
         ANDI.W  #$00FF,D6      RESET (GANPM) NEED PLUS MINUS
         BRA     GAP111S

*  ]  CLOSE INDIRECT

GAP131   TST.W   D5             (GALB)
         BPL.S   GAE            [ MISSING

* IF NO R@ GIVEN ADD R0
         TST.L   D5             (GARO)
         BMI.S   GAP135         R@ GIVEN
         ADD.L   OFFSET,D4      NO R@ GIVEN; ADD R0
GAP135   DS      0

         MOVE.L  D4,A0
         MOVE.L  (A0),D0
         BRA     GAP199

*  (  DO PARIN PAIR

GAP141   TST.B   D5             (GALP)
         BMI.S   GAE            MULTI (
         TST.L   D5             (GARO)
         BMI.S   GAE            R@ NOT ALLOWED WITH (..)
         ORI.B   #$80,D5        (GALP) SET LEFT PAREN

* LEFT PARIN SET; MUST BE A@ NEXT
         MOVE.B  (A5)+,D0       GET BYTE
         CMP.L   A5,A6
         BCS.S   GAE
         CMPI.B  #'A',D0
         BNE.S   GAE            NOT A-REG
         LEA     REGS+32,A0
         BSR.S   GASRGN         GET VALUE IN A@
         ADD.L   D1,D4
         ORI.L   #$80000000,D6  (GAAVF) A-REG VALUE FLAG
         BRA     GAP111S

GAE      BRA     SYNTAX

*  COMMA  A-REG or
*  COMMA  D-REG REQUIRED

GAP161   TST.L   D6             (GAAVF)
         BPL     GAE            NO A-REG SPECIFIED
         MOVE.B  (A5)+,D0       GET BYTE
         CMP.L   A5,A6
         BCS     GAE
         CMPI.B  #'A',D0
         BNE.S   GAP163
         LEA     REGS+32,A0     GET VALUE IN A@
         BRA.S   GAP165
GAP163   CMPI.B  #'D',D0
         BNE     GAE            NOT D-REG
         LEA     REGS,A0        GET VALUE IN D@
GAP165   BSR.S   GASRGN
         ADD.L   D1,D4
         BRA     GAP111S

*  R@  OFFSET

GAP171   CMPI.B  #'+',D6        (GAPMS)
         BNE     GAE            ONLY + ALLOWED

* ONLY ONE R@ ALLOWED

         TST.L   D5             (GARO)
         BMI     GAE            MULIT R@
         ORI.L   #$80000000,D5  SET R@ GIVEN (GARO)

         LEA     OFFSET,A0
         BSR.S   GASRGN         GET VALUE IN R@
         ADD.L   D1,D4
         BRA     GAP119

*  )  CLOSE THE WORLD

GAP181   TST.L   D6             (GAAVF)
         BPL     GAE            NO (
         BRA.S   GAP197

*  SPACE  TERMINATOR

GAP191   TST.W   D5             (GALB)
         BMI     GAE            [ WITHOUT ]
         TST.B   D5             (GALP)
         BMI     GAE            ( WITHOUT )
         SUBQ.L  #1,A5          ADJUST CHAR POINTER

* IF NO R@ GIVEN ADD R0

         TST.L   D5             (GARO)
         BMI.S   GAP197         R@ GIVEN
         ADD.L   OFFSET,D4
GAP197   MOVE.L  D4,D0

GAP199   MOVEM.L (A7)+,D4-D6/A0
         RTS

* GET NEXT NUMBER
*  A0 = POINTER TO TABLE OF VALUES
*  D1 = VALUE ON RETURN

GASRGN   CLR.L   D0
         MOVE.B  (A5)+,D0       GET BYTE
         CMP.L   A5,A6
         BCS     GAE
         SUBI.B  #'0',D0        ADJUST TO ZERO
         CMPI.B  #7,D0
         BHI     GAE            NOT 0 - 7
         MULU    #4,D0          4 * OFFSET
         MOVE.L  (A0,D0),D1
         RTS




*-------------------------------------------------------------------------
* File H         Register save,Trace, Breakpoint                  03/03/82

*       SAVE ALL REGISTERS ROUTINE-JMP [TEMP] BACK
*          USUALLY CALLED BY THE MACRO "SAVEREGS"

SAVE     DS      0
         LEA     REGA7,A7       WHERE TO START STORING
         MOVEM.L D0-D7/A0-A6,-(A7)  SAVE REGISTERS

         LEA     SYSTACK+4,A7   SET UP STRETCHED VERSAUG STACK

         MOVE.L  REGA7,A0       A0 = TARGETS SUPERVISOR STACK POINTER
         MOVE.W  (A0)+,REGSR+2  GET TARGETS SR

         MOVE.L  (A0)+,REGPC    GET TARGETS PC

         MOVE.L  A0,REGA7       WHERE TARGET STACK REALLY POINTS

         MOVE.L  USP,A1         GET USERS STACK POINTER
         MOVE.L  A1,REGUS       SAVE IT FOR DISPLAY ETC

         MOVE.L  REGPC,D0       GET PROGRAM COUNTER
         SUBQ.L  #4,A7          SET REAL MACSBUG STACK
         MOVE.L  TEMP,-(A7)     PUT RETURN ADDRESS ON STACK
         RTS                    RETURN TO SENDER

*
*     ***TRACE***  TRACE ENTRY POINT
*       ENTER FROM VECTOR 9  (LOCATION 24) FOR
*

* REGISTER USAGE
*  A0 = ADDRESS OF BREAKPOINT ADDRESS
*  A2 = ADDRESS OF BREAKPOINT COUNTS
*  D1 = PC
*  D5 = TRACECNT
*  D7 = BKPT COUNT

TRACE    MOVE.W  #$2700,SR      MASK OFF INTERRUPTS
         SAVEREGS

* IF PC POINTS TO 'TRACE'; DOUBLE EVENT OCCURED
*  CLEAR LAST EVENT BY IGNORING

         CMPI.L  #V2,REGPC

         BNE.S   TRACE16

         MOVE.L  REGA7,A5       TRIM LAST EVENT FROM STACK
         MOVE.W  (A5)+,REGSR+2  *MOVE VALUES FROM STACK TO
         MOVE.L  (A5)+,REGPC    *PSUEDO SR, PC,
         MOVE.L  A5,REGA7       *REFLECT ADJUSTMENTS IN PSUEDO STACK
TRACE16  ANDI.W  #$7FFF,REGSR+2 RESET "T" (TRACE) BIT


         MOVE.L  TRACECNT,D5
         BMI.S   TRACE39        EXECUTING ONE-INSTRUCTION
         BEQ     ABORT335       NOT TRACEING

*   MAKE SURE WE ARE NOT TRACING OURSELVES
         MOVE.L  REGPC,D1       GET PC
         LEA.L   FIRST(PC),A0
         CMP.L   A0,D1
         BMI.S   TISOK          TRACING BELOW OURSELVES
         LEA     LAST(PC),A0
         CMP.L   A0,D1
         BHI.S   TISOK          TRACING ABOVE OURSELVES
         LEA     MSG020(PC),A5  TRACING OURSELVES
         BRA     CHKBP4
TISOK

         LEA     BPADD,A0
         LEA     BPCNT,A2
         MOVEQ   #9,D7          9TH BP IS "UNTILL" FEATURE

TRACE01  CMP.L   (A0),D1        SEE IF PC MATCHES ADDRESS IN TABLE
         BNE.S   TRACE08
         MOVE.L  (A2),D0        GET COUNT
         BEQ     CHKBP3         COUNT ZERO
         SUBQ.L  #1,D0          COUNT DOWN
         MOVE.L  D0,(A2)        SAVE IT
         BEQ     CHKBP3         COUNT WENT TO ZERO
         BRA.S   TRACE03

TRACE08  ADDQ.L  #4,A0          BUMP TABLE POINTER
         ADDQ.L  #4,A2          BUMP COUNT TABLE POINTER
         SUBQ.L  #1,D7          LOOP AROUND
         BNE     TRACE01

TRACE03  BSR     TDISPLY        DO TRACE DISPLAY
         SUBQ.L  #1,TRACECNT    TRACE COUNT
         BEQ     MACSBUG        STOP WHEN ZERO
         BRA.S   UNTRACE        CONTINUE WITH TRACE


* END UP HERE AFTER BREAKPOINTING ONE INSTRUCTION
* -- PUT BP BACK IN AND CONTINUE TO RUN

TRACE39  CLR.L   TRACECNT
         BSR.S   SWAPIN         PUT BP INTO USER'S MEMORY
         BRA.S   UNSTACK        CONTINUE TO RUN


UNTRACE  ORI.W   #$8000,REGSR+2 SET UP TRACE BIT!
         ADDR2MEM TRACE,AV9     TAKE TRACE VECTOR

UNSTACK  MOVE.L  REGUS,A1
         MOVE.L  A1,USP         US = TARGET'S USER STACK
         MOVE.L  REGPC,A2       A2 = TARGET'S PC


         DS      0              INSURE MEMORY AT LOCATION OF PC
         MOVE.W  (A2),D0        * ADDR TRAP ERROR * IF NO MEMORY

         MOVE.L  REGA7,A1       A1 = TARGET SYSTEM STACK (SS)

         DS      0              INSURE MEMORY AT TARGET'S STACK
         MOVE.L  A2,-(A1)       MOVE PC ONTO TARGET'S STACK

         MOVE.W  REGSR+2,D0
         MOVE.W  D0,-(A1)       SR ONTO TARGET'S STACK

         MOVE.L  A1,TEMP        TEMP = TARGETS SS

         LEA     REGS,A7        A7 = POINTER TO PSUEDO REGISTERS
         MOVEM.L (A7)+,D0-D7/A0-A6  ARM MOST OF TARGET REGISTERS
         MOVE.L  TEMP,A7        SS = TARGET'S

         RTE                    GO BACK TO THE USER


SWAPIN   BSR.S   SWAPOUT        MAKE SURE THEY ARE ALL OUT

         MOVE.L  AV4,SAVEAV4    SAVE VECTOR (WHOM EVER'S IT WAS)
         LEA     CHKBP(PC),A6
         MOVE.L  A6,AV4         REPLACE IT WITH THE "CHKBP" RTN
         LEA     SWAPIN1(PC),A6 A6 = ROUTINE ADDRESS
         BRA.S   SWAP

SWAPOUT  TST.W   BPSTATUS        SEE IF OUT ALREADY
         BEQ.S   SWAPEND         YES...DONE
         MOVE.L  SAVEAV4,AV4     NO....REPLACE THE VECTOR

         LEA     SWAPOUT1(PC),A6 A6 = ROUTINE ADDRESS
SWAP     LEA     BPADD,A0       A0 = ADDRESS OF TABLE
         LEA     BPCNT,A2       A2 = ADDRESS OF COUNTS
         MOVEQ   #9,D7          DO 9 BP
         LEA     BPDATA,A3      CONTENT TABLE

SWAP1    MOVE.L  (A0),A4        GET POSSIBLE ADDDRESS
         TST.L   (A0)           IS POSSIBLE ADDRESS ZERO
         BEQ.S   SWAP99         ZERO MEANS NO BP DEFINED
         JMP     (A6)           GO TO RIGHT ROUTINE

SWAPIN1
         MOVE.W  (A4),D0        USER'S PROGRAM GOES INTO TABLE

         MOVE.W  D0,(A3)
         MOVE.W  #BKPOINT,(A4)  PUT BREAKPOINT IN

         MOVE.W  #1,BPSTATUS    FLAG AS BP IN
         BRA.S   SWAP99

SWAPOUT1 MOVE.W  (A3),D0        GET CONTENTS FROM TABLE
         MOVE.W  D0,(A4)        PUT CONTENTS BACK INTO PROGRAM

         CLR.W   BPSTATUS       FLAG AS BREAKPOINTS OUT
SWAP99   ADDQ.L  #4,A0          BUMP ADDRESS TABLE POINTER
         ADDQ.L  #2,A3          BUMP CONTENT TABLE POINTER
         SUBQ.L  #1,D7
         BNE     SWAP1
SWAPEND  RTS

*  ILLEGAL INSTRUCTION ENTRY POINT
*   BREAKPOINT TEST
*
CHKBP    MOVE.W  #$2700,SR      MASK OF INT.
         SAVEREGS
         MOVE.L  REGPC,D0       GET PROGRAM COUNTER TO COMPARE
         MOVE.L  D0,A5          A5 = TARGET PC
         MOVE.W  (A5),D1        SEE WHAT OP CODE WAS XEQ

         BSR     SWAPOUT        TAKE BREAKPOINTS OUT

         CMPI.W  #BKPOINT,D1    USED FOR BP
         BNE.S   CHKBP11        NOT AT BREAKPOINT

         LEA     BPADD,A0       A0 = ADDRESS OF BP ADDRESSES
         LEA     BPCNT,A2       A2 = ADDRESS OF BP COUNTS
         MOVEQ   #9,D7          D7 = LOOP COUNT

CHKBP1   CMP.L   (A0),A5        SEE IF WE ARE THERE
         BEQ.S   CHKBP2         AT BREAKPOINT; AT AN ADDRESS

         ADDQ.L  #4,A0          BUMP BOTH POINTERS
         ADDQ.L  #4,A2
         SUBQ.L  #1,D7
         BNE     CHKBP1

* IS NOT A BREAKPOINT; ASSUME ILLEGAL INSTRUCTION
CHKBP11  LEA     MSG009(PC),A5  'ILLEGAL INSTRUCTION'
         CLR.W   TRACEON        RESET TRACE MODE
         BRA.S   CHKBP4

* AT BREAKPOINT...CHECK COUNT
CHKBP2   MOVE.L  (A2),D0        GET COUNT
         BEQ.S   CHKBP3         COUNT ZERO
         SUBQ.L  #1,D0          DECREMENT
         MOVE.L  D0,(A2)        PUT COUNT BACK
         BNE     GOCMD1         COUNT NOT ZERO; KEEP GOING

CHKBP3   LEA     MSG014(PC),A5  "AT BREAKPOINT"

CHKBP4   BSR     FIXDCRLF
         BSR     OUT1CR
         BSR     TDISPLY        PRINT TRACE DISPLAY
         BRA     MACSBUG

MSG009   DC.B    'ILLEGAL INSTRUCTION',EOT




MSG014   DC.B    'AT BREAKPOINT',EOT



MSG020   DC.B    '.PC within "DEBUGGER"',BELL,EOT





         DC.B    0              PAD BYTE


*-------------------------------------------------------------------------
* File BA        BASIC Command                                     12/01/81

* BASIC  COMMAND
*  START ENHANCED BASIC
BACMD    BRA     code_start        Run BASIC



*-------------------------------------------------------------------------
* File HE        HELP Command                                     12/01/81

* HELP  COMMAND
*  PRINT: REGISTERS AND COMMANDS IN TABLES

HECMD    LEA     MSG002(PC),A5
         BSR     FIXDATA
         BSR     OUT1CR         PRINT

         LEA     SOLIST(PC),A4  A4 = POINTER TO COMMAND LIST

         BSR     FIXBUF
         MOVE.B  #8,D2          D2 = # CMDS PER LINE
HELP4    MOVE.W  (A4)+,D1       GET 2 BYTE COMMAND
         CMPI.W  #$FFFF,D1
         BEQ.S   HELP6          DONE PRINT LAST BUFFER
         ADDQ.L  #2,A4          BUMP POINTER UP BY 2
         TST.W   D1             IS THE INVISIBLE INDICATOR ON?
         BMI     HELP4          YES... THEN BYPASS THIS ONE
         MOVE.W  D1,D3          SAVE XX FOR "XX" AND "NOXX" IN HELP
         ANDI.W  #$7F7F,D1      REMOVE CONTROL BITS
         MOVE.W  D1,(A6)+       NO.... MOVE THIS COMMAND TO "PRINT" LINE
         MOVE.L  #'    ',(A6)+  MOVE BLANKS FOR SPACING
         BSR.S   HELP81         PRINT THE LINE IF FULL
         BTST    #7,D3          IS "NO" OPTION SUPPORTED?
         BEQ.S   EOHLOOP        NO...BYPASS THIS COMMAND, ELSE...
         MOVE.W  #'NO',(A6)+    "NO  "   IN MSG
         ANDI.W  #$7F7F,D3      RESET CONTROL BITS
         MOVE.W  D3,(A6)+       "NOCC"   IN MSG (WHERE CC=COMMAND CODE)
         MOVE.W  #'  ',(A6)+    "NOCC  " IN MSG    "    "    "      "
         BSR.S   HELP81         PRINT THE LINE IF FULL
EOHLOOP  BRA     HELP4          NEXT COMMAND.

*        DISPLAY LINE OF COMMANDS (IF FULL)

HELP81   SUBQ.B  #1,D2          D2 = COUNT OF COMMANDS PER LINE
         BNE.S   HELP85         NOT FULL, JUST RETURN FOR MORE
         BSR     OUT1CR         YES, THEN WRITE IT
         BSR     FIXBUF         SET-UP LINE FOR NEXT COMMANDS
         MOVE.B  #8,D2          D2 = MAX NUMBER CAN BE PLACED IN LINE
HELP85   RTS

HELP6    BSR     OUT1CR         PRINT ANY REMAINING PORTION
*        BRA     HELP1          SEE IF COMPLETE
         BRA     MACSBUG        HELP IS COMPLETE SO RETURN

MSG002   DC.B    '.PC .SR .US .SS',CR,LF



         DC.B    '.D0 .D1 .D2 .D3 .D4 .D5 .D6 .D7',CR,LF






         DC.B    '.A0 .A1 .A2 .A3 .A4 .A5 .A6 .A7',CR,LF






         DC.B    '.R0 .R1 .R2 .R3 .R4 .R5 .R6',CR,LF,EOT






         DC.B    0              PAD BYTE



*-------------------------------------------------------------------------
* File HEX2DEC   HEX2DEC convert hex to decimal                   11/02/81


*    CONVERT BINARY TO DECIMAL  REG D0 PUT IN (A6) BUFFER AS ASCII

HEX2DEC  MOVEM.L D1-D4/D6-D7,-(A7)   SAVE REGISTERS
         MOVE.L  D0,D7          SAVE IT HERE
         BPL.S   HX2DC
         NEG.L   D7             CHANGE TO POSITIVE
         BMI.S   HX2DC57        SPECIAL CASE (-0)
         MOVE.B  #'-',(A6)+     PUT IN NEG SIGN
HX2DC    CLR.W   D4             FOR ZERO SURPRESS
         MOVEQ   #10,D6         COUNTER
HX2DC0   MOVEQ   #1,D2          VALUE TO SUB
         MOVE.L  D6,D1          COUNTER
         SUBQ.L  #1,D1          ADJUST - FORM POWER OF TEN
         BEQ.S   HX2DC2         IF POWER IS ZERO
HX2DC1   MOVE.W  D2,D3          D3=LOWER WORD
         MULU    #10,D3
         SWAP    D2             D2=UPPER WORD
         MULU    #10,D2
         SWAP    D3             ADD UPPER TO UPPER
         ADD.W   D3,D2
         SWAP    D2             PUT UPPER IN UPPER
         SWAP    D3             PUT LOWER IN LOWER
         MOVE.W  D3,D2          D2=UPPER & LOWER
         SUBQ.L  #1,D1
         BNE     HX2DC1
HX2DC2   CLR.L   D0             HOLDS SUB AMT
HX2DC22  CMP.L   D2,D7
         BLT.S   HX2DC3         IF NO MORE SUB POSSIBLE
         ADDQ.L  #1,D0          BUMP SUBS
         SUB.L   D2,D7          COUNT DOWN BY POWERS OF TEN
         BRA.S   HX2DC22        DO MORE
HX2DC3   TST.B   D0             ANY VALUE?
         BNE.S   HX2DC4
         TST.W   D4             ZERO SURPRESS
         BEQ.S   HX2DC5
HX2DC4   ADDI.B  #$30,D0        BINARY TO ASCII
         MOVE.B  D0,(A6)+       PUT IN BUFFER
         MOVE.B  D0,D4          MARK AS NON ZERO SURPRESS
HX2DC5   SUBQ.L  #1,D6          NEXT POWER
         BNE     HX2DC0
         TST.W   D4             SEE IF ANYTHING PRINTED
         BNE.S   HX2DC6
HX2DC57  MOVE.B  #'0',(A6)+     PRINT AT LEST A ZERO
HX2DC6   MOVEM.L (A7)+,D1-D4/D6-D7   RESTORE REGISTERS
         RTS                    END OF ROUTINE




*-------------------------------------------------------------------------
* File LOAD      LO & VE (Load & Verify) Commands.                02/22/82

* THIS FUNCTION
*   1.) READS A "S-RECORD"
*   2.) FORMATS THE DATA ON THE STACK
*   3.) CALCULATES THE CHECKSUM
*   4.) THEN STORES (VERIFIES) THE DATA TO MEMORY
*
* WHEN VERIFYING RECORDS MAKE BE SKIPPED WHILE DISPLAYING THE MISS-MATCHED
*  RECORDS.  DISPLAY FORMAT
*   S1CCAAAA.-.-.-33.-
*     CC                     BYTE COUNT
*       AAAA                 ADDRESS
*           .-.-.-  .-       DATA FIELDS THAT MATCHED
*                 33         DATA MISS MATCH (DISPLAY DATA FROM S-RECORD)

*   ***LOAD*** AND ***VERIFY***  'S' RECORDS
*
*        D4 = ERROR FLAG
*
*        D5 = V000I0CC
*             0.......  = LOAD
*             8.......  = VERIFY
*             ....0...  = CALCULATE CHECKSUM
*             ....8...  = IGNORE CHECKSUM
*             ......CC  = CHECKSUM

VECMD    MOVEQ   #1,D5          MARK THE MODE
         ROR.L   #1,D5          D5 = $80000000
         BRA.S   CHKCHKS        GO CHECK CHECKSUM OPTION

LOCMD    CLR.L   D5             READ MODE
CHKCHKS  CLR.L   D4             RESET ERROR FLAG
         BSR     SCANPORT       SET UP OUTPUT P1,P2,P3 ETC

* SEE IF CHECKSUM -C OPTION AND =SEND THIS OPTION

READ01   CMP.L   A6,A5          SEE IF AT END OF BUFFER
         BCC.S   READ09
         MOVE.B  (A5)+,D0       GET A CHARACTER
READ03   CMPI.B  #'=',D0        SEE IF EQUAL SIGN
         BEQ.S   READ08

         CMPI.B  #'X',D0        SEE IF ECHO
         BNE.S   READ021
         MOVE.B  #-1,D5         D5.B = ECHO TO PORT ONE
         BRA     READ01

READ021  CMPI.B  #'-',D0        SEE IF MINUS SIGN
         BNE.S   READ01
         CMP.L   A6,A5          SEE IF AT END OF BUFFER
         BEQ.S   READ09
         MOVE.B  (A5)+,D0       GRAB SECOND CHARACTER
         CMPI.B  #'C',D0        SEE IF LETTER C AS IN -C
         BNE     READ03
         ORI.W   #$8000,D5      MARK AS IGNORE CHECKSUM
         BRA     READ01

READS1   CLR.L   D6             D6 = TYPE "S1"
         SUBQ.L  #4,D3          BYTE COUNT

         CLR.L   D0
         BSR     READHEX4       FORM ADDRESS
         BRA.S   READS202

READ08   BSR     OUTPUT2        SEND REST OF LINE(+CR) TO PORT

READ09   MOVE.B  D5,ECHOPT1     MOVE ECHO FLAG
         MOVE.L  OUTPORT1,OUTTO SEND OUTPUT TO CONSOLE


READ0    LEA     SYSTACK,A7     FORCE STACK (FOR ERROR RECOVERY)

         LINK    A4,#-((BUFFSIZE/2)+4)  CREATE BUFFER ON STACK

         CLR.B   D5             ZERO CHECKSUM

         BSR     FIXBUF         START OF INPUT BUFFER
         BSR     PORTIN2        GET A RECORD FROM PORT

         MOVE.L  A5,A3 SAVE     START ADDRESS OF BUFFER
READ00   MOVE.B  (A3)+,D0       GET FIRST CHARACTER
         CMP.L   A3,A6
         BCS     READ0          END OF BUFFER WITHOUT "S"

READ005  CMPI.B  #'S',D0        SEE IF IT IS AN S
         BNE     READ00         GET ANOTHER CHARACTER
         BSR     GETCHR         GET RECORD TYPE
         MOVE.L  D0,D6

         BSR     READHEX        GET CHAR COUNT
         CLR.L   D3
         MOVE.B  D0,D3

         CMPI.B  #'0',D6        'S0'???
         BEQ     READ0          JUST IGNORE
         CMPI.B  #'1',D6
         BEQ.S   READS1         S1 RECORD TYPE (2 BYTE ADDRESS)
         CMPI.B  #'8',D6
         BEQ     READS8         S8 RECORD TYPE
         CMPI.B  #'9',D6
         BEQ     READS9         S9 RECORD TYPE
         CMPI.B  #'2',D6
         BNE.S   READ005        KEEP LOOKING FOR "Sn"

READS2   MOVEQ   #2,D6          D6 = TYPE = S2 (3 BYTE ADDRESS)
         BSR     READHEX6
         SUBQ.L  #5,D3          BYTE COUNT
READS202 MOVE.L  D3,CC(A4)

         MOVE.L  D0,ADDRESS(A4) ADDRESS + OFFSET
         LEA     LDATA(A4),A2   A2 = STORE TO STACK POINTER

READ100  BSR.S   READHEX        GET DATA BYTE
         MOVE.B  D0,(A2)+       MOVE DATA TO STACK
         DBRA    D3,READ100

         TST.W   D5
         BMI.S   READ120        IGNORE CHECKSUM

         MOVE.B  D5,D7
         BSR.S   READHEX        GET CHECKSUM FROM DATA
         NOT.B   D7             CALCULATED CHECKSUM
         CMP.B   D7,D0
         BNE.S   READCKSM       ERROR
READ120


* STORE DATA (VERIFY) TO MEMORY

         MOVE.L  CC(A4),D3      BYTE COUNT
         MOVE.L  ADDRESS(A4),A3 MEMORY STORE ADDRESS
         LEA     LDATA(A4),A2   DATA ADDRESS ON STACK

         TST.L   D5
         BMI.S   READ400        VERIFY

READ130  MOVE.B  (A2),(A3)      STORE DATA
         CMP.B   (A2)+,(A3)+    VERIFY DATA STORED
         BNE     SETME          DATA DID NOT STORE
         DBRA    D3,READ130
READ135  BRA     READ0


***     VERIFY

READ400  LEA     8(A5),A1       A1 = PTR TO INPUT STRING
         ADD.L   D6,A1

         CLR.L   D7             D7 = MISS-MATCH FLAG

READ410  CMP.B   (A2)+,(A3)+    VERIFY DATA
         BNE.S   READ440        MISS-MATCH
         MOVE.B  #'.',(A1)+     OVERLAY INPUT STRING IF OK
         MOVE.B  #'-',(A1)+
READ420  DBRA    D3,READ410

         TST.L   D7
         BEQ     READ135        RECORD OK

         MOVE.L  A1,A6          DONOT DISPLAY CHECKSUM
READ430  BSR     OUT1CR         DISPLAY IT
         BRA     READ135        READ NEXT RECORD

READ440  MOVEQ   #-1,D7         D7 = Set miss-match flag
         MOVEQ   #-1,D4         D4 = Set Summary error flag
         ADDQ.L  #2,A1
         BRA     READ420

READCKSM MOVEQ   #-1,D4         D4 = Set summary error flag
         LEA     MSGLOAD2(PC),A5
         BSR     FIXDADD
         MOVE.L  D7,D0
         BSR     PNT2HX         CALCULATED CHECKSUM
         BRA     READ430

READHEX  BSR.S   GETHEXC        FORM BYTE
         ASL.B   #4,D0
         MOVE.B  D0,D1
         BSR.S   GETHEXC
         OR.B    D1,D0          D0 = BYTE FORMED
         ADD.B   D0,D5          UPDATE CHECKSUM
         RTS

GETCHR   MOVE.B  (A3)+,D0
         CMP.L   A3,A6
         BCS     READCKSM       OVERFLOW
         RTS

GETHEXC  BSR     GETCHR
         SUBI.B  #$30,D0        SEE IF LESS THAN ZERO
         BLT.S   RHEX3
         CMPI.B  #$09,D0        SEE IF GT 9
         BLE.S   RHEX2
         SUBQ.B  #7,D0          NORMALIZE $A TO 10
         CMPI.B  #$10,D0        SEE IF TOO LARGE
         BCC.S   RHEX3
RHEX2    RTS

RHEX3    LEA     MSGLOAD1(PC),A5 'NOT HEX=X?'  MESSAGE
         BSR     FIXDADD
         MOVE.B  -(A3),(A6)+    BAD CHARACTER
         BRA     READ430        GO TRY NEXT RECORD

MSGLOAD1 DC.B    'NOT HEX=',EOT


MSGLOAD2 DC.B    ' CHKSUM=',EOT


READHEX6 CLR.L   D0             FORM ADDRESS (3 BYTE)
         BSR     READHEX
         ASL.L   #8,D0
READHEX4 BSR     READHEX        FORM ADDRESS (2 BYTE)
         ASL.L   #8,D0
         BSR     READHEX
         ADD.L   OFFSET,D0
         RTS

READS8   BSR     READHEX6
READS800 MOVE.L  D0,REGPC       SAVE IT IN THE USER PREG

         TST.L   D4
         BNE     ERROR          DISPLAY "ERROR"
         BRA     MACSBUG        END OF ROUTINE

READS9   CLR.L   D0
         BSR     READHEX4       GET ADDRESS
         BRA     READS800


*-------------------------------------------------------------------------
* File MDDI      MD[S] (Memory Display) Command                   06/16/82

*   ***MD***   MEMORY DISPLAY         ENTRY POINT
*     FORMAT:  MD[S] <ADDRESS> [<COUNT>] [;DI]
* 1.  IF 'S' USED IN COMMAND THEN IT WILL DUMP 16 LINES, (1 Screen), AND
*     PROMPT-ENTER CR FOR 16 MORE LINES ETC OR ANY MACSBUG COMMAND.
*

MDCMD    DS      0
         BSR     SCANPORT       WHERE TO SEND OUTPUT
         MOVE.L  INPORT1.L,INFROM ONLY ALLOW INPUT FROM PORT1

         MOVEQ   #-1,D6         D6 = HOW MANY LINES PER PAGE

         SUB.L   A3,A3          A4 = DEFAULT ZERO  START
         MOVE.L  A3,A4          A3 = END ADDR

         CLR.L   D7             D7 = DO NOT DISASSEMBLE
         MOVE.L  A5,A2
PRINT8   CMP.L   A2,A6          LOOK FOR OPTIONS
         BCS.S   PRINTDI        NO  OPTIONS
         CMPI.B  #';',(A2)+
         BNE     PRINT8

         MOVE.L  A2,A6
         SUBQ.L  #1,A6          A6 = POINTER TO ;

         CMPI.B  #'D',(A2)+
PRINTMB  BNE     SYNTAX         COMMAND SYNTAX ERROR
         CMPI.B  #'I',(A2)+
         BNE     PRINTMB
         MOVEQ   #-1,D7         DISASSEMBLE OPTION
PRINTDI


* LOOK FOR "S" IN COMMAND
         MOVE.B  (A5),D0
         CMPI.B  #'S',D0
         BNE.S   PRINT5         NO "S" IN COMMAND
         ADDQ.L  #1,A5          MOVE PAST "S"

         MOVEQ   #16,D6         DO 16 LINES AT A TIME
         SUB.L   A3,A3
         SUBQ.L  #1,A3          MAX END ADDRESS

PRINT5   LEA     PRINT7(PC),A0  WHERE TO GO IF NO PARAMETERS
         BSR     FNEXTF         FIND NEXT FIELD
         BSR     GETA
         MOVE.L  D0,A4          A4 = GET ADDRESS

         BSR     FNEXTF
         BSR     GETEXP         D0 = GET COUNT
         ADD.L   A4,D0          END=START+COUNT-1
         SUBQ.L  #1,D0          BACK OFF ONE
         MOVE.L  D0,A3          A3 = END ADDRESS

PRINT7   TST.L   D7
         BEQ.S   PUTADR         NOT DISASSEMBLE

PRINTDI5 BSR     FIXBUF         ;DI OPTION
         MOVEM.L A3/D6-D7,-(A7)
         MOVEM.L (A4),D0-D2     D0-D2 = DATA TO DISASSEMBLE
         BSR     DCODE68K       DISASSEMBLE
         BSR     OUT1CR
         MOVEM.L (A7)+,A3/D6-D7

         SUBQ.L  #1,D6
         BEQ.S   PRINT9         'MDS' COMMAND

         CMP.L   A4,A3          END CHECK
         BCC     PRINTDI5
         BRA.S   PRINT9

PRINT3   MOVEQ   #16,D6         D6 = LINE BLOCK COUNT
         SUB.L   A3,A3
         SUBQ.L  #1,A3          A3 = MAX END ADDRESS
         BRA     PRINT7

* START A NEW  LINE
*
PUTADR   BSR     FIXBUF         SET UP OUTPUT BUFFER
         MOVE.L  A4,D0          CURRENT LINE ADDRESS
         BSR     FRELADDR       FORM RELATIVE ADDRESS
         MOVE.B  #$20,(A6)+     FORMAT  SPACE
         MOVE.L  A4,A0          A0 IS SCANNING ADDRESS
         MOVEQ   #$10,D3        SET UP COUNTER FOR LOOP

NXTBP    MOVE.B  (A0)+,D0       GET BYTE TO PRINT
         BSR     PNT2HX         PRINT IT
         MOVE.B  #$20,(A6)+     SPACE BETWEEN EACH HEX

         CMPI.B  #9,D3          HALF LINE SPACING
         BNE.S   NXTBP3
         MOVE.B  #$20,(A6)+
NXTBP3

         SUBQ.L  #1,D3
         BNE     NXTBP          LOOP TILL D3 IS ZERO

         MOVE.B  #$20,(A6)+     MOVE A SPACE
         MOVE.L  A4,A0          RELOAD SCANNER FOR ASCII PRINTS
         MOVEQ   #$10,D3        RELOAD COUNTER

NXTCHR   MOVE.B  (A0)+,D0       FETCH BYTE
         ANDI.B  #$7F,D0        REMOVE HIGH ORDER BIT, (ASCII ONLY USES 7 BITS)
         CMPI.B  #$20,D0        SEE IF IT IS CONTROL CHAR
         BLT.S   NOTCHR         BYPASS IF IT IS... ELSE
         CMPI.B  #$7F,D0        IS IT A "7F"?    (CAUSES PRINTER PROBLEM)
         BLT.S   PUTCHR         NO... THEN PRINT IT, ELSE SUBSTITUTE "."
NOTCHR   MOVE.B  #$2E,D0        CHANGE UNPRINTABLE TO PERIOD

PUTCHR   MOVE.B  D0,(A6)+       MOVE "EDITTED" CHARACTER TO PRINT LINE
         SUBQ.L  #1,D3          LOOP AROUND FOR NEXT CHAR
         BNE     NXTCHR         ANY LEFT?
         BSR     OUT1CR         NO... THEN PRINT THE COMPLETE LINE
         ADDQ.L  #$08,A4        UPDATE STARTING ADDRESS OF NEXT ADDRESS
         ADDQ.L  #$08,A4        ........
         CMP.L   A4,A3          DOES NEW LINE START PAST END
         BCS.S   PRINT9         SEE IF STILL GOING
         SUBQ.L  #1,D6          DECR THE COUNTER
         BNE     PUTADR         DO ANOTHER LINE

PRINT9   LEA     MSG001(PC),A5  SET UP FOR PROMPT
         BSR     FIXDATA
         MOVE.B  #'>',(A6)+     PROMPT SAME AS MACSBUG
         MOVE.B  #BLANK,(A6)+
         BSR     OUTPUT         PRINT IT

         BSR     FIXBUF         RESET BUFFER
         BSR     PORTIN1        TAKE IN INPUT
         CMP.L   A6,A5          SEE IF ANYTHING ENTERED
         BEQ     PRINT3         NOTHING ENTERED; DO 16 MORE LINES
         CLR.L   OUTTO          *
         BRA     DECODE6        GO MAKE SURE 2ND DIGIT IS BLANK




*-------------------------------------------------------------------------
* File MMDI      Modify Memory command WITH asm/disasm            11/27/81

* MODIFY MEMORY
*  COMMON REGISTER USAGE
*   A6  IO BUFFER POINTER  END
*   A5  IO BUFFER POINTER  START
*   A4  ADDRESS TO MODIFY
*   A3
*   A2
*   A1
*   A0
*   D7  DATA READ (DATA STORED)
*   D6  SIZE  1/2/4 BYTES  (ASM/DISASM 2 - 10 BYTES)
*   D5  OVERRIDE BYTE (80XX=NON VERIFY)  (XX80=BYTE SIZE)
*
* ;OPTIONS
*   ;W  WORD
*   ;L  LONG WORD (4 BYTES)
*   ;DI DISASSEMBLE
*     ;O  ODD ADDRESSES ONLY
*     ;V  EVEN ADDRESSES ONLY
*       ;N  NON-VERIFY
*

MMDI     BSR     CKWADR
         BSR     CKADDR
         CLR.L   D6             SIZE = 0
MMDI22   ADD.L   D6,A4          PC = PC + SIZE
MMDI23   BSR     FIXBUF         A5 & A6 = POINTER TO BUFFER

*                  ENTRY
*                   A4 = PROGRAM COUNTER
*                   A5 = POINTER TO STORE DISASSEMBLED LINE
         MOVEM.L   (A4),D0-D2          DATA TO DISASSEMBLE
         BSR       DCODE68K
*                  RETURN
*                   A4 = NEW PROGRAM COUNTER
*                   A5 = PTR START BUFFER
*                   A6 = PRT END BUFFER
*                   D6 = NUMBER OF BYTES DISASSEMBLED

         MOVE.B  #'?',(A6)+
         BSR     OUTPUT

MMDI31   BSR     FIXBUF
         BSR     PORTIN1N       INPUT ASSEMBLY SOURCE (NO LINE FEED)
         CMP.L   A5,A6
         BNE.S   MMDI34
         BSR     OUT1CR         NOTHING INPUT; OUTPUT LINE FEED
         BRA     MMDI23

MMDI34   SUB.L   D6,A4          BACKUP PC

         CMPI.B  #'.',(A5)
         BEQ     MM905          CLOSE

         LEA     SYSTACK+17,A3  STORE BUFFER

*                  A3 = STORE POINTER
*                  A4 = PROGRAM COUNTER
*                  A5 = POINTER TO DATA TO ASSEMBLE
*                  A6 = POINTER TO END OF SOURCE DATA

         BSR     CODE68K        ASSEMBLE

*                  A3 = POINTER TO LINE ASSEMBLED
*                  A4 = PROGRAM COUNTER
*                  A6 = POINTER END OF LINE ASSEMBLED
*                  D0-D2 = DATA ASSEMBLED
*                  D6 = NUMBER OF BYTES ASSEMBLED
*                  D7 = ERROR FLAG & POSITION OF ERROR

         MOVE.L  A3,A5
         ADD.L   #78,A3         A3 = MAX LINE
MMDI26   CMP.L   A6,A3
         BCS.S   MMDI27
         MOVE.B  #BLANK,(A6)+   SPACE FILL LINE
         BRA     MMDI26
MMDI27   BSR     OUT1CR         PRINT LINE JUST ENTERED

         TST.B   D7
         BNE.S   MMDI30         ERROR; DON'T STORE DATA

         LEA     SYSTACK+4,A2   A2 = TEMP AREA
         MOVEM.L D0/D1/D2,-(A2) STORE DATA
         MOVE.L  D6,D1          D1 = NUMBER OF BYTES TO STORE
         SUBQ.L  #1,D1
         MOVE.L  A4,A1          A1 = DATA STORE POINTER
MMDI29   MOVE.B  (A2)+,D0
         MOVE.B  D0,(A1)
         MOVE.B  (A1)+,D2       INSURE DATA STORED
         CMP.B   D0,D2
         BNE     MM90
         DBRA    D1,MMDI29
         BRA     MMDI22

MMDI30   BSR     FIXBUF
MMDI44   MOVE.B  #BLANK,(A6)+   SPACES
         DBRA    D7,MMDI44

         MOVE.B  #'X',-1(A6)    X UNDER ERROR
         MOVE.B  #'?',(A6)+     ? ALLOW REINPUT
         BSR     OUTPUT
         BRA     MMDI31


MCMD     DS      0              "M" Alias for "MM" Command
MMCMD    DS      0              "MM" Command -Memory Modify-
         LEA     SYNTAX(PC),A0  A0=ERROR RETURN
         BSR     FNEXTF
         BSR     GETA
         MOVE.L  D0,A4          A4= ADDRESS OF DATA
         MOVEQ   #1,D6          SIZE = BYTE
         CLR.L   D5             NO OVERRIDE

MM05     CMP.L   A5,A6
         BCS.S   MM10           AT END OF BUFFER

* LOOK FOR ;OPTIONS
         MOVE.B  (A5)+,D0
         CMPI.B  #';',D0
         BNE     MM05           IGNORE NOT ;

         MOVE.B  (A5)+,D0       GET NEXT CHAR
         CMPI.B  #'D',D0
         BNE.S   MM045

         CMPI.B  #'I',(A5)+     DISSAMBLY OPTION
         BNE     MM05
         BRA     MMDI

MM045    CMPI.B  #'W',D0
         BEQ.S   MM065          ;W   D6=2

         CMPI.B  #'L',D0
         BNE.S   MM054
         MOVE.B  #4,D6          ;L   D6=4
         CLR.B   D5             RESET BYTE OVERRIDE
         BRA     MM05

MM054    CMPI.B  #'N',D0
         BNE.S   MM056
         ORI.W   #$8000,D5      ;N  D5=$8000
         BRA     MM05

MM056    CMPI.B  #'O',D0
         BNE.S   MM058
         MOVE.L  A4,D0          ;O
         ORI.B   #1,D0          FORCE ODD ADDRESS
         BRA.S   MM060

MM058    CMPI.B  #'V',D0
         BNE     SYNTAX         ERROR
         MOVE.L  A4,D0          ;V
         ANDI.B  #$FE,D0        FORCE EVEN ADDRESS
MM060    MOVE.L  D0,A4
         ORI.B   #$80,D5        BYTE OVERRIDE
MM064    MOVE.B  #2,D6          SIZE = WORD (2 BYTES)
         BRA     MM05

MM065    CLR.B   D5             RESET BYTE OVERRIDE
         BRA     MM064

* FORMAT ADDRESS FOR PRINTING
MM10     MOVE.L  A4,D0
         CMPI.B  #1,D6
         BEQ.S   MM11           "BYTE"
         TST.B   D5
         BMI.S   MM11           BYTE OVERRIDE
         BSR     CKWADR         CHK ALLIGNMENT
MM11     BSR     CKADDR         *
         BSR     FIXBUF
         BSR     FRELADDR       FORM RELATIVE ADDRESS
         MOVE.B  #BLANK,(A6)+   SPACE

         TST.W   D5
         BMI.S   MM18           NON-VERIFY (DON'T READ MEMORY)

* READ DATA FROM MEMORY & FORMAT IT
         TST.B   D5
         BMI.S   MM12           BYTE OVERRIDE

         CMPI.B  #2,D6
         BEQ.S   MM14           WORD
         CMPI.B  #4,D6
         BEQ.S   MM16           LONG WORD

* BYTE
MM12
         MOVE.B  (A4),D7        D7 = DATA READ
         MOVE.L  D7,D0
         BSR     PNT2HX         FORMAT BYTE
         BRA.S   MM18

* WORD
MM14
         MOVE.W  (A4),D7
         MOVE.L  D7,D0
         BSR     PNT4HX         FORMAT WORD
         BRA.S   MM18

* LONG WORD
MM16
         MOVE.L  (A4),D7
         MOVE.L  D7,D0
         BSR     PNT8HX         FORMAT LONG WORD

MM18     MOVE.B  #BLANK,(A6)+   SPACE
         MOVE.B  #'?',(A6)+
         BSR     OUTPUT

* READ USER INPUT
*  [DATA] (CR)   NEXT
*           ^    LAST
*           =    SAME
*           .    EXIT

         BSR     FIXBUF
         BSR     PORTIN1
         CMP.L   A5,A6
         BEQ     MM50           NO DATA (CR ONLY)

         LEA     MM40(PC),A0    A0 = NO PARAMETER RETURN
         BSR     FNEXTF         FIND NEXT FIELD

* IF = ^ OR .  TAKE ACTION
         MOVE.B  (A5),D0
         CMPI.B  #'=',D0
         BEQ     MM10
         CMPI.B  #'.',D0
         BEQ     MACSBUG
         CMPI.B  #'^',D0
         BEQ.S   MM60

         BSR     GETEXP         GET DATA
         MOVE.L  D0,D7          D7=DATA STORED

* WE HAVE DATA; STORE IT
         TST.B   D5
         BMI.S   MM22           BYTE OVERRIDE

         CMPI.B  #2,D6
         BEQ.S   MM24           WORD
         CMPI.B  #4,D6
         BEQ.S   MM26           LONG WORD

* BYTE
MM22
         MOVE.B  D0,(A4)        STORE DATA
         TST.W   D5
         BMI.S   MM40           NO-VERIFY
         MOVE.B  (A4),D0
         CMP.B   D7,D0
         BNE.S   MM90           NO MATCH
         BRA.S   MM40

* WORD
MM24
         MOVE.W  D0,(A4)        STORE
         TST.W   D5
         BMI.S   MM40           DO NOT VERIFY
         MOVE.W  (A4),D0
         CMP.W   D7,D0
         BNE.S   MM90           NO MATCH
         BRA.S   MM40

* LONG WORD
MM26
         MOVE.L  D0,(A4)
         TST.W   D5
         BMI.S   MM40           DO NOT VERIFY
         MOVE.L  (A4),D0
         CMP.L   D7,D0
         BNE.S   MM90           NO MATCH

* LOOK FOR  . = ^
MM40     MOVE.B  (A5),D0
         CMPI.B  #'.',D0
         BEQ     MACSBUG        DONE
         CMPI.B  #'^',D0
         BEQ.S   MM60           BACKUP ADDRESS
         CMPI.B  #'=',D0
         BEQ     MM10           ADDRESS STAYS THE SAME
         CMPI.B  #BLANK,D0
         BEQ.S   MM50
         CMP.L   A5,A6
         BNE     SYNTAX         ERROR

* ADDRESS LOW TO HIGH
MM50     ADD.L   D6,A4
         BRA     MM10

* ADDRESS HIGH TO LOW
MM60     SUB.L   D6,A4
         BRA     MM10

MM90     LEA     MSG017(PC),A5  'DATA DID NOT STORE'
MM95     BSR     FIXDCRLF
         BRA     MSG

MM905    LEA     MSGEOT(PC),A5
         BRA     MM95




*-------------------------------------------------------------------------
* File MS        Memory set command                               11/02/81

*    ***MS***   MEMORY SET
*     FORMAT: MS  ADDRESS HEX HEX,HEX,'ASCII'  ETC.
*     COMMAS OR SPACES BETWEEN FIELDS
*     FIELDS ARE SIZE ADJUSTED (STORES UP TO 4 BYTES)
*     ASCII ENCLOSED IN SINGLE QUOTES-ANY LENGTH

MSCMD    LEA     SYNTAX(PC),A0  IF NO PARAMETERS
         BSR     FNEXTF         FIND NEXT FIELD
         BSR     GETA           GET ADDRESS
         BSR     CKADDR         CHECK VALID ADDRESS

         MOVE.L  D0,A1          A1=START (OPEN) ADDRESS
SETM1    LEA     MACSBUG(PC),A0 IF NO PARAMTER
         BSR     FNEXTF         FIND NEXT FIELD
         MOVE.L  A5,A4          SAVE ADDRESS OF PARAMTER
         MOVE.B  (A5),D0        CHECK OUT NEXT CHARACTER
         CMPI.B  #$27,D0        SEE IF IT IS QUOTE MARK
         BEQ.S   SETM5          SPECIAL ROUTINE
         CMPI.B  #'N',D0        SEE IF NEXT LINE FEATURE
         BEQ.S   SETM7
         BSR     GETNUMA        GET THE DATA
         MOVE.L  A1,A3          ADDRESS
         MOVE.L  A5,D1          COMPUTE BYTES OF DATA
         SUB.L   A4,D1          LEN=END-START
         ASR.L   #1,D1          BYTES=CHAR/2
         BCC.S   SETM3          TAKE CARE OF ODD CHARACTER
         ADDQ.L  #1,D1          WHOLE NUMBER OF BYTES
SETM3    MOVE.L  D1,D2          D1 SCANS DOWN
         SUBQ.L  #1,D2          KNOCK IT DOWN TO INDEX
         MOVE.B  D0,0(A3,D2)    INDEXED BECAUSE BACKWARD

         MOVE.B  0(A3,D2),D3    REREAD TO CHECK IF STORED OK

         CMP.B   D0,D3          ARE SAME?
         BNE.S   SETME          'DATA DID NOT STORE'

         ASR.L   #8,D0          SHIFT ONE BYTE
         ADDQ.L  #1,A1          BUMP ADDRESS
         SUBQ.L  #1,D1
         BNE     SETM3
         BRA.S   SETM1          GO DO NEXT DATA

*  DATA IN IN ASCII STRING
SETM5    ADDQ.L  #1,A5          GET PAST QUOTE MARK
SETM6    CMP.L   A6,A5          SEE IF END OF BUFFER
         BGE     MACSBUG
         MOVE.B  (A5)+,D0       GRAB CHARACTER
         CMPI.B  #$27,D0        SEE IF QUOTE MARK
         BEQ.S   SETM1          IF SO-END OF STRING
         MOVE.B  D0,(A1)        SAVE DATA

         MOVE.B  (A1)+,D1       REREAD FOR CHECK

         CMP.B   D1,D0          SEE IF SAME
         BEQ     SETM6
SETME    LEA     MSG017(PC),A5  'DATA DID NOT STORE'
         BSR     FIXDCRLF
         BRA     MSG

SETM7    BSR     FIXBUF         DISPLAY CURRENT ADDRESS
         MOVE.L  A1,D0
         BSR     PNT8HX         PUT ADDRESS IN BUFFER
         MOVE.L  #'  ? ',(A6)+  PROMPT
         BSR     OUTPUT         DUMP BUFFER WITH NO LF CR
         BSR     FIXBUF         GET READY FOR INPUT
         MOVE.B  #BLANK,(A5)+   ADVANCE IN BUFFER
         MOVE.L  A5,A6          BECAUSE OF SNAFU IN FINDNP
         BSR     PORTIN1        INPUT FROM CONSOLE
         MOVE.B  -(A5),D0       JUST BACK UP IN BUFFER
         CMP.L   A6,A5
         BEQ     MACSBUG
         BRA     SETM1          DO DECODE IT

MSG017   DC.B    'DATA DID NOT STORE',CR,LF,EOT





         DC.B    0              PAD BYTE




*-------------------------------------------------------------------------
* File MTSETUP   MTSETUP memory test setup                        11/02/81

*
* SET UP PARMS FOR BLOCK TEST AND BLOCK INITIALIZE
*

MTSETUP  DS      0
         MOVE.L  A7,TEMP        STACK FOR EXCEPTION RETURN
         LEA     SYNTAX(PC),A0  WHERE TO GO IF NO PARAMETERS
         BSR     FNEXTF         FIND NEXT FIELD
         BSR     GETA           GET ADDR1
         BSR     CKWADR         CHECK WORD BOUNDRY ADDRESS
         MOVE.L  D0,A3          SAVE STARTING ADDRESS

         LEA     SYNTAX(PC),A0  SET UP TO TRY "TO" ADDRESS
         BSR     FNEXTF         *
         BSR     GETA           GET ADDR2
         BSR     CKWADR
         MOVE.L  D0,A1          A1 = END ADDRESS?
         MOVE.L  A3,A0          A0 = STARTING ADDRESS
         BSR     P2PHY          DISPLAY TWO ADDRESSES
         CMP.L   A0,A1
         BCS     SYNTAX         END ADDR TOO SMALL
         ADDQ.L  #2,A1          ADJUST END ADDR
         RTS




*-------------------------------------------------------------------------
* File OF        OF & PERIOD Command                              12/18/81

* .*  HANDLER
*   GET TWO CHARACTERS FOLLOWING PERIOD

PERCMD   LSL.W   #8,D1
         MOVE.B  (A5),D1        D1 = 2ND,3RD CHARACTERS
         SUBQ.L  #1,A5          A5 = POINTER TO 2ND CHAR  (1ST REAL CHARACTER)

         LEA     REGTBL(PC),A0
PER4     CLR.L   D7
         MOVE.W  (A0)+,D7       SAVE FIRST WORD FOR END OF TABLE TEST
         MOVE.W  (A0)+,D0       GET REAL REGISTER ID INTO D0
         CMPI.W  #$FFFF,D7      ARE WE AT THE END OF THE TABLE?
         BEQ     WHAT           YES...THEN WE DIDNT FIND IT

         CMPI.B  #'@',D0
         BNE.S   PER3           NOT @

* THIRD CHAR MUST BE NUMERIC 0 - 7
         MOVE.B  D1,D0          ALLEGED DIGIT
         CMPI.B  #'0',D0
         BMI     PER4           NOT A DIGIT
         CMPI.B  #'8',D0
         BPL     PER4           NOT A DIGIT

PER3     CMP.W   D1,D0
         BNE     PER4           MISS-MATCH

*******************************************************************
*        AT THIS TIME WE HAVE FOUND THE ENTRY IN THE "REG TABLE"  *
*        WE NOW NEED TO EXTRACT AND USE THE OFFSET                *
*******************************************************************

         LEA     FIRST(PC),A0   A0 = Start of VERSAbug RO
         ADD.L   D7,A0          Add offset
         JMP     (A0)           Now go to the calculated location
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
